omaralabed/Radxa-CM5-PCB/fabrication/footprint-coupon-a1/output/renders/Footprint-Coupon-bottom.png

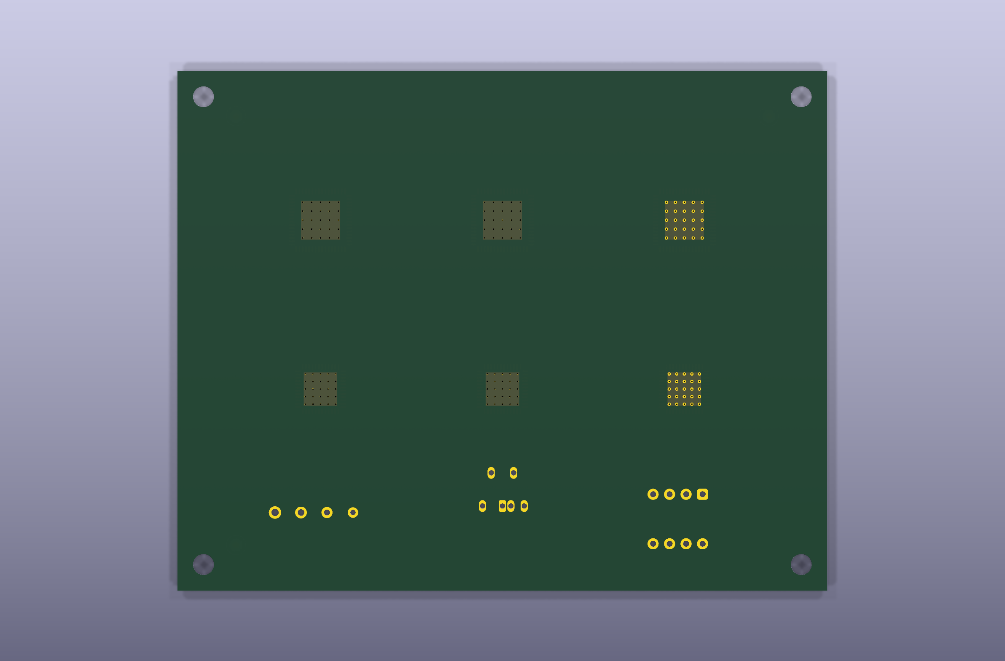
fabrication/footprint-coupon-a1/output/renders/Footprint-Coupon-bottom.png
