omaralabed/Radxa-CM5-PCB/references/radxa-cm-projects/cm5/README.md

<!-- AGENT_SPEC_START -->
Spec source: ../tools/out/cm5.md

### Agent Spec Summary
- Board: Radxa CM5 (cm5)
- SoC: RK3588S
- Category: cm
- Form factor: raspberrypi_cm4_compatible
- Interfaces total: 0
- Interface breakdown: none
- Capability tags: cm4_compatible, edge_ai
- Power inputs: unknown unknown via unknown
- Data path: hardware-db/boards/cm5
<!-- AGENT_SPEC_END -->

## Apply for Radxa CM5

Radxa is donating some free [Radxa CM5](hhttps://rock.sh/cm5) to open source hardware projects.

## How to apply

Send a new PR to this repository on GitHub, append your application table(sort Project Name). Radxa team will review/ask questions/discuss about the project detail. If the project is interesting or welcomed by the community, we will approve it. Radxa Team will contact the developer for the further sample shipping&development etc.

## CM5 projects list:

| Project Name | CM5 Model | Hardware(Carrier Board) | Software | Notes |
|---|---|---|---|---|
| Argo | Radxa CM5 Max (16GB RAM, 128GB eMMC) | Custom Raspberry Pi–focused Carrier PCB | Ubuntu/Android | For testing with custom Raspi-focused Carrier PCB |
| piBrick PocketRX5 | Radxa CM5 Max (16GB RAM, 128GB eMMC) | Handheld pocket computer | Ubuntu/Android | For designing new board supporting Radxa CM5 |
