omaralabed/Radxa-CM5-PCB/cad/kicad/FOOTPRINT_RELEASE.md

# Footprint Release Control

This project does not permit final production routing from schematic symbols
that lack a resolved, drawing-backed footprint. Engineering board outlines,
mechanical placement, component floorplanning, and routing outside a named
local coupon region may proceed from the controlled nominal geometry. Run:

```sh
python3 cad/kicad/audit_footprint_readiness.py --routing
```

The command must pass before final route freeze. The stricter `--release` gate
also requires a manufacturer and MPN for every board-mounted component.

## Locked connector evidence

| Function | Manufacturer / part | Footprint | Evidence | State |
|---|---|---|---|---|
| Wi-Fi Mini PCIe socket | Molex 0679101002 / 67910-1002 | `CM5Carrier:Molex_0679101002_Mini_PCIe` | Molex production drawing SD-67910-001 revision C2 | Land pattern locked; first-article and 3D fit open |
| Balanced output XLR, CH1-CH8 | Neutrik NC3MAV | `Connector_Audio:Jack_XLR_Neutrik_NC3MAV_Vertical` | Neutrik NC3MAV product drawing and KiCad source footprint | Pad/hole signature and Rev L face-center placement locked; overhanging outline is assembly data on `F.Fab` |
| Balanced input XLR, CH1-CH8 | Neutrik NC3FAV | `Connector_Audio:Jack_XLR_Neutrik_NC3FAV_Vertical` | Neutrik NC3FAV product drawing and KiCad source footprint | Pad/hole signature and Rev L face-center placement locked |
| Radxa CM5 board-to-board mates | 3x Hirose DF40C-100DS-0.4V(51) | Three `CM5Carrier:Radxa_CM5_*_DF40C_100DS_OFFICIAL` footprints | Pad, drill, module-mount, and relative-transform geometry extracted from Radxa IO V2.20 official PADS source; pin identity from V2.21 workbook; Hirose EDC3-311352-00 drawing | Source geometry locked. J24's child pad angle is restored to the native PADS decal angle after a documented KiCad importer double-rotation; coordinates and sizes are unchanged. Installed stack-height inspection remains open |
| Ethernet MagJacks | Wurth 74991114412 | `CM5Carrier:T_Wurth_WE-RJ45LAN_74991114412` | Wurth manufacturer footprint and STEP | Pad/hole signature and Rev L opening-center placement locked; immutable 0.2312 mm NPTH-to-copper minimum requires the documented PCBWay process rule |
| Cellular M.2 B-key socket | TE 2199230-3 | `CM5Carrier:TE_2199230-3_M2_Key_B_4.2mm` | TE customer drawing C-2199230 revision B4 | Locked; modem/heatsink envelope open |
| Dual nano-SIM holders | Wurth 693043020611 | `CM5Carrier:J_Wurth_WR-CRD_693043020611` | Wurth manufacturer drawing | Pad/hole signature and Rev L service-center placement locked |
| Program-audio TDM headers | Molex 87832-6423, two devices | `Connector_Molex_Milligrid:Molex_8783230xx_2x15_P2.0mm_Header_Vertical_Polarized_MountingPegs` | Molex 87832 production drawing; 30 circuits, pegs, polarization and 30 microinch gold | Locked; harness SI and vibration qualification open |
| CTIA headset jack | Kycon STX-353K7A-6N-KTTR | `CM5Carrier:Kycon_STX-353K7A-6N-KTTR_PRELIMINARY` | Kycon component drawing defines terminal centers but no recommended PCB land | Coupon A1 artwork ready; production blocked pending physical sample and plated-hole result |

## Program-audio package evidence

| Function | Manufacturer / part | Footprint | Evidence | State |
|---|---|---|---|---|
| Eight-channel ADC | AKM `AK5558VN` | `Package_DFN_QFN:QFN-64-1EP_9x9mm_P0.5mm_EP6x6mm_ThermalVias` | AKM package drawing and KiCad exposed-pad starting land | Coupon A1 artwork ready; routing blocked pending physical X-ray and assembly pass |
| Eight-channel DAC | AKM `AK4458VN` | `Package_DFN_QFN:QFN-48-1EP_7x7mm_P0.5mm_EP5.15x5.15mm_ThermalVias` | AKM package drawing and KiCad exposed-pad starting land | Coupon A1 artwork ready; routing blocked pending physical X-ray and assembly pass |
| Output fail-silent relays, K501-K508 | Panasonic Industry `TQ2-12V` | `CM5Carrier:Panasonic_TQ2-12V_PRELIMINARY` | Panasonic TQ relay package drawing | Coupon A1 artwork ready; routing blocked pending insertion, seating, and pin-map pass |
| Balanced input receivers | THAT Corporation `THAT1206S08-U` | `Package_SO:SOIC-8_3.9x4.9mm_P1.27mm` | THAT package drawing and standard SOIC land | Locked |
| Audio op amps | TI `OPA1652AIDR` | `Package_SO:SOIC-8_3.9x4.9mm_P1.27mm` | TI D package drawing and standard SOIC land | Locked |
| Balanced output drivers | THAT Corporation `THAT1646S08-U` | `Package_SO:SOIC-8_3.9x4.9mm_P1.27mm` | THAT package drawing and standard SOIC land | Locked |

## Molex 0679101002 datum contract

The project-owned Mini PCIe footprint is regenerated by `generate_interface_schematics.py`. Its origin is Molex datum E, the center of the 1.60 mm locator hole.

- 52 SMD contacts, each 0.60 x 2.00 mm.
- Contact pitch 0.80 mm.
- Even and odd rows staggered 0.40 mm.
- Contact-row centers at `Y = -4.10 mm` and `Y = +4.10 mm`.
- 1.60 mm datum-E locator at `(0, 0)`.
- 1.10 mm second locator at `(25.00, 0)`.
- Pin groups 1-16 span 5.60 mm; pin groups 17-52 span 13.60 mm.
- Mechanical solder tabs are included as unnumbered pads.

The current official drawing is:

`https://www.molex.com/content/dam/molex/molex-dot-com/products/automated/en-us/salesdrawingpdf/679/67910/679100002_sd.pdf`

As of 2026-08-16, Molex 0679101002 is listed active and stocked by major authorized distributors. Availability is procurement evidence only and must be refreshed before the production purchase order.

## Audio connector release contract

The TDM cable uses Molex `51110-3051` polarized 30-circuit housings and
`50394-8052` crimp terminals. The exact pin and wire-class assignment is in
`docs/audio_tdm_harness_a1.csv`. Final harness length, pair construction,
strain relief, and eye-margin qualification remain open mechanical/electrical
release gates.

The Kycon headset footprint is intentionally marked `PRELIMINARY`. Its six
pad centers are generated and checked by `validate_audio_control.py`, but the
production audit must remain `BLOCKED_MECHANICAL_COUPON` until a physical
sample and plated-hole coupon confirm terminal diameters, insertion fit, bezel,
and switch polarity.

## Footprint Coupon A1

The controlled coupon project is in `FOOTPRINT-COUPON`. Its generated release
archive and factory instructions are in
`../../fabrication/footprint-coupon-a1`. The coupon compares open, bottom-tented,
and selective IPC-4761 Type VII thermal vias for both AKM packages and includes
physical fit sites for the Panasonic relay and Kycon jack.

`FOOTPRINT-COUPON/review_coupon.sh` currently passes with zero KiCad DRC
violations. This closes CAD preparation only. It does not clear any routing or
production gate until the signed physical result sheet, X-ray evidence, via
microsection, and part-fit records pass the criteria in
`../../docs/qualification/footprint-coupon-a1.md`.

## Locked power-package evidence

| Function | Manufacturer / part | Footprint | Evidence | State |
|---|---|---|---|---|
| 4.006 V CM5 buck MOSFET, high side | onsemi `NVMFS6B25NLT1G` | `CM5Carrier:onsemi_DFN5_5x6_488AA_GSD` | onsemi case 488AA recommended soldering footprint | Drawing-derived G/S/D remap locked; first-article stencil and thermal review open |
| 4.006 V CM5 buck MOSFET, low side | onsemi `FDWS86068-F085` | `CM5Carrier:onsemi_DFNW8_5p2x6p3_507AU_GSD` | onsemi case 507AU recommended land pattern | Drawing-derived G/S/D remap locked; first-article stencil and thermal review open |
| 12 V buck-boost MOSFETs | TI `CSD18532Q5B`, `CSD17573Q5B` | `CM5Carrier:TI_DNK0008A_GSD` | TI DNK0008A / VSON-CLIP package land pattern | Repeated source/drain terminals remapped to the three-pin symbol and machine checked |
| Radio/network buck regulators | TI `LM61460RJR`, `LM61440RJR` | `CM5Carrier:TI_RJR0014A` | TI drawing 4223976/H, RJR0014A example board layout | All 14 pads, including four L-shaped lands, are drawing-derived and machine checked |
| Wi-Fi load switch | TI `TPS22990DMLR` | `CM5Carrier:TI_DML0010A` | TI drawing 4222524/A | Exposed VIN land and all ten terminals machine checked |
| 4.006 V CM5 buck inductor | TDK `SPM10065VC-3R3M-D` | `CM5Carrier:TDK_SPM10065VC` | TDK recommended land dimensions | Locked |
| 12 V buck-boost inductor | Wurth `74439370047` | `CM5Carrier:Wurth_74439370047` | Wurth manufacturer drawing | Locked |
| 12 V current shunts | Susumu `KRL6432E-M-R006-F-T1`, `KRL11050-C-R004-F-T1` | project KRL6432E/KRL11050 lands | Susumu KRL recommended land tables | Locked |

`CM5-CARRIER/validate_power_regulators.py` checks the critical pad sets and
dimensions above and checks every row in `docs/power_regulator_bom_a1.csv`.
The BOM is regenerated from the KiCad netlist by `export_schematic_bom.py`.

## Open gate

Power-Regulators-A1 has zero routing or production-part blockers. Across the
three physical board roots, the controlled audit currently reports 1203
unique components, ten local final-routing blockers, and 11 production blockers.
Engineering placement and routing outside those local coupon regions may
proceed; production route freeze remains held until the routing count is zero. See
`reports/component-footprint-audit.md` and
`reports/component-footprint-audit.csv`. Assigning a plausible package without
a locked part drawing is not accepted as closure.
