omaralabed/Radxa-CM5-PCB/outputs/schematic-release-a1/CM5-Carrier-Schematic-A1.pdf

1 | 2 | 3 | 4 | 5 | 6 | 7 | 8 | 9 | 10 | 11
1 | 2 | 3 | 4 | 5 | 6 | 7 | 8 | 9 | 10 | 11

AB

C

D

E

## FGH

AB

C

D

E

# FGH Date: 2026-08-14

# KiCad E.D.A. 10.0.5-rc1

Size: A2 | Rev: A1 Id: 1/1

# Title: Radxa CM5 ProComm Carrier - Interface Contract

# File: CM5-Carrier.kicad_sch

# Sheet: /

# ProComm

# Interface overview; detailed A1 capture is maintained in the named standalone sheets

# Fan 1 intake, fan 2 exhaust; independent PWM/tach channels

# Program audio crosses a buffered differential TDM link

# NOT A FABRICATION RELEASE

1 | 2
3 | 4 J401 CPU_FAN
1 | 2
3 | 4
5 | 6
7 | 8
9 | 10
11 | 12
13 | 14
15 | 16
17 | 18
19 | 20
21 | 22
23 | 24
25 | 26
27 | 28
29 | 30
| J201

## AUDIO_TDM_CONTROL

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
## J102 PWR_STATUS_FROM_SELECTOR

1 | 2
3 | 4 J101 RAW_POWER_FROM_PWR_SELECT
1 | 2
3 | 4

## J402 MODEM_FAN

1 | 2
3 | 4
J404

## THA0412AD-TZW3_EXHAUST

1
2
3
4
5
6

## J103 PWR_TELEMETRY_FROM_SELECTOR

1 | 2
3 | 4 J403

## THA0412AD-TZW3_INTAKE

1 | 2
3 | 4 J202

## AUDIO_12V_POWER

## AUD_ADC_RST_N

## AUD_DAC_MUTE_N

## INTAKE_FAN_TACH

GND | MODEM_FAN_12V MODEM_FAN_PWM
CPU_FAN_12V | GND | INTAKE_FAN_12V
| | INTAKE_FAN_PWM

## GND

CPU_FAN_PWM | MODEM_FAN_TACH

## GND

AUDIO_12V | AUDIO_12V

## EXHAUST_FAN_PWM

## GND

## CTRL_I2C_SDA GND

## CTRL_I2C_SCL PWR_MON_ALERT_N

## LOGIC_3V3 GND

## AUD_MCLK_N

## GND

## AUD_BCLK_N

## AUD_FSYNC_N

## GND

## CH_24V_N

## CH_BAT_N

## VALID_24V_N

## GND

## GND

RAW_OUT_LOAD | RAW_OUT_LOAD

## GND

## EXHAUST_FAN_TACH

## VALID_BAT_N

## BAT_LOW_N

## VALID_DTAP_N

## VALID_GOLD_N

## TDM_SPARE_1

## LOGIC_3V3

## AUDIO_PRESENT_N

## EXHAUST_FAN_12V

## AUD_MCLK_P

## GND

## AUD_BCLK_P

## AUD_FSYNC_P

## GND

## GND

## GND

## AUD_DAC_SDIN_N

## AUD_ADC_SDOUT_N

## GND

## GND

## TDM_SPARE_2

## GND

## AUD_DAC_SDIN_P

## AUD_ADC_SDOUT_P

## GND

AUD_I2C_SCL | AUD_I2C_SDA
| AUD_DAC_RST_N
| AUD_IRQ_N
| AUDIO_ENABLE

## CPU_FAN_TACH

THA0412AD-TZW3_EXHAUST

08 Thermal-IO: I2C translation, GPIO expansion, sensors and four fan channels

Carrier drives MCLK/BCLK/FSYNC/DAC data; AUDIO-8X8 drives ADC data back. Mates with AUDIO-8X8 J101 using Molex 87832-6423 headers; harness assembly remains vibration-qualified. B. BUFFERED DIFFERENTIAL TDM + AUDIO CONTROL

Mates with PWR-SELECT J401; add 3.3 V pull-ups on the carrier. Mates with PWR-SELECT J301; two contacts per polarity; validate 15 A derating. A. PWR-SELECT INTERFACE

Mates with PWR-SELECT J402; carrier supplies 3.3 V and owns I2C pull-ups.

J403 is physically keyed/labeled INTAKE; J404 is keyed/labeled EXHAUST. MODEM_FAN C. FOUR INDEPENDENT PWM / TACH FANS

CPU_FAN | THA0412AD-TZW3_INTAKE

09 Power-Regulators-A1: protected raw hold-up, all main rails, sequencing and test points 10 Audio-8x8: all XLR shields bonded to chassis with one controlled AGND bond 11 Review: every detailed sheet has zero ERC errors; warnings are classified DC/DC compensation and magnetics remain a separate power-design calculation milestone. High-speed routing starts only after stackup and connector Z datums are released. The two enclosure fans require an underside baffle to prevent direct intake/exhaust short flow.

# D. DETAILED CAPTURE SUITE - REV A1

01 CM5-Core-Allocated: exact 300-contact CM5 symbol, 76 locked functions 02 CM5-Core-Allocated: VCC_SYSIN, reset, recovery, power-on and debug UART 04 Network-PCIe: 4x Wurth MagJack and Molex 0679101002 Mini PCIe 4T4R Wi-Fi 03 Network-PCIe: PI7C9X2G608GP, 3x LAN7430 and native WAN1 front end 05 WWAN-SIM: TE 2199230-3 B-key, USB3/USB2, controls and dual-SIM mux 06 Display-Harness: HDMI, USB touch and dedicated 12 V / 2.5 A branch 07 Audio-Control: I2S0 TDM, I2S1 ES8316 headset and CTIA amplifier path

Separate filtered audio-power harness; no fan/radio loads.

1 | 2 | 3 | 4 | 5 | 6 | 7 | 8 | 9 | 10 | 11
1 | 2 | 3 | 4 | 5 | 6 | 7 | 8 | 9 | 10 | 11

AB

C

D

E

## FGH

AB

C

D

E

# FGH Date: 2026-08-13

Size: A2 | Rev: A1

# Title: Radxa CM5 ProComm Carrier - Exact CM5 Connector Allocation

# File: CM5-Core-Allocated.kicad_sch

# Three 100-contact Hirose DF40C mates; all physical pin numbers follow CM5 V2.21

Exactly 76 product allocations are connected; unused functions are intentionally no-connect

# All connector grounds join the carrier ground plane; allocated GPIO domain is 3.3 V

# DETAILED CAPTURE BASELINE - verify CM5 voltage limits before release

GND 1 | GND | 2 PHY1_MDI3+ 3 | PHY1_MDI1+ | 4 PHY1_MDI3- 5 | PHY1_MDI1- | 6 GND 7 | GND | 8 PHY1_MDI2- 9 | PHY1_MDI0- | 10 PHY1_MDI2+ 11 | PHY1_MDI0+ | 12 GND 13 | GND | 14 PHY1_LED2_Y 15 | NC | 16 PHY1_LED1_G 17 | NC | 18 PHY1_LED0_Y1 19 | HP_INT | 20 PWM15_M1 21 | GND | 22 GND 23 | PCIE20X1_2_WAKEN_M0 | 24
I2C4_SDA_M3_WIFI 25 | NC | 26 WIFI_REG_ON_E 27 | SPIO_MOSI_M1 | 28 GSENSOR_INT 29 | SPIO_CLK_M1 | 30
SPIO_CS0M1 31 | GND | 32 GND 33 | I2S0_SDO0 | 34
I2C8_SCL_M2_CAM 35 | I2C8_SDA_M2_CAM | 36
TP_INT_L 37 | MIPI_CAM2_RST_L | 38
TP_RST_L 39 | GPIO1_B1 | 40
LCD_RESET_L 41 | GND | 42 GND 43 | GPIO1_B2_CAM1 | 44 GPIO1_A6_CAM1 45 | I2S0_SCLK_TX | 46 MIPI_CAM2_PDN_L 47 | I2S0_LRCK_TX | 48
I2C4_SCL_M3_WIFI 49 | I2S0_MCLK | 50 UART2_RX_M0 51 | GND | 52 GND 53 | I2S0_SDI0 | 54 UART2_TX_M0 55 | GPIO0_C7 | 56
SDMMC_CLK 57 | GPIO0_D0 | 58 GND 59 | GND | 60
SDMMC_D3 61 | SDMMC_CMD | 62
SDMMC_D0 63 | NC | 64 GND 65 | GND | 66
SDMMC_D1 67 | NC | 68
SDMMC_D2 69 | NC | 70 GND 71 | NC | 72
VCCIO_FLASH 73 | GND | 74
SD_PWR_ON 75 | NC | 76
VCC_SYSIN 77 | GPIO_VREF | 78
VCC_SYSIN 79 | I2C7_SCL_M2 | 80
VCC_SYSIN 81 | I2C7_SDA_M2 | 82
VCC_SYSIN 83 | VCC_3V3_S3 | 84
VCC_SYSIN 85 | VCC_3V3_S3 | 86
VCC_SYSIN 87 | VCC_1V8_S0 | 88 PWM4_M0 89 | VCC_1V8_S0 | 90 HOST_WAKE_BT_H 91 | RESET_L | 92
SARADC_VIN0_BOOT 93 | NC | 94 WIFI_LED 95 | SARADC_VIN4 | 96 USB_HOST_PWREN_H 97 | GND | 98 PWRON_L 99 | SPIO_MISO_M1 100 J501 RADXA CM5 U13-A MATE | 1

2
3
4
5

J512

INTERNAL_USB_RECOVERY | 1 | 2
3 | 4
5 | 6
7 | 8 J513 CM5_POWER_ENTRY

GND

1 | GND

2

TYPEC0_SBU1

3 | GPIO3_C0

4

TYPEC0_SBU2

5 | GPIO3_B7

6 GND

7
| TYPEC0_SBU1_DC

8

TYPEC0_SSRX1P

9 | GPIO1_B6_CAM2_CLK

10

TYPEC0_SSRX1N

11 | GPIO1_B7

12 GND

13
| TYPEC0_SBU2_DC

14

TYPEC0_SSTX1P

15 | NC

16

TYPEC0_SSTX1N

17 | PWM11_M3

18 GND

19 | GPIO1_C1

20

TYPEC0_SSRX2P

21 | GND

22

TYPEC0_SSRX2N

23 | WIFI_PWR_EN

24 GND

25

SARADC_VIN1_KEY/RECOVERY 26

TYPEC0_SSTX2P

27
SARADC_VIN2_DC

28

TYPEC0_SSTX2N

29
SARADC_VIN3_HP_HOOK

30 GND

31 | GND

32 NC

33
| LCD_PWREN_H

34 NC

35 | HP_DET_L | 36 GND
37 | GPIO4_A4

38 PCIE20_2_REFCLKP

39 | GPIO4_A5

40 PCIE20_2_REFCLKN

41 | GND

42 GND

43 | GPIO1_D0

44 USB20_HOST1_DP

45 | GPIO1_D1

46 USB20_HOST1_DM

47 | GND

48 GND

49 | NC
50 USB30_2_SSTXP
51 | NC

52 USB30_2_SSTXN

53 | NC

54 GND

55 | GND

56 USB30_2_SSRXP

57 | NC

58 USB30_2_SSRXN

59 | NC

60 GND

61 | GND

62 USB20_HOST0_DP

63 | NC

64 USB20_HOST0_DM

65 | NC

66 GND

67 | GND

68

I2C6_SDA_M3

69 | NC

70

I2C6_SCL_M3

71 | GND

72 GND

73

SDMMC_DET_L | 74 GPIO1_C6_S
75 | GND

76 GPIO1_D5_S

77 | NC

78 GPIO1_C4_S

79 | NC
80 RTC_INT_L 81 | NC

82 GPIO1_D2

83 | NC
84 BT_HOST_WAKE 85 | NC

86 GPIO4_A7

87 | NC

88 GPIO4_A6

89 | NC

90 NC

91
| VCC_3V3_S3

92 GPIO0_C2

93 | GPIO0_D3

94

TYPEC5V_PWREN_H

95 | CC_INT0_L | 96
TYPEC0_OTG_VBUSDET 97 | BT_REG_ON_H

98 GND

99 | GND

## 100 J503 RADXA CM5 J1 MATE

TYPEC0_USB20_OTG_ID 101 | PCIE20X1_2_CLKREQN_M0 102
TYPEC0_OTG_DM 103 | NC 104
TYPEC0_OTG_DP 105 | 5V_HDMI 106 GND 107 | GND 108 PCIE20X1_2_PERSTN_M0 109 | PCIE20_0_REFCLKP 110 NC 111 | PCIE20_0_REFCLKN 112 GND 113 | GND 114 MIPI_DPHY0_RX_D0N 115 | PCIE20_0_RXP 116 MIPI_DPHY0_RX_D0P 117 | PCIE20_0_RXN 118 GND 119 | GND 120 MIPI_DPHY0_RX_D1N 121 | PCIE20_0_TXP 122 MIPI_DPHY0_RX_D1P 123 | PCIE20_0_TXN 124 GND 125 | GND 126 MIPI_DPHY0_RX_CLKN 127 | MIPI_CSI0_RX_D0N 128 MIPI_DPHY0_RX_CLKP 129 | MIPI_CSI0_RX_D0P 130 GND 131 | GND 132 MIPI_DPHY0_RX_D2N 133 | MIPI_CSI0_RX_D1N 134 MIPI_DPHY0_RX_D2P 135 | MIPI_CSI0_RX_D1P 136 GND 137 | GND 138 MIPI_DPHY0_RX_D3N 139 | MIPI_CSI0_RX_CLK0N 140 MIPI_DPHY0_RX_D3P 141 | MIPI_CSI0_RX_CLK0P 142 NC 143 | GND 144 HDMI0_TX_SBDP 145 | NC 146 HDMI0_TX_SBDN 147 | NC 148 NC 149 | GND 150 HDMI_TX0_CEC_PORT 151 | NC 152 HDMI_TX0_HPD 153 | NC 154 GND 155 | GND 156 MIPI_DPHY0_TX_D0N 157 | NC 158 MIPI_DPHY0_TX_D0P 159 | NC 160 GND 161 | GND 162 MIPI_DPHY0_TX_D1N 163 | NC 164 MIPI_DPHY0_TX_D1P 165 | NC 166 GND 167 | GND 168 MIPI_DPHY0_TX_CLKN 169 | HDMI0_TX2P 170 MIPI_DPHY0_TX_CLKP 171 | HDMI0_TX2N 172 GND 173 | GND 174 MIPI_DPHY1_TX_D0N 175 | HDMI0_TX1P 176 MIPI_DPHY1_TX_D0P 177 | HDMI0_TX1N 178 GND 179 | GND 180 MIPI_DPHY1_TX_D1N 181 | HDMI0_TX0P 182 MIPI_DPHY1_TX_D1P 183 | HDMI0_TX0N 184 GND 185 | GND 186 MIPI_DPHY1_TX_CLKN 187 | HDMI0_TX3P 188 MIPI_DPHY1_TX_CLKP 189 | HDMI0_TX3N 190 GND 191 | GND 192 MIPI_DPHY1_TX_D2N 193 | MIPI_DPHY1_TX_D3N 194 MIPI_DPHY1_TX_D2P 195 | MIPI_DPHY1_TX_D3P 196 GND 197 | GND 198 HDMI_TX0_SDA_5V 199 | HDMI_TX0_SCL_5V 200 J502 RADXA CM5 U13-B MATE 1

2
3
4
5
6
J510 CM5_POWER_SERVICE | 1

2
3
4

## J511 DEBUG_UART_3V3

GND

IO_5V0

GND

# GND WAN1_LED2 WAN1_LED1 WAN1_LED0 HS_SDOUT_TO_CODEC

GND | PCIE_UP_TX_N_CM5 | WWAN_USB3_TX_P

GND

GND

TOUCH_USB_DM

GND

GND

GND

GND

GND

GND

GND HS_SDIN_FROM_CODEC HS_JACK_DET_N

TOUCH_USB_DP

GND DBG_UART_RX

GND

GND

GND

GND

GND

GND CM5_RECOVERY_KEY HS_I2C_SCL WAN1_MDI2_N

AUD_BCLK

AUD_FSYNC

AUD_MCLK

GND

GND

GND

GND

LOGIC_3V3

GND HS_MCLK

HS_I2C_SDA GND | GND

## REC_USB_VBUS_DET

HDMI_DDC_SCL HDMI_CLK_N

HDMI_CLK_P HDMI_D0_N

HDMI_D0_P HDMI_D1_N

WAN1_MDI1_N WAN1_MDI0_N WAN1_MDI0_P

GND

AUD_IRQ_N

GND PCIE_UP_WAKE_N

HS_BCLK HS_LRCK

GND

REC_USB_ID

REC_USB_DM

REC_USB_DP

GND PCIE_UP_PERST_N

HDMI_HEAC_P HDMI_HEAC_N

HDMI_CEC HDMI_HPD | HDMI_D1_P

GND

GND

GND

GND

GND

GND

GND

## GND

## REC_USB_ID

## REC_USB_DP

## REC_USB_DM

GND

GND | PCIE_UP_CLKREQ_N

## SYS_4V0

## SYS_4V0

GND REC_USB_VBUS_DET GND

GND

WAN1_MDI1_P

DBG_UART_RX | GND | GND

## LOGIC_3V3 GND

DBG_UART_TX | GND

GND

GND

GND

GND

GND HDMI_DDC_SDA

GND

AUD_DAC_SDIN

AUD_ADC_SDOUT SYS_I2C7_SCL SYS_I2C7_SDA CM5_RESET_N LOGIC_3V3 CM5_RESET_N

## CM5_BOOT CM5_PWRON_N

## CM5_RECOVERY_KEY

WAN1_MDI3_N

GND DBG_UART_TX

GND

GND

## GND

## SYS_4V0

## SYS_4V0

GND

GND SYS_4V0

SYS_4V0

SYS_4V0

SYS_4V0 | WWAN_USB3_RX_N WWAN_USB3_RX_P

GND SYS_4V0

SYS_4V0 CM5_BOOT | WWAN_USB3_TX_N
GND CM5_PWRON_N | WWAN_USB2_DM

WWAN_USB2_DP HDMI_D2_N

HDMI_D2_P

## GND

GND

GND

GND

GND

GND PCIE_UP_RX_N_CM5 PCIE_UP_RX_P_CM5

GND

GND

GND

GND

GND

WAN1_MDI3_P

GND

GND

GND

GND | PCIE_UP_TX_P_CM5

GND

GND

GND

GND WAN1_MDI2_P | PCIE_UP_REFCLK_N

PCIE_UP_REFCLK_P

GND

GND

Internal keyed recovery harness; service fixture owns the protected USB-C receptacle and CC network.

J1: 100 physical contacts 3.3 V UART only; keyed factory/debug cable. | Kelvin-sense SYS_4V0 at J501; 4.0 V follows the Radxa CM5 carrier design note.

# U13-A: 100 physical contacts 2. INTERNAL POWER / STARTUP / RECOVERY SERVICE

## Internal keyed service header; never exposed on the top panel. 3. OWNERSHIP AUDIT

76 / 76 allocated contacts connected; 0 duplicate physical-pin claims. WAN1 uses native MDI. PCIe Gen2 x1 feeds the packet switch. WWAN owns USB30_2 + USB20_HOST0; touch owns USB20_HOST1. HDMI_TX0, I2S0 TDM, I2S1 headset, I2C7, I2C3 and UART2 are reserved exactly once. Pins 145/147 remain HDMI HEAC reserved. U13-B pin 106 receives the dedicated IO_5V0 rail. Unused alternate-function contacts carry explicit no-connect markers on this A1 baseline.

# 1. EXACT RADXA CM5 MATING CONNECTORS

U13-B: 100 physical contacts

1 | 2 | 3 | 4 | 5 | 6 | 7 | 8 | 9 | 10 | 11 | 12 | 13 | 14 | 15 | 16
1 | 2 | 3 | 4 | 5 | 6 | 7 | 8 | 9 | 10 | 11 | 12 | 13 | 14 | 15 | 16

AB

C

D

E

## FGH

## IJK

AB

C

D

E

## FGH

# IJK Date: 2026-08-14

Size: A1 | Rev: A1

# Title: Radxa CM5 ProComm Carrier - PCIe / Ethernet / Wi-Fi

# File: Network-PCIe.kicad_sch

# PI7C9X2G608GP in 606 mode: x1 upstream plus five x1 downstream ports

# Native WAN1 plus three LAN7430 endpoints use exact Wurth 74991114412 MagJacks

# Exact package balls/pins from Diodes DS40210 Rev 8 and Microchip DS00002631G

# Port 5 is disabled and unrouted; generic cable headers are prohibited on PCIe Gen2 lanes

D1+
1 D1-
2 | GND

3 D2+
4 D2-

5NC

6NC
7 NC

9NC
10 | U634
TPD4E05U06DQA | D1+

1 D1-

2 | GND

3 D2+
4 D2-

5NC

6NC
7 NC

9NC
10 | U636
TPD4E05U06DQA | 330R R656 | 330R R657 L6131 3.3uH / 2.37A min | 200R R61311%

AVDDH_1

1

TXRXP_A 2

TXRXM_A 3

AVDDL_1 | 4

TXRXP_B

5
TXRXM_B

6

TXRXP_C

7
TXRXM_C

8

AVDDL_2

9
TXRXP_D

10

TXRXM_D

11
AVDDH_2

12

VDD12CORE 13
VP

14 GD_1

15 | PCIE_RX_P

16 PCIE_RX_M

17 | GD_2

18 PCIE_TX_P

19
| VPTX

20 PCIE_TX_M

21 | GD_3

22

VPH

23 | RESREF | 24 PCIE_CLK_P
25 | PCIE_CLK_M

26

VDD25_REG_OUT 27
| VDD_REG_IN

28 RESET_N

29

TEST 30

VDD12CORE 31

VDD12_SW_OUT 32

VDD_SW_IN

33
VDD12_SW_FB

34

VAUX_DET/GPIO3/LED3/TCK

35

EECLK/GPIO2/LED2/TMS/ADV_PM_DISABLE 36

EEDIO/GPIO1/LED1/TDO

37

EECS/GPIO0/LED0/TDI 38

VDDVARIO

39

VDD12CORE 40

VDD_OTP

41 | CLKREQ#

42 WAKE#

43 | PERST#

44

AVDD12

45
XO

46

XI 47

ISET 48

VSS_EP

49 U613

# LAN7430 C6125

# 15pF C0G

D1+
1 D1-
2 | GND

3 D2+
4 D2-

5NC

6NC
7 NC

9NC
10 | U635
TPD4E05U06DQA 330R R654 | 330R R655 GND
1 | D1+
2 | D1-
3 | D2+
4 | D2-
5 | D3+
6 | D3-
7 | D4+
8 | D4-
9
| SHIELD1

S1

# SHIELD2

S2

# LED1_Y-/G+

11

# LED1_Y+/G-

12

# LED2_Y-/G+

13

# LED2_Y+/G-

14

J612

74991114412

C6122

# 100nF C6121

# 10uF 25V X5R

C6124

## 15pF C0G ⁶.04k R61221%

XI 1 GND
2 XO

3

4 Y612

# 25MHz / 10pF / -40..85C

C6123

# 1uF 35V X5R / ESR <1R

AVDDH_1

1

TXRXP_A 2

TXRXM_A 3

AVDDL_1 | 4

TXRXP_B

5
TXRXM_B

6

TXRXP_C

7
TXRXM_C

8

AVDDL_2

9
TXRXP_D

10

TXRXM_D

11
AVDDH_2

12

VDD12CORE 13
VP

14 GD_1

15 | PCIE_RX_P

16 PCIE_RX_M

17 | GD_2

18 PCIE_TX_P

19
| VPTX

20 PCIE_TX_M

21 | GD_3

22

VPH

23 | RESREF | 24 PCIE_CLK_P
25 | PCIE_CLK_M

26

VDD25_REG_OUT 27
| VDD_REG_IN

28 RESET_N

29

TEST 30

VDD12CORE 31

VDD12_SW_OUT 32

VDD_SW_IN

33
VDD12_SW_FB

34

VAUX_DET/GPIO3/LED3/TCK

35

EECLK/GPIO2/LED2/TMS/ADV_PM_DISABLE 36

EEDIO/GPIO1/LED1/TDO

37

EECS/GPIO0/LED0/TDI 38

VDDVARIO

39

VDD12CORE 40

VDD_OTP

41 | CLKREQ#

42 WAKE#

43 | PERST#

44

AVDD12

45
XO

46

XI 47

ISET 48

VSS_EP

49 U612
LAN7430 | C6131
10uF 25V X5R | 6.04k R61321%

C6132

100nF

XI 1 GND
2 XO

3

4 Y613

# 25MHz / 10pF / -40..85C

C6133

# 1uF 35V X5R / ESR <1R

# PWR_FLAG

C6135

# 15pF C0G

D1+
1 D1-
2 | GND

3 D2+
4 D2-

5NC

6NC
7 NC

9NC
10 | U637

# TPD4E05U06DQA GND

1 | D1+
2 | D1-
3 | D2+
4 | D2-
5 | D3+
6 | D3-
7 | D4+
8 | D4-
9
| SHIELD1

S1

# SHIELD2

S2

# LED1_Y-/G+

11

# LED1_Y+/G-

12

# LED2_Y-/G+

13

# LED2_Y+/G-

14

J613

74991114412

# PWR_FLAG

C6134

# 15pF C0G

# PWR_FLAG

D1+
1 D1-
2 | GND

3 D2+
4 D2-

5NC

6NC
7 NC

9NC
10 | U633

# TPD4E05U06DQA C6114

# 15pF C0G

PWR_FLAG ³³⁰R R652 | 330R R653 GND 1 | D1+ 2 | D1- 3 | D2+ 4 | D2- 5 | D3+ 6 | D3- 7 | D4+ 8 | D4- 9

# SHIELD1 S1 SHIELD2 S2

# LED1_Y-/G+

11

# LED1_Y+/G-

12

# LED2_Y-/G+

13

# LED2_Y+/G-

14

J611

74991114412

C6112

100nF | C6113
1uF 35V X5R / ESR <1R 200R R61111% | 6.04k R61121%

C6111

# 10uF 25V X5R

D1+
1 D1-
2 | GND | 3 | D2+ 4 D2-
| | | 5NC

6NC
7 NC

9NC
10 | U632
TPD4E05U06DQA | 10k R620 PWR_FLAG
GND 1 | D1+ 2 | D1- 3 | D2+ 4 | D2- 5 | D3+ 6 | D3- 7 | D4+ 8 | D4- 9

# SHIELD1 S1 SHIELD2 S2

LED1_Y-/G+ | 11
LED1_Y+/G- | 12
LED2_Y-/G+ | 13
LED2_Y+/G- | 14

J610

74991114412 330R R651

CLKREQ_L[5] A1 | CLKREQ_L[4] | A2 PERP[7] A3 | PETP[7] | A4 PERP[6] A5 | PETP[6] | A6 REFCLKN[1] A7 | PETP[5] | A9 PERP[5] A10 | PETP[4] A11 PERP[4] A12 | CLKREQ_L[6] | B2 PERN[7] B3 | PETN[7] | B4 PERN[6] B5 | PETN[6] | B6 REFCLKP[1] B7 | PETN[5] | B9 PERN[5] B10 | PETN[4] B11 PERN[4] B12 | PERST_L C12 CLKREQ_L[3] C13 | CLKREQ_L[2] D12 REFCLKOP[1] D13 | REFCLKON[1] D14 REFCLKOP[2] E13 | REFCLKON[2] E14 CLKREQ_L[1] F11 | REFCLKOP[3] F13 REFCLKON[3] F14 | REFCLKIP G13 REFCLKIN G14 | REFCLKOP[4] H13 REFCLKON[4] H14 | REFCLKOP[5] J13 REFCLKON[5] J14 | REFCLKOP[6] K13 REFCLKON[6] K14 | REFCLKOP[7] L13 REFCLKON[7] L14 | DWNRST_L[1] | M2 DWNRST_L[4] M3 | DWNRST_L[5] | M4 DWNRST_L[2] N2 | PERN[0] | N3 PETN[0] N4 | PERN[1] | N5 PETN[1] N6 | REFCLKP[0] | N8 PETN[2] N9 | PERN[2] N10 PETN[3] N11 | PERN[3] N12 DWNRST_L[3] P2 | PERP[0] | P3 PETP[0] P4 | PERP[1] | P5 PETP[1] P6 | REFCLKN[0] | P8 PETP[2] P9 | PERP[2] P10 PETP[3] P11 | PERP[3] P12 U601A PI7C9X2G608GP

# PWR_FLAG

D1+
1 D1-
2 | GND | 3 | D2+ 4 D2-
| | | 5NC

6NC
7 NC

9NC
10 | U630
TPD4E05U06DQA | L6121 3.3uH / 2.37A min

AVDDH_1 1

TXRXP_A 2

TXRXM_A 3
AVDDL_1

4

TXRXP_B 5
TXRXM_B

6

TXRXP_C 7
TXRXM_C

8

AVDDL_2 9
TXRXP_D

10

TXRXM_D 11 | AVDDH_2

12

VDD12CORE 13 | VP
14 GD_1 15 | PCIE_RX_P
16 PCIE_RX_M 17 | GD_2
18 PCIE_TX_P 19 | VPTX
20 PCIE_TX_M 21 | GD_3

22

VPH 23 | RESREF | 24 PCIE_CLK_P 25 | PCIE_CLK_M

26

VDD25_REG_OUT 27 | VDD_REG_IN
28 RESET_N 29 | TEST | 30
VDD12CORE 31 | VDD12_SW_OUT | 32
VDD_SW_IN 33 | VDD12_SW_FB

34

VAUX_DET/GPIO3/LED3/TCK 35 | EECLK/GPIO2/LED2/TMS/ADV_PM_DISABLE | 36
EEDIO/GPIO1/LED1/TDO 37 | EECS/GPIO0/LED0/TDI | 38
VDDVARIO 39 | VDD12CORE | 40
VDD_OTP 41 | CLKREQ#
42 WAKE# 43 | PERST#

44

AVDD12 45 | XO

46

XI 47 | ISET | 48

VSS_EP 49 U611

# LAN7430 L6111 3.3uH / 2.37A min D1+

1 D1-

2 | GND | 3 | D2+ 4 D2-
| | | 5NC

6NC
7 NC

9NC
10 | U631
TPD4E05U06DQA | 200R R61211% 2.2k R605 475R R604 1% ¹.43k R603 1% ¹.43k R602 1% ⁴.7k R601
AGND C5 | AGND | C6
AVDDH C8 | AGND | C9
AGND C10 | AGND C11
VDDR D4 | VDDC | D5
VDDC D6 | AVDD | D7
AVDD D8 | VDDC | D9
VDDC D10 | VDDR D11
VDDC E4 | DGND | E5 DGND E6 | DGND | E7 DGND E8 | DGND | E9 DGND E10 | VDDC E11 DGND F5 | DGND | F6 DGND F7 | DGND | F8 DGND F9 | DGND F10
AVDDH G3 | VDDC | G4 DGND G5 | DGND | G6 DGND G7 | DGND | G8 DGND G9 | DGND G10
VDDC G11 | CVDDR G12
AGND H3 | VDDC | H4 DGND H5 | DGND | H6 DGND H7 | DGND | H8 DGND H9 | DGND H10
VDDC H11 | CVDDR H12 DGND J5 | DGND | J6 DGND J7 | DGND | J8 DGND J9 | DGND J10
VDDC K4 | DGND | K5 DGND K6 | DGND | K7 DGND K8 | DGND | K9 DGND K10 | VDDC K11
VDDR L4 | VDDC | L5
VDDC L6 | AVDD | L7
AVDD L8 | VDDC | L9
VDDC L10 | VDDR L11
AGND M5 | AGND | M6
AVDDH M7 | AGND | M9
AGND M10 | AGND M11 U601C

# PI7C9X2G608GP

C602

# 100nF C603

# 100nF C601

# 100nF C604

# 100nF ⁰RR607 2.2k R606

REXT[1] A8 | SHCL_I2C A13
LNKSTS[4] A14 | LNKSTS[2] | B1 REXT_GND[1] B8 | SHDA_I2C B13
LNKSTS[3]/LNKSTS_DIS B14 | NC | C1
LNKSTS[5] C2 | NC | C3 NC C4 | NC | C7
SHPCINT_L C14 | GPIO[1] | D1 GPIO[0] D2 | NC | D3 GPIO[4] E1 | GPIO[3] | E2 GPIO[2] E3 | IREF E12 UPS_PORTSEL[1]/DBO[4] F1 | GPIO[5] | F2 UPS_PORTSEL[0]/DBO[3] F3 | NC | F4
SDA_I2C F12 | NC | G1 UPS_PORTSEL[3] G2 | NC | H1 UPS_PORTSEL[2] H2 | GPIO[7] | J1 RXPOLINV_DIS J2 | DBO[1] | J3 GPIO[6] J4 | SCL_I2C J11
SWG_LVL J12 | NC | K1 NC K2 | DBO[2] | K3
EEDO K12 | SMBUS_EN_L | L1 CLKBUF_PD L2 | NC | L3
EECK L12 | NC | M1 NC M8 | EECS_L M12
LNKSTS[1]/DBG_DIS M13 | EEDI M14 PL_512B/DBO[0] N1 | REXT_GND[0] | N7
VC1_EN N13 | NC N14 NC P1 | REXT[0] | P7 PWR_SAV_DIS P13 | TEST/LNKSTS[0] P14 U601B
PI7C9X2G608GP | 330R R650
WAKE 1 | +³V3AUX

# 2 COEX1

# 3 GND

# 4 COEX2

5 +¹V5

# 6 CLKREQ

7 | UIM_PWR

# 8 UIM_DATA 10 REFCLK-

11 | UIM_CLK

# 12 REFCLK+

13 | UIM_RESET 14 UIM_VPP

# 16 UIM_C8

# 17 UIM_C4

# 19 W_DISABLE 20 PERST 22 PERn0

# 23 +³V3AUX 24

# PERp0

25 | +¹V5 28

# SMB_CLK

# 30 PETn0

31

# SMB_DATA 32 PETp0

# 33 USB_D-

# 36 USB_D+

38 | +³V3AUX 39 | +³V3AUX 41

# LED_WWAN

42

# LED_WLAN

# 44 Reserved 45

# LED_WPAN

46 Reserved 47 +¹V5 48 Reserved 49 Reserved 51 +³V3AUX 52 | MP MP
J620 | AW7915-NP1_WIFI6_4T4R
XI 1 | GND
2 XO

3

4 Y611

# 25MHz / 10pF / -40..85C

C6115

# 15pF C0G

WAN2_1V2

# LAN1_1V2 NET_3V3 PCIE_UP_WAKE_N

LAN1_1V2

GND

LAN1_ISET LAN1_1V2 GND

LAN1_1V2 GND

GND

LAN1_MDI_A_P

LAN1_MDI_A_N

# LAN1_MDI_B_PLAN1_LED_A1

CHASSIS_GND

# CHASSIS_GNDNET_3V3

LAN1_LED_A2 NET_3V3

LAN1_LED0

LAN1_LED_A2

LAN1_LED1 | GND

LAN1_MDI_B_P

LAN1_MDI_B_N

GND

LAN2_MDI_A_N

LAN1_LED3

LAN1_MDI_B_N

LAN1_MDI_C_P

LAN1_MDI_C_N

LAN1_MDI_D_P

LAN1_MDI_D_N

GND WAN2_MDI_A_P WAN2_MDI_A_N WAN2_MDI_C_P WAN2_MDI_C_N | WAN2_LED_A2

CHASSIS_GND

CHASSIS_GND | NET_3V3
LAN2_MDI_A_P WAN2_LED0 WAN2_MDI_B_P WAN2_MDI_B_N | WAN2_LED_A1 WAN2_LED_A2 WAN2_LED1

LAN1_MDI_A_P

LAN1_MDI_A_N

WAN2_1V2

LAN2_MDI_B_N

LAN1_ISET LAN1_XO

GND WIFI_DISABLE1_N WIFI_PCIE_PERST_N WIFI_PCIE_TX_N WIFI_PCIE_TX_P WIFI_PCIE_RX_N WIFI_PCIE_RX_P

LAN2_MDI_B_P

WAN2_2V5

GND

WIFI_3V3 WIFI_3V3 WIFI_3V3 WIFI_3V3 WIFI_3V3

LAN2_LED_A2 NET_3V3

LAN2_LED_A1 NET_3V3

GND

LAN2_MDI_C_P

LAN2_MDI_B_N

LAN2_MDI_C_N

CHASSIS_GND

CHASSIS_GND

LAN2_MDI_D_N

LAN2_MDI_D_P

WAN2_MDI_A_N

LAN2_1V2 | GND
LAN1_1V2 | LAN2_SW_NODE | LAN2_1V2

WAN2_MDI_B_P

LAN2_RESREF | LAN2_ISET

PCIE_UP_RX_N_CM5 WIFI_PCIE_REFCLK_N WIFI_PCIE_PERST_N

LAN1_PCIE_PERST_N

SW_REXT1 GND

PCIE_MODE_606_HIGH

LAN2_PCIE_PERST_N

PCIE_UP_RX_P_CM5 | GND | GND

SW_REFCLK0_IN_N

GND

LAN2_1V2

SYS_I2C7_SDA

PCIE_UP_WAKE_N

NET_3V3

LAN2_LED1

LAN2_LED3

CHASSIS_GND

# CHASSIS_GNDNET_3V3 WAN1_LED_A1

LAN1_LED0

LAN2_RESET_LOCAL_N

LAN2_2V5

LAN2_PCIE_REFCLK_P

LAN2_2V5

LAN2_PCIE_TX_N

LAN2_PCIE_TX_P

LAN2_PCIE_RX_N

GND

LAN2_1V2

LAN2_MDI_D_N

LAN2_1V2

LAN1_LED2

LAN2_MDI_C_P

LAN2_MDI_B_P

LAN2_MDI_A_N

LAN2_2V5

PCIE_UP_CLKREQ_N

LAN1_1V2

SYS_I2C7_SCL

LOGIC_3V3

LAN1_SW_NODE

PCIE_1V0 NET_3V3 GND

GND

GND

PCIE_1V0 GND

GND

GND

PCIE_1V0 GND

GND

GND NET_3V3 PCIE_1V0 | SW_REFCLK1_IN_N

SW_REFCLK1_IN_P

SW_REFCLK2_RAW_N

LAN1_RESET_LOCAL_N

GND

SW_REFCLK1_RAW_P

SW_REFCLK0_IN_P

WAN2_MDI_C_P

LAN2_XI LAN1_2V5

GND

GND

GND

PCIE_1V0 PCIE_1V0

LAN1_PCIE_REFCLK_P

SW_REFCLK0_IN_N

SW_REFCLK1_RAW_N

SW_REFCLK2_RAW_P

LAN1_2V5

PCIE_1V0 GND

GND

GND

PCIE_1V0

PCIE_1V0 PCIE_1V0 PCIE_1V0 GND

GND

NET_3V3

GND

GND

GND

# GND NET_3V3 PCIE_1V0 GND

GND

GND

GND

GND

GND

GND

GND NET_3V3 GND NET_3V3 PCIE_1V0 | GND

GND

GND NET_3V3 GND

GND

GND

GND

GND

LAN1_PCIE_TX_N

GND

GND

GND NET_3V3 | GND

PCIE_1V0 PCIE_1V0 PCIE_1V0 PCIE_1V0 PCIE_1V0 PCIE_1V0 PCIE_1V0 GND NET_3V3 GND

NET_3V3

NET_3V3 GND

GND

GND

# LAN2_1V2 GND

LAN2_ISET LAN2_XO

SW_IREF | GND

LAN2_PCIE_PERST_N

LAN2_PCIE_CLKREQ_N

LAN2_1V2

SW_REXT1

LAN1_XI

PCIE_MODE_606_HIGH

NET_3V3

NET_3V3

SW_REXT0

NET_3V3

LAN2_LED0

LAN2_LED2

LAN2_1V2

LAN2_SW_NODE GND

SYS_I2C7_SCL

NET_3V3

LAN2_PCIE_REFCLK_N

LAN2_RESREF GND

GND

SW_REXT0

LAN2_1V2 GND

LAN2_PCIE_RX_P

GND

# LOGIC_3V3 GND

SYS_I2C7_SDA

LAN1_1V2

SW_IREF

GND

LAN2_1V2 WAN1_MDI3_P WAN1_MDI3_N

GND

LAN2_2V5

LAN2_MDI_D_P

LAN1_RESREF GND WAN2_ISET

WAN2_2V5

GND

GND

LAN1_1V2

# WAN2_PCIE_RX_P WAN2_PCIE_REFCLK_N WAN2_SW_NODE WAN2_1V2

LAN1_SW_NODE

WAN2_LED2 WAN2_LED0 WAN2_1V2 WAN2_PCIE_CLKREQ_N WAN2_PCIE_PERST_N WAN2_XO WAN2_ISET

WAN2_XI | WAN2_XO

GND

LAN2_MDI_C_N WAN1_MDI3_P WAN1_MDI3_N WAN1_MDI1_P WAN1_MDI1_N

LAN2_MDI_B_N WIFI_PCIE_RX_N

LAN2_PCIE_RX_N

LAN1_PCIE_RX_N WAN2_PCIE_RX_N

PCIE_UP_PERST_N

LAN1_PCIE_CLKREQ_N

SW_REFCLK1_RAW_N

SW_REFCLK2_RAW_N WAN2_PCIE_REFCLK_P

PCIE_UP_REFCLK_P

LAN1_PCIE_REFCLK_P

LAN2_PCIE_REFCLK_P

LAN1_LED1 WAN2_PCIE_PERST_N

GND WAN1_MDI0_P WAN1_MDI0_N WAN1_MDI2_P WAN1_MDI2_N WAN1_MDI0_P WAN1_MDI0_N

LAN2_1V2

LAN2_MDI_A_P WAN2_1V2

GND

WIFI_PCIE_CLKREQ_N WIFI_PCIE_RX_P

LAN2_PCIE_RX_P

LAN1_PCIE_RX_P WAN2_PCIE_RX_P

LAN1_XO

WIFI_PCIE_TX_P

LAN2_PCIE_TX_P

SW_REFCLK1_IN_N

LAN1_PCIE_TX_P

GND

WAN2_MDI_D_N WAN2_PCIE_TX_P WIFI_PCIE_TX_N

LAN2_PCIE_TX_N

SW_REFCLK1_IN_P

LAN1_PCIE_TX_N

GND

WAN2_PCIE_TX_N

LAN2_PCIE_CLKREQ_N

SW_REFCLK1_RAW_P

SW_REFCLK2_RAW_P WAN2_PCIE_CLKREQ_N WAN2_PCIE_REFCLK_N

PCIE_UP_REFCLK_N

LAN1_PCIE_REFCLK_N

LAN2_PCIE_REFCLK_N | WAN1_LED_A2 NET_3V3

WAN1_MDI1_P WAN1_MDI1_N

LAN1_MDI_D_N

WAN1_LED1 WAN1_LED_A1 WAN1_LED0 WAN1_LED_A2

WIFI_3V3

WAN1_MDI2_P WAN1_MDI2_N | WAN2_PCIE_TX_P WAN2_PCIE_TX_N

LAN1_MDI_D_P

WAN2_MDI_A_P WAN2_PCIE_REFCLK_P WAN2_2V5 WAN2_RESET_LOCAL_N WAN2_1V2 NET_3V3 WAN2_LED3 WAN2_LED1 NET_3V3 NET_3V3 PCIE_UP_WAKE_N WAN2_1V2 WAN2_XI GND

WAN2_MDI_A_P WAN2_MDI_A_N | WAN2_MDI_B_P WAN2_MDI_B_N

WAN2_MDI_B_N WAN2_MDI_C_N

GND

WIFI_3V3

WAN2_RESREF WAN2_1V2 WAN2_SW_NODE

WIFI_DISABLE1_N

LOGIC_3V3

SYS_I2C7_SDA

GND

SYS_I2C7_SCL

WAN2_1V2 GND | WAN2_2V5

WIFI_PCIE_REFCLK_P

WAN2_MDI_C_N | LAN1_MDI_C_N

WIFI_PCIE_REFCLK_N WIFI_PCIE_CLKREQ_N

NET_3V3 WAN2_LED_A1

PCIE_UP_WAKE_N

WAN2_MDI_D_P

# WAN2_MDI_D_P WAN2_XO

GND

GND

WAN2_MDI_D_P WAN2_MDI_D_N

GND

LAN1_2V5

LAN1_PCIE_PERST_N

WAN2_XI GND

WAN2_MDI_C_P | GND

PCIE_1V0

LAN1_PCIE_CLKREQ_N

WAN2_MDI_D_N

GND

NET_3V3

PCIE_UP_TX_N_CM5

SW_REFCLK0_IN_P

PCIE_UP_TX_P_CM5

LAN1_PCIE_REFCLK_N WAN2_1V2 | WAN2_1V2

LAN1_MDI_C_P

LAN1_LED_A1 | GND

LAN1_XI

GND WAN2_PCIE_RX_N WAN2_2V5

LAN1_XI | LAN1_XO

GND

GND

WAN2_1V2 | GND NET_3V3
| LAN1_RESREF GND

LAN1_PCIE_TX_P

LAN1_PCIE_RX_N

GND

LAN1_1V2

LAN1_MDI_D_N

LAN1_1V2

# LAN2_XI GND

LAN2_MDI_C_P

LAN2_MDI_C_N

GND

LAN1_PCIE_RX_P

LAN2_LED1

LAN2_LED_A1

LAN2_LED0

LAN2_LED_A2

GND

LAN1_1V2

LAN2_MDI_D_N

GND

GND

LAN2_MDI_D_P

LAN1_2V5

GND

LAN2_XO

GND

LAN2_XO

GND

CHASSIS_GND

GND

GND

LAN2_MDI_A_P

LAN2_MDI_A_N

LAN2_MDI_B_P

GND

LAN2_XI LAN2_2V5 GND

LAN2_1V2

NET_3V3 WAN2_RESREF GND

LAN1_MDI_A_P

LAN1_1V2

LAN1_MDI_B_N

LAN1_MDI_C_N

LAN1_MDI_D_P

LAN1_2V5

LAN1_MDI_A_N

LAN1_MDI_B_P

LAN1_MDI_C_P WIFI_PCIE_REFCLK_P WAN1: 74991114412 voltage-mode 1 GbE; shields direct to chassis, PHY-side residual ESD

GPIO[1:0] = 01 selects 606 mode. GPIO1 uses its internal pulldown; GPIO0 is pulled high. Hold PERST# low until 3.3 V, 1.0 V, and 100 MHz REFCLK are stable for at least 100 ms. U601B: 606-mode strap, I2C and calibration; other straps use documented internal defaults

U601C: every 1.0 V / 3.3 V / ground ball shown; place decoupling per ball group

1. PI7C9X2G608GP PCIe GEN2 SWITCH - 606 MODE | NATIVE CM5 WAN1 FRONT END | 2. THREE LAN7430 PCIe GIGABIT ENDPOINTS

AW7915-NP1: true Wi-Fi 6 4T4R Mini PCIe AP, 3.3 V / 4 A rail, four RF pigtails

# 3. WI-FI AP MINI PCIE 4T4R

J620 uses the controlled SD-67910-001 C2 land pattern; 3D/first-article fit remains a release gate.

WAN2: 74991114412 voltage-mode 1 GbE; shields direct to chassis, PHY-side residual ESD | LAN1: 74991114412 voltage-mode 1 GbE; shields direct to chassis, PHY-side residual ESD

U601A: exact PCIe lanes, reset and distributed reference clocks

PWR_FLAG symbols declare off-sheet regulator outputs for ERC; they are not physical parts.

LAN2: 74991114412 voltage-mode 1 GbE; shields direct to chassis, PHY-side residual ESD

Switch port 5 is disabled and unrouted to avoid PCIe Gen2 stubs and an unsafe generic test header.

1 | 2 | 3 | 4 | 5 | 6 | 7 | 8 | 9 | 10 | 11 | 12 | 13 | 14 | 15 | 16
1 | 2 | 3 | 4 | 5 | 6 | 7 | 8 | 9 | 10 | 11 | 12 | 13 | 14 | 15 | 16

AB

C

D

E

## FGH

## IJK

AB

C

D

E

## FGH

# IJK Date: 2026-08-14

Size: A1 | Rev: A1

# Title: Radxa CM5 ProComm Carrier - WWAN and Dual SIM

# File: WWAN-SIM.kicad_sch

# M.2 B-key modem socket supports USB 3.0 and USB 2.0 fallback

# Dedicated 3.8 V / 5 A minimum rail; verify selected modem peak-current waveform

# FSA2567 defaults to physical SIM 1; open-drain low selects physical SIM 2

# RF coax leaves the module directly for four right-side bulkhead antennas ¹⁰⁰k R701

PWR_FLAG | PWR_FLAG | PWR_FLAG

# TP7206 MODEM_SIM_MUX_SEL_OD

# TP7202 MODEM_W_DISABLE1_N

# TP7205 MODEM_STATUS_LED_N

# TP7201 MODEM_FULL_CARD_POWER_OFF_N

# TP7208 GND

1VSIM

1

| SEL | 2
2RST 3 | RST | 4
1RST 5 | GND
| | 6

2CLK

7 | CLK

8

1CLK

9 | NC

10

2DAT 11 | DAT | 12

1DAT 13
VCC

14

2VSIM

15
VSIM

16

EP

17 U704

# FSA2567MPX

# TP7203 MODEM_RESET_N

# TP7207 MODEM_3V8

# TP7204 MODEM_WAKE_N

# CONFIG_3 1 ³.3V 2 GND

3

FULL_CARD_POWER_OFF 6 USB_D+ 7 | W_DISABLE1 8 USB_D- 9 | GPIO_9/DAS/DSS/LED1 10 GPIO_5 20 CONFIG_0 21 GPIO_6 22 GPIO_11 23 GPIO_7 24 DPR 25 GPIO_10 26 GPIO_8 28 PERn1/USB3.0-Rx-/SSIC-RxN 29 UIM-RESET 30 PERp1/USB3.0-Rx+/SSIC-RxP 31 UIM-CLK 32 UIM-DATA 34 PETn1/USB3.0-Tx-/SSIC-TxN 35 UIM-PWR 36 PETp1/USB3.0-Tx+/SSIC-TxP 37 DEVSLP 38 | GPIO_0 40 PERn0/SATA-B+ 41 | GPIO_1 42 PERp0/SATA-B- 43 | GPIO_2 44 GPIO_3 46 PETn0/SATA-A- 47 | GPIO_4 48 PETp0/SATA-A+ 49 PERST 50 CLKREQ 52 REFCLKn 53 PEWAKE 54 REFCLKp 55

# ANTCTL0 59 COEX3 60 ANTCTL1 61 COEX2 62 ANTCTL2 63 COEX1 64

# ANTCTL3 65

SIM_DETECT 66 RESET 67 | SUSCLK 68 CONFIG_1 69 CONFIG_2 75
J701 | WWAN_M2_B_KEY_USB3_USB2

VCC

C1 | RESET | C2 CLOCK
C3 | GND

C5

VPP_NC

C6
I/O

C7

SHIELD

S1
SHIELD

S2

SHIELD

S3
SHIELD

S4

SHIELD

S5
SHIELD

S6 J703

693043020611

VCC

C1 | RESET | C2 CLOCK
C3 | GND

C5

VPP_NC

C6
I/O

C7

SHIELD

S1
SHIELD

S2

SHIELD

S3
SHIELD

S4

SHIELD

S5
SHIELD

S6 J702

693043020611

1

# 2J714CELL_4_GNSS_RF PWR_FLAG

1

# 2J712CELL_2_RF

# DATA1_OUT 1 CLK_OUT 2 DATA2_OUT 3

# VCC 5 DATA2_IN

# 6 CLK_IN

# 7 DATA1_IN

8 | GND U706 | 9

# TPD3F303DPV DATA1_OUT 1 CLK_OUT 2 DATA2_OUT 3

# VCC 5 DATA2_IN

# 6 CLK_IN

# 7 DATA1_IN

8 | GND U705 | 9

# TPD3F303DPV

1

# 2J713CELL_3_RF PWR_FLAG

1

# 2J711CELL_1_RF

C703

# 10uF 25V X5R

D1+
1 D1-
2 | GND

3 D2+
4 D2-

5NC

6NC
7 NC

9NC

10 | U702 TPD4E05U06DQA

C704

# 100nF PWR_FLAG

D1+
1 D1-
2 | GND

3 D2+
4 D2-

5NC

6NC
7 NC

9NC

10 | U703 TPD4E05U06DQA

CELL_3_RF

GND MODEM_UIM_PWR MODEM_UIM_PWR MODEM_SIM_MUX_SEL_OD

MODEM_UIM_CLK MODEM_UIM_RESET MODEM_UIM_CLK MODEM_UIM_DATA MODEM_UIM_PWR | MODEM_UIM_DATA
LOGIC_3V3 | GND | CHASSIS_GND

MODEM_UIM_PWR

GND

MODEM_SIM_MUX_SEL_OD

SIM2_CLK_RAW

MODEM_W_DISABLE1_N

GND | MODEM_STATUS_LED_N

SIM2_DATA_RAW

SIM1_VCC

MODEM_3V8

SIM2_VCC MODEM_FULL_CARD_POWER_OFF_N MODEM_RESET_N

# GND MODEM_WAKE_N

SIM1_RESET_RAW

SIM2_RESET_RAW

MODEM_RESET_N

MODEM_3V8 | WWAN_USB3_RX_P

SIM1_CLK_RAW

SIM1_CLK MODEM_W_DISABLE1_N MODEM_WAKE_N

GND

MODEM_3V8 | WWAN_USB2_DP WWAN_USB2_DM
GND WWAN_USB3_RX_P WWAN_USB3_RX_N | WWAN_USB3_RX_N

GND

MODEM_3V8

WWAN_USB3_TX_P

SIM1_VCC WWAN_USB3_TX_N

WWAN_USB3_TX_P WWAN_USB3_TX_N

WWAN_USB2_DM

GND

WWAN_USB2_DP

GND MODEM_3V8 | MODEM_3V8

CHASSIS_GND CELL_1_RF

GND

SIM2_VCC

SIM2_RESET SIM2_CLK

SIM2_DATA

SIM2_VCC

CHASSIS_GND

SIM1_VCC

GND

MODEM_FULL_CARD_POWER_OFF_N

CHASSIS_GND

CHASSIS_GND

SIM1_CLK

SIM1_RESET SIM1_VCC

GND

CHASSIS_GND

CHASSIS_GND

SIM1_RESET_RAW

SIM1_CLK_RAW

SIM1_DATA_RAW

CELL_2_RF MODEM_STATUS_LED_N

CHASSIS_GND

SIM2_CLK

CHASSIS_GND MODEM_UIM_RESET

SIM2_VCC

CHASSIS_GND | CELL_4_GNSS_RF | CHASSIS_GND

MODEM_SIM_MUX_SEL_OD

CHASSIS_GND

SIM1_RESET GND

SIM1_DATA CHASSIS_GND

SIM1_DATA_RAW

SIM1_DATA | SIM2_RESET_RAW
| SIM2_CLK_RAW

SIM2_DATA_RAW

SIM2_RESET SIM2_DATA CHASSIS_GND

CHASSIS_GND

CHASSIS_GND

# CHASSIS_GND 3. FSA2567 DUAL-SIM MUX

Socket power pins retain the stock symbol's 3.3 V names but are intentionally fed from MODEM_3V8. Qualification window: 3.135-4.4 V module input, >=5 A transient capability, keyed B socket, 42 mm standoff. 6. MODEM CONTROL CONTRACT

1. UNIVERSAL M.2 B-KEY WWAN SOCKET | 2. USB ESD AND MODEM BULK CAPACITANCE

Power-Regulators C1189-C1192 provide 1320 uF low-ESR bulk beside the socket; C703/C704 are local HF bypass.

Place USB ESD at the modem socket; route USB 3 pairs as short, continuous 90 ohm differential channels. | 5. RF BULKHEAD HARNESS CONTRACT

CELL_1

Four off-board ECT 818033349 USS RF IV-to-SMA bulkhead pigtails; final cable length remains a routed sample gate. | CELL_2

Physical SIM 1 uses FSA2567 channel 2 and physical SIM 2 uses channel 1 to implement that default.

CELL_3

R701 keeps SEL high: SIM 1 is selected by default. GPIO control must be open drain; low selects SIM 2. The control domain tracks MODEM_UIM_PWR, preventing a fixed 3.3 V overdrive when the SIM rail is 1.8 V.

# 4. TWO FIELD-ACCESSIBLE NANO-SIM HOLDERS

CELL_4_GNSS

TP7201-TP7208 are copper factory probes. USB 2/3 has no branch or generic test header.

SIM1: TPD3F303 filters RESET/CLK/DATA and clamps VCC beside the holder; shell bonds to CHASSIS_GND. | SIM2: TPD3F303 filters RESET/CLK/DATA and clamps VCC beside the holder; shell bonds to CHASSIS_GND.

Control outputs originate at the system GPIO expander. FULL_CARD_POWER_OFF and RESET require final modem-specific timing validation.

1 | 2 | 3 | 4 | 5 | 6 | 7 | 8 | 9 | 10 | 11 | 12 | 13 | 14 | 15 | 16
1 | 2 | 3 | 4 | 5 | 6 | 7 | 8 | 9 | 10 | 11 | 12 | 13 | 14 | 15 | 16

AB

C

D

E

## FGH

## IJK

AB

C

D

E

## FGH

# IJK Date: 2026-08-14

Size: A1 | Rev: A1

# Title: Radxa CM5 ProComm Carrier - Lid Display Harness

# File: Display-Harness.kicad_sch

# 15.6-inch lid monitor: HDMI video, USB 2 touch, 12 V / 2.5 A

# Carrier connectors face downward at the hinge-edge harness notch

# USB-A is the CM5 host end; cable terminates in USB-B SuperSpeed at the monitor

# No display eFuse; separate fused DISPLAY_12V and DISPLAY_IO_12V branches feed this sheet

1 | 2
3 | 4 J803

## LID_DISPLAY_12V C802

# 100nF ².2k R802 2.2k R801 PWR_FLAG

D1+
1 D1-
2 | GND

3 D2+
4 D2-

5NC

6NC
7 NC

9NC
10 | U801

# TPD4E05U06DQA D1+

1 D1-

2 | GND

3 D2+
4 D2-

5NC

6NC
7 NC

9NC

10 | U802 TPD4E05U06DQA

C801

## 10uF 25V X5R

C808

## 22uF 10V X7R

C806

# 10uF 25V X7R ²⁶.1k R805 0.1%

PWR_FLAG | PWR_FLAG | PWR_FLAG | 7.5k R807S-CONF
PWR_FLAG | L805 2.2uH / 3.7A C805

470nF

PWR_FLAG | PWR_FLAG

EN/SYNC

1
SW

2

VO

3 | PGND

4 PG

5
| VIN

6 PSNS

7 | NR/SS

8

FB

9

S-CONF 10 U805

## TPS62913RPU

C810

## 22uF 10V X7R

C809

## 22uF 10V X7R

C807

## 10uF 25V X7R ⁴.99k R806 0.1% F802 1.10A hold / 16V D1+

1 D1-

2 | GND | 3 | D2+ 4 D2-
| | | 5NC

6NC
7 NC

9NC
10 | U804
TPD4E05U06DQA | F801 | 0.10A hold / 15V

D1+
1 D1-
2 | GND

3 D2+
4 D2-

5NC

6NC
7 NC

9NC

10 | U803 TPD4E05U06DQA

# VBUS 1 D- 2 D+ 3 GND

4

## SSRX- 5 SSRX+ 6 DRAIN

7

## SSTX- 8

SSTX+ 9 SHIELD SHJ802 | TOUCH_USB_HOST
D2+ 1 | D2S

# 2 D2- 3 D1+ 4 D1S

# 5 D1- 6 D0+ 7 D0S

# 8 D0- 9 CK+ 10 CKS 11 CK- 12 CEC 13 UTILITY 14

## SCL 15

SDA 16 | GND 17 +⁵V 18 HPD 19 | SH
J801 | SH | HDMI_TO_LID_DISPLAY

DISPLAY_12V

GND | GND | CHASSIS_GND | HDMI_DDC_SCL

HDMI_D2_P HDMI_D2_N

HDMI_D1_P HDMI_D1_N

HDMI_D0_P | HDMI_5V_OUT

IO_5V0

HDMI_CLK_P HDMI_CLK_N

HDMI_HEAC_P HDMI_DDC_SCL HDMI_DDC_SDA | HDMI_5V_OUT

GND

HDMI_DDC_SDA HDMI_5V_OUT GND HDMI_D0_N

# HDMI_CEC HDMI_HPD

GND

GND GND

TOUCH_USB_5V

TOUCH_USB_DM | DISPLAY_12V

HDMI_DDC_SCL

TOUCH_USB_5V

HDMI_D1_N

HDMI_D1_P
GND | HDMI_CLK_N
GND | HDMI_DDC_SDA

HDMI_D2_N

HDMI_CEC

GND

HDMI_D2_P

GND | DISPLAY_12V

HDMI_D0_P HDMI_D0_N

HDMI_CLK_P

TOUCH_USB_DM

HDMI_HPD

GND

GND

HDMI_5V_OUT

GND

IO5V0_FB

GND

DISPLAY_IO_12V

TOUCH_USB_5V

GND

# IO_5V0 GND

IO_5V0

IO_5V0 | TOUCH_USB_5V

IO5V0_SW

GND

IO5V0_NRSS

IO5V0_SCONF

TOUCH_USB_DP CHASSIS_GND

HDMI_5V_OUT

IO5V0_NRSS | IO5V0_SCONF GND

TOUCH_USB_5V

IO_5V0

IO5V0_SW

CHASSIS_GND

GND

DISPLAY_IO_12V

IO_5V0

IO_5V0_PG

GND

IO5V0_FB

TOUCH_USB_DP

DISPLAY_IO_12V

IO_5V0

IO5V0_FB

DISPLAY_IO_12V GND

IO_5V0

GND | GND

GND

IO_5V0

DISPLAY_IO_12V

Acceptance: full lid travel plus 300 mm panel lift / 45 degree tilt; no connector tension or hinge-line bend. Carrier connectors face down. Store released loops clear of fans, PSU airflow, board keepouts and sharp edges.

Confirm CM5 DDC 5 V tolerance and final pull-up values against the Radxa carrier reference before layout release.

No local display eFuse. Use the upstream AUX_12V branch fuse and H03C keyed 18 AWG harness.

# 5. 12 V / 2.5 A DISPLAY POWER

H03A HDMI, H03B USB touch, H03C 12 V: 1000 +/- 25 mm each, with separate retained hinge and service loops. 6. HINGE-EDGE HARNESS BUILD

# 3. DEDICATED IO_5V0 / 2 A BUCK

DISPLAY_12V design load: 2.5 A continuous / 30 W branch, covering the locked 25 W monitor. The monitor-side SuperSpeed Type-B receptacle is not duplicated as a device connector on this host carrier. Only USB 2 is allocated from the CM5. A standard USB 3 A-to-B cable still carries USB 2 touch data.

# 2. HDMI ESD / LOW-CAPACITANCE SHUNTS

# 4. USB TOUCH HOST PORT

Shell bonds to chassis at the connector. TMDS shield returns use the local digital ground plane. HDMI_HEAC_N remains unused in Rev A; the selected monitor uses video/DDC/CEC/HPD only.

IO_5V0 feeds CM5 U13-B pin 106, HDMI source 5 V and USB-touch VBUS; no monitor-power eFuse.

# 1. HDMI TYPE-A SOURCE CONNECTOR

Place all HDMI ESD arrays immediately behind J801 with no stubs on TMDS pairs.

1 | 2 | 3 | 4 | 5 | 6 | 7 | 8 | 9 | 10 | 11 | 12 | 13 | 14 | 15 | 16 | 17 | 18 | 19 | 20 | 21 | 22 | 23
1 | 2 | 3 | 4 | 5 | 6 | 7 | 8 | 9 | 10 | 11 | 12 | 13 | 14 | 15 | 16 | 17 | 18 | 19 | 20 | 21 | 22 | 23

AB

C

D

E

## FGH

## IJK

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
## FGH

## IJK

LM

N

O

# P Date: 2026-08-16

Size: A0 | Rev: A1

# Title: Radxa CM5 ProComm Carrier - TDM and Headset Audio

# File: Audio-Control.kicad_sch

# I2S0/TDM program audio is buffered over LVDS to the separate AUDIO-8X8 board

# I2S1 uses explicit 3.3 V to 1.8 V translation before the ES8316 codec

# TPA6132A2 provides 0 dB dedicated stereo headphone amplification

# Kycon STX-353K7A is CTIA-mapped; its preliminary land pattern requires a coupon

C902

1uF

## INL-

1

## INL+

2

## INR+

3

## INR-

4 | OUTR

5 G0

6 G1

7 | HPVSS

## 8 CPN

9 PGND 10 | CPP

## 11 HPVDD 12

EN

13 | VDD 14 SGND 15 | OUTL 16 EP U913 | 17 | C924
2.2uF | C925 2.2uF

VCCA 1

| SCLA | 2
SDAA 3 | GND | 4

EN 5

| SDAB | 6

SCLB 7

## VCCB 8 U903 PCA9517ADP

C920

1uF | C923

## 2.2uF C921

1uF | C922 1uF
D1D2D3D4 EN 1 DIN1 2 DIN2 3 | VCC

# 4 GND

## 5 DIN3 6 DIN4 7

EN 8 | DOUT4- 9 DOUT4+ 10 DOUT3+ 11 DOUT3- 12 DOUT2- 13 DOUT2+ 14 DOUT1+ 15 DOUT1- 16 U901 | SN65LVDS047PW

D1+
1 D1-
2 | GND

3 D2+
4 D2-

5NC

6NC
7 NC

9NC

10 | U914 TPD4E05U06DQA

SLEEVE_MIC

1 | R2_GND

2 R1_HP_R

3

TIP_HP_L 4

SWITCH_A 5
SWITCH_B
6 J910 | C930
100nF ².2k R903 | 2.2k R904 | 2.2k R910 | 330k R911

C926

## 100nF 0R R900star bond

C928

## 100nF C927

100nF

CCLK

1 | MCLK

2 DVDD

3 | PVDD

4 DGND

5
| SCLK

6 DSDIN

7 | DLRCK

8

ASDOUT 9 | GPIO1

10 GPIO2

11 | GPIO3

12 CPVSSP

13 | CPVDD

14 CPTOP

15 | CPBOT | 16 CPGND
17 | CPGNDREF | 18 ROUT 19
LOUT | 20 DACVREF 21
| AVDD

22

AGND

23

ADCVREF 24

VMID

25 | MICBIAS

26 RIN2

27
| LIN2

28 RIN1

29
LIN1
30 CE 31 | CDATA | 32

E-PAD

33 U912 C916

## 10uF C915

10uF

R
B

1

A 2 | NC

3 NC

# 4 GND

5 NC

6 R

7

## VCC 8 U902 SN65LVDT2D 2.2k R901

C914

10uF

1 | 2
3 | 4
5 | 6
7 | 8
9 | 10
11 | 12
13 | 14
15 | 16
17 | 18
19 | 20
21 | 22
23 | 24
25 | 26
27 | 28
29 | 30
| J901

## AUDIO_8X8_TDM_CONTROL

C919

4.7uF ².2k R902 | 100k R912 | 100k R913 10k R914

C906

100nF | C907
100nF | C929
100nF | C918

## 10uF C917

10uF

## IN 1 GND

2

EN 3 | OUT 5 U911 | LP5907MFX-1.8 PWR_FLAG

C911

# 1uF VCCA 1

## 1DIR 2 2DIR 3

1A1 4
1A2 5
2A1 6
2A2 7 | GND

8

## 2B2 10 2B1 11 1B2 12 1B1 13

2OE 14 1OE 15 | VCCB 16 U905
PWR_FLAG | PWR_FLAG

C912

## 1uF PWR_FLAG

C910

# 1uF PWR_FLAG

## IN 1 GND

2

EN 3 | OUT 5 U910 | LP5907MFX-3.3 | C913
1uF ².2k R905 | 2.2k R906 C904

## 100nF C903

100nF | VCCA 1 | GND

2

A 3 | B
4 DIR 5 | VCCB

## 6 U906 GND

# 1 VREF1

2

## SCL1 3 SDA1 4

## SDA2 5

## SCL2 6 VREF2

7

EN 8 U904 | 2.2k R908 | C905
100nF | C908

## 100nF ².2k R907 C901

100nF

AUD_MCLK 1

AUD_BCLK 2

AUD_FSYNC 3

AUD_DAC_SDIN 4

AUD_ADC_SDOUT 5

SYS_I2C7_SCL 6

SYS_I2C7_SDA 7

AUD_IRQ_N | 8 HS_MCLK 9 | HS_BCLK | 10 HS_LRCK 11 | HS_SDOUT_TO_CODEC | 12 HS_SDIN_FROM_CODEC 13 | HS_I2C_SCL | 14 HS_I2C_SDA 15 | HS_JACK_DET_N | 16 U900 CM5_AUDIO_OFFSHEET_PORT
HS_CODEC_I2C_SDA | HPAMP_CPN

LOGIC_3V3 GND

LOGIC_3V3

HPAMP_CPP

AUD_ADC_SDOUT_P

GND

AUD_ADC_SDOUT LOGIC_3V3

HPAMP_CPN

HPAMP_HPVSS

AUD_BCLK

SYS_I2C7_SCL AUD_IRQ_N

AUDIO_ENABLE

AUD_DAC_SDIN

GND

AUD_MCLK

AUD_FSYNC

# AUD_ADC_SDOUT SYS_I2C7_SDA HS_SDIN_FROM_CODEC

HEADSET_HP_R

AUD_DAC_SDIN

HS_BCLK HS_SDOUT_TO_CODEC HS_I2C_SCL HS_I2C_SDA | HS_JACK_DET_N

HS_MCLK HS_LRCK

AUD_ADC_SDOUT_N

HS_I2C_SCL HEADSET_1V8 HS_CODEC_I2C_SDA

LOGIC_3V3

LOGIC_3V3

HEADSET_1V8

LOGIC_3V3

LOGIC_3V3 HEADSET_AGND

HS_I2C_SDA

HEADSET_AGND

HS_I2C_SDA HS_I2C_SCL

LOGIC_3V3

LOGIC_3V3 HEADSET_1V8 HS_CODEC_I2C_SDA | HEADSET_AGND HS_CODEC_I2C_SCL

HEADSET_AGND

# HS_LRCK HS_SDOUT_TO_CODEC HEADSET_AGND HEADSET_AGND

LOGIC_3V3

HEADSET_AGND HEADSET_AGND | HEADSET_AGND
HEADSET_AGND | HEADSET_AGND

HEADSET_1V8

HEADSET_1V8 | HS_CODEC_SDIN HEADSET_1V8 HS_CODEC_I2C_SCL | HEADSET_AGND

GND HEADSET_AGND HEADSET_1V8
HEADSET_1V8

LOGIC_3V3

HEADSET_HP_L

SYS_4V0 | HEADSET_3V3 HEADSET_AGND HEADSET_POWER_EN

HS_SDIN_FROM_CODEC

HEADSET_3V3 HS_CODEC_MCLK HS_CODEC_BCLK

SYS_4V0 HEADSET_AGND

SYS_4V0 | LOGIC_3V3

HS_CODEC_LRCK

HPAMP_HPVSS

HS_CODEC_SDOUT

HEADSET_3V3 HEADSET_AGND

HEADSET_AGND

LOGIC_3V3

HEADSET_3V3 HEADSET_AGND

GND | HEADSET_AGND

HEADSET_1V8

HEADSET_3V3 | HEADSET_AGND HEADSET_POWER_EN

HEADSET_3V3 HS_BCLK

HEADSET_AGND

HS_MCLK

ES8316_DACVREF HEADSET_AGND

ES8316_ADCVREF

LOGIC_3V3 | HS_CODEC_BCLK HS_CODEC_LRCK

ES8316_ADCVREF ES8316_MICBIAS

AUD_I2C_SCL

ES8316_CE HEADSET_3V3 HEADSET_AGND

LOGIC_3V3

LOGIC_3V3 HEADSET_AGND

HEADSET_POWER_EN

HEADSET_AGND | HEADSET_AGND HEADSET_AMP_EN

HEADSET_1V8

HS_CODEC_MCLK HEADSET_1V8 | HEADSET_AMP_EN HS_CODEC_HP_L HPAMP_IN_L | HS_CODEC_HP_R HPAMP_IN_R

SYS_I2C7_SDA

HPAMP_HPVSS HEADSET_AGND

AUDIO_ENABLE

# HEADSET_1V8 HEADSET_AGND

ES8316_VMID | HEADSET_3V3

LOGIC_3V3

AUD_I2C_SCL

SYS_I2C7_SCL GND

LOGIC_3V3

GND

GND

AUD_BCLK_N

AUD_FSYNC_N

AUD_I2C_SDA

AUD_I2C_SDA

LOGIC_3V3

LOGIC_3V3

AUD_MCLK_P

GND

AUD_BCLK_P

AUD_FSYNC_P

GND

GND

GND

AUD_DAC_SDIN_N

AUD_ADC_SDOUT_N

GND

GND

TDM_SPARE_2

SYS_I2C7_SCL | AUD_DAC_SDIN_P

AUD_ADC_SDOUT_P

GND

AUD_I2C_SCL | AUD_I2C_SDA

AUD_DAC_RST_N

AUD_IRQ_N

AUDIO_ENABLE

AUD_ADC_RST_N

AUD_DAC_MUTE_N

AUDIO_PRESENT_N

LOGIC_3V3

TDM_SPARE_1 GND

ES8316_CPVSS

LOGIC_3V3

HEADSET_1V8 HEADSET_AGND

ES8316_CPTOP

AUD_DAC_SDIN_N

HEADSET_AGND

GND

HEADSET_AGND

HEADSET_AGND

ES8316_VMID HS_MIC_INPUT ES8316_CE HEADSET_AGND

AUD_DAC_SDIN_P

HEADSET_1V8

ES8316_CPBOT HEADSET_AGND | HEADSET_3V3 HPAMP_IN_L HEADSET_AGND

HEADSET_AGND

AUD_FSYNC_N

ES8316_CPBOT HEADSET_1V8 HEADSET_AGND | HEADSET_1V8

AUD_MCLK_N

HS_CODEC_HP_L HEADSET_3V3 | HEADSET_AGND HPAMP_IN_R

AUD_MCLK_P

HEADSET_AGND

HEADSET_AGND

HEADSET_AGND

HEADSET_1V8

AUD_BCLK_P

HS_CODEC_I2C_SCL HEADSET_1V8 HEADSET_AGND HS_CODEC_SDOUT HS_CODEC_SDIN

ES8316_CPVSS

ES8316_CPTOP HEADSET_AGND HS_CODEC_HP_R
ES8316_DACVREF | HEADSET_AGND
AUD_MCLK | HS_MIC_JACK HEADSET_HP_R HEADSET_AGND

AUD_BCLK

HS_JACK_DET_N

HEADSET_HP_L HEADSET_HP_R

AUD_BCLK_N

LOGIC_3V3

AUD_FSYNC_P

ES8316_MICBIAS HS_MIC_JACK | HS_MIC_JACK HS_MIC_INPUT

HEADSET_AGND

AUD_FSYNC | HEADSET_AGND HEADSET_HP_L HS_JACK_DET_N

LOGIC_3V3

SYS_I2C7_SDA

HEADSET_3V3

HS_MIC_JACK HS_JACK_DET_N

HEADSET_AGND

HPAMP_CPP

AUD_MCLK_N

# 5. TPA6132A2 HEADPHONE AMPLIFIER

CE is pulled to 1.8 V; all ES8316 digital pins are translated. Decoupling follows the Radxa reference topology.

# 6. CTIA HEADSET JACK, MIC BIAS, DETECT, AND ESD

# 4. ES8316 I2S1 HEADSET CODEC

G0=1 and G1=0 select 0 dB gain. EN remains software-controlled for pop-free mute.

Firmware must debounce HS_JACK_DET_N and perform pop-free mute before any route change. Sequence: enable rails, configure ES8316, enable TPA6132A2, then ramp software volume.

HEADSET_POWER_EN and HEADSET_AMP_EN default low so the codec and amplifier remain muted during boot. 7. HEADSET CONTROL POLICY

R900 is the only headset analog-ground bond. Do not create a second PCB or chassis bond.

J910 is routable for prototype capture, but its drawing-derived footprint is blocked from production until sample/coupon sign-off.

# 3. DEDICATED LOW-NOISE HEADSET RAILS

CM5 audio GPIO is 3.3 V. ES8316 digital pins remain entirely in the translated 1.8 V domain.

# 2. I2S1 HEADSET LEVEL TRANSLATION

# 1. I2S0/TDM PROGRAM-AUDIO LVDS LINK

CTIA contact map: tip=L, ring1=R, ring2=GND, sleeve=MIC. Verify isolated switch polarity on a Kycon sample. J901 mates with AUDIO-8X8 J101. Route five 100 ohm differential pairs with the assigned interleaved returns. SN65LVDT2D includes the ADC-data receiver termination; do not add a duplicate far-end resistor.

1 | 2 | 3 | 4 | 5 | 6 | 7 | 8 | 9 | 10 | 11 | 12 | 13 | 14 | 15 | 16 | 17 | 18 | 19 | 20 | 21 | 22 | 23
1 | 2 | 3 | 4 | 5 | 6 | 7 | 8 | 9 | 10 | 11 | 12 | 13 | 14 | 15 | 16 | 17 | 18 | 19 | 20 | 21 | 22 | 23

AB

C

D

E

## FGH

## IJK

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
## FGH

## IJK

LM

N

O

# P Date: 2026-08-14

Size: A0 | Rev: A1

# Title: Radxa CM5 ProComm Carrier - Power Regulators and Sequencing

# File: Power-Regulators-A1.kicad_sch

# RAW_OUT_LOAD accepts 10.5 V to 30 V after source selection and load telemetry

# The 27.2 mF / 50 V no-blink bank resides on floor-mounted PWR-SELECT

# DISPLAY_12V is a fused 12 V / 2.5 A harness branch with no dedicated eFuse

Component values are Rev A1 starting values; bench loop, thermal, and transfer validation remain mandatory

C1118

# 100nF 25V X7R

C1152

# 4.7uF 50V 100k R11510.1%

C1154

# 47uF X7R

C1155

47uF X7R | 0R R1153 RBOOT L1150 4.7uH / 15.2A Isat 43.2k R11520.1%

BIAS

1
VCC

2

AGND

3
FB

4 PGOOD

5 | RT | 6

EN/SYNC

7
VIN1

8 PGND1

9
SW

10 PGND2

11
VIN2
12 RBOOT 13 | CBOOT | 14 U1140

# LM61440RJR

C1150

100nF

BIAS

1
VCC

2

AGND

3
FB

4 PGOOD

5 | RT | 6

EN/SYNC

7
VIN1

8 PGND1

9
SW

10 PGND2

11
VIN2
12 RBOOT 13 | CBOOT | 14 U1150
LM61440RJR | 7.5k R11702S-CONF

C11710

## 470nF 4.99k R117110.1%

EN/SYNC

1
SW

2

VO

3 | PGND

4 PG

5
| VIN

6 PSNS

7 | NR/SS

8

FB

9

S-CONF 10 U1171

# TPS62913RPU

C11715

# 10uF 25V X7R

C11714

10uF 25V X7R | 6.19k R117100.1%

C11703

## 22uF 10V X7R L1140 4.7uH / 15.2A Isat

C11702

# 22uF 10V X7R

+VIN

1 | -VIN
2 +VOUT 3 | COMMON

4 -VOUT 5 U1180

# TRI 20-1223 ON AUDIO-8X8 C11713

# 22uF 10V X7R

C11712

# 22uF 10V X7R

C1112

# 150pF C0G

C11711

22uF 10V X7R ⁴.99k R11120.1% | 7.5k R11712S-CONF 7.5k R1113 | L11710 2.2uH / 1.5A rail C1156

# 1uF 10V X7R

C1161

4.7uF 50V | C1162
4.7uF 50V 3A | F1180 time-lag 69.8k R11151% ⁴⁰.2k R1110 | 10k R11161% | 3A | F1181 time-lag | 0R R1163 RBOOT C1166

# 1uF 10V X7R

C1165

47uF X7R | 0.25A | F1183 fast 2A | F1182 time-lag | 3A | F1184 time-lag | 2A | F1185 time-lag

C1160

100nF

C1109

# 1uF 50V X7R

C1163

# 47uF X7R

C1164

# 47uF X7RL1160 4.7uH / 15.2A Isat

BIAS

1
VCC

2

AGND

3
FB

4 PGOOD

5 | RT | 6

EN/SYNC

7
VIN1

8 PGND1

9
SW

10 PGND2

11
VIN2
12 RBOOT 13 | CBOOT | 14 U1160
LM61440RJR | 43.2k R11620.1%
1 | 2
3 | 4
J1100 RAW_POWER_FROM_PWR_SELECT | 100k R11610.1% 33.2k R1160/ 400kHz

C11701

# 22uF 10V X7R

C11700

# 470nF L11700 2.2uH / 2.0A rail

EN/SYNC

1
SW

2

VO

3 | PGND

4 PG

5
| VIN

6 PSNS

7 | NR/SS

8

FB

9

S-CONF 10 U1170

# TPS62913RPU

C1146

1uF 10V X7R ⁰R R1143 RBOOT | 33.2k R1150/ 400kHz C1151

# 4.7uF 50V

1

# 2 3 Q1110 NVMFS6B25NL 1

2 3 Q1111

# FDWS86068-F085 4.99k R117010.1%

C1189

# 330uF 6.3V polymer

C1113

# 47uF 6.3V X7R

C1190

330uF 6.3V polymer | C1192 330uF 6.3V polymer

C1114

# 47uF 6.3V X7R

C1191

# 330uF 6.3V polymer

# TP1193 MODEM_3V8

TP1192

# AUX_12V

CT 1 | NC

2

VIN

3
VBIAS

4 ON

5 | GND

6 PG

7
| VOUT1

8

VOUT2

9
VOUT3

10 U1141

# TPS22990DMLR L1110 3.3uH / 29.2A Isat

C11705

## 10uF 25V X7R 1.24k R117000.1%

# PWR_FLAG ⁴⁹⁹R R1114

C1122

33nF

# PWR_FLAG

C1149

10nF

PWR_FLAG | PWR_FLAG

TP1191

# SYS_4V0

C1119

# 4.7uF 10V X7R

C1111

6.8nF

# TP1190 RAW_OUT_LOAD

C1193

# 470uF 6.3V polymer C11704

# 10uF 25V X7R ³⁵.7k R11320.1%

C1133

# 47uF X7R

C1134

# 47uF X7R

C1138

## 4.7nF 255R R11381% / 6A ILIM

IN1 1

IN2 | 2
IN3 3 | GND1 | 4 GND2 5
EN/UVLO | 6

ITIMER 7

ILIM | 8
IMON 9 | RETRY_DLY | 10 NRETRY 11 | LDSTRT | 12 PG 13 | GND3 | 14
dVdt 15 | IN4 | 16 OUT1 17 | OUT2 | 18 OUT3 19 | OUT4 | 20 OUT5 21 | OUT6 | 22 OUT7 23 | OUT8 | 24 U1131

# TPS259827LNRGER ¹⁰⁰k R11310.1%

C1132

# 4.7uF 50V ³³.2k R1130/ 400kHz C1131

# 4.7uF 50V

C1210

10nF

BIAS 1

VCC 2

AGND 3

FB | 4 PGOOD 5 | RT | 6

EN/SYNC 7

VIN1 | 8 PGND1 9
SW | 10 PGND2 11 | VIN2 | 12 RBOOT 13 | CBOOT | 14 U1130
LM61460RJR | 100k R11410.1% 33.2k R1140/ 400kHz

C1130

100nF | 0R R1133 RBOOT L1130 4.7uH / 15.2A Isat

C1142

4.7uF 50V | C1153 47uF X7R

C1141

4.7uF 50V | C1140

## 100nF 43.2k R11420.1%

C1135

# 47uF X7R

C1136

# 1uF 10V X7R

C1143

# 47uF X7R

C1144

# 47uF X7R

C1145

# 47uF X7R

C1110

47nF | C1196

# 4.7uF 50V X7R

C1195

# 4.7uF 50V X7R

C1117

# 47uF 6.3V X7R

C1116

47uF 6.3V X7R | 27.4k R1121 C1197

# 4.7uF 50V X7R

C1194

# 4.7uF 50V X7R

C1115

# 47uF 6.3V X7R

C1126

# 330uF 16V polymer C1125

# 330uF 16V polymer C1124

330uF 16V polymer | 10k R11281% 73.2k R11271% | 93.1k R1122 20.0k R11110.1%

C1120

220pF | C1127
330uF 16V polymer D1120 BAT54WS | D1121 BAT54WS²⁸⁰k R11230.1%

EN/UVLO

1 | RT | 2

SS/TRK

3 | COMP

4

FB

5
AGND

6

SYNCOUT 7
SYNCIN

8 NC

9 | PGOOD

10

ILIM

11 | PGND

12

LO

13
VCC

14

EP

15 | NC
16 BST 17 | HO

18

SW

19
VIN

20 U1110

# LM5146RGYR

C1121

100nF

1

# 2 3 Q1120 CSD18532Q5B

C1205

# 4.7uF 50V X7R

C1203

# 4.7uF 50V X7R

C1204

# 4.7uF 50V X7R

C1201

# 2.2nF C1200

# 4.7uF 10V

1

# 2 3 Q1122 CSD17573Q5B

C1202

# 4.7uF 50V X7R

C1129

# 100nF 25V C1128

# 100nF 25V

EN/UVLO

1
VIN

2

VISNS

3 | MODE | 4 DITH
5 | RT/SYNC

6

SLOPE 7
| SS

8 COMP

9
AGND

10

FB

11
VOSNS

12

ISNS-

13
ISNS+

14 CSG

15 | CS

16 PGOOD

17
| SW2

18 HDRV2

19 | BOOT2

20

LDRV2

21 | PGND

22

VCC

23 | BIAS

24

LDRV1

25 | BOOT1

26 HDRV1

27
| SW1

28

EP

29 U1120

# LM5176PWP

1

# 2 3 Q1121 CSD18532Q5B

C1123

560pF | 4mR R11266W

1

## 2 3 Q1123 CSD17573Q5B 6mR R11202W L1120 4.7uH / 20.9A Isat 20k R11240.1% 10k R1125

GND

NET3V3_FB

AUX_COMP_C

AUX_SW1

AUX_SW2

AUX_FB

GND

AUX_COMP_C

AUX_12V_PRE

AUX_COMP

# AUX_CS GND

AUX_SW2

AUX_FB

AUX_12V

AUX_COMP

AUX_CS

AUX_EN_UVLO | RAW_OUT_LOAD
RAW_OUT_LOAD | AUX_MODE
AUX_DITH | AUX_RT AUX_SS GND

AUX_12V_PRE

AUX_SW2

AUX_BOOT2

AUX_BOOT1

AUX_SLOPE

AUX_COMP

AUX_12V

AUX_12V_PG

SYS_EN_UVLO

AUX_HDRV2

AUX_LDRV2

AUX_VCC

AUX_LDRV1

AUX_HDRV1 GND

AUX_FB | AUX_12V GND | AUX_CS

AUX_SW1

AUX_VCC

GND

LOGIC_3V3 GND

AUX_BOOT2

AUX_CS

AUX_LDRV1

AUX_SW2

AUX_BOOT1

AUX_SW1

AUX_BOOT2

AUX_LDRV2

AUX_DITH

GND

AUX_SW2

RAW_OUT_LOAD

GND | GND

AUX_HDRV2 RAW_OUT_LOAD

AUX_SW1

RAW_OUT_LOAD | RAW_OUT_LOAD

GND

RAW_OUT_LOAD

GND

AUX_HDRV1

GND | AUX_FB
AUX_SS | AUX_12V

AUX_12V_PRE SYS_4V0_PG

GND

AUX_VCC

GND

AUX_12V

GND

AUX_BOOT1 | AUX_VCC

SYS_COMP

GND

GND

AUX_12V

AUX_SW1

AUX_MODE | AUX_SLOPE

SYS_RT

SYS_FB

AUX_EN_UVLO | GND

RAW_OUT_LOAD

SYS_4V0

RAW_OUT_LOAD

GND

AUX_12V GND

AUX_12V

RAW_OUT_LOAD

AUX_EN_UVLO

GND

SYS_VCC

AUX_12V

GND

GND

RAW_OUT_LOAD

GND | GND

SYS_HO

GND

SYS_4V0

GND

GND | GND

AUX_RT RAW_OUT_LOAD

GND

GND

SYS_SW

GND

SYS_BST

SYS_4V0 | SYS_4V0

SYS_LO

GND

SYS_ILIM

RAW_OUT_LOAD | RAW_OUT_LOAD

SYS_SYNCOUT_TP

# WIFI3V3PRE_RBOOT WIFI3V3PRE_CBOOT WIFI3V3PRE_VCC

GND | GND WIFI_3V3_PRE

SYS_RT

WIFI_3V3_PRE | WIFI_3V3_PRE GND | GND

GND

RAW_OUT_LOAD

GND MODEM_3V8_PRE GND | MODEM3V8PRE_VCC

SYS_EN_UVLO

GND

WIFI3V3PRE_FB

GND | WIFI3V3PRE_CBOOT WIFI3V3PRE_SW

SYS_SS

MODEM_3V8_PRE | RAW_OUT_LOAD

GND

GND

MODEM3V8PRE_RT | MODEM3V8PRE_FB | MODEM3V8PRE_CBOOT | MODEM3V8PRE_RBOOT MODEM3V8PRE_SW | MODEM3V8PRE_CBOOT

MODEM3V8PRE_SW

MODEM3V8PRE_FB

RAW_OUT_LOAD

GND WIFI3V3PRE_RT

MODEM3V8PRE_VCC | WIFI_3V3_PRE WIFI3V3PRE_FB

MODEM_3V8_PRE

# MODEM_3V8 MODEM_3V8 MODEM_DVDT GND

GND

GND

GND

RAW_OUT_LOAD

GND

RAW_RAIL_EN MODEM3V8PRE_RBOOT

RAW_OUT_LOAD

GND

# GND MODEM_DVDT MODEM_3V8 MODEM_3V8

MODEM3V8PRE_FB

# MODEM_3V8_PRE MODEM_3V8_PRE MODEM_ITIMER MODEM_IMON MODEM_3V8_PG

GND

MODEM3V8PRE_CBOOT

MODEM_ITIMER

GND | GND MODEM_ILIM

RAW_OUT_LOAD

# NET_3V3 NET3V3_FB NET_3V3

GND

WIFI_3V3_PRE GND | WIFI3V3PRE_FB MODEM3V8PRE_SW
GND | MODEM_3V8_PRE GND

RAW_OUT_LOAD

MODEM_3V8_PRE

MODEM3V8PRE_RT

SYS_4V0

GND

WIFI_3V3 GND

SYS_COMP_C

SYS_4V0

SYS_ILIM | SYS_VCC

NET_3V3_PG

RAW_OUT_LOAD | SYS_4V0

RAW_OUT_LOAD

GND

GND WIFI_DVDT

WIFI_3V3_PRE WIFI_POWER_EN WIFI_3V3_PG WIFI_3V3

NET_3V3

NET_3V3

GND

GND

SYS_SW

GND | GND
SYS_4V0 GND | PCIE1V0_FB PCIE_1V0

SYS_SW

SYS_BST

LOGIC_3V3 GND WIFI_3V3 WIFI_3V3 WIFI_DVDT

GND

GND

MODEM_3V8

SYS_4V0

AUX_12V

SYS_SW

SYS_SW

MODEM_3V8 GND | GND

NET_3V3

MODEM_3V8

SYS_4V0

MODEM_3V8_PRE GND MODEM_POWER_EN MODEM_ILIM

GND

GND

GND MODEM_3V8_PRE MODEM_3V8 MODEM_3V8 MODEM_3V8 MODEM_3V8 | MODEM_3V8 GND | GND MODEM_3V8

GND

SYS_4V0

PCIE1V0_FB

GND

PCIE1V0_NRSS PCIE1V0_SCONF

GND

SYS_LO

RAW_OUT_LOAD

GND | GND

RAW_OUT_LOAD

SYS_SW

SYS_HO

PCIE1V0_FB

PCIE1V0_SW

SYS_4V0 GND

GND

PCIE1V0_SW

PCIE_1V0 PCIE1V0_NRSS | PCIE_1V0

NET3V3_RT

GND

NET3V3_RBOOT

GND | GND

GND

PCIE1V0_EN

PCIE_1V0 PCIE_1V0_PG

GND

GND | LOGIC3V3_FB
LOGIC3V3_RT | LOGIC_3V3

GND

RAW_OUT_LOAD | RAW_RAIL_EN

LOGIC3V3_RBOOT LOGIC_3V3_PG

RAW_RAIL_EN

GND

GND

LOGIC3V3_VCC

LOGIC3V3_FB

LOGIC3V3_RT RAW_OUT_LOAD

LOGIC3V3_SW NET3V3_RBOOT

RAW_OUT_LOAD | LOGIC_3V3
LOGIC3V3_CBOOT | LOGIC3V3_SW

LOGIC_3V3 GND

LOGIC_3V3 GND

RAW_OUT_LOAD RAW_OUT_LOAD

LOGIC3V3_SW

LOGIC3V3_FB

GND NET3V3_CBOOT | LOGIC3V3_CBOOT

DISPLAY_IO_12V

AUX_12V

FAN_AUX_12V

AUX_12V

MODEM_3V8_PRE_PG

GND MODEM_3V8_PRE

AUX_12V NIGHT_LIGHT_12V

AUX_12V

AUDIO_12V

NET3V3_CBOOT | GND | GND NET3V3_VCC | LOGIC_3V3

# LOGIC3V3_RBOOT LOGIC3V3_CBOOT LOGIC3V3_VCC

AUX_12V DISPLAY_12V

AUX_12V

FAN_CPU_12V

RAW_OUT_LOAD

GND

RAW_OUT_LOAD

GND

SYS_FB

RAW_OUT_LOAD

SYS_SS

LOGIC1V8_NRSS

LOGIC1V8_SCONF | LOGIC1V8_SW

LOGIC_1V8

SYS_EN_UVLO

WIFI3V3PRE_SW

LOGIC1V8_SCONF GND

NET_3V3

GND

GND

GND | GND

LOGIC_1V8

SYS_FB

SYS_FB

NET3V3_SW

RAW_OUT_LOAD

LOGIC_1V8 GND

LOGIC_1V8

RAW_OUT_LOAD

SYS_COMP

AUDIO_12V

AUDIO_P15V

AUDIO_N15V

GND

AGND

AGND

SYS_COMP_C

GND

SYS_COMP

PCIE_1V0 | PCIE_1V0

WIFI_3V3_PRE

LOGIC1V8_FB

LOGIC1V8_EN

LOGIC_1V8

LOGIC_1V8_PG

LOGIC1V8_FB LOGIC_1V8

WIFI3V3PRE_SW

GND

WIFI3V3PRE_CBOOT

GND

SYS_4V0

WIFI3V3PRE_RT

SYS_4V0 GND | LOGIC1V8_FB

LOGIC1V8_SW

GND

WIFI3V3PRE_VCC

GND

WIFI3V3PRE_RBOOT

GND

LOGIC1V8_NRSS

GND

SYS_4V0

PCIE1V0_SCONF GND

GND | NET3V3_CBOOT NET3V3_RT RAW_OUT_LOAD NET3V3_SW NET3V3_VCC NET3V3_FB
RAW_RAIL_EN | NET3V3_SW

WIFI_3V3_PRE_PG

AUX_12V | U1180 is a typed off-board handoff only. AUDIO-8X8 locally creates +/-15 V, the quiet 5.5 V pre-rail, separate LT3045 ADC/DAC 5 V rails and AKM 3.3 V.

FAN_CPU_12V and FAN_AUX_12V are separate 3 A branches; every fan also has local resettable protection.

# 6. AUX_12V BRANCHES AND AUDIO HANDOFF

4.006 V nominal follows Radxa RK806 guidance. 300 kHz; target loop crossover about 20 kHz.

1. PROTECTED RAW INPUT FROM PWR-SELECT | 2. SYS_4V0 / 12 A SYNCHRONOUS BUCK

Mates with PWR-SELECT J301; 15 A path; do not mate live.

# 4. DEDICATED RADIO, NETWORK, AND LOGIC BUCKS

C1109 is local high-frequency input decoupling; the clamped bulk bank is not carried by this suspended PCB. PWR-SELECT C306-C309 provide 27.2 mF plus 660 uF local storage upstream of its load shunt.

# 5. LOW-NOISE POINT-OF-LOAD RAILS

TPS22990 provides controlled Wi-Fi startup and PG; it is not a current limiter. | NIGHT_LIGHT_12V: independent 0.25 A fused panel branch; no CM5 or software dependency.

TPS62913 uses 2.2 MHz, 470 nF NR/SS and 2.2 uH. Headset LDOs live on Audio-Control; all AKM rails live on AUDIO-8X8. All PGOOD outputs are open drain; control-sheet 10k pull-ups to LOGIC_3V3 and adjacent rail test pads are required. AUDIO_ENABLE controls the AUDIO-8X8 converters; DAC mute stays asserted through rail and clock qualification. Wi-Fi and modem final rails remain off until Thermal-IO asserts WIFI_POWER_EN / MODEM_POWER_EN after checks. SYS_4V0_PG enables LOGIC_1V8 and PCIE_1V0; hold PCIe reset until NET_3V3_PG and PCIE_1V0_PG are both valid. RAW valid -> SYS_4V0, AUX_12V, LOGIC_3V3 and radio pre-regulators start from local UVLO. 7. SEQUENCING, POWER-GOOD, AND TEST ACCESS

TPS259827L active current limiter; 255 ohm ILIM; 1320 uF local modem bulk; validate weak-signal TX bursts.

Revised 12 V / 8 A starting design. Recalculate losses and compensation, then verify by Bode plot and full thermal load before routing.

DISPLAY_12V: 12 V / 2.5 A harness, simple fuse only. No dedicated monitor eFuse by requirement.

# 3. AUX_12V / 8 A FOUR-SWITCH BUCK-BOOST

1 | 2 | 3 | 4 | 5 | 6 | 7 | 8 | 9 | 10 | 11 | 12 | 13 | 14 | 15 | 16 | 17 | 18 | 19 | 20 | 21 | 22 | 23
1 | 2 | 3 | 4 | 5 | 6 | 7 | 8 | 9 | 10 | 11 | 12 | 13 | 14 | 15 | 16 | 17 | 18 | 19 | 20 | 21 | 22 | 23

AB

C

D

E

## FGH

## IJK

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
## FGH

## IJK

LM

N

O

# P Date: 2026-08-14

Size: A0 | Rev: A1

# Title: Radxa CM5 ProComm Carrier - Thermal and GPIO Control

# File: Thermal-IO.kicad_sch

# EMC2305 controls CPU, modem, intake, and exhaust fans independently

# PWM pull-ups provide full-speed hardware fallback if the controller or firmware fails

# TMP117 sensors monitor CM5, modem, and board/power zones at 0x48/0x49/0x4A

TCA9535 0x20 captures source, fan, temperature, and power-monitor alerts ².2k R1003 | 10k R1033 | F1024 | 1.1A | 10k R1034hold / 33V | 1k R1070 ring limit

# INT 1

A1

2

A2

3 | P00

4 P01
5 P02
6 P03
7 P04
8 P05
9 P06
10 P07
11 GND 12 | P10

13 P11
14 P12
15 P13
16 P14
17 P15
18 P16
19 P17
20
A0

21

# SCL 22

# SDA 23 VCC 24 U1001

# TCA9535PWR_0x20

1 | 2
3 | 4
5 | 6
7 | 8 J1070 NIGHT_LIGHT_PANEL_HARNESS
1 | 2
3 | 4 J1024
THA0412AD-TZW3 EXHAUST 1kR1062 | 1kR1063 100k R1082 | 100k R1083

1

2 3 Q1065

2N7002K-7

1

2 3 Q1064

## 2N7002K-7 ¹⁰⁰k R1081 1kR1061

1

2 3 Q1062

2N7002K-7

1

2 3 Q1061

2N7002K-7

1

2 3 Q1063

2N7002K-7 | 100k R1018 100k R1014 | 100k R1015 5.1k R1050 | 100k R1016 | 100k R1017 | 100k R1012
SCL 1 | GND

2

# ALERT 3

ADD0 4 | V+

5
SDA 6 | U1050
TMP117_CM5 | 100k R1011 100k R1013 100k R1010 | 0.25A | F1060 fast
PWR_FLAG | PWR_FLAG | PWR_FLAG | 100k R1085 1kR1064 | 1kR1065

C1050

100nF | 100k R1084
1 | 2
3 | 4
5 | 6
7 | 8 J1060

# STATUS_LAMP_PANEL_HARNESS

1 | 2
3 | 4 J1023
THA0412AD-TZW3 INTAKE F1023 | 1.1A hold / 33V
SCL 1 | GND

2

# ALERT 3

# ADD0

4 | V+
| 5
SDA 6 | U1051
TMP117_MODEM | F1022 | 1.1A hold / 33V | 1 | 2
| | | 3 | 4 J1022

# AFB0412SHB-SP04 MODEM FAN

# INT 1

A1

2

A2

3 | P00

4 P01
5 P02
6 P03
7 P04
8 P05
9 P06
10 P07
11 GND 12 | P10

13 P11
14 P12
15 P13
16 P14
17 P15
18 P16
19 P17
20
A0

21

# SCL 22

# SDA 23 VCC 24 U1002

# TCA9535PWR_0x2110k R1042

C1051

100nF PWR_FLAG | 10k R1032 | 10k R1044
PWR_FLAG | 10k R1043 2.2k R1001

C1052

100nF | 1kR1060 100k R1080

1

2 3 Q1060

2N7002K-7

SCL 1 | GND

2

# ALERT 3

# ADD0

4 | V+
| 5
SDA 6 | U1052
TMP117_BOARD_POWER ².2k R1002 | 4.7k R10205%

C1020

100nF 4.7k R1021 | 10k R1031 GND

# 1 VREF1

2

# SCL1 3 SDA1 4

# SDA2 5

# SCL2 6 VREF2

7

EN 8 U1000 | PCA9306DP | F1021 | 3.0A hold / 15V | 10k R1041
1 | 2
3 | 4 J1021

# FFB0412EN-00Y2E CPU FAN

# SMDATA 1

SMCLK 2 | VDD

3

ADDR_SEL 4 | PWM1 5

# TACH1 6 PWM2 7

# TACH2 8 PWM3 9

# TACH3 10 CLK 11

ALERT 12 | PWM4 13

# TACH4 14 PWM5 15

TACH5 16 GND 17U1020 | EMC2305-1-AP-TR | 2.2k R1004 | 4.7k R1005

MODEM_FAN_PWM

STATUS_AUDIO_SINK

CTRL_I2C_SCL | CTRL_I2C_SDA
LOGIC_3V3 | LOGIC_3V3 PWR_MON_ALERT_N

GND

EXHAUST_FAN_TACH

U1001_INT_N

GND

GND

CTRL_I2C_SCL CTRL_I2C_SDA | GND

CPU_FAN_TACH MODEM_FAN_PWM

MODEM_FAN_TACH

INTAKE_FAN_PWM

LOGIC_3V3

INTAKE_FAN_TACH

EXHAUST_FAN_PWM

EXHAUST_FAN_TACH | EXHAUST_FAN_PWM

LOGIC_3V3

CTRL_I2C_SDA CTRL_I2C_SCL

LOGIC_3V3

EMC2305_ADDR

FAN_ALERT_N

LOGIC_3V3

CPU_FAN_PWM

GND | CPU_FAN_12V CPU_FAN_TACH

SYS_I2C7_SDA

CPU_FAN_TACH

LOGIC_3V3 CPU_FAN_PWM

LOGIC_3V3

SYS_I2C7_SCL

CPU_FAN_12V

LOGIC_1V8

FAN_CPU_12V

CTRL_I2C_SCL

GND

CTRL_I2C_SDA

LOGIC_3V3

FAN_ALERT_N

LOGIC_3V3

GND

EXHAUST_FAN_12V

CPU_FAN_PWM

GND

LOGIC_3V3

EMC2305_ADDR

LOGIC_3V3

FAN_AUX_12V

CTRL_I2C_SCL | GND

GND

LOGIC_3V3 CTRL_I2C_SDA

CH_24V_N

CH_BAT_N

CS_GREEN_RING_K NIGHT_LIGHT_SINK

CTRL_I2C_SDA CTRL_I2C_SCL

TEMP_ALERT_N

LOGIC_3V3

NIGHT_LIGHT_SINK

VALID_24V_N

STATUS_BACKUP_GATE | GND STATUS_BACKUP_SINK

EXHAUST_FAN_PWM

GND

STATUS_PWR_GATE | GND STATUS_PWR_SINK

EXHAUST_FAN_12V

SYS_I2C7_SDA

LOGIC_1V8

# LED_PWR_GATE STATUS_PWR_GATE STATUS_PWR_GATE

NIGHT_LIGHT_12V

SYS_I2C7_SCL

GND

CTRL_I2C_SDA

NIGHT_LIGHT_12V

LOGIC_3V3 GND

LOGIC_1V8

MODEM_FAN_TACH

CS_GREEN_RING_K

LOGIC_3V3

INTAKE_FAN_TACH

LOGIC_3V3 | LOGIC_3V3

NIGHT_LIGHT_SINK NIGHT_LIGHT_12V

FAN_AUX_12V | LOGIC_3V3 MODEM_FAN_12V

FAN_AUX_12V

GND

CTRL_I2C_SDA

LOGIC_3V3

AUDIO_ENABLE

AUD_ADC_RST_N

LOGIC_3V3

AUD_DAC_RST_N

AUD_DAC_MUTE_N

HEADSET_POWER_EN

HEADSET_AMP_EN MODEM_FULL_CARD_POWER_OFF_N

LOGIC_3V3

MODEM_STATUS_LED_N WIFI_DISABLE1_N WAN2_RESET_LOCAL_N | WAN2_RESET_LOCAL_N

MODEM_W_DISABLE1_N MODEM_RESET_N MODEM_SIM_MUX_SEL_OD

LAN1_RESET_LOCAL_N

LAN2_RESET_LOCAL_N

GND | MODEM_WAKE_N

MODEM_FAN_PWM

GND | MODEM_FAN_12V MODEM_FAN_TACH

CTRL_I2C_SDA CTRL_I2C_SCL

LOGIC_3V3

GND

GND

# LOGIC_3V3 CTRL_I2C_SCL

GND

INTAKE_FAN_PWM

LOGIC_3V3

FAN_AUX_12V

INTAKE_FAN_12V

LOGIC_3V3

INTAKE_FAN_TACH

TEMP_ALERT_N | STATUS_AUDIO_SINK

STATUS_LED_12V STATUS_BACKUP_SINK

STATUS_CELL_SINK

GND | GND

STATUS_CELL_GATE

LED_CELL_GATE STATUS_CELL_GATE GND | GND

STATUS_TEMP_GATE

LED_TEMP_GATE STATUS_TEMP_GATE

LOGIC_3V3

LOGIC_3V3 GND

FAN_CPU_12V

STATUS_LED_12V

# LED_AUDIO_GATE STATUS_AUDIO_GATE STATUS_AUDIO_GATE

AUX_12V

LOGIC_3V3

STATUS_LED_12V STATUS_PWR_SINK

STATUS_WIFI_SINK

STATUS_TEMP_SINK

MODEM_W_DISABLE1_N

NIGHT_LIGHT_SINK

AUDIO_ENABLE GND

GND

LOGIC_1V8

GND | INTAKE_FAN_12V
| INTAKE_FAN_PWM

GND

EXHAUST_FAN_TACH

VALID_BAT_N

LOGIC_3V3

AUD_DAC_MUTE_N

GND | MODEM_FULL_CARD_POWER_OFF_N

BAT_LOW_N

LOGIC_3V3

MODEM_RESET_N

LOGIC_3V3

LAN1_RESET_LOCAL_N

TEMP_ALERT_N

TEMP_ALERT_N

LED_WIFI_GATE

GND

LOGIC_3V3

AUD_IRQ_N

LAN2_RESET_LOCAL_N

WIFI_DISABLE1_N

LOGIC_3V3

AUDIO_PRESENT_N

STATUS_CELL_GATE

STATUS_WIFI_GATE GND

STATUS_WIFI_SINK

STATUS_WIFI_GATE

STATUS_CELL_SINK

STATUS_TEMP_GATE | GND

LED_AUDIO_GATE

LED_TEMP_GATE

STATUS_WIFI_GATE | GND

FAN_ALERT_N

TEMP_ALERT_N

LED_CELL_GATE

# LED_BACKUP_GATE GND

# STATUS_BACKUP_GATE STATUS_BACKUP_GATE

LED_WIFI_GATE

LED_BACKUP_GATE PWR_MON_ALERT_N

LED_PWR_GATE

STATUS_TEMP_SINK

STATUS_AUDIO_GATE | GND

U1002_INT_N

AUDIO / DX06WG012B

TCA9535 outputs power up as inputs. External straps below define safe reset, mute, radio, and amplifier states.

The three open-drain TMP117 alerts share TEMP_ALERT_N; firmware reads 0x48/0x49/0x4A to identify the source.

W_DISABLE and WIFI_DISABLE are held active during boot; software releases them only after power and thermal checks pass.

TMP117 CM5 / 0x48

U1002: 7-bit address 0x21; INT is test-point only and firmware polls status.

AFB0412SHB-SP04 MODEM FAN

U1001: 7-bit address 0x20; INT is test-point only and firmware polls status. 3. EMC2305 FOUR-FAN CONTROL WITH FAILSAFE | 6. INDEPENDENT WARM-WHITE PANEL LIGHTS

THA0412AD-TZW3 INTAKE

TMP117 BOARD POWER / 0x4A

# 5. SIX 12 V TOP-PANEL STATUS-LAMP DRIVERS

PWR / DX06WG012B

J1060 feeds six external Bulgin DX06 12 V wire-lead indicators. Two supply contacts plus six protected low-side returns. | BACKUP / DX06WY012B

The control branch is isolated by its own PCA9306. Recheck total bus capacitance with the separate AUDIO-8X8 branch populated.

All four PWM nets pull high when U1020 is absent or unpowered, commanding the selected 4-wire fans to full speed. Fan 1 is panel intake and fan 2 is panel exhaust. CPU and modem fans circulate locally beneath their dedicated mesh/keepout areas. FFB0412EN-00Y2E CPU FAN

Enclosure channels: 26.00 kHz base / divide 26 = 1.000 kHz PWM; direct duty with tach monitoring, 100% start and 30% minimum running duty. | THA0412AD-TZW3 EXHAUST 4. THREE HIGH-ACCURACY TEMPERATURE SENSORS

ADDR_SEL 4.7k to 3.3 V selects 7-bit SMBus address 0x2E; internal clock is used.

WIFI / DX06WB012B | CELL / DX06WW012B | TEMP / DX06WR012B
1. 1.8 V TO 3.3 V SYSTEM I2C CONTROL BUS | 2. TWO 16-BIT GPIO EXPANDERS

J1070 is the keyed eight-circuit boundary to external CS7L2FR and two LS102W panel lights. Unused blue/red switch-ring leads are insulated in the harness. Pins 1-4 serve switch GND, 12 V, green ring, and latching sink. Pins 5-8 are the two lamp +/- pairs; the PCB joins both lamps to the switched sink. Hardware-only control: lights remain usable if the CM5 is booting, crashed, or powered down while AUX_12V is available.

TMP117 MODEM / 0x49
