omaralabed/Radxa-CM5-PCB/outputs/schematic-release-a1/Power-Selector-Schematic-A1.pdf

1 | 2 | 3 | 4 | 5 | 6 | 7 | 8 | 9 | 10 | 11
1 | 2 | 3 | 4 | 5 | 6 | 7 | 8 | 9 | 10 | 11

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
## FGH Date: 2026-08-16

## KiCad E.D.A. 10.0.5-rc1

Size: A2 | Rev: A1 Id: 1/1

# Title: Radxa CM5 ProComm 24 V / Battery Seamless Power Selector

## File: PowerSelector.kicad_sch

## Sheet: /

## ProComm

## Fixed priority: internal PSU 24 V, then D-Tap, then Gold Mount dock

## RAW_OUT_LOAD feeds the protected CM5-CARRIER regulator input

## 27.2 mF / 50 V hold-up bank is retained on this floor-mounted board

## Battery inputs use LTC4418 plus back-to-back P-MOS reverse-polarity blocking

10uF 50V

S

1

S

2

S

3 G

4 | D

5 47nF 50V

S

1

S

2

S

3 G

4 | D

5 10uF 50V X7R

PWR_FLAG | PWR_FLAG | PWR_FLAG

A1

1

A0

2

Alert 3

SDA 4

SCL 5 VS

# 6 GND

7

Vbus 8

Vin-

9

Vin+

10

10uF 50V X7R

1 | 2
3 | 4 PWR_FLAG | PWR_FLAG | PWR_FLAG
1 | 2
3 | 4

47nF 50V

S

1

S

2

S

3 G

4 | D
| 5

S

1

S

2

S

3 G

4 | D
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
470nF 50V

TMR 1 UV1 2 OV1 3 UV2 4 OV2 5

VALID1 6

VALID2 7 | GND

8 CAS 9 INTVCC 10 G2 11

VS2 12 G1 13

VS1 14

VOUT 15

V2 16

V1 17

EN 18

SHDN 19 HYS 20 | EP 21 470nF 50V
CTR 1 | GND

2 CTS 3 RESET 4

SENSE 5

VDD 6

100nF

1
2
3
4
5
6
100nF 16V | 1nF C0G | 100uF 63V

SOURCE1 1 GATE1 2

V1 3 UVF1 4 UVR1 5 OV1 6

TMR1 7 DISABLE1 8 CH1 9

VALID1 10

FAULT1 11 | CASIN 12 INTVCC 13 | CASOUT 14 QUAL 15 GND 16 | RETRY 17

SHDN 18

FAULT2 19

VALID2 20 CH2 21 DISABLE2 22

TMR2 23 OV2 24 UVR2 25 UVF2 26

V2 27 | GATE2 28

SOURCE2 29

SENSE2 30 OUT2 31 CPOREF 32 | CPO 33 | EXTVCC 34 | OUT1 35

# SENSE1 36 EP 37

220uF 50V | 220uF 50V | 220uF 50V | 1uF 50V X7R | 100nF 50V | 47nF 50V

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
# 5 47nF 50V

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
# 5 6800uF 50V

PWR_FLAG | PWR_FLAG

1uF 50V X7R

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
510uF 50V 1uF 50V X7R 1

2

1 | 2
3 | 4
6800uF 50V | 1uF 16V 1

2

34

1

2

34

6800uF 50V

A1

1

A0

2

Alert 3

SDA 4

SCL 5 VS

# 6 GND

7

Vbus 8

Vin-

9

Vin+

10

6800uF 50V | 1
| 2

34

1uF 16V | 1nF C0G | 100nF

A1

1

A0

2

Alert 3

SDA 4

SCL 5 VS

# 6 GND

7

Vbus 8

Vin-

9

Vin+

10 | PWR_FLAG
1 | 2
3 | 4
GND | INTVCC

MON_3V3 GND MONBAT_VBUS

VALID_DTAP_N

FAULT_DISABLE_BAT

INTVCC

RAW_OUT_LOAD

FAULT_DISABLE_24

INTVCC

MONBAT_VBUS

INTVCC
PRE_INTVCC

VALID_GOLD_N

SRC_GOLD

GND | MONBAT_INN

RAW_OUT RAW_OUT GATE_BAT BAT_SENSE SRC_BAT GND

SHDN_MAIN

GND

SRC_24 GATE_24

V24_SENSE

BAT_LOW_N

G2_CTRL | BAT_SELECTED

SRC_GOLD

BAT_SELECTED

MON24_INN MON24_INP

RAW_OUT | MON24_INN | MONBAT_INP | RAW_OUT RAW_OUT_LOAD
| | GND
BAT_SENSE RAW_OUT | MONLOAD_INP

GATE_GOLD GATE_GOLD

GATE_GOLD

MON_3V3 | PWR_MON_SCL PWR_MON_SDA PWR_MON_ALERT_N
GND | RAW_OUT_LOAD MON24_INP MON24_INN MON24_VBUS | GND
V24_SENSE | MON24_INP | MON_3V3 G2_CTRL

MONLOAD_INN

V24_FUSED | MON24_VBUSMON24_VBUS GND | MON_3V3 MONLOAD_VBUS MONBAT_VBUS

BAT_SELECTED

MONBAT_INP MONBAT_INN MON_3V3 PWR_MON_SDA PWR_MON_SCL PWR_MON_ALERT_N

GND

GND

BAT_FUSED MONBAT_INP MONBAT_INN

# GND MONLOAD_VBUS

TMR_BAT FAULT_DISABLE_BAT CH_BAT_N

VALID_BAT_N
FAULT_DISABLE_BAT
V24_RTOP_MID | MONLOAD_INN
V24_RTOP_MID | MONLOAD_INP
MON_3V3 V24_FUSED | UVF_24 | UVF_24 | UVR_24 | PWR_MON_ALERT_N

PWR_MON_SDA GND

RAW_OUT_LOAD | RAW_OUT_LOAD

PWR_MON_SCL

RAW_OUT | RAW_OUT GND

GATE_GOLD

MON_3V3 | MONLOAD_INP

GOLD_FUSED

GATE_DTAP

SRC_DTAP

GND

BAT_SENSE

PWR_MON_ALERT_N

GND | GOLD_FUSED

GATE_GOLD

GND | PWR_MON_SCL

GND

INTVCC

GND

RAW_OUT CPO

RAW_OUT

GOLD_FUSED

MON_3V3

SRC_GOLD

BAT_SELECTED

GOLD_FUSED

V24_SENSE

RAW_OUT

GND | GND

SHDN_PRE

GND

GATE_DTAP

GND

GND MON_3V3 PWR_MON_SDA DTAP_FUSED

BAT_FUSED

V24_FUSED

BAT_SELECTED

GND

RAW_OUT GND

RAW_OUT GND

GND

GOLD_IN | GOLD_IN

SHDN_MAIN

V24_IN | V24_IN

DTAP_FUSED

GND

DTAP_FUSED

SHDN_MAIN

GND

V24_FUSED

BAT_FUSED

V24_FUSED

GOLD_FUSED

MONLOAD_INN MONLOAD_VBUS

GOLD_IN

V24_FUSED | V24_FUSED

GND

GND

GATE_BAT

MON_3V3 GND

GND

BAT_FUSED

BAT_MON | MON_3V3 GND

DTAP_FUSED

DTAP_IN
GND
BAT_FUSED | QUAL

GND

DTAP_IN | DTAP_IN

GATE_24

SRC_24 | RAW_OUT | GND

GND

BAT_SELECTED

SRC_DTAP

BAT_SELECTED

GATE_DTAP

GND BAT_FUSED

GND

CH_24V_N RAW_OUT CPO

GND

CH_BAT_N

G1_CTRL GATE_DTAP

G1_CTRL | GATE_DTAP

VALID_24V_N

OV_BAT

BAT_SELECTED

SRC_DTAP

GND

BAT_FUSED

SRC_BAT | OV_BAT | OV_BAT

GATE_24

SRC_24

UVR_BAT

UVR_BAT RAW_OUT GND

RAW_OUT GND

BAT_RTOP_MID | UVF_BAT | UVF_BAT | UVR_BAT

V24_FUSED

GATE_24

BAT_RTOP_MID

GATE_BAT SRC_BAT

VALID_BAT_N

UVF_BAT

DTAP_FUSED

BAT_LOW_N

BAT_SENSE GATE_BAT SRC_BAT | BAT_FUSED | PRE_INTVCC

GND

SHDN_PRE

V24_SENSE

FAULT_DISABLE_24

TMR_PRE BAT_SELECTED

G2_CTRL

SRC_24

VALID_24V_N

SRC_GOLD

CH_24V_N

RAW_OUT GND

RAW_OUT

G1_CTRL

FAULT_DISABLE_24

TMR_24

SRC_DTAP

OV_24 GND

RAW_OUT GND

VALID_GOLD_N

UVR_24

GOLD_FUSED

OV_24 | GND

GND

VALID_DTAP_N

UVF_24

V24_FUSED

OV_24

OV_DTAP UV_DTAP

DTAP_FUSED

RAW_OUT

UVR_24

OV_GOLD UV_GOLD | GND
PRE_INTVCC | TMR_PRE GND

GND

GND | OV_GOLD

GND

BAT_SELECTED

GND

OV_GOLD | OV_DTAP
GOLD_FUSED | OV_DTAP | GND

SHDN_PRE

DTAP_FUSED | DTAP_RTOP_MID | DTAP_RTOP_MID | UV_DTAP MON_3V3

GND

GND

# RAW_OUT_LOADMON_3V3 BAT_MON

RAW_OUT

UV_GOLD | UV_GOLD | UV_DTAP
GND INTVCC | GND QUAL GND
BAT_MON | BAT_MON | GND

GND

BAT_FUSED

TMR_BAT GND

TMR_24 BAT_FUSED

R111 1.50mR KELVIN Q201 | Q202

Q501 External interface: LEMO EGG.0B.302.CLL female panel inlet; pin 1 return, pin 2 positive.

C311 1nF C0G Q502 LTC4418 V1 gives valid D-Tap priority over V2 Gold Mount. Both paths are break-before-make. G. D-TAP / GOLD MOUNT NON-PARALLELING PRESELECTOR

Q101 | Q102 Common-source MOSFET pairs block reverse and cross current. B. BREAK-BEFORE-MAKE IDEAL-DIODE POWER PATHS
C105 D201 SMCJ18A C201 D101 SMCJ24A H01: RPS-400 CN3 +V to J101-1; CN2 -V to J101-2; 14 AWG. A. MAIN INPUT, COMMON BACKUP FUSE, TVS CLAMPS

C101

J202 FROM 2-PIN LEMO PANEL INLET 13.0-16.8 V

C210

SW201 OFF disables both selectors; no valid source can energize RAW_OUT. Charge batteries externally. Both selectors are break-before-make; C301-C309 provide continuous energy to the carrier input. Priority: internal PSU 24 V, then D-Tap, then Gold Mount. No source paralleling.

C110

R302 10.0k 0.1%

REVERSE MISWIRE SAFE: fuse + bidirectional TVS + ceramic C precede LTC4418/back-to-back P-MOS blockers.

R205 1.69R

SiR5607DP: -60 V P-MOS, 12 mOhm max at VGS=-4.5 V. Use large copper heat-spreading areas. D-Tap and Gold Mount are alternate backup inputs only. Never parallel and never charge through this board.

STARTING VALUE: ILIM = 25 mV / 1.50 mR = 16.7 A. Validate tolerance, SOA, and thermal margin before release. C205

## DESIGN INTENT

D511/D521: anode at controller G pin, cathode at MOSFET gate for fast turn-off

R105 2.40R

R511/R521 + C511/C521 limit higher-voltage-source inrush; verify SOA on prototype C532 = 1 nF: about 16 ms source validation

C310 100nF 10V R202 15.8k 0.1%

24 V operating window: UV fall 18.0 V, UV rise 20.0 V, OV rise 30.0 V

BAT_SELECTED FROM LTC4418 PRESELECTOR

F202 15A | D202 SMBJ18CA
J101 BOTTOM-PSU 24 V HARNESS | F101 15A

F203 15A

R203 4.22k 0.1%

Selected-backup outer window: UV fall 10.6 V, UV rise 11.6 V, OV rise 18.1 V D. RAW OUTPUT AND TRANSFER HOLD-UP

J301 RAW OUT TO LM5176

J203 FROM PANEL QRC-GOLD 8375-0094 HARNESS 10.0-16.8 V

R541 47k F201 15A

U603 0x44 R201 28.0k 0.1%

C202

C309

D203 SMBJ18CA

C308

C203

# C. LTC4421 PRIORITY CONTROLLER

U602 0x41 C302 | C303 | C307

R206 12.1k 0.1%

C121 Battery: OV=18.09 V, UV rising=11.58 V, UV falling=10.57 V | U201 LTC4418IUF#PBF

C304

R204 953k 0.1%

R211 1.50mR KELVIN

# C120 E. VALID-VOLTAGE WINDOWS (0.5 V COMPARATOR TAPS)

Physical order is VIN - R4 - UVF - R3 - UVR - R2 - OV - R1 - GND. R102 9.10k 0.1%

C306 | U301 TPS3842A015DRLRQ1

Gold actual: UV rise 11.69 V, UV fall 11.35 V, OV rise 17.74 V Q503

R504 56.2k 0.1%

J401 STATUS TO CARRIER

R506 909k 0.1%

C123/C223 = 100 nF gives about 8.3 ms current-limit timer.

R503 909k 0.1%

C122 = 1 nF gives about 16 ms input qualification.

# F. BATTERY WARNING AND CARRIER STATUS

R311 1.00mR LOAD KELVIN

C223

Open-drain outputs require 3.3 V pull-ups on the carrier. J401 pins 1-8: GND, /CH24, /CHBAT, /VALID24, /VALIDBAT, /BATLOW, /VDTAP, /VGOLD Hardware backup-low policy: assert about 13.02 V; 5% hysteresis releases near 13.67 V. R103 3.01k 0.1% 24 V: OV=29.95 V, UV rising=19.97 V, UV falling=17.99 V

R106 107k 0.1%

R301 176k 0.1%

C122 | C123

R104 953k 0.1%

C301 C301-C303 are low-ESR Panasonic hybrid capacitors. C306-C309: 4 x 6800 uF = 27.2 mF; total with C301-C303 is 27.86 mF nominal. At -20% capacitance the total provides about 25.4 ms ideal hold-up at 184.2 W from 24.0 V to 12.5 V. 30 x 35 mm cans require a tray-supported clamp; board outline and dock clearance remain A2 sample gates.

D-Tap actual: UV rise 12.62 V, UV fall 12.25 V, OV rise 18.00 V

J402 TELEMETRY: 1 3V3, 2 GND, 3 SDA, 4 SCL, 5 /ALERT, 6 GND

R501 55.6k 0.1% Q504

## I. PRIMARY / BACKUP / LOAD DIGITAL POWER TELEMETRY

Source shunts: 1.5mR -> 27.307 A at +/-40.96 mV. Load shunt: 1mR -> 40.96 A. R311 is after the hold-up bank, so U603 includes capacitor-supplied load current during transfer.

J204 KEYED 4-WIRE SWITCH HARNESS OFF opens both poles; 47k pull-downs disable LTC4421 and LTC4418 (fail-OFF). SW201: E-Switch RA812C1121 maintained DPST OFF-ON panel rocker. H. USER SYSTEM POWER SWITCH

U101 LTC4421IUHE#PBF

Switch carries only controller-enable current; no 10 A load current crosses the panel. | R542 47k

R507 10.0k 0.1%

INA228: 85 V, 20-bit shunt/bus monitor; common I2C with wired-OR active-low alert.

R505 31.6k 0.1%

SW201 pole B: J204-3 PRE_INTVCC to J204-4 SHDN_PRE.

R502 26.1k 0.1%

U601 0x40

RETRY is grounded: a sustained overcurrent latches off until the selector is | power-cycled. | SW201 pole A: J204-1 INTVCC to J204-2 SHDN_MAIN. R131 100k

R101 18.2k 0.1%

R231 100k C305
