omaralabed/Radxa-CM5-PCB/docs/radxa_cm5_v2210_pinout.xlsx

Sheet: U13-A
Radxa CM5 V2.21 U13-A Pinout
Pin Number | Raspberry Pi CM4 | Radxa CM5 | RK3588S SoC | Func1 | Func2 | Func3 | Func4 | Func5 | Func6 | Func7 | Func8 | Func9 | Func10 | Note
1 | GND | GND | -
2 | GND | GND | -
3 | Ethernrt_Pair3_P | PHY1_MDI3+ | -
4 | Ethernet_Pair1_P | PHY1_MDI1+ | -
5 | Ethernrt_Pair3_N | PHY1_MDI3- | -
6 | Ethernet_Pair1_N | PHY1_MDI1- | -
7 | GND | GND | -
8 | GND | GND | -
9 | Ethernrt_Pair2_N | PHY1_MDI2- | -
10 | Ethernet_Pair0_N | PHY1_MDI0- | -
11 | Ethernrt_Pair2_P | PHY1_MDI2+ | -
12 | Ethernet_Pair0_P | PHY1_MDI0+ | -
13 | GND | GND | -
14 | GND | GND | -
15 | Ethernrt_nLED3(3.3V) | PHY1_LED2_Y | -
16 | Ethernet_SYNC_IN(1.8v) | NC | -
17 | Ethernrt_nLED2(3.3V) | PHY1_LED1_G | -
18 | Ethernet_SYNC_OUT(1.8v) | NC | -
19 | Ethernrt_nLED1(3.3V) | PHY1_LED0_Y1 | -
20 | EEPROM_nWP | HP_INT | W38 | REFCLK_OUT | GPIO0_A0_d
21 | Pl_nLED_Activity | PWM15_M1 | AV23 | CIF_VSYNC | BT1120_D9 | I2S1_SDO2_M0 | PCIE20X1_2_BUTTON_RSTN | I2C7_SDA_M3 | UART8_CTSN_M0 | PWM15_IR_M1 | CAN1_TX_M1 | GPIO4_B3_u
22 | GND | GND | -
23 | GND | GND | -
24 | GPIO26 | PCIE20X1_2_WAKEN_M0 | AW31 | CIF_D12 | PCIE20X1_2_WAKEN_M0 | HDMI_TX0_SDA_M2 | I2C5_SDA_M0 | UART4_RX_M1 | PWM8_M2 | SPI3_CLK_M3 | GPIO3_D0_u
25 | GPIO21 | I2C4_SDA_M3_WIFI | D38 | VOP_POST_EMPTY | I2C4_SDA_M3 | UART6_RTSN_M1 | PWM0_M2 | SPI4_CLK_M2 | GPIO1_A2_d
26 | GPIO19 | NC | -
27 | GPIO20 | WIFI_REG_ON_E | L40 | PCIE20X1_1_WAKEN_M2 | I2C2_SCL_M4 | UART6_TX_M1 | SPI4_MOSI_M2 | GPIO1_A1_d
28 | GPIO13 | SPIO_MOSI_M1 | AW18 | CIF_D1 | BT1120_D1 | I2S1_SCLK_TX_M0 | PCIE20X1_1_WAKEN_M1 | UART9_CTSN_M1 | SPI0_MOSI_M1 | GPIO4_A1_d
29 | GPIO16 | GSENSOR_INT | G37 | SPI2_MISO_M0 | GPIO1_A4_d
30 | GPIO6 | SPIO_CLK_M1 | AV26 | CIF_D2 | BT1120_D2 | I2S1_LRCK_TX_M0 | PCIE20X1_1_PERSTN_M1 | SPI0_CLK_M1 | GPIO4_A2_d
31 | GPIO12 | SPIO_CS0M1 | AT15 | CIF_HREF | BT1120_D8 | I2S1_SDO1_M0 | PCIE20X1_1_BUTTON_RSTN | I2C7_SCL_M3 | UART8_RTSN_M0 | PWM14_M1 | SPI0_CS0_M1 | CAN1_RX_M1 | GPIO4_B2_u
32 | GND | GND | -
33 | GND | GND | -
34 | GPIO5 | I2S0_SDO0 | P41 | I2S0_SDO0 | I2C4_SCL_M4 | UART4_CTSN | GPIO1_C7_d
35 | ID_SC | I2C8_SCL_M2_CAM | L37 | MIPI_CAMERA3_CLK_M0 | I2C8_SCL_M2 | UART1_RTSN_M1 | PWM14_M2 | GPIO1_D6_u
36 | ID_SD | I2C8_SDA_M2_CAM | G38 | MIPI_CAMERA4_CLK_M0 | I2C8_SDA_M2 | UART1_CTSN_M1 | PWM15_IR_M3 | GPIO1_D7_u
37 | GPIO7 | TP_INT_L | D40 | UART7_TX_M2 | SPI0_CS1_M2 | GPIO1_B5_u
38 | GPIO11 | MIPI_CAM2_RST_L | M37 | PDM1_CLK1_M1 | SATA0_ACT_LED_M1 | UART4_TX_M2 | SPI0_CLK_M2 | GPIO1_B3_d
39 | GPIO8 | TP_RST_L | M39 | PDM1_CLK0_M1 | UART7_RX_M2 | SPI0_CS0_M2 | GPIO1_B4_u
40 | GPIO9 | GPIO1_B1 | G39 | PDM1_SDI2_M1 | SPI0_MISO_M2 | GPIO1_B1_d
41 | GPIO25 | LCD_RESET_L | H39 | PDM1_SDI1_M1 | SPI2_CS1_M0 | GPIO1_B0_u
42 | GND | GND | -
43 | GND | GND | -
44 | GPIO10 | GPIO1_B2_CAM1 | M38 | PDM1_SDI3_M1 | UART4_RX_M2 | SPI0_MOSI_M2 | GPIO1_B2_d
45 | GPIO24 | GPIO1_A6_CAM1 | D39 | SPI2_CLK_M0 | GPIO1_A6_d
46 | GPIO22 | I2S0_SCLK_TX | M42 | I2S0_SCLK_TX | I2C6_SCL_M1 | UART3_CTSN | PWM7_IR_M2 | SPI4_CS0_M0 | GPIO1_C3_d
47 | GPIO23 | MIPI_CAM2_PDN_L | H38 | PDM1_SDI0_M1 | PCIE20X1_1_PERSTN_M2 | PWM3_IR_M3 | SPI2_CS0_M0 | GPIO1_A7_u
48 | GPIO27 | I2S0_LRCK_TX | P39 | I2S0_LRCK_TX | I2C2_SCL_M3 | UART4_RTSN | GPIO1_C5_d
49 | GPIO18 | I2C4_SCL_M3_WIFI | L39 | I2C4_SCL_M3 | UART6_CTSN_M1 | PWM1_M2 | SPI4_CS0_M2 | GPIO1_A3_d
50 | GPIO17 | I2S0_MCLK | U36 | I2S0_MCLK | I2C6_SDA_M1 | UART3_RTSN | PWM3_IR_M2 | SPI4_CLK_M0 | GPIO1_C2_d
51 | GPIO15 | UART2_RX_M0 | AH40 | I2S1_SCLK_TX_M1 | JTAG_TMS_M2 | I2C1_SDA_M0 | UART2_RX_M0 | PCIE20X1_1_WAKEN_M0 | GPIO0_B6_d
52 | GND | GND | -
53 | GND | GND | -
54 | GPIO4 | I2S0_SDI0 | N42 | I2S0_SDI0 | GPIO1_D4_d
55 | GPIO14 | UART2_TX_M0 | AH39 | I2S1_MCLK_M1 | JTAG_TCK_M2 | I2C1_SCL_M0 | UART2_TX_M0 | PCIE20X1_1_CLKREQN_M0 | GPIO0_B5_d
56 | GPIO3 | GPIO0_C7 | AL40 | I2S1_SDI2_M1 | PDM0_SDI0_M1 | I2C6_SDA_M0 | UART1_RTSN_M2 | PWM6_M0 | SPI0_MISO_M0 | GPIO0_C7_d
57 | SD_CLK | SDMMC_CLK | AR1 | SDMMC_CLK | PDM1_CLK0_M0 | TEST_CLKOUT_M0 | MCU_JTAG_TMS_M0 | CAN0_RX_M1 | UART5_TX_M0 | GPIO4_D5_d
58 | GPIO2 | GPIO0_D0 | AG39 | I2S1_SDI3_M1 | PDM0_SDI1_M1 | I2C6_SCL_M0 | UART1_CTSN_M2 | PWM7_IR_M0 | SPI3_MISO_M2 | GPIO0_D0_d
59 | GND | GND | -
60 | GND | GND | -
61 | SD_DAT3 | SDMMC_D3 | AT1 | SDMMC_D3 | PDM1_SDI0_M0 | JTAG_TMS_M0 | I2C8_SDA_M0 | UART5_RTSN_M0 | PWM10_M1 | GPIO4_D3_u
62 | SD_CMD | SDMMC_CMD | AU1 | SDMMC_CMD | PDM1_CLK1_M0 | MCU_JTAG_TCK_M0 | CAN0_TX_M1 | UART5_RX_M0 | PWM7_IR_M1 | GPIO4_D4_u
63 | SD_DAT0 | SDMMC_D0 | AV2 | SDMMC_D0 | PDM1_SDI3_M0 | JTAG_TCK_M1 | I2C3_SCL_M4 | UART2_TX_M1 | PWM8_M1 | GPIO4_D0_u
64 | SD_DAT5 | NC | -
65 | GND | GND | -
66 | GND | GND | -
67 | SD_DAT1 | SDMMC_D1 | AR2 | SDMMC_D1 | PDM1_SDI2_M0 | JTAG_TMS_M1 | I2C3_SDA_M4 | UART2_RX_M1 | PWM9_M1 | GPIO4_D1_u
68 | SD_DAT4 | NC | -
69 | SD_DAT2 | SDMMC_D2 | AV1 | SDMMC_D2 | PDM1_SDI1_M0 | JTAG_TCK_M0 | I2C8_SCL_M0 | UART5_CTSN_M0 | GPIO4_D2_u
70 | SD_DAT7 | NC | -
71 | GND | GND | -
72 | SD_DAT6 | NC | -
73 | SD_VDD_Override | VCCIO_FLASH | -
74 | GND | GND | -
75 | SD_PWR_ON | SD_PWR_ON | AV30 | CIF_D10 | SPI3_MISO_M3 | GPIO3_C6_u
76 | Reserved | NC | -
77 | +5v_(input) | VCC_SYSIN | -
78 | GPIO_VREF(1.8v/3.3v_input) | GPIO_VREF | -
79 | +5v_(input) | VCC_SYSIN | - |  |  |  |  |  |  |  |  |  |  | default is 4V
80 | SCL0 | I2C7_SCL_M2 | AY30 | CIF_D14 | I2C7_SCL_M2 | UART9_RTSN_M2 | SPI0_MOSI_M3 | GPIO3_D2_d
81 | +5v_(input) | VCC_SYSIN | - |  |  |  |  |  |  |  |  |  |  | default is 4V
82 | SDA0 | I2C7_SDA_M2 | AY31 | CIF_D15 | I2C7_SDA_M2 | UART9_CTSN_M2 | PWM10_M2 | SPI0_CLK_M3 | GPIO3_D3_d
83 | +5v_(input) | VCC_SYSIN | - |  |  |  |  |  |  |  |  |  |  | default is 4V
84 | +3.3v_(output)600mA Max | VCC_3V3_S3 | -
85 | +5v_(input) | VCC_SYSIN | - |  |  |  |  |  |  |  |  |  |  | default is 4V
86 | +3.3v_(output) | VCC_3V3_S3 | -
87 | +5v_(input) | VCC_SYSIN | - |  |  |  |  |  |  |  |  |  |  | default is 4V
88 | +1.8v_(output)600mA Max | VCC_1V8_S0 | -
89 | WL_nDisable | PWM4_M0 | AG38 | I2S1_SDI0_M1 | GPU_AVS | UART0_TX_M0 | I2C4_SCL_M2 | PWM4_M0 | GPIO0_C5_u
90 | +1.8v_(output)600mA | VCC_1V8_S0 | -
91 | BT_nDisable | HOST_WAKE_BT_H | AH42 | I2S1_SDI1_M1 | NPU_AVS | UART0_RTSN | PWM5_M1 | SPI0_CLK_M0 | SATA_CP_POD | GPIO0_C6_u
92 | RUN_PG | RESET_L | V42 | NPOR
93 | nRPIBOOT | SARADC_VIN0_BOOT | AW15 | SARADC_IN0_BOOT
94 | Analogip1 | NC | -
95 | nPl_LED_PWR | WIFI_LED | AV34 | CIF_D9 | FSPI_CS1N_M2 | CAN2_TX_M0 | UART5_RX_M1 | SPI3_CS1_M3 | GPIO3_C5_u
96 | Analogip0 | SARADC_VIN4 | AY15 | SARADC_IN4
97 | Camera_GPIO | USB_HOST_PWREN_H | G40 | PCIE20X1_1_CLKREQN_M2 | DP0_HPDIN_M2 | I2C2_SDA_M4 | UART6_RX_M1 | SPI4_MISO_M2 | GPIO1_A0_d
98 | GND | GND | -
99 | Global_EN | PWRON_L | -
100 | nEXTRST | SPIO_MISO_M1 | AV19 | CIF_D0 | BT1120_D0 | I2S1_MCLK_M0 | PCIE20X1_1_CLKREQN_M1 | UART9_RTSN_M1 | SPI0_MISO_M1 | GPIO4_A0_d

Sheet: U13-B
Radxa CM5 V2.21 U13-B Pinout
Pin Number | Raspberry Pi CM4 | Radxa CM5 | RK3588S SoC | Func1 | Func2 | Func3 | Func4 | Func5 | Func6 | Func7 | Func8 | Func9 | Func10 | Note
101 | USB_OTG_ID | TYPEC0_USB20_OTG_ID | AW10 | TYPEC0_USB20_OTG_ID
102 | Pcie_CLK_nREQ | PCIE20X1_2_CLKREQN_M0 | AU30 | CIF_D11 | PCIE20X1_2_CLKREQN_M0 | HDMI_TX0_SCL_M2 | I2C5_SCL_M0 | SPI3_MOSI_M3 | GPIO3_C7_u
103 | USB2_N | TYPEC0_OTG_DM | AY10 | TYPEC0_USB20_OTG_DM
104 | Reserved | NC | -
105 | USB2_P | TYPEC0_OTG_DP | AY11 | TYPEC0_USB20_OTG_DP
106 | Reserved | 5V_HDMI | - |  |  |  |  |  |  |  |  |  |  | If VCC_SYSIN provides 5V input, this pin can be No Connect; if VCC_SYSIN provides less than 5V, this pin needs to provide 5v from the IO board to the Radxa CM5 .
107 | GND | GND | -
108 | GND | GND | -
109 | Pcie_nRST | PCIE20X1_2_PERSTN_M0 | AY27 | CIF_D13 | PCIE20X1_2_PERSTN_M0 | UART4_TX_M1 | PWM9_M2 | SPI0_MISO_M3 | GPIO3_D1_d
110 | Pcie_CLK_P | PCIE20_0_REFCLKP | L42 | PCIE20_0_REFCLKP
111 | VDAC_COMP | NC | -
112 | Pcie_CLK_N | PCIE20_0_REFCLKN | K41 | PCIE20_0_REFCLKN
113 | GND | GND | -
114 | GND | GND | -
115 | CAM1_DO_N | MIPI_DPHY0_RX_D0N | BB38 | MIPI_DPHY0_RX_D0N | MIPI_CPHY0_RX_TRIO0_A
116 | Pcie_RX_P | PCIE20_0_RXP | J42 | PCIE20_0_RXP | SATA30_0_RXP
117 | CAM1_DO_P | MIPI_DPHY0_RX_D0P | BA38 | MIPI_DPHY0_RX_D0P | MIPI_CPHY0_RX_TRIO0_B
118 | Pcie_RX_N | PCIE20_0_RXN | J41 | PCIE20_0_RXN | SATA30_0_RXN
119 | GND | GND | -
120 | GND | GND | -
121 | CAM1_D1_N | MIPI_DPHY0_RX_D1N | AY40 | MIPI_DPHY0_RX_D1N | MIPI_CPHY0_RX_TRIO0_C
122 | Pcie_TX_P | PCIE20_0_TXP | H41 | PCIE20_0_TXP | SATA30_0_TXP
123 | CAM1_D1_P | MIPI_DPHY0_RX_D1P | BA40 | MIPI_DPHY0_RX_D1P | MIPI_CPHY0_RX_TRIO1_A
124 | Pcie_TX_N | PCIE20_0_TXN | H42 | PCIE20_0_TXN | SATA30_0_TXN
125 | GND | GND | -
126 | GND | GND | -
127 | CAM1_C_N | MIPI_DPHY0_RX_CLKN | BA41 | MIPI_DPHY0_RX_CLKN | MIPI_CPHY0_RX_TRIO1_B
128 | CAM0_D0_N | MIPI_CSI0_RX_D0N | AL41 | MIPI_CSI0_D0N
129 | CAM1_C_P | MIPI_DPHY0_RX_CLKP | BB41 | MIPI_DPHY0_RX_CLKP | MIPI_CPHY0_RX_TRIO1_C
130 | CAM0_D0_P | MIPI_CSI0_RX_D0P | AL42 | MIPI_CSI0_D0P
131 | GND | GND | -
132 | GND | GND | -
133 | CAM1_D2_N | MIPI_DPHY0_RX_D2N | BA42 | MIPI_DPHY0_RX_D2N | MIPI_CPHY0_RX_TRIO2_A
134 | CAM0_D1_N | MIPI_CSI0_RX_D1N | AK42 | MIPI_CSI0_D1N
135 | CAM1_D2_P | MIPI_DPHY0_RX_D2P | AY42 | MIPI_DPHY0_RX_D2P | MIPI_CPHY0_RX_TRIO2_B
136 | CAM0_D1_P | MIPI_CSI0_RX_D1P | AK41 | MIPI_CSI0_D1P
137 | GND | GND | -
138 | GND | GND | -
139 | CAM1_D3_N | MIPI_DPHY0_RX_D3N | AW42 | MIPI_DPHY0_RX_D3N | MIPI_CPHY0_RX_TRIO2_C
140 | CAM0_C_N | MIPI_CSI0_RX_CLK0N | AN41 | MIPI_CSI0_CLK0N
141 | CAM1_D3_P | MIPI_DPHY0_RX_D3P | AW41 | MIPI_DPHY0_RX_D3P | NO_USE
142 | CAM0_C_P | MIPI_CSI0_RX_CLK0P | AN42 | MIPI_CSI0_CLK0P
143 | HDMI1_HOTPLUG | NC | -
144 | GND | GND | -
145 | HDMI1_SDA | HDMI0_TX_SBDP | BA1 | HDMI_TX0_SBDP | EDP_TX0_AUXP
146 | HDIM1_TX2_P | NC | -
147 | HDMI1_SCL | HDMI0_TX_SBDN | AY1 | HDMI_TX0_SBDN | EDP_TX0_AUXN
148 | HDIM1_TX2_N | NC | -
149 | HDMI1_CEC | NC | AW22 | BT1120_D12 | SATA0_ACT_LED_M0 | I2C5_SCL_M1 | PWM13_M1 | SPI3_MOSI_M1 | GPIO4_B6_d
150 | GND | GND | -
151 | HDMI0_CEC | HDMI_TX0_CEC_PORT | AY26 | BT1120_D15 | SPDIF1_TX_M2 | PCIE20X1_2_PERSTN_M1 | HDMI_TX0_CEC_M0 | I2C8_SDA_M3 | PWM6_M1 | SPI3_CS1_M1 | GPIO4_C1_d
152 | HDIM1_TX1_P | NC | -
153 | HDMI0_HOTPLUG | HDMI_TX0_HPD | M40 | HDMI_TX0_HPD_M0 | SPI2_MOSI_M0 | GPIO1_A5_d
154 | HDIM1_TX1_N | NC | -
155 | GND | GND | -
156 | GND | GND | -
157 | DSIO_DO_N | MIPI_DPHY0_TX_D0N | BA31 | MIPI_DPHY0_TX_D0N | MIPI_CPHY0_TX_TRIO0_A
158 | HDIM1_TX0_P | NC | -
159 | DSIO_DO_P | MIPI_DPHY0_TX_D0P | BB31 | MIPI_DPHY0_TX_D0P | MIPI_CPHY0_TX_TRIO0_B
160 | HDIM1_TX0_N | NC | -
161 | GND | GND | -
162 | GND | GND | -
163 | DSIO_D1_N | MIPI_DPHY0_TX_D1N | BB32 | MIPI_DPHY0_TX_D1N | MIPI_CPHY0_TX_TRIO0_C
164 | HDIM1_CLK_P | NC | -
165 | DSIO_D1_P | MIPI_DPHY0_TX_D1P | BA32 | MIPI_DPHY0_TX_D1P | MIPI_CPHY0_TX_TRIO1_A
166 | HDIM1_CLK_N | NC | -
167 | GND | GND | -
168 | GND | GND | -
169 | DSIO_C_N | MIPI_DPHY0_TX_CLKN | BA34 | MIPI_DPHY0_TX_CLKN | MIPI_CPHY0_TX_TRIO1_B
170 | HDIM0_TX2_P | HDMI0_TX2P | BB7 | HDMI_TX0_D2P | EDP_TX0_D2P
171 | DSIO_C_P | MIPI_DPHY0_TX_CLKP | BB34 | MIPI_DPHY0_TX_CLKP | MIPI_CPHY0_TX_TRIO1_C
172 | HDIM0_TX2_N | HDMI0_TX2N | BA7 | HDMI_TX0_D2N | EDP_TX0_D2N
173 | GND | GND | -
174 | GND | GND | -
175 | DSI1_D0_N | MIPI_DPHY1_TX_D0N | BA16 | MIPI_DPHY1_TX_D0N | MIPI_CPHY1_TX_TRIO0_A
176 | HDIM0_TX1_P | HDMI0_TX1P | BA5 | HDMI_TX0_D1P | EDP_TX0_D1P
177 | DSI1_D0_P | MIPI_DPHY1_TX_D0P | BB16 | MIPI_DPHY1_TX_D0P | MIPI_CPHY1_TX_TRIO0_B
178 | HDIM0_TX1_N | HDMI0_TX1N | BB5 | HDMI_TX0_D1N | EDP_TX0_D1N
179 | GND | GND | -
180 | GND | GND | -
181 | DSI1_D1_N | MIPI_DPHY1_TX_D1N | BB17 | MIPI_DPHY1_TX_D1N | MIPI_CPHY1_TX_TRIO0_C
182 | HDIM0_TX0_P | HDMI0_TX0P | BB4 | HDMI_TX0_D0P | EDP_TX0_D0P
183 | DSI1_D1_P | MIPI_DPHY1_TX_D1P | BA17 | MIPI_DPHY1_TX_D1P | MIPI_CPHY1_TX_TRIO1_A
184 | HDIM0_TX0_N | HDMI0_TX0N | BA4 | HDMI_TX0_D0N | EDP_TX0_D0N
185 | GND | GND | -
186 | GND | GND | -
187 | DSI1_C_N | MIPI_DPHY1_TX_CLKN | BA19 | MIPI_DPHY1_TX_CLKN | MIPI_CPHY1_TX_TRIO1_B
188 | HDIM0_CLK_P | HDMI0_TX3P | BA2 | HDMI_TX0_D3P | EDP_TX0_D3P
189 | DSI1_C_P | MIPI_DPHY1_TX_CLKP | BB19 | MIPI_DPHY1_TX_CLKP | MIPI_CPHY1_TX_TRIO1_C
190 | HDIM0_CLK_N | HDMI0_TX3N | BB2 | HDMI_TX0_D3N | EDP_TX0_D3N
191 | GND | GND | -
192 | GND | GND | -
193 | DSI1_D2_N | MIPI_DPHY1_TX_D2N | BB20 | MIPI_DPHY1_TX_D2N | MIPI_CPHY1_TX_TRIO2_A
194 | DSI1_D3_N | MIPI_DPHY1_TX_D3N | BA22 | MIPI_DPHY1_TX_D3N | MIPI_CPHY1_TX_TRIO2_C
195 | DSI1_D2_P | MIPI_DPHY1_TX_D2P | BA20 | MIPI_DPHY1_TX_D2P | MIPI_CPHY1_TX_TRIO2_B
196 | DSI1_D3_P | MIPI_DPHY1_TX_D3P | BB22 | MIPI_DPHY1_TX_D3P | NO_USE
197 | GND | GND | -
198 | GND | GND | -
199 | HDIM0_SDA | HDMI_TX0_SDA_5V | AW23 | BT1120_D14 | PCIE20X1_2_WAKEN_M1 | HDMI_TX0_SDA_M0 | I2C8_SCL_M3 | SPI3_CS0_M1 | GPIO4_C0_u
200 | HDIM0_SCL | HDMI_TX0_SCL_5V | AV22 | BT1120_D13 | PCIE20X1_2_CLKREQN_M1 | HDMI_TX0_SCL_M0 | I2C5_SDA_M1 | SPI3_CLK_M1 | GPIO4_B7_u

Sheet: J1
Radxa CM5 V2.21 J1 Pinout
Pin Number | Radxa CM5 | RK3588S SoC | Func1 | Func2 | Func3 | Func4 | Func5 | Func6 | Func7 | Func8 | Func9 | Func10 | Note
1 | GND | -
2 | GND | -
3 | TYPEC0_SBU1 | BA8 | TYPEC0_SBU1 | DP0_AUXP
4 | GPIO3_C0 | AR36 | GMAC1_PPSTRIG | I2C3_SDA_M1 | UART7_TX_M1 | SPI1_MISO_M1 | GPIO3_C0_d
5 | TYPEC0_SBU2 | BB8 | TYPEC0_SBU2 | DP0_AUXN
6 | GPIO3_B7 | AY34 | GMAC1_PTP_REF_CLK | I2C3_SCL_M1 | SPI1_MOSI_M1 | GPIO3_B7_d
7 | GND | -
8 | TYPEC0_SBU1_DC | AU34 | CIF_D8 | FSPI_CS0N_M2 | CAN2_RX_M0 | UART5_TX_M1 | SPI3_CS0_M3 | GPIO3_C4_u
9 | TYPEC0_SSRX1P | BB10 | TYPEC0_SSRX1P | DP0_TX0P
10 | GPIO1_B6_CAM2_CLK | L38 | MIPI_CAMERA1_CLK_M0 | SPDIF0_TX_M0 | I2C5_SCL_M3 | UART1_TX_M1 | GPIO1_B6_u
11 | TYPEC0_SSRX1N | BA10 | TYPEC0_SSRX1N | DP0_TX0N
12 | GPIO1_B7 | F37 | MIPI_CAMERA2_CLK_M0 | SPDIF1_TX_M0 | SATA2_ACT_LED_M1 | I2C5_SDA_M3 | UART1_RX_M1 | PWM13_M2 | GPIO1_B7_u
13 | GND | -
14 | TYPEC0_SBU2_DC | AV31 | HDMI_TX0_HPD_M1 | MCU_JTAG_TCK_M1 | UART9_RX_M2 | SPI0_CS0_M3 | GPIO3_D4_d
15 | TYPEC0_SSTX1P | BB11 | TYPEC0_SSTX1P | DP0_TX1P
16 | NC | -
17 | TYPEC0_SSTX1N | BA11 | TYPEC0_SSTX1N | DP0_TX1N
18 | PWM11_M3 | AW30 | MCU_JTAG_TMS_M1 | UART9_TX_M2 | PWM11_IR_M3 | SPI0_CS1_M3 | GPIO3_D5_d
19 | GND | -
20 | GPIO1_C1 | N41 | I2C3_SCL_M0 | UART3_TX_M0 | SPI4_MOSI_M0 | GPIO1_C1_z
21 | TYPEC0_SSRX2P | BB13 | TYPEC0_SSRX2P | DP0_TX2P
22 | GND | -
23 | TYPEC0_SSRX2N | BA13 | TYPEC0_SSRX2N | DP0_TX2N
24 | WIFI_PWR_EN | R39 | I2S0_SDI1 | PDM0_SDI3_M0 | I2C1_SDA_M4 | UART4_RX_M0 | PWM1_M1 | SPI1_CS0_M2 | GPIO1_D3_d
25 | GND | -
26 | SARADC_VIN1_KEY/RECOVERY | AY13 | SARADC_IN1
27 | TYPEC0_SSTX2P | BB14 | TYPEC0_SSTX2P | DP0_TX3P
28 | SARADC_VIN2_DC | AV11 | SARADC_IN2
29 | TYPEC0_SSTX2N | BA14 | TYPEC0_SSTX2N | DP0_TX3N
30 | SARADC_VIN3_HP_HOOK | AV13 | SARADC_IN3
31 | GND | -
32 | GND | -
33 | NC | -
34 | LCD_PWREN_H | AY19 | CIF_D3 | BT1120_D3 | I2S1_SCLK_RX_M0 | UART0_TX_M2 | GPIO4_A3_d
35 | NC | -
36 | HP_DET_L | R38 | I2C3_SDA_M0 | UART3_RX_M0 | SPI4_MISO_M0 | GPIO1_C0_z
37 | GND | -
38 | GPIO4_A4 | AW19 | CIF_D4 | BT1120_D4 | I2S1_LRCK_RX_M0 | I2C3_SCL_M2 | UART0_RX_M2 | SPI2_MISO_M1 | GPIO4_A4_d
39 | PCIE20_2_REFCLKP | F41 | PCIE20_2_REFCLKP
40 | GPIO4_A5 | AU15 | CIF_D5 | BT1120_D5 | I2S1_SDI0_M0 | I2C3_SDA_M2 | UART3_TX_M2 | SPI2_MOSI_M1 | GPIO4_A5_d
41 | PCIE20_2_REFCLKN | F42 | PCIE20_2_REFCLKN
42 | GND | -
43 | GND | -
44 | GPIO1_D0 | U37 | I2S0_SDO1 | I2C7_SCL_M0 | UART6_TX_M2 | SPI1_MISO_M2 | GPIO1_D0_d
45 | USB20_HOST1_DP | AV7 | USB20_HOST1_DP
46 | GPIO1_D1 | U38 | I2S0_SDO2 | I2S0_SDI3 | PDM0_SDI1_M0 | I2C7_SDA_M0 | UART6_RX_M2 | SPI1_MOSI_M2 | GPIO1_D1_d
47 | USB20_HOST1_DM | AW7 | USB20_HOST1_DM
48 | GND | -
49 | GND | -
50 | NC | -
51 | USB30_2_SSTXP | E41 | PCIE20_2_TXP | SATA30_2_TXP | USB30_SSTXP
52 | NC | -
53 | USB30_2_SSTXN | D41 | PCIE20_2_TXN | SATA30_2_TXN | USB30_SSTXN
54 | NC | -
55 | GND | -
56 | GND | -
57 | USB30_2_SSRXP | D42 | PCIE20_2_RXP | SATA30_2_RXP | USB30_SSRXP
58 | NC | -
59 | USB30_2_SSRXN | C42 | PCIE20_2_RXN | SATA30_2_RXN | USB30_SSRXN
60 | NC | -
61 | GND | -
62 | GND | -
63 | USB20_HOST0_DP | AW6 | USB20_HOST0_DP
64 | NC | -
65 | USB20_HOST0_DM | AV6 | USB20_HOST0_DM
66 | NC | -
67 | GND | -
68 | GND | -
69 | I2C6_SDA_M3 | AW27 | CIF_CLKIN | BT1120_CLKOUT | I2S1_SDI3_M0 | I2C6_SDA_M3 | UART8_TX_M0 | SPI2_CS1_M1 | GPIO4_B0_d
70 | NC | -
71 | I2C6_SCL_M3 | AU22 | MIPI_CAMERA0_CLK_M0 | SPDIF1_TX_M1 | I2S1_SDO0_M0 | SATA2_ACT_LED_M0 | I2C6_SCL_M3 | UART8_RX_M0 | SPI0_CS1_M1 | GPIO4_B1_u
72 | GND | -
73 | GND | -
74 | SDMMC_DET_L | AC38 | SDMMC_DET | GPIO0_A4_u |  |  |  |  |  |  |  |  | SDMMC_DET_L needs to be pulled down by default if booting from microSD is required
75 | GPIO1_C6_S | M41 | I2S0_LRCK_RX | PDM0_CLK0_M0 | I2C4_SDA_M4 | PWM15_IR_M2 | GPIO1_C6_d
76 | GND | -
77 | GPIO1_D5_S | P38 | PDM0_SDI0_M0 | SPI1_CS1_M2 | GPIO1_D5_d
78 | NC | -
79 | GPIO1_C4_S | U35 | I2S0_SCLK_RX | PDM0_CLK1_M0 | I2C2_SDA_M3 | PWM11_IR_M2 | SPI4_CS1_M0 | GPIO1_C4_d
80 | NC | -
81 | RTC_INT_L | AC37 | SPI2_CS1_M2 | I2C1_SCL_M1 | UART0_RX_M1 | GPIO0_B0_z
82 | NC | -
83 | GPIO1_D2 | P40 | I2S0_SDO3 | I2S0_SDI2 | PDM0_SDI2_M0 | I2C1_SCL_M4 | UART4_TX_M0 | PWM0_M1 | SPI1_CLK_M2 | GPIO1_D2_d
84 | NC | -
85 | BT_HOST_WAKE | AU23 | BT1120_D11 | UART9_RX_M1 | PWM12_M1 | SPI3_MISO_M1 | GPIO4_B5_d
86 | NC | -
87 | GPIO4_A7 | AW26 | CIF_D7 | BT1120_D7 | I2S1_SDI2_M0 | I2C5_SDA_M2 | SPI2_CS0_M1 | GPIO4_A7_d
88 | NC | -
89 | GPIO4_A6 | AV18 | CIF_D6 | BT1120_D6 | I2S1_SDI1_M0 | I2C5_SCL_M2 | UART3_RX_M2 | SPI2_CLK_M1 | GPIO4_A6_d
90 | NC | - |  |  |  |  |  |  |  |  |  |  | This GPIO port is already in use.
91 | NC | -
92 | VCC_3V3_S3 | -
93 | GPIO0_C2 | AG36 | PMIC_SLEEP4 | GPIO0_C2_d
94 | GPIO0_D3 | AG37 | LITCPU_AVS | SPI3_CLK_M2 | GPIO0_D3_u
95 | TYPEC5V_PWREN_H | AM39 | I2S1_SDO3_M1 | CPU_BIG1_AVS | I2C1_SDA_M2 | CAN2_TX_M1 | HDMI_TX0_SCL_M1 | SPI3_CS1_M2 | SATA_MP_SWITCH | GPIO0_D5_u
96 | CC_INT0_L | AL38 | I2S1_LRCK_RX_M1 | PDM0_CLK1_M1 | PWM2_M0 | UART0_RX_M0 | I2C4_SDA_M2 | DP0_HPDIN_M1 | GPIO0_C4_d
97 | TYPEC0_OTG_VBUSDET | AV10 | TYPEC0_USB20_VBUSDET
98 | BT_REG_ON_H | AL39 | I2S1_SDO2_M1 | PDM0_SDI2_M1 | PWM3_IR_M0 | I2C1_SCL_M2 | CAN2_RX_M1 | HDMI_TX0_SDA_M1 | SPI3_CS0_M2 | SATA_CPDET | GPIO0_D4_u
99 | GND | -
100 | GND | -
