omaralabed/Radxa-CM5-PCB/cad/im2300-top-panel-layout-rev-l.png

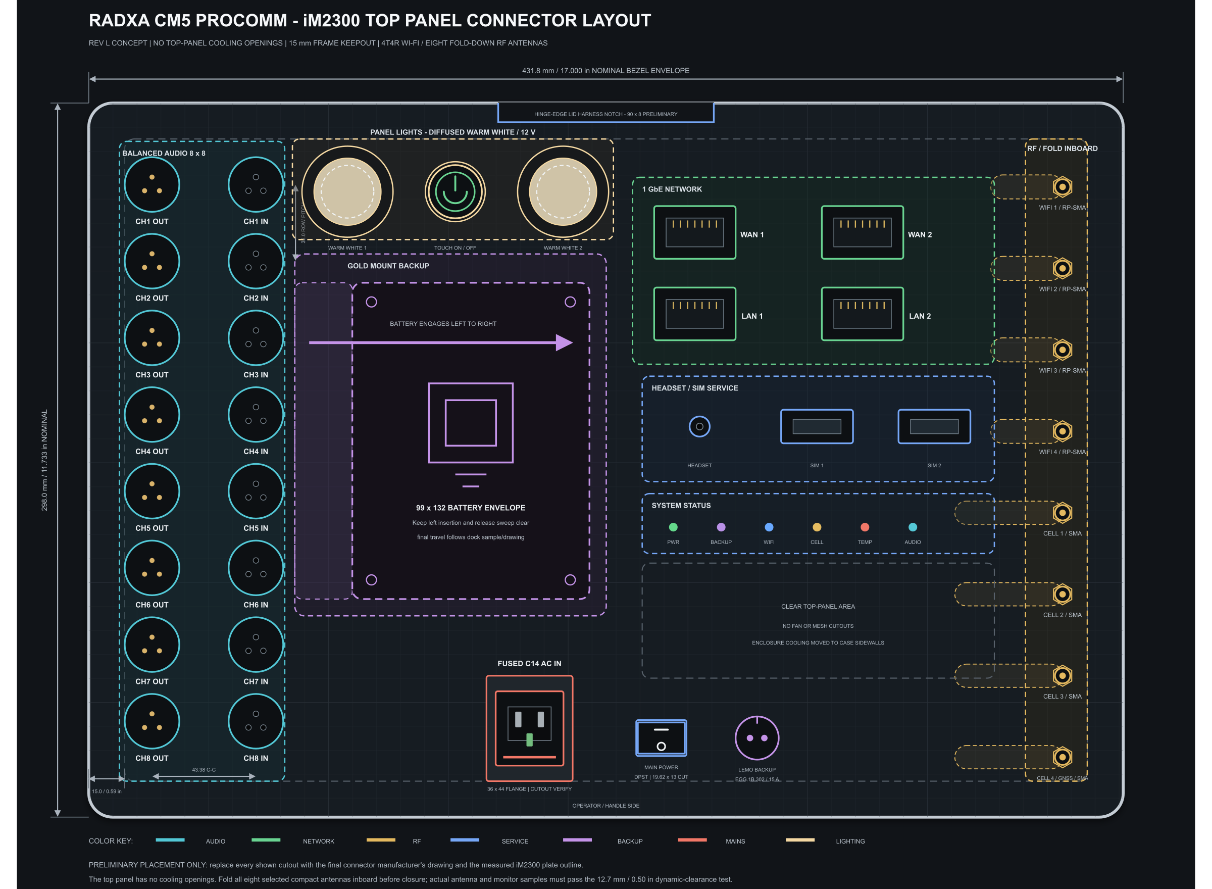
cad/im2300-top-panel-layout-rev-l.png
