omaralabed/Radxa-CM5-PCB/cad/kicad/AUDIO-8X8/REVIEW/rendered/Audio-8x8.png

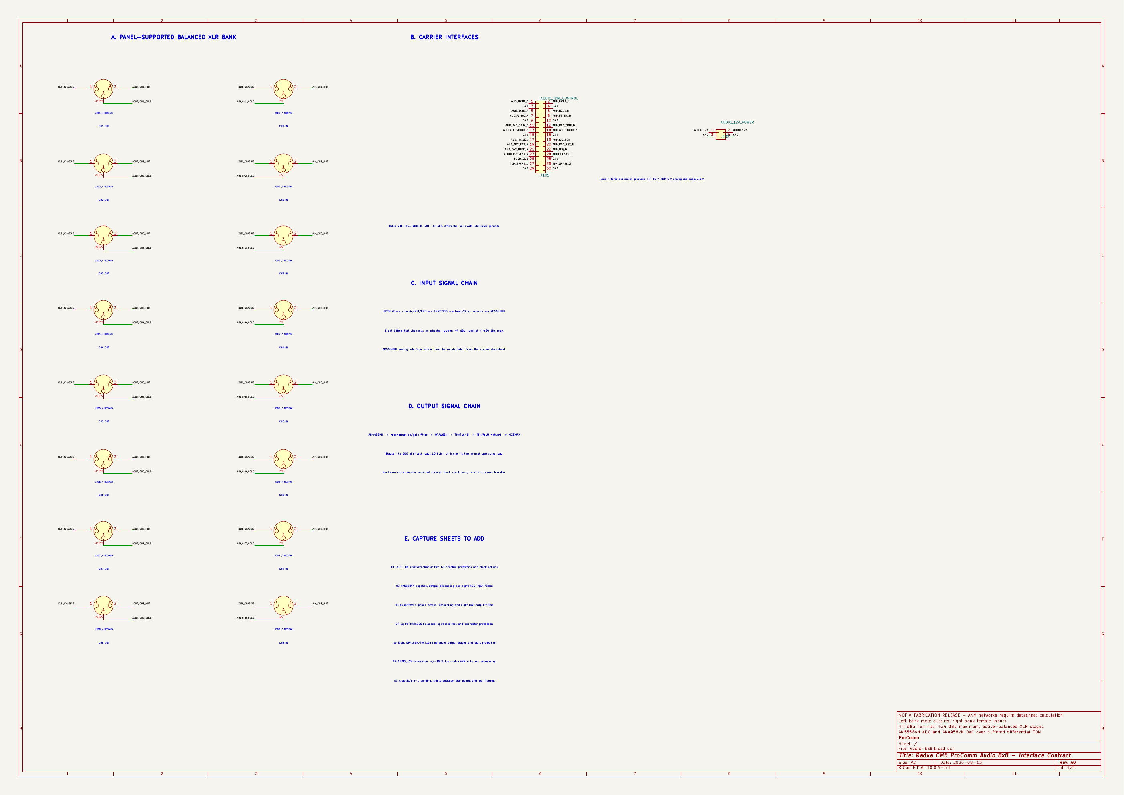
cad/kicad/AUDIO-8X8/REVIEW/rendered/Audio-8x8.png
