omaralabed/Radxa-CM5-PCB/cad/kicad/CM5-CARRIER/REVIEW/rendered/CM5-Carrier.png

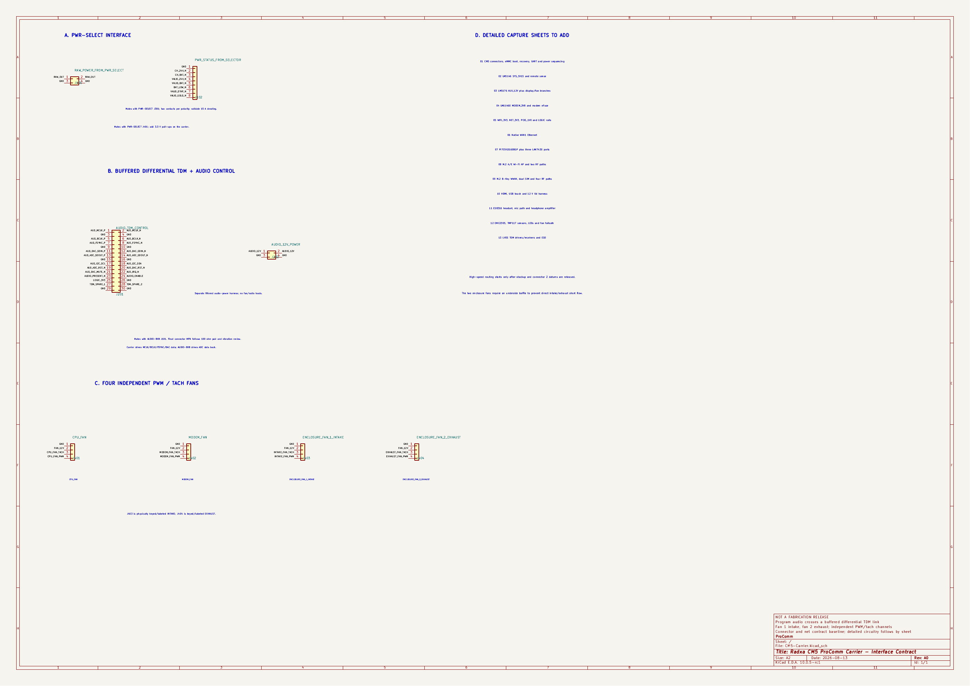
cad/kicad/CM5-CARRIER/REVIEW/rendered/CM5-Carrier.png
