omaralabed/Radxa-CM5-PCB/cad/kicad/CM5-CARRIER/REVIEW/rendered/Power-Regulators-A1.png

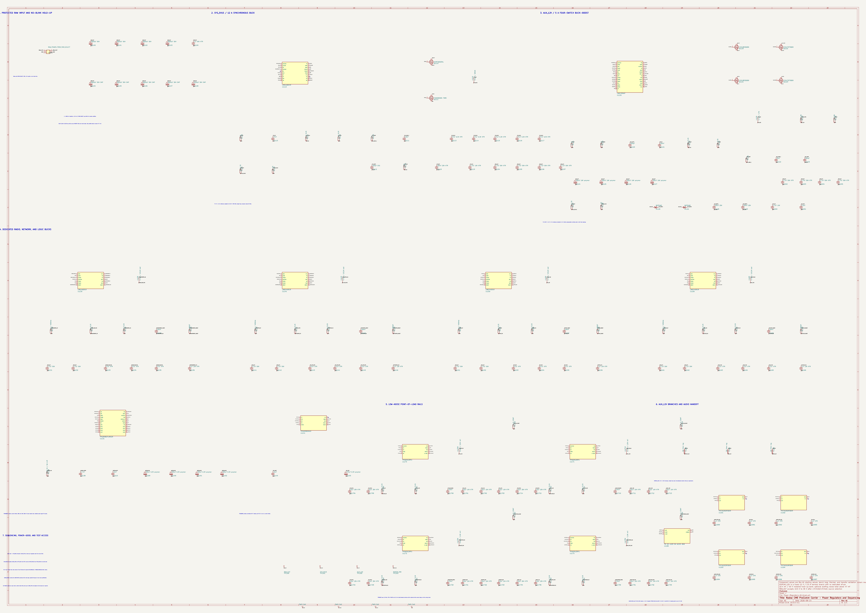
cad/kicad/CM5-CARRIER/REVIEW/rendered/Power-Regulators-A1.png
