omaralabed/Radxa-CM5-PCB/cad/kicad/PCB-REVIEW/3D/Audio-8x8-PCB-A1-bottom.png

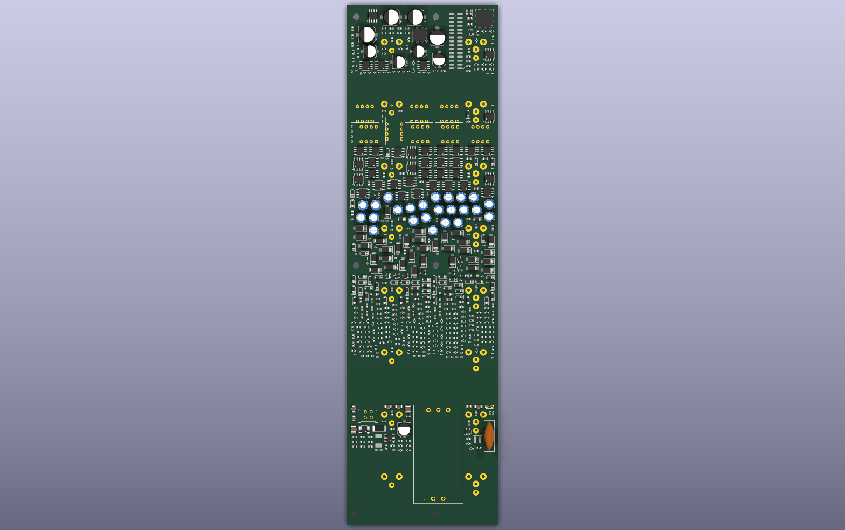
cad/kicad/PCB-REVIEW/3D/Audio-8x8-PCB-A1-bottom.png
