omaralabed/Radxa-CM5-PCB/cad/kicad/PCB-REVIEW/3D/PowerSelector-PCB-A1-bottom.png

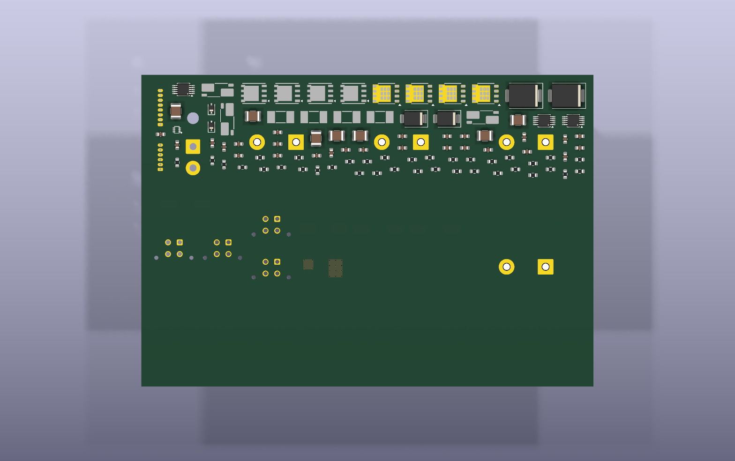
cad/kicad/PCB-REVIEW/3D/PowerSelector-PCB-A1-bottom.png
