omaralabed/Radxa-CM5-PCB/cad/kicad/PCB-REVIEW/3D/Sim-Service-PCB-A1-bottom.png

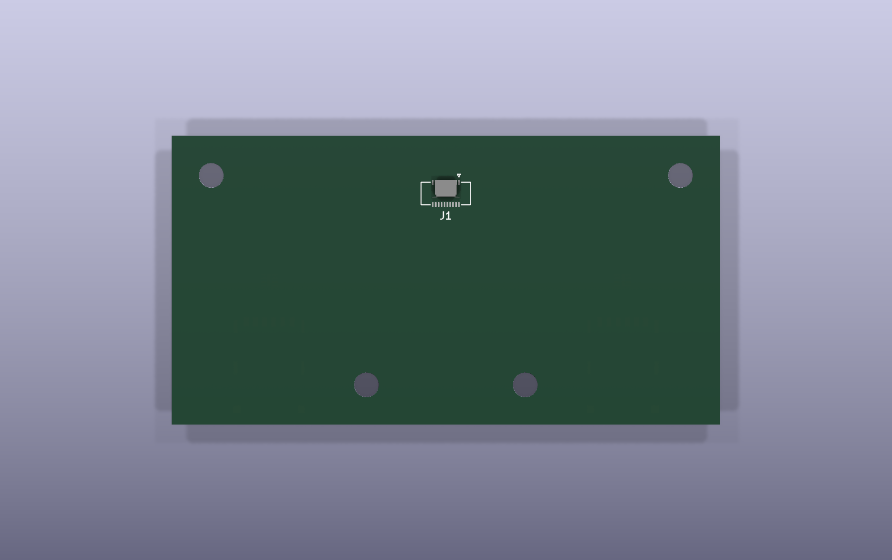
cad/kicad/PCB-REVIEW/3D/Sim-Service-PCB-A1-bottom.png
