omaralabed/Radxa-CM5-PCB/cad/kicad/PCB-REVIEW/3D/Sim-Service-PCB-A1-top.png

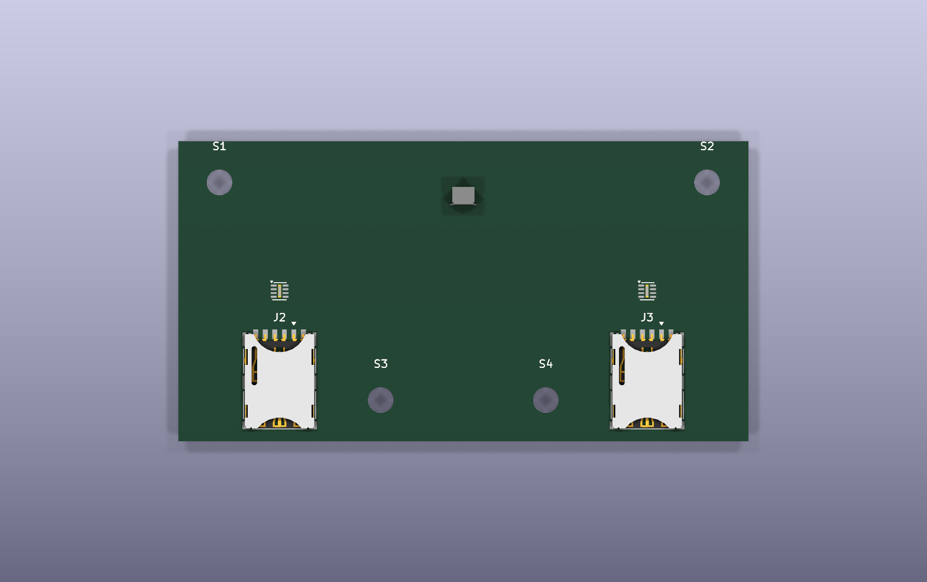
cad/kicad/PCB-REVIEW/3D/Sim-Service-PCB-A1-top.png
