omaralabed/Radxa-CM5-PCB/cad/kicad/PWR-SELECT/REVIEW/rendered/PowerSelector-A0.png

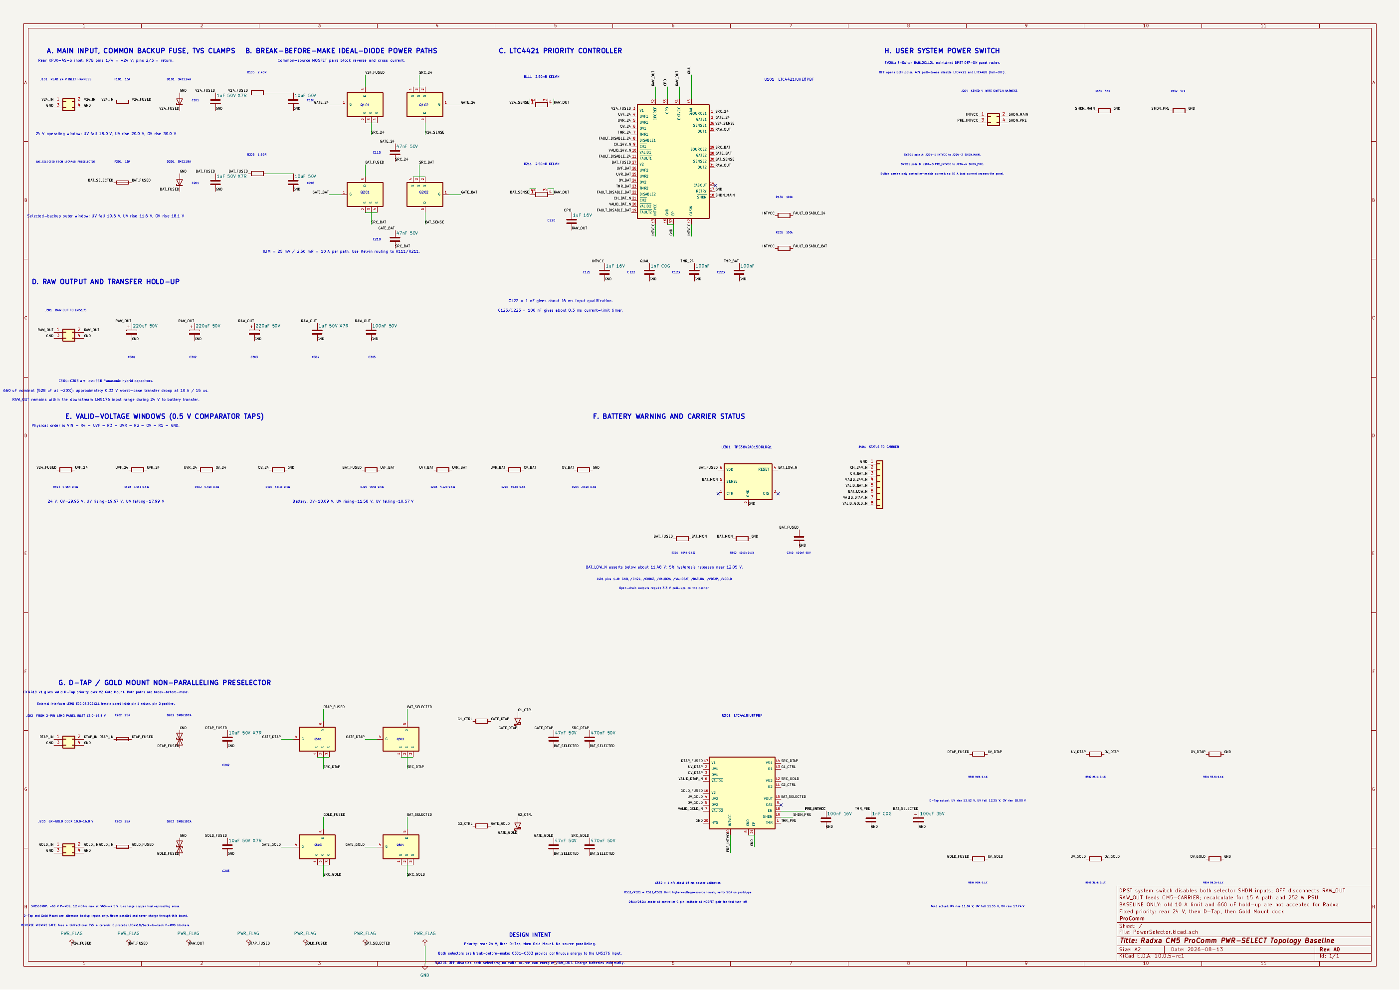
cad/kicad/PWR-SELECT/REVIEW/rendered/PowerSelector-A0.png
