omaralabed/Radxa-CM5-PCB/cad/mechanical/im2300-underside-pcb-floorplan-rev-l.png

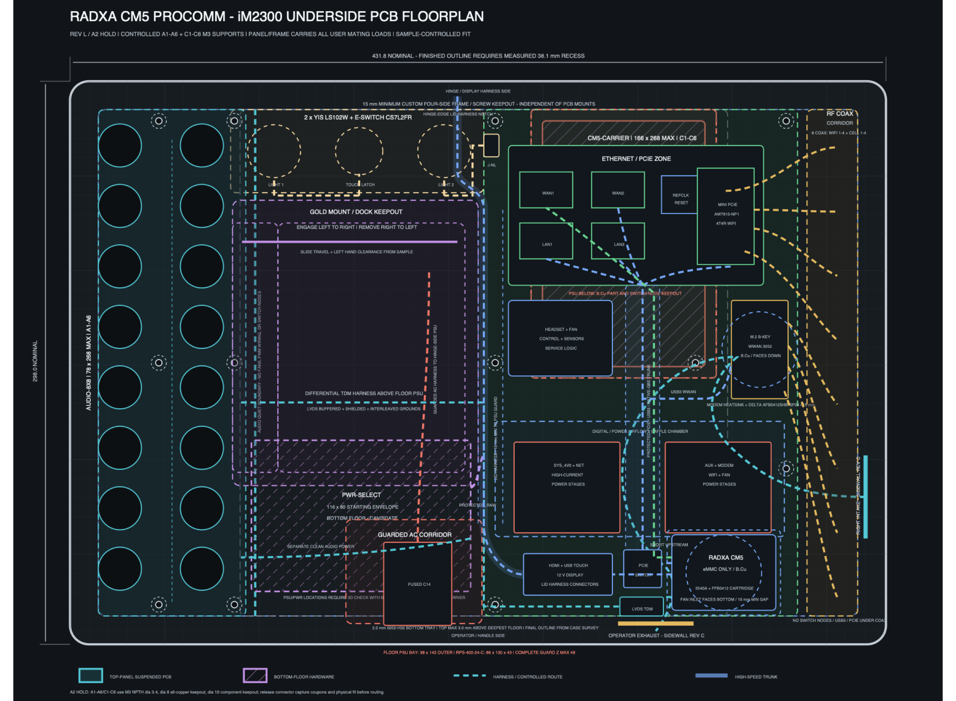
cad/mechanical/im2300-underside-pcb-floorplan-rev-l.png
