omaralabed/Radxa-CM5-PCB/cad/mechanical/pcb-and-connector-support-detail-rev-a.png

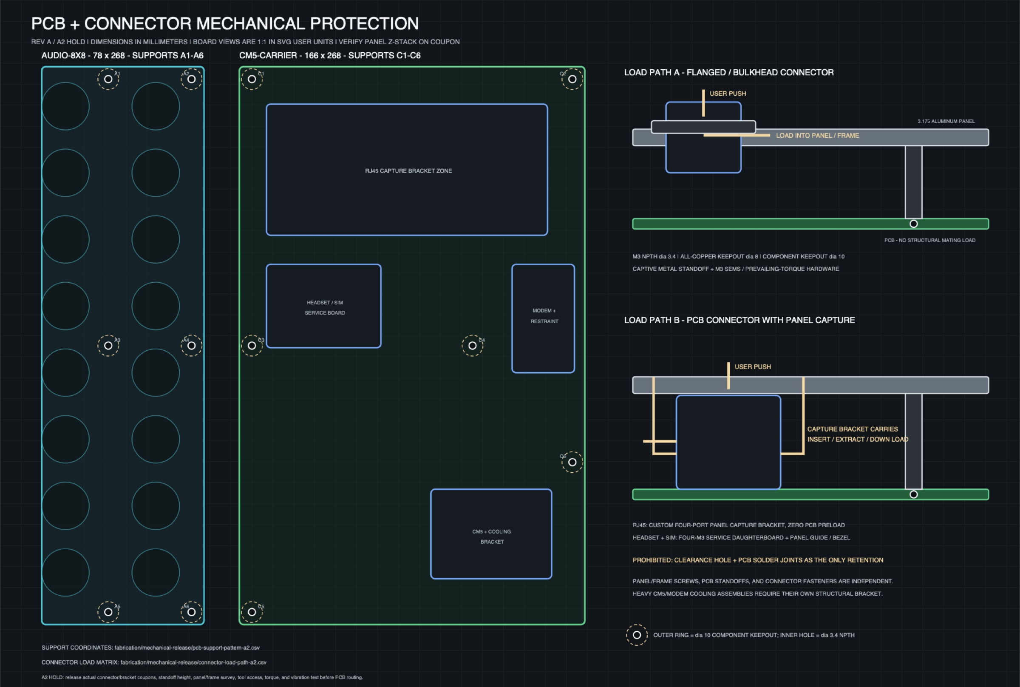
cad/mechanical/pcb-and-connector-support-detail-rev-a.png
