omaralabed/Radxa-CM5-PCB/cad/mechanical/sim-service-daughterboard-stack-rev-b.png

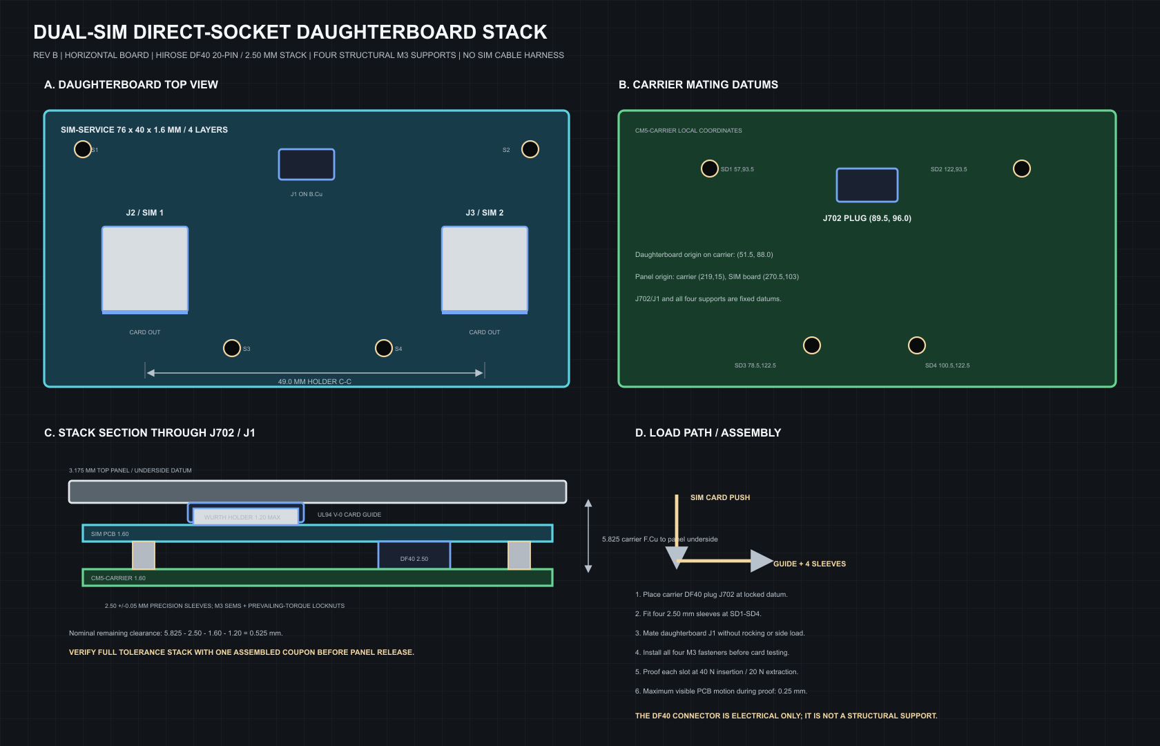
cad/mechanical/sim-service-daughterboard-stack-rev-b.png
