omaralabed/Radxa-CM5-PCB/outputs/cm5-pin-allocation-a0/previews/control-allocation.png

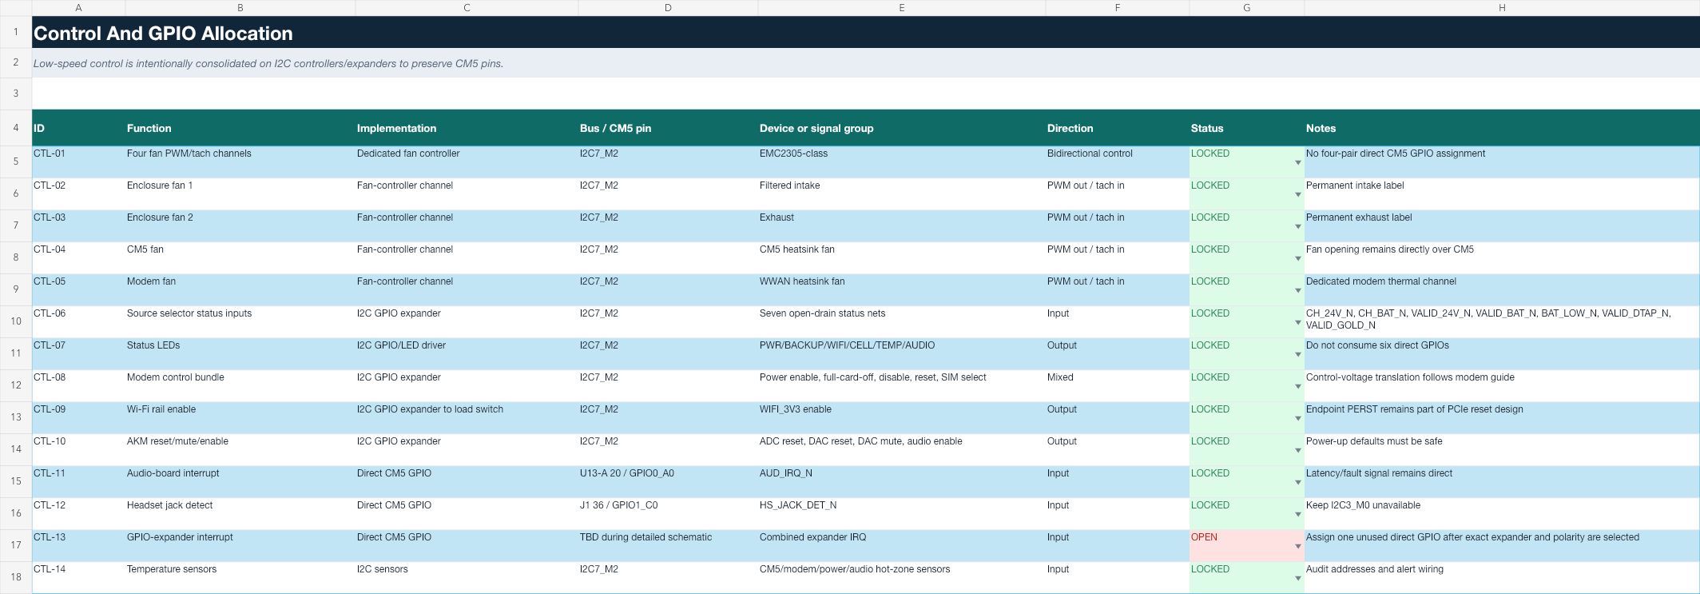
outputs/cm5-pin-allocation-a0/previews/control-allocation.png
