omaralabed/Radxa-CM5-PCB/outputs/cm5-pin-allocation-a0/previews/resource-map.png

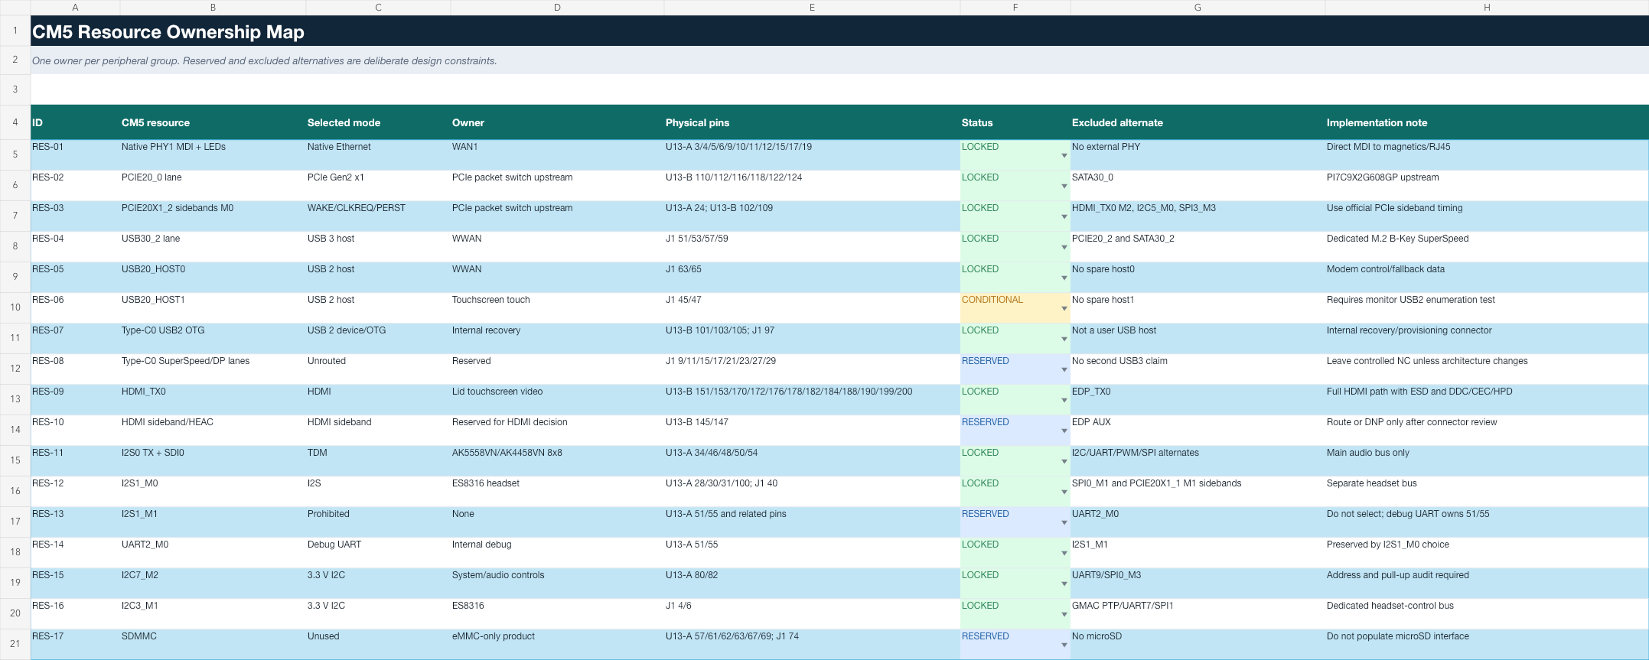
outputs/cm5-pin-allocation-a0/previews/resource-map.png
