omaralabed/Radxa-CM5-PCB/outputs/cm5-pin-allocation-a0/previews/summary.png

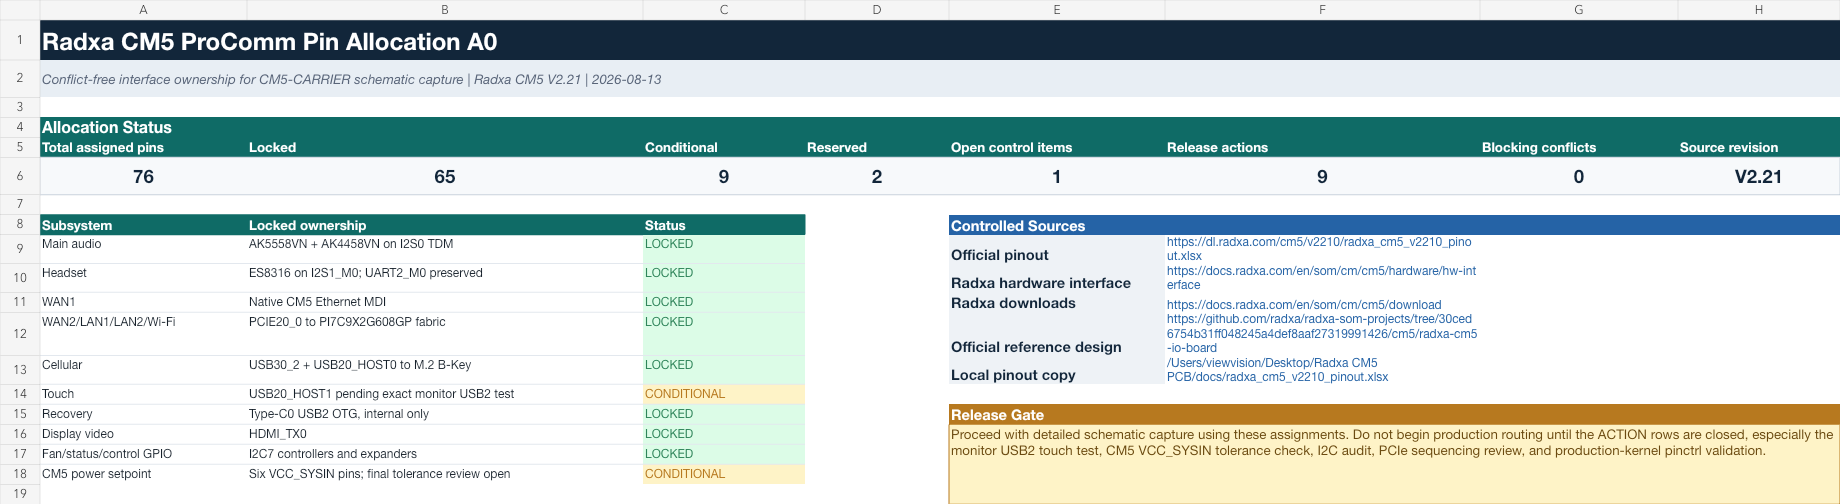
outputs/cm5-pin-allocation-a0/previews/summary.png
