omaralabed/Radxa-CM5-PCB/references/procomm-field-unit/procomm_field_unit-2.png

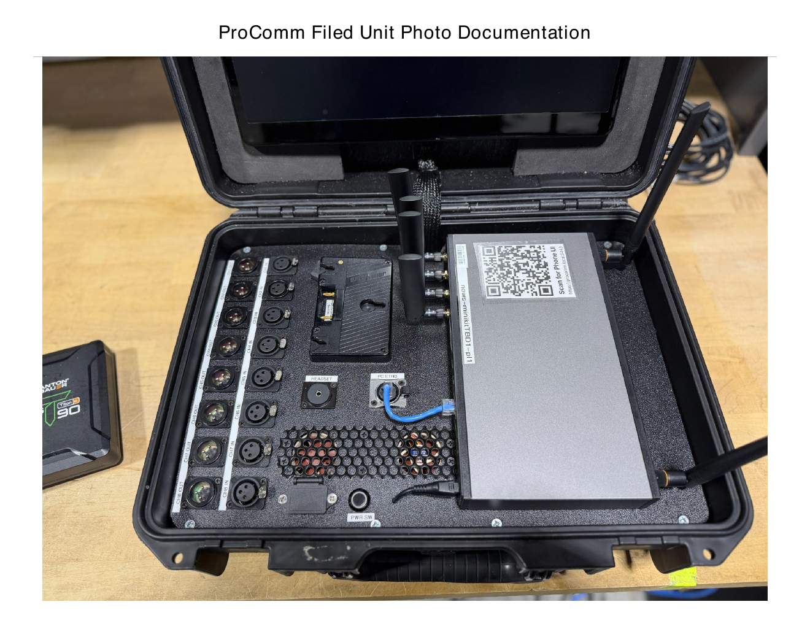
references/procomm-field-unit/procomm_field_unit-2.png
