omaralabed/Radxa-CM5-PCB/references/procomm-field-unit/procomm_field_unit-3.png

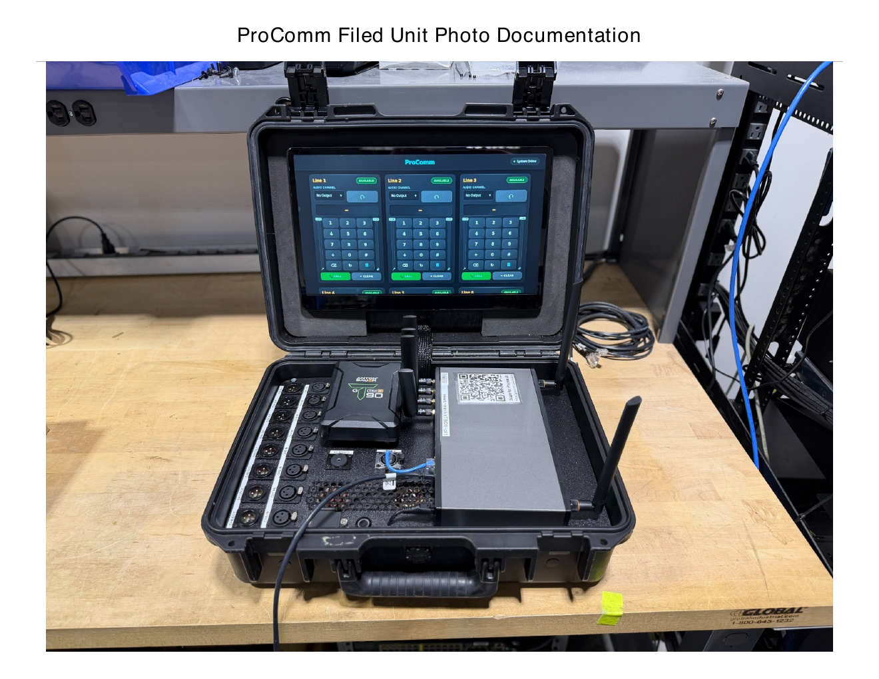
references/procomm-field-unit/procomm_field_unit-3.png
