omaralabed/Radxa-CM5-PCB/references/procomm-field-unit/procomm_field_unit-5.png

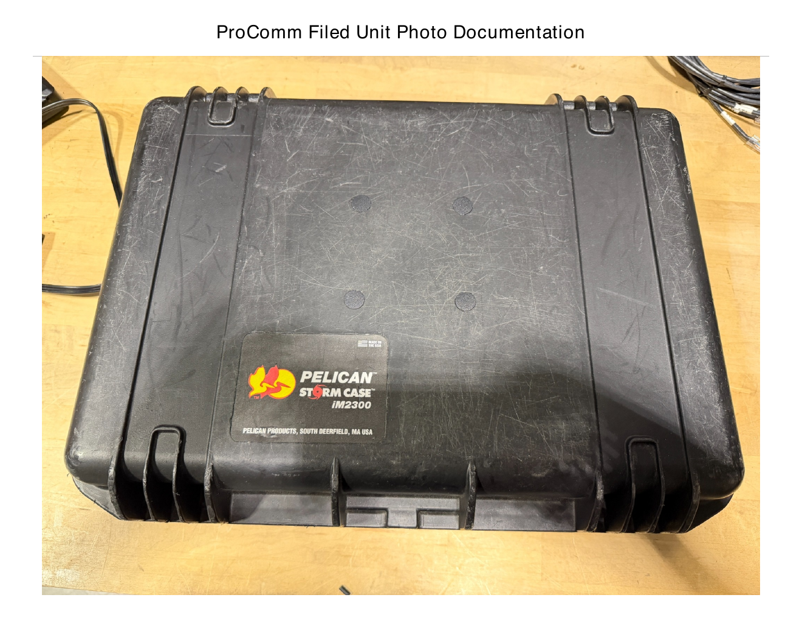
references/procomm-field-unit/procomm_field_unit-5.png
