omaralabed/Radxa-CM5-PCB/references/procomm-field-unit/procomm_field_unit-6.png

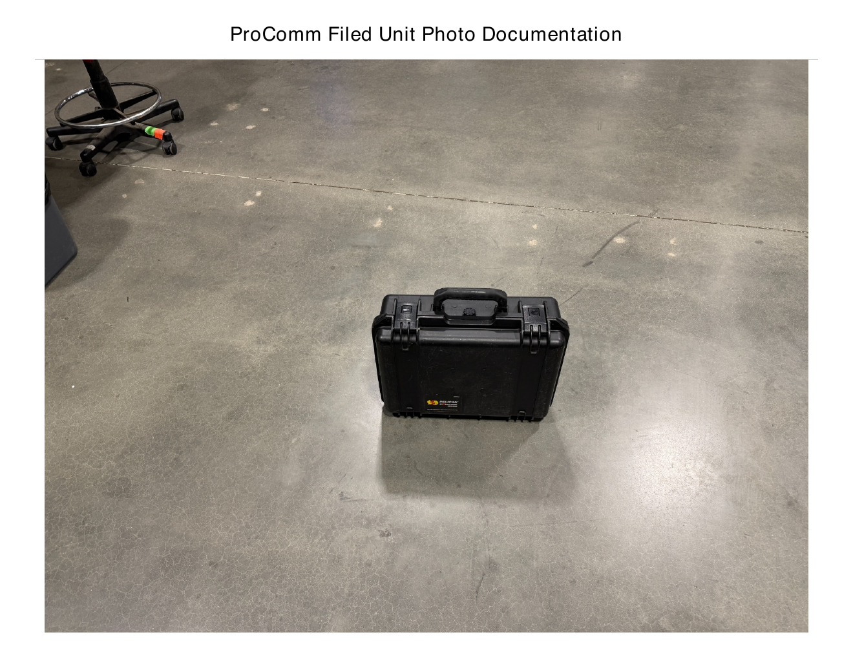
references/procomm-field-unit/procomm_field_unit-6.png
