omaralabed/Radxa-CM5-PCB/references/components/bel/V8BR-1AX1-GH/README.md

# Bel V8BR-1AX1-GH controlled reference

- Manufacturer part: Bel `V8BR-1AX1-GH`
- Function: vertical, through-hole, 1000BASE-T MagJack with G/Y LEDs
- Official drawing: <https://www.belfuse.com/media/drawings/products/magjack%20ICMs/dr-MAG-V8BR-1AX1-GH.pdf>
- Product page: <https://www.belfuse.com/products/ethernet/magjacks-icms/v8br-1ax1-gh>
- Cross-check source: LCSC `C5346729` EasyEDA record

`Bel_V8BR_1AX1_GH.kicad_mod` preserves the official drawing's 22 plated
holes and two 3.25 mm locating holes. The copied EasyEDA source is retained
for traceability. `Bel_V8BR_1AX1_GH.step` is a controlled outer-envelope model
generated from the official 18.19 x 20.65 x 17.02 mm dimensions. Its top
cavity communicates orientation; it is not a substitute for the supplier's
detailed internal model or the land pattern.
