omaralabed/Radxa-CM5-PCB/references/components/hirose/DF40C-100DS-0.4V/README.md

# Hirose DF40C-100DS-0.4V(51)

Controlled manufacturer evidence for all three Radxa CM5 mating connectors.

- Part: `DF40C-100DS-0.4V(51)`
- Hirose CL number: `CL0684-4033-4-51`
- Drawing: `DF40C-100DS-0.4V-51_2D_drawing.pdf`
- Drawing number: `EDC3-311352-00`
- Drawing revision/date shown: July 1, 2026
- SHA-256: `30b4c54ab38ddd18a65e1f3b631b8bcfb64efd1799c2a4a10936f010070521cd`
- Source: <https://www.hirose.com/en/product/p/CL0684-4033-4-51>

The Radxa IO V2.20 PADS board remains authoritative for the installed module
mating coordinates and its 1.14 x 0.20 mm production lands. The Hirose drawing
independently confirms the 100-position receptacle, 0.40 mm contact pitch, and
the land orientation. KiCad 10.0.5's PADS importer retains J24's 270-degree
component placement on each already-localized child pad; the project generator
removes only that double-applied angle and validates the result.
