omaralabed/Radxa-CM5-PCB/docs/radio_module_bom_a1.csv

Reference | Description | Manufacturer | MPN | Qty | Interface | Supply | Status | Source
WIFI-MOD-1 | Wi-Fi 6 4T4R full-size Mini PCIe AP module | AsiaRF | AW7915-NP1 | 1 | PCIe 2.1 Mini PCIe | 3.3 V +/-5% 3 A recommended | LOCKED-QUALIFICATION-REQUIRED | https://asiarf.com/product/wifi-6-11ax-4t4r-mini-pcie-module-mt7915-aw7915-np1/
