omaralabed/Radxa-CM5-PCB/fabrication/harnesses/H01-PSU-24V-BOM.csv

Reference | Assembly | Manufacturer | MPN | Qty | Description | Distributor | Distributor_PN | URL | Status | Notes
J101 | PWR-SELECT PCB | Molex | 76825-0002 | 1 | Mega-Fit 2-circuit dual-row right-angle through-hole header; tin; keyed and latched | Molex |  | https://www.molex.com/en-us/products/part-detail/768250002 | SELECTED | Pin 1 V24_IN; pin 2 GND; exact KiCad library footprint
P101 | H01 harness | Molex | 171692-0202 | 1 | Mega-Fit 2-circuit tangless TPA-capable receptacle housing | DigiKey | 900-1716920202-ND | https://www.digikey.com/en/products/detail/molex/1716920202/10481958 | SELECTED | Mates with J101
TPA101 | H01 harness | Molex | 105415-0002 | 1 | Mega-Fit 2-circuit terminal-position-assurance retainer | DigiKey | 900-1054150002-ND | https://www.digikey.com/en/products/detail/molex/1054150002/10482367 | SELECTED | Install after both contact latches pass tug check
C101A-C101B | H01 harness | Molex | 76823-0344 | 2 | Mega-Fit tangless female crimp contact; tin; single 14-16 AWG | DigiKey |  | https://www.molex.com/en-us/products/part-detail/0768230344 | SELECTED | One contact per polarity
RT101-RT102 | H01 harness | TE Connectivity | 320619 | 2 | PIDG insulated closed ring; 16-14 AWG; #6/M3.5 stud | DigiKey | A1070-ND | https://www.digikey.com/en/products/detail/te-connectivity-amp-connectors/320619/20591 | SELECTED | One each on PSU CN3 +V and CN2 -V
W101-W102 | H01 harness | Harness supplier | UL1015-14AWG | 2 | 14 AWG stranded copper hook-up wire; UL1015 or equivalent; 600 V; 105 C; red and black | Qualified supplier |  | MECH_SPEC | CONTROLLED_SPEC | 750 +/- 20 mm prototype finished length; release after 300 mm lift / 45 degree tilt test
SL101 | H01 harness | Harness supplier | PET-SLEEVE-6MM | 1 | Abrasion-resistant black PET sleeve sized for two 14 AWG conductors | Qualified supplier |  | MECH_SPEC | CONTROLLED_SPEC | Keep clear of PSU airflow and guarded AC zone
ID101-ID103 | H01 harness | Harness supplier | HEATSHRINK-ID | 3 | Permanent heat-shrink identification labels rated 105 C minimum | Qualified supplier |  | MECH_SPEC | CONTROLLED_SPEC | H01/J101 label plus CN2 and CN3 labels
