omaralabed/Radxa-CM5-PCB/references/radxa-cm-projects/cm5/radxa-cm5-io-board/radxa_cm5_io_board_v2200_BOM.xlsx

BOM层级 | 子项物料编码 | 物料名称 | 规格型号 | 子项类型 | 标准用量 | 位置号 | 原厂料号 | 品牌 | 原厂料号2 | 品牌2
0 | HHH01.00135 | 机板 | RC122 V2.2 CM5 IO RC122-V2.2 |  | 1
.1 | A1J11.00007 | DC座 | DIP 5PIN DS-044BS 内孔Φ6mm 铁芯Φ2.0mm 11.6*10.2*7.3mm ROHS | 标准件 | 1 | U37 | DS-044BS | 协佳
.1 | A1J01.00014 | 排座 | DIP 排针座 1*4PIN 180度 无定位柱 2.54mm脚距 针长一端8.3mm 另一端3.5mm 小4PIN 白色 M2545V-4P 兴飞 ROHS | 标准件 | 1 | U28 | M2545V-4P | 兴飞
.1 | A1J02.00013 | 排座 | DIP 排针座 1*3PIN 180度 2.54mm脚距 中间朔高2.5mm 针长一端6.1mm 另一端3mm 黑色 PH2.54 1*3P L=11.6/3.0 ROHS | 标准件 | 2 | U32,U90134 | PH2.54 1*3P L=11.6/3.0 | 国意英
.1 | A1J01.00012 | 排座 | DIP 排针座 2*20PIN 180度 2.54mm脚距 中间朔高2.5mm 针长一端6.1mm 另一端3mm 彩色 PH2.54 2*20P 彩印 L=11.6/3.0 ROHS | 标准件 | 1 | CON1 | PH2.54 2*20P 彩印 L=11.6/3.0 | 国意英
.1 | A1J03.00002 | RJ45座 | DIP母座 千兆网 带POE功能 18PIN 21.5*16*13.7MM LPJG0926HENL 镀镍 带指示灯 无弹片 左绿右黄 ROHS | 标准件 | 1 | J3 | LPJG0926HENL | LP
.1 | A1J01.00011 | 排座 | DIP 排针座 2*2PIN 180度 2.54mm脚距 中间朔高2.5mm 针长一端6.1mm 另一端3mm 黑色 PH2.54 2*02P L=11.6/3.0 S/T ROHS | 标准件 | 1 | J4 | PH2.54 2*02P L=11.6/3.0 S/T | 国意英
.1 | A1J02.00011 | 排座 | DIP 排针座 1*2PIN 180度 2.54mm脚距 中间朔高2.5mm 针长一端6.1mm 另一端3mm 黑色 PH2.54 1*2P L=11.6/3.0 ROHS | 标准件 | 1 | J10 | PH2.54 1*2P L=11.6/3.0 | 国意英
.1 | A1J02.00005 | USB2.0母座 | DIP 双层 卷边无定位柱 90度弯脚 黑色胶芯 17.5*14.4*H15.6mm 弯脚固定间距15.6mm 铜壳 ROHS | 标准件 | 1 | J8203 | XJ-DR-USB2.0AF90-02 | 协佳电子
.1 | TPT01.00194 | PCBA | RC122 V2.2 CM5 IO RC122-V2.2 | 标准件 | 1
..2 | A1P01.00282 | PCB板 | RC122 CM5 IO V2.2 90*160.1*H1.6mm FR-4 4层通孔板 沉金1U"+OSP 绿色油 白色丝印 ROHS | 标准件 | 1
..2 | A1R01.00001 | 贴片电阻 | SMD 0201 0R 1/20W ±1% ROHS | 标准件 | 19 | R715,R814,R95469,R95470,R95471,R95472,R95580,R2013,R2015,R2016,R2017,R9241,R90341,R91181,R91182,R95071,R95467,R95573,R95586 | 0201WMF0000TEE | UNI-ROYAL(厚声)
..2 | A1R01.00024 | 贴片电阻 | SMD 0201 22R 1/20W ±5% ROHS | 标准件 | 7 | R95143,R95147,R95148,R95149,R95150,R95152,R95583 | RC-01W220JT | FH
..2 | A1R01.00148 | 贴片电阻 | SMD 0201 4.7K 1/20W ±1% ROHS | 标准件 | 1 | R95556 | RC-01W4701FT | FH
..2 | A1R01.00158 | 贴片电阻 | SMD 0201 6.8K 1/20W ±1% ROHS | 标准件 | 1 | R91193 | RC-01W6801FT | FH
..2 | A1R01.00086 | 贴片电阻 | SMD 0201 8.2K 1/20W ±1% ROHS | 标准件 | 1 | R95116 | RC-01W8201FT | FH
..2 | A1R01.00012 | 贴片电阻 | SMD 0201 10K 1/20W ±5% ROHS | 标准件 | 8 | R90338,R95042,R95044,R95151,R95153,R95154,R95239,R95558 | RTT01103JTH | RALEC | RC-01W103JT | FH
..2 | A1R01.00011 | 贴片电阻 | SMD 0201 12K 1/20W ±5% ROHS | 标准件 | 1 | R95043 | RC-01W123JT | FH
..2 | A1R01.00061 | 贴片电阻 | SMD 0201 47K 1/20W ±1% ROHS | 标准件 | 1 | R95120 | RC0201FR-0747KL | YAGEO | RTT014702FTH | RALEC
..2 | A1R01.00149 | 贴片电阻 | SMD 0201 51K 1/20W ±1% ROHS | 标准件 | 1 | R95210 | RC-01W5102FT | FH
..2 | A1R01.00006 | 贴片电阻 | SMD 0201 100K 1/20W ±5% ROHS | 标准件 | 6 | R2004,R2007,R95041,R95113,R95119,R95137 | RC-01W104JT | FH | RTT01104JTH | RALEC
..2 | A1R01.00094 | 贴片电阻 | SMD 0201 120K 1/20W ±1% ROHS | 标准件 | 3 | R95555,R95578,R95579 | RTT011203FTH | RALEC
..2 | A1R01.00189 | 贴片电阻 | SMD 0201 232K 1/20W ±1% ROHS | 标准件 | 1 | R95281 | RTT012323FTH | RALEC
..2 | A1R01.00196 | 贴片电阻 | SMD 0201 330K 1/20W ±5% ROHS | 标准件 | 1 | R90337 | RC-01W334JT | FH | RTT01334JTH | RALEC
..2 | A1R01.00089 | 贴片电阻 | SMD 0201 510K 1/20W ±5% ROHS | 标准件 | 2 | R95114,R95122 | RC-01W514JT | FH
..2 | A1R01.00114 | 贴片电阻 | SMD 0201 2M 1/20W ±5% ROHS | 标准件 | 2 | R2005,R2006 | RTT01205JTH | RALEC
..2 | A1R01.00030 | 贴片电阻 | SMD 0402 0R 1/16W ±5% ROHS | 标准件 | 25 | R1,R5,R7,R120,R121,R153,R7120,R90334,R95155,R95377,R95468,R95530,R95541,R95557,R95570,R95571,R95589,R95599,R95602,R95609,R95612,R95613,R95282,R95616,R7125 | RC-02000JT | FH
..2 | A1R01.00049 | 贴片电阻 | SMD 0402 3.3R 1/16W ±5% ROHS | 标准件 | 2 | R147,R95115 | RHC-02U3R3JT | FH
..2 | A1R01.00063 | 贴片电阻 | SMD 0402 2.2R 1/16W ±5% ROHS | 标准件 | 4 | R91188,R91189,R95551,R95552 | RTT012R2JTH | RALEC
..2 | A1R01.00002 | 贴片电阻 | SMD 0402 22R 1/16W ±5% ROHS | 标准件 | 5 | R11,R95028,R95144,R95145,R95146 | RC-02W220JT | FH
..2 | A1R01.00033 | 贴片电阻 | SMD 0402 100R 1/16W ±5% ROHS | 标准件 | 7 | R167,R168,R95495,R95582,R95584,R95585,R95614 | RC-02K101JT | FH
..2 | A1R01.00066 | 贴片电阻 | SMD 0402 510R 1/16W ±5% ROHS | 标准件 | 2 | R3,R9 | RC-02K511JT | FH
..2 | A1R01.00067 | 贴片电阻 | SMD 0402 1K 1/16W ±5% ROHS | 标准件 | 2 | R91,R215 | RC-02K102JT | FH | 0402WGJ0102TCE | UNIOHM
..2 | A1R01.00409 | 贴片电阻 | SMD 0402 2.2K 1/16W ±1% ROHS | 标准件 | 5 | R95590,R95591,R95592,R95593,R7313 | 0402WGF2201TCE | UNI-ROYAL(厚声) | RC0402FR-072K2L | YAGEO(国巨)
..2 | A1R01.00238 | 贴片电阻 | SMD 0402 2.7K 1/16W ±1% ROHS | 标准件 | 1 | R102 | 0402WGF2701TCE | UNI-ROYAL
..2 | A1R01.00245 | 贴片电阻 | SMD 0402 3.9K 1/16W ±1% ROHS | 标准件 | 1 | R2322 | RC-02W3901FT | FH
..2 | A1R01.00051 | 贴片电阻 | SMD 0402 4.7K 1/16W ±5% ROHS | 标准件 | 3 | R2612,R2613,R95603 | 0402WGJ0472TCE | UNI-ROYAL
..2 | A1R01.00266 | 贴片电阻 | SMD 0402 8.2K 1/16W ±1% ROHS | 标准件 | 1 | R154 | RC-02W8201FT | FH
..2 | A1R01.00070 | 贴片电阻 | SMD 0402 5.1K 1/16W ±5% ROHS | 标准件 | 1 | R152 | RC-02W512JT | FH
..2 | A1R01.00034 | 贴片电阻 | SMD 0402 10K 1/16W ±5% ROHS | 标准件 | 8 | R94,R96,R149,R396,R2311,R7314,R7315,R95374 | RC-02W103JT | FH
..2 | A1R01.00046 | 贴片电阻 | SMD 0402 24K 1/16W ±5% ROHS | 标准件 | 1 | R160 | RC-02W243JT | FH
..2 | A1R01.00053 | 贴片电阻 | SMD 0402 47K 1/16W ±5% ROHS | 标准件 | 2 | R95375,R95615 | RTT02473JTH | RALEC
..2 | A1R01.00252 | 贴片电阻 | SMD 0402 51K 1/16W ±5% ROHS | 标准件 | 1 | R161 | RC-02K513JT | FH
..2 | A1R01.00031 | 贴片电阻 | SMD 0402 100K 1/16W ±1% ROHS | 标准件 | 8 | R105,R106,R156,R158,R2611,R4203,R151,R95606 | RTT021003FTH | RALEC | RC-02W1003FT | FH
..2 | A1R01.00289 | 贴片电阻 | SMD 0402 232K 1/16W ±1% ROHS | 标准件 | 1 | R157 | RC-02K2323FT | FH
..2 | A1R01.00058 | 贴片电阻 | SMD 0603 0R 1/10W ±5% ROHS | 标准件 | 3 | R220,R316,R95373 | RS-03000JT | FH | RTT03000JTP | RALEC
..2 | A1R01.00085 | 贴片电阻 | SMD 1206 0.1R 1/4W ±5% ROHS | 标准件 | 1 | R353 | RTT06R10JTP | RALEC
..2 | A1R01.00391 | 贴片电阻 | SMD 1206 1.1R 1/4W ±1% ROHS | 标准件 | 1 | R5004 | RS-06L1R10FT | FH
..2 | A1C01.00284 | 陶瓷电容 | SMD 0201 100PF 25V COG ±5% ROHS | 标准件 | 1 | C266 | 0201CG101J250NT | FH
..2 | A1C01.00096 | 陶瓷电容 | SMD 0201 10NF 25V X7R ±10% ROHS | 标准件 | 1 | C90084 | C0201X7R103K250NTA | EYANG
..2 | A1C01.00009 | 陶瓷电容 | SMD 0201 100NF 10V X5R ±20% ROHS | 标准件 | 4 | C549,C813,C90486,C90779 | CL03A104KP3NNNC | SAMSUNG | 0201X104K100NT | FH
..2 | A1C01.00018 | 陶瓷电容 | SMD 0201 100NF 16V X5R ±10% ROHS | 标准件 | 13 | C268,C269,C2010,C2011,C2013,C2014,C2019,C2020,C2280,C2281,C2284,C90392,C90393 | C0201X5R104K160NTA | EYANG | 0201X104K160NT | FH
..2 | A1C01.00082 | 陶瓷电容 | SMD 0201 220NF 16V X5R ±20% ROHS | 标准件 | 8 | C90420,C90421,C90422,C90423,C90424,C90425,C90426,C90427 | C0201X5R224M160NTJ | EYANG
..2 | A1C01.00020 | 陶瓷电容 | SMD 0201 1UF 16V X5R ±20% ROHS | 标准件 | 2 | C90429,C90430 | CL03A105MO3NRNH | SAMSUNG
..2 | A1C01.00174 | 陶瓷电容 | SMD 0201 1UF 10V X5R ±10% ROHS | 标准件 | 1 | C90482 | C0603X5R105KDTS | DARFON(达方)
..2 | A1C01.00170 | 陶瓷电容 | SMD 0402 12PF 50V COG ±5% ROHS | 标准件 | 1 | C90615 | GRM1555C1H120JA01D | muRata(村田)
..2 | A1C01.00030 | 陶瓷电容 | SMD 0402 22PF 50V NPO ±5% ROHS | 标准件 | 1 | C148 | 0402N220J500CT | Walsin(华新科) | CC0402JRNPO9BN220 | YAGEO(国巨)
..2 | A1C01.00211 | 陶瓷电容 | SMD 0402 56PF 50V NPO ±5% ROHS | 标准件 | 2 | C84,C85 | 0402N560J500CT | Walsin(华新科) | AC0402JRNPO9BN560 | YAGEO(国巨)
..2 | A1C01.00183 | 陶瓷电容 | SMD 0402 220PF 50V X7R ±10% ROHS | 标准件 | 2 | C2612,C2613 | UMK105B7221KVHF | TAIYO YUDEN
..2 | A1C01.00062 | 陶瓷电容 | SMD 0402 220NF 25V X5R ±10% ROHS | 标准件 | 1 | C90489 | CL05A224KA5NNNC | SAMSUNG
..2 | A1C01.00061 | 陶瓷电容 | SMD 0402 100NF 25V X5R ±20% ROHS | 标准件 | 3 | C133,C140,C152 | 0402X104M250NT | FH
..2 | A1C01.00031 | 陶瓷电容 | SMD 0402 4.7UF 16V X5R ±20% ROHS | 标准件 | 2 | C563,C574 | CL05A475MO5NUNC | SAMSUNG(三星)
..2 | A1C01.00161 | 陶瓷电容 | SMD 0402 10NF 25V X5R ±10% ROHS | 标准件 | 1 | C7322 | CC0402KRX5R8BB103 | YAGEO
..2 | A1C01.00001 | 陶瓷电容 | SMD 0402 100NF 16V X5R ±20% ROHS | 标准件 | 42 | C90483,C90488,C90790,C89,C3,C558,C90410,C90751,C90776,C90777,C5,C34,C87,C88,C126,C131,C135,C138,C139,C141,C145,C146,C150,C153,C560,C561,C570,C571,C573,C2606,C2609,C2611,C2614,C90617,C90618,C90772,C90782,C90783,C90784,C90787,C90788,C7320 | CL05A104MO5NNNC | SAMSUNG
..2 | A1C01.00048 | 陶瓷电容 | SMD 0402 220NF 16V X5R ±10% ROHS | 标准件 | 1 | C129 | 0402X224K160NT | FH
..2 | A1C01.00002 | 陶瓷电容 | SMD 0402 1UF 16V X5R ±20% ROHS | 标准件 | 6 | C1,C143,C144,C2608,C90773,C90789 | CL05A105MO5NNNC | SAMSUNG | CL05A105KO5NNNC | SAMSUNG
..2 | A1C01.00015 | 陶瓷电容 | SMD 0603 22UF 10V X5R ±20% ROHS | 标准件 | 4 | C83,C2282,C2283,C90774 | CL10A226MP8NUNE | SAMSUNG
..2 | A1C01.00239 | 陶瓷电容 | SMD 0603 4.7UF 16V X5R ±10% ROHS | 标准件 | 1 | C90408 | 0603X475K160CT | Walsin | GRM188R61C475KAAJD | muRata(村田)
..2 | A1C01.00261 | 陶瓷电容 | SMD 0603 1UF 50V X5R ±10% ROHS | 标准件 | 1 | C90409 | 0603X105K500NT | FH
..2 | A1C01.00228 | 陶瓷电容 | SMD 0603 22UF 16V X5R ±20% ROHS | 标准件 | 6 | C127,C130,C136,C137,C2607,C548 | GRM188R61C226ME01D | muRata
..2 | A1C01.00016 | 陶瓷电容 | SMD 0603 10UF 16V X5R ±20% ROHS | 标准件 | 15 | C4,C265,C267,C562,C564,C565,C568,C569,C572,C2335,C90431,C2330 ,C2332,C559,C90582 | CL10A106MO8NQNC | SAMSUNG
..2 | A1C01.00075 | 陶瓷电容 | SMD 0603 10UF 10V X5R ±20% ROHS | 标准件 | 4 | C812,C90750,C90775,C90778 | CL10A106MP8NNNC | SAMSUNG
..2 | A1C01.00005 | 陶瓷电容 | SMD 0805 10UF 25V X5R ±20% ROHS | 标准件 | 1 | C90781 | 0805X106M250NT | FH
..2 | A1C01.00248 | 陶瓷电容 | SMD 0805 22UF 10V X5R ±20% ROHS | 标准件 | 4 | C90478,C90479,C90485,C90490 | CL21A226MPQNNNE | SAMSUNG
..2 | A1C01.00053 | 陶瓷电容 | SMD 0805 22UF 16V X5R ±20% ROHS | 标准件 | 5 | C149,C154,C155,C156,C90780 | CL21A226MOQNNNE | SAMSUNG
..2 | A1C01.00249 | 陶瓷电容 | SMD 0805 22UF 25V X5R ±20% ROHS | 标准件 | 5 | C132,C134,C142,C151,C658 | CL21A226MAYNNNE | SAMSUNG
..2 | A1C01.00056 | 陶瓷电容 | SMD 1206 10UF 16V X5R ±10% ROHS | 标准件 | 1 | C147 | 1206X106K160NT | FH
..2 | A1C01.00065 | 陶瓷电容 | SMD 1206 10UF 25V X5R ±10% ROHS | 标准件 | 2 | C90480,C90484 | 1206X106K250NT | FH
..2 | A1D02.00001 | ESD管 | SMD 编带 DFN1006-2L ESD5311N-2/TR 双向TVS VRWM=5V 0.25pF 84W WILLSEMI(韦尔) ROHS | 标准件 | 16 | ED6,ED20,ED21,ED22,ESD2701,ESD2702,ESD2703,ESD2704,ESD2706,ESD27052,D90031,D90032,D90033,D90034,D90035,D90037 | ESD5311N-2/TR | WILLSEMI(韦尔)
..2 | A1D02.00002 | ESD管 | SMD 编带 0402 BTR04G02 B-tron ROHS | 标准件 | 6 | ED1,ED2,ED3,D3,D4,ED5 | BTR04G02 | B-tron
..2 | A1D02.00087 | ESD管 | SMD 编带 0402 MESD5V0UF12B 双向 5V 0.20pF 密勒半导体 ROHS | 标准件 | 9 | ED9,ED10,ED11,ED12,ED13,ED14,ED15,D48,D49 | MESD5V0UF12B | 密勒半导体
..2 | A1D02.00088 | ESD管 | SMD 编带 0402 MESD5V0SF11B 双向 5V 12pF 密勒半导体 ROHS | 标准件 | 8 | ED2109,ED2110,ED2111,ED4806,ED9203,ED9204,ED9205,ED7104 | MESD5V0SF11B | 密勒半导体
..2 | A1D02.00015 | ESD管 | SMD 编带 SON10 ESD73034D-10/TR 4Line 双向TVS VRWM=3.3V 0.2pF 33W WILLSEMI(韦尔) ROHS | 标准件 | 2 | U3806,U3807 | ESD73034D-10/TR | WILLSEMI(韦尔)
..2 | A1D02.00008 | ESD管 | SMD编带 DFN2510-10L ESD5344D ROHS | 标准件 | 2 | U5,U6 | ESD5344D | WILLSEMI(韦尔)
..2 | A1D02.00018 | ESD管 | SMD 编带 SON10 TPD4E05U06DQAR 4Line VRWM=5V 0.5pF 40W TI ROHS | 标准件 | 2 | U90040,U90127 | TPD4E05U06DQAR | TI
..2 | A1D01.00006 | MOS管 | SMD 编带 SOT23-3 WPM3407-3/TR P沟道 WILLSEMI(韦尔) ROHS | 标准件 | 1 | Q9514 | WPM3407-3/TR | WILLSEMI(韦尔)
..2 | A1D01.00010 | MOS管 | SMD编带 SOT23-3 AOS AO3416 N沟道 ROHS | 标准件 | 1 | Q15 | AO3416 | AOS
..2 | A1D02.00089 | 稳压二极管 | SMD 编带 SOD-123 BZT52C15 15V ROHS | 标准件 | 1 | D41 | BZT52C15 | CJ
..2 | A1D02.00007 | TVS管 | SMD编带 SOD-123 SMFJ18A ROHS | 标准件 | 1 | D47 | SMFJ18A | 晶导微
..2 | A1D02.00010 | 肖特基二极管 | SMD编带 SOD-123 B5819W ROHS | 标准件 | 2 | D5000,D37 | B5819W | 长电
..2 | A1D02.00005 | 肖特基二极管 | SMD 编带 SOD-323 B5819WS 晶导微 ROHS | 标准件 | 3 | D1,D2,D90038 | B5819WS | 晶导微
..2 | A1D02.00006 | 肖特基二极管 | SMD编带 DO-214AC SS54 ROHS | 标准件 | 2 | D45,D46 | SS54 | 晶导微
..2 | A1D03.00002 | 发光二极管 | SMD编带 0603 发绿光 单色 mcd=150 IF=20mA 无色散光 ROHS | 标准件 | 1 | LED4 | EY-TB0603GC-010F | 恩域光电
..2 | A1D01.00009 | 三极管 | SMD编带 SOT-23 S8050 NPN ROHS | 标准件 | 1 | Q9515 | S8050 | 长晶
..2 | A1L09.00034 | 贴片磁珠 | SMD 0402 FB120R 2A ±25% ROHS | 标准件 | 3 | FB2,FB6,FB7 | HCB1005KF-121T20 | TAI-TECH(台庆)
..2 | A1L09.00006 | 贴片磁珠 | SMD 1206 FB60R 5A ±25% ROHS | 标准件 | 2 | R148,R150 | HCB3216KF-600T50 | TAI-TECH(台庆)
..2 | A1L01.00132 | 贴片功率电感 | SMD 带屏蔽 5.4*5.2*2.8mm 1.5UH 10A ±20% RXWSHC0530-1R5M 仁芯微 ROHS | 标准件 | 2 | L12,L5002 | RXWSHC0530-1R5M | 仁芯微
..2 | A1L01.00071 | 贴片功率电感 | SMD 带屏蔽 5.4*5.2*1.8mm 4.7UH 4.5A ±20% RXWSHC0520-4R7M ROHS | 标准件 | 1 | L13 | RXWSHC0520-4R7M | 仁芯微
..2 | A1L01.00021 | 贴片功率电感 | SMD 带屏蔽 3*3*1.5mm 4.7UH 3A ±20% RXWHJ3015-4R7MT ROHS | 标准件 | 1 | L5000 | RXWHJ3015-4R7MT | 仁芯微
..2 | A1L01.00020 | 贴片功率电感 | SMD 带屏蔽 3*3*1.5mm 2.2UH 4.6A ±20% RXWHJ3015-2R2MT 仁芯微 ROHS | 标准件 | 1 | L5011 | RXWHJ3015-2R2MT | 仁芯微
..2 | A1L03.00006 | 共模电感 | SMD TDK MCZ1210DH900L2TA0G 90R 4PIN ±5% ROHS | 标准件 | 5 | FB261,L5012,L90020,L90026，L90027 | MCZ1210DH900L2TA0G | TDK
..2 | A1L03.00011 | 共模电感 | SMD 编带 BCMF062P120T 12R 4PIN 11.98GHZ ±5% 比创达 ROHS | 标准件 | 8 | L5003,L5004,L5005,L5006,L5007,L5008,L5009,L5010 | BCMF062P120T | 比创达
..2 | A1L09.00002 | 贴片磁珠 | SMD 0402 FB120R 1A PZ1005U121-1R0TF ±25% Sunlord(顺络) ROHS | 标准件 | 1 | L3 | PZ1005U121-1R0TF | Sunlord(顺络)
..2 | A1I01.00037 | IC | SMD DCDC MP8759GD-Z MPS QFN12 ROHS | 标准件 | 1 | U1 | MP8759GD-Z | MPS
..2 | A1I01.00206 | IC | SMD HUB FE1.1S_BQFN24B QFN24 Terminus ROHS | 标准件 | 1 | U17 | FE1.1S_BQFN24B | Terminus
..2 | A1I01.00033 | IC | SMD DCDC NB679GD-Z QFN12 MPS ROHS | 标准件 | 1 | U27 | NB679GD-Z | MPS
..2 | A1I01.00017 | IC | SMD USB限流 SY6280AAC SOT23-5 ROHS | 标准件 | 1 | U2603 | SY6280AAC | silergy(矽力杰)
..2 | A1I01.00054 | IC | SMD 限流 SGM2576BYN5G/TR SOT-23-5 圣邦威 ROHS | 标准件 | 3 | U90115,U90128,U2305 | SGM2576BYN5G/TR | 圣邦威
..2 | A1I01.00017 | IC | SMD USB限流 SY6280AAC SOT23-5 ROHS | 替代件 | 3 | U90115,U90128,U2305 | SY6280AAC | silergy(矽力杰)
..2 | A1I01.00217 | IC | SMD TYPEC协议 FUSB302BMPX MLP-14 ROHS | 标准件 | 1 | U2602 | FUSB302BMPX | onsemi(安森美)
..2 | A1I01.00032 | IC | SMD DCDC SY8089AAAC SOT23-5 ROHS | 标准件 | 1 | U90077 | SY8089AAAC | silergy(矽力杰)
..2 | A1I01.00493 | IC | SMD 驱动 MP3302DJ–LF–Z SOT23-5 MPS ROHS | 标准件 | 1 | U90082 | MP3302DJ–LF–Z | MPS
..2 | A1I01.00022 | IC | SMD 电平转换 UM3204H CSP-12 ROHS | 标准件 | 5 | U90089,U90132,U90133,U90135,U90136 | UM3204H | 上海英联
..2 | A1I01.00093 | IC | SMD DCDC SY8113BADC SOT23-6 silergy(矽力杰) ROHS | 标准件 | 1 | U29 | SY8113BADC | silergy(矽力杰)
..2 | A1I01.00055 | IC | SMD 音频 顺芯 ES8316 QFN32 ROHS | 标准件 | 1 | U90129 | ES8316 | 顺芯
..2 | A1I01.00264 | IC | SMD 时钟 HYM8563TS TSSOP8 武汉昊昱微 ROHS | 标准件 | 1 | U3 | HYM8563TS | 武汉昊昱微
..2 | A1I01.00437 | IC | SMD 时钟 TCS8563 MSOP8 汤诚 ROHS | 替代件 | 1 | U3 | TCS8563 | 汤诚
..2 | A1J01.00032 | 连接座 | SMD 母座 电池座 CR1220-3V 文章济美 ROHS | 标准件 | 1 | U90131 | CR1220-3V | 文章济美
..2 | A1Y01.00011 | 石英晶振 | SMD编带 无源 3225 12MHz 20PF ±10ppm ROHS | 标准件 | 1 | Y1 | 3S12.000E20UCG | 晶灏
..2 | A1Y01.00002 | 石英晶振 | SMD编带 无源 3215 32.768KHz 12.5PF ±20ppm ROHS | 标准件 | 1 | Y2 | SF32WK32768D31T002 | 泰晶
..2 | A1J02.00003 | TF卡座 | SMD TFW09-HRJ-68B 14.75*14.5*H1.85mm 不锈钢 ROHS | 标准件 | 1 | CN14A1 | TFW09-HRJ-68B | 文章济美
..2 | A1J01.00029 | 连接座 | SMD 母座 75PIN 180度 H5.5mm 0.5mm脚距 M.2 E KEY APCI0488-P001A 黑色 LOTES ROHS | 标准件 | 1 | U4301 | APCI0488-P001A | LOTES | APCI0317-P001A | LOTES
..2 | A1J06.00001 | FPC座 | SMD 下接触 卧式 39PIN 0.3mm脚距 后翻盖H1.0 镀金 FH35C-39S-0.3SHW(50) ROHS | 标准件 | 1 | U90104 | FH35C-39S-0.3SHW(50) | 广濑
..2 | A1J08.00010 | USB3.0母座 | SMD USB3.0母座 单层 直边无定位柱 蓝色胶芯 14.5*13*H6.8mm 90度弯脚 直脚固定间距12.6mm 鱼叉脚 脚长2.7mm ROHS | 标准件 | 1 | USB2502 | 5001-01010011A | 文章济美
..2 | A1J10.00001 | 耳机插座 | SMD XJ-DR-PJ342B-00 6PIN 外孔Φ6.0mm 内孔Φ3.6mm 前插后贴 14*6.4*H4.5MM 黑色 镀金铜头 协佳 ROHS | 标准件 | 1 | J15 | XJ-DR-PJ342B-00 | 协佳
..2 | A1J06.00002 | FPC座 | SMD 上下接触 卧式 31PIN 0.3mm脚距 后翻盖H1.0 FH35C-31S-0.3SHW(50) 镀金 ROHS | 标准件 | 1 | J5002 | FH35C-31S-0.3SHW(50) | 广濑
..2 | A1J04.00005 | HDMI座 | SMD A座 19PIN 180度 卧贴 12.1*15*6.05mm 镀镍 脚距14.5mm 916000-000004 ROHS | 标准件 | 1 | J1 | 916000-000004 | 闻川科技
..2 | A1J04.00007 | TYPEC座 | SMD母座 2*12PIN 双排 8.94*7.9*H3.2mm 带定位柱 不锈钢 ROHS | 标准件 | 1 | J8202 | TYPE-C USB JACK | 协佳
..2 | A1J01.00028 | 连接座 | SMD 母座 1*2PIN 90度 立贴 1.25mm脚距 5001—WF0125B—02R1-00 白色 文章济美 ROHS | 标准件 | 1 | U26 | 5001—WF0125B—02R1-00 | 文章济美
..2 | A1J01.00008 | FPC座 | SMD 下接触 立式 2*15PIN 180度 1.0mm脚距 胶厚3mm 白色卡扣 FPC1030-15S-TAG ROHS | 标准件 | 2 | J6,J7 | FPC1030-15S-TAG | 金胜博业
..2 | A2S02.00164 | 铜柱 | RS119 铜柱 M2*3.5*4.9 铜 镀锡 DDSMT231122104 东达 | 标准件 | 1 | J2 | DDSMT231122104 | 东达
..2 | A2S02.00012 | 铜柱 | 铜柱 SMD M2 通孔 一端∅3.5mm 高3.5mm 另一端∅2.5mm 高1.4mm 总高4.9mm 铜镀锡 ROHS XJH01-001 雄和远景 | 替代件 | 1 | J2 | XJH01-001 | 雄和远景
..2 | A1J01.00025 | 连接座 | SMD 母座 2*50PIN 180度 22.6x1.88x1.14mm 0.4mm脚距 DF40C-100DS-0.4V(51) 黑色 ROHS | 标准件 | 3 | U33A,U33B,J24 | DF40C-100DS-0.4V(51) | 广濑
