omaralabed/Radxa-CM5-PCB/fabrication/harnesses/H03-Lid-Display-Bundle.png

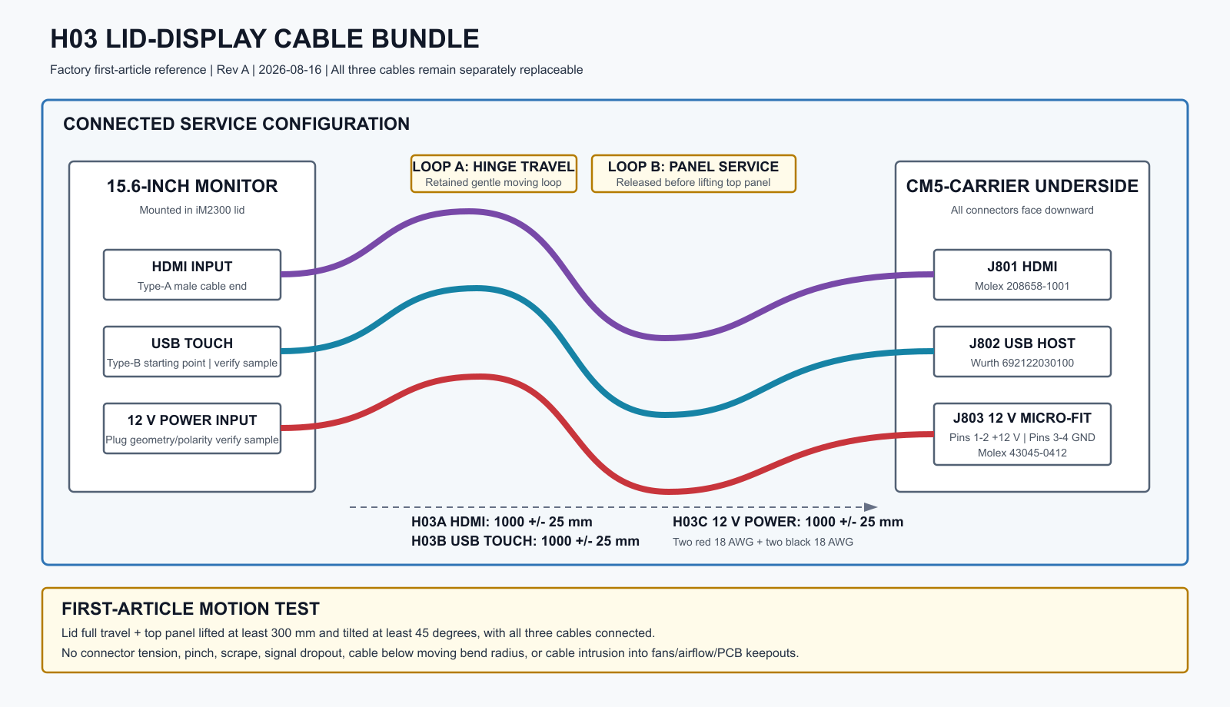
fabrication/harnesses/H03-Lid-Display-Bundle.png
