omaralabed/Radxa-CM5-PCB/fabrication/harnesses/PSU-Harness-Interfaces.png

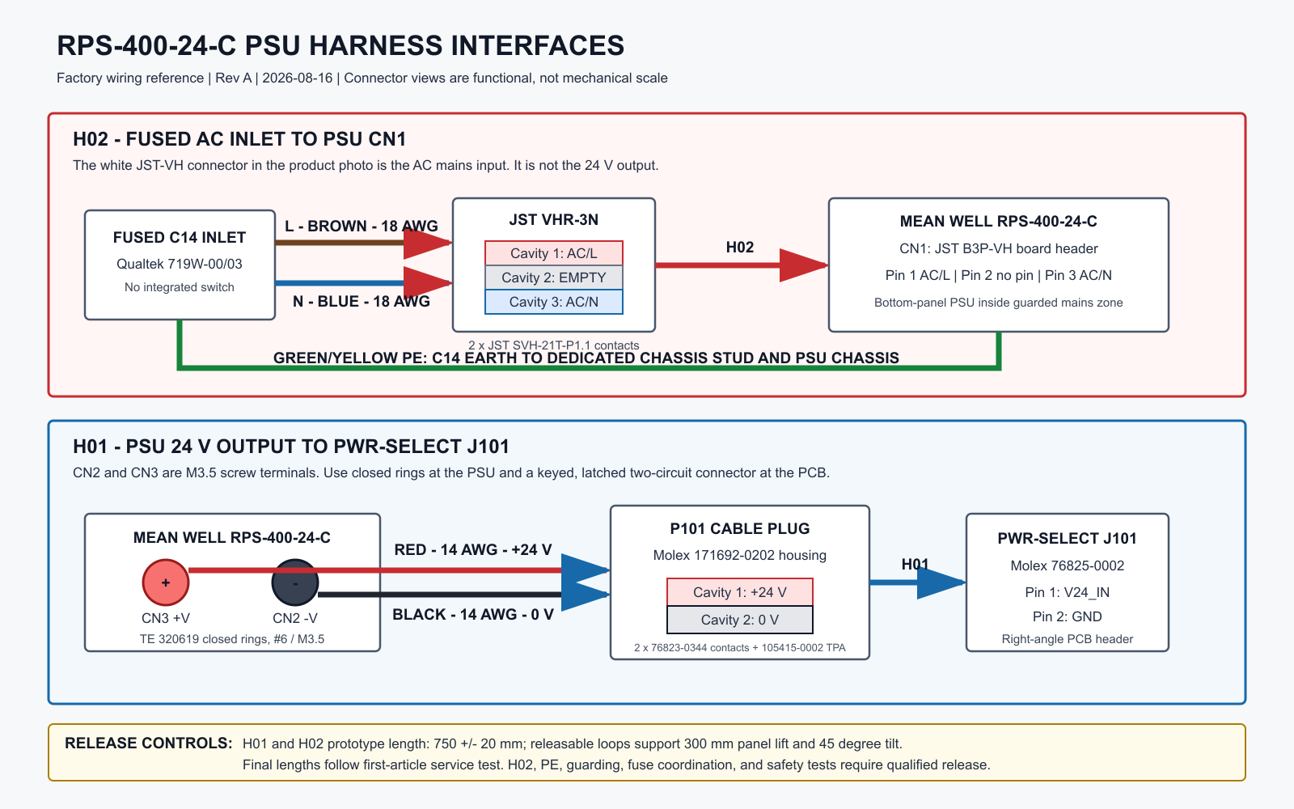
fabrication/harnesses/PSU-Harness-Interfaces.png
