omaralabed/Radxa-CM5-PCB/fabrication/mechanical-release/im2300-measurement-register.csv

id | group | measurement | datum_from | datum_to | units | design_target | tolerance_or_limit | measured_min | measured_max | tool | status | inspection_record
M001 | case | Opening width at hinge side | B | right case wall | mm | published reference 431.8 | record actual |  |  |  | OPEN
M002 | case | Opening width at center | B | right case wall | mm | published reference 431.8 | record actual |  |  |  | OPEN
M003 | case | Opening width at operator side | B | right case wall | mm | published reference 431.8 | record actual |  |  |  | OPEN
M004 | case | Opening depth at left side | C | operator case wall | mm | published bezel reference 298.0 | record actual |  |  |  | OPEN
M005 | case | Opening depth at center | C | operator case wall | mm | published bezel reference 298.0 | record actual |  |  |  | OPEN
M006 | case | Opening depth at right side | C | operator case wall | mm | published bezel reference 298.0 | record actual |  |  |  | OPEN
M007 | case | Inside corner radius upper left | case opening | corner | mm | TBD | record actual |  |  |  | OPEN
M008 | case | Inside corner radius upper right | case opening | corner | mm | TBD | record actual |  |  |  | OPEN
M009 | case | Inside corner radius lower left | case opening | corner | mm | TBD | record actual |  |  |  | OPEN
M010 | case | Inside corner radius lower right | case opening | corner | mm | TBD | record actual |  |  |  | OPEN
M011 | case | Opening diagonal upper-left to lower-right | case opening | case opening | mm | TBD | compare within 1.0 mm |  |  |  | OPEN
M012 | case | Opening diagonal upper-right to lower-left | case opening | case opening | mm | TBD | compare within 1.0 mm |  |  |  | OPEN
M013 | frame | Panel recess | D | A | mm | 38.1 | +/-0.5 |  |  |  | OPEN
M014 | frame | Frame support width left | case wall | E | mm | 15.0 minimum | >=15.0 |  |  |  | OPEN
M015 | frame | Frame support width right | case wall | E | mm | 15.0 minimum | >=15.0 |  |  |  | OPEN
M016 | frame | Frame support width hinge | case wall | E | mm | 15.0 minimum | >=15.0 |  |  |  | OPEN
M017 | frame | Frame support width operator | case wall | E | mm | 15.0 minimum | >=15.0 |  |  |  | OPEN
M018 | frame | Panel material thickness | top face | bottom face | mm | 3.2 | 3.0 to 3.3 |  |  |  | OPEN
M019 | frame | Frame screw edge distance | hole center | finished panel edge | mm | 8.0 minimum | >=8.0 |  |  |  | OPEN
M020 | frame | Frame nut and washer intrusion | frame inner edge | hardware envelope | mm | TBD | record maximum |  |  |  | OPEN
M021 | lid | Display total protrusion | lid cavity back surface | direct-mount gasket/display front glass | mm | TBD | record maximum from actual direct-mounted sample; exterior screw heads and hinge-edge connector heads do not add to the internal Z stack |  |  |  | OPEN
M022 | lid | Closed-lid gap at XLR bank | display front | XLR face | mm | 12.7 minimum dynamic | >=12.7 after tolerance |  |  |  | OPEN
M023 | lid | Battery-installed closure interference | display front | battery plus QRC-GOLD | mm | informational | do not latch if interference; battery is removed for transport |  |  |  | OPEN
M024 | lid | Closed-lid gap at folded RF bank | display front | highest point of all eight folded antennas | mm | 12.7 minimum dynamic | >=12.7 with released antennas installed and folded inboard |  |  |  | OPEN
M025 | lid | Hinge harness bend radius | harness centerline | bend center | mm | 10 x cable diameter minimum | record actual |  |  |  | OPEN
M026 | lid | Hinge harness slack at full opening | harness anchors | harness loop | mm | TBD | no tension or pinch |  |  |  | OPEN
M027 | bottom | Available depth below panel underside | panel underside | deepest interior floor | mm | published nominal 65.425 with 3.175 mm panel | record actual minimum |  |  |  | OPEN
M028 | bottom | PSU guard vertical clearance to carrier or panel underside | PSU guard | nearest overlying carrier component or panel | mm | 10.0 minimum | >=10.0 plus wiring |  |  |  | OPEN
M029 | bottom | CM5 dedicated fan inlet clearance | fan inlet | nearest floor or bottom hardware | mm | 10.0 minimum | >=10.0 through tolerance and vibration |  |  |  | OPEN
M030 | bottom | Modem dedicated fan inlet clearance | fan inlet | nearest floor or bottom hardware | mm | 10.0 minimum | >=10.0 through tolerance and vibration |  |  |  | OPEN
M031 | battery | Left-side insertion and hand corridor | XLR hardware | battery dock edge | mm | 30.0 target | >=20.0 minimum |  |  |  | OPEN
M032 | battery | Installed right-side service clearance | battery envelope | nearest RJ45 or cable | mm | 27.0 target | >=20.0 minimum |  |  |  | OPEN
M033 | battery | Left-to-right engagement slide travel | battery start position | fully latched position | mm | TBD | complete engagement with no collision |  |  |  | OPEN
M034 | thermal | Right-wall intake center from hinge side | C | fan axis | mm | 210 preliminary | +/-0.5 after physical release |  |  |  | OPEN
M035 | thermal | Right-wall intake center below parting line | D | fan axis | mm | 71.5 preliminary | +/-0.5 after physical release |  |  |  | OPEN
M036 | thermal | Operator-wall exhaust center from left side | B | fan axis | mm | 310 preliminary | +/-0.5 after physical release |  |  |  | OPEN
M037 | thermal | Operator-wall exhaust center below parting line | D | fan axis | mm | 71.5 preliminary | +/-0.5 after physical release |  |  |  | OPEN
M038 | thermal | Fan and PWM wiring separation to audio quiet boundary | audio boundary | nearest fan or PWM harness | mm | 100 target | >=100 where practical; engineering review if less |  |  |  | OPEN
M039 | pcb | AUDIO-8X8 maximum outline | PCB edge | PCB edge | mm | 78 x 268 | must not exceed |  |  |  | OPEN
M040 | pcb | CM5-CARRIER maximum outline | PCB edge | PCB edge | mm | 166 x 268 | must not exceed |  |  |  | OPEN
M041 | pcb | Minimum PCB to frame hardware clearance | PCB/copper/frame keepout | frame hardware | mm | 3.0 minimum | >=3.0 |  |  |  | OPEN
M042 | vibration | PCB standoff unsupported span | standoff | standoff | mm | 128.0 maximum between support rows | <=128.0 and engineering review |  |  |  | OPEN
M043 | vibration | Heavy component restraint clearance | component restraint | panel/bottom | mm | TBD | no preload on PCB |  |  |  | OPEN
M044 | panel | Hinge harness notch width | notch edge | notch edge | mm | 90.0 preliminary | release from cable bundle |  |  |  | OPEN
M045 | panel | Hinge harness notch depth | hinge panel edge | notch edge | mm | 8.0 preliminary | release from cable bundle |  |  |  | OPEN
M046 | thermal | Minimum sidewall fan reinforcement clearance | reinforcement or guard | case ribs handle hinges latches or frame | mm | 5.0 minimum | >=5.0 static plus service access |  |  |  | OPEN
M047 | emc | PSU guard separation to audio quiet boundary | audio quiet boundary | nearest grounded PSU guard edge | mm | 125.0 minimum | >=125.0 after tolerance stack |  |  |  | OPEN
M048 | harness | Lid-display cable envelope clearance to PSU guard | HDMI USB-touch and 12 V cable envelope | nearest grounded PSU guard edge | mm | 15.0 minimum | >=15.0 through full lid and panel service motion |  |  |  | OPEN
M049 | bottom | Local floor height variation under equipment tray | deepest interior floor | highest rib or support point | mm | TBD | record profile and maximum |  |  |  | OPEN
M050 | bottom | Bottom equipment tray material thickness | tray top | tray bottom | mm | 2.0 | 1.8 to 2.2 |  |  |  | OPEN
M051 | bottom | Bottom equipment tray top elevation | deepest interior floor | tray top | mm | 3.0 maximum | <=3.0 including restrained isolator |  |  |  | OPEN
M052 | bottom | Panel top-face height above deepest floor | deepest interior floor | A | mm | published nominal 68.6 | record actual minimum |  |  |  | OPEN
M053 | bottom | Clear height from tray top to panel underside | tray top | panel underside | mm | published nominal 62.4 if tray top is 3.0 | record actual minimum |  |  |  | OPEN
M054 | power | Installed PSU case height | tray top | RPS-400-24-C case top | mm | 43.0 | +/-1.0 manufacturer body tolerance plus mounting stack |  |  |  | OPEN
M055 | power | Installed PSU guard envelope height | deepest interior floor | tallest guard terminal cover or conductor bend | mm | 48.0 maximum | <=48.0 everywhere under carrier |  |  |  | OPEN
M056 | pcb | Carrier top-side gap to panel underside | carrier F.Cu highest non-panel component | panel underside | mm | 4.0 minimum | >=4.0 after tolerance; panel connector geometry controls |  |  |  | OPEN
M057 | pcb | Carrier bottom copper-plane height | deepest interior floor | carrier B.Cu surface | mm | TBD | record minimum at all supports |  |  |  | OPEN
M058 | power | PSU guard clearance to carrier B.Cu | PSU guard envelope | carrier B.Cu keepout plane | mm | 10.0 minimum | >=10.0 after tolerance and vibration |  |  |  | OPEN
M059 | display | Monitor documented body width | left body edge | right body edge | mm | 396.24 nominal | controlled Amazon ASIN listing value; installed fit uses M062-M065 | 396.24 | 396.24 | Amazon product information | COMPLETE | ASIN B0GK5X95D9 accessed 2026-08-16
M060 | display | Monitor documented body height | top body edge | bottom body edge | mm | 203.20 nominal | controlled Amazon ASIN listing value; installed fit uses M062-M065 | 203.20 | 203.20 | Amazon product information | COMPLETE | ASIN B0GK5X95D9 accessed 2026-08-16
M061 | display | Monitor documented body depth | rear body surface | front glass | mm | 20.32 nominal | controlled Amazon ASIN listing value; mount buildup uses M062; monitor connectors remain inside the rear-bracket Z envelope | 20.32 | 20.32 | Amazon product information | COMPLETE | ASIN B0GK5X95D9 accessed 2026-08-16
M062 | display | Monitor total lid protrusion | lid cavity back surface | front glass or bezel | mm | TBD | include compressed direct-mount gasket; exterior screw heads and hinge-edge connector heads are excluded from internal Z only after direct-mount and cable-motion verification |  |  |  | OPEN
M063 | display | Monitor left-right position in lid | lid cavity left wall | monitor body edges | mm | TBD | record both margins and centering error |  |  |  | OPEN
M064 | display | Monitor hinge-operator position in lid | lid cavity hinge wall | monitor body edges | mm | TBD | record both margins and harness keepout |  |  |  | OPEN
M065 | lid | Minimum closed-lid permanent-hardware clearance | display front | tallest permanent panel hardware | mm | 12.7 minimum | >=12.7 through gasket compression lid flex and tolerance |  |  |  | OPEN
M066 | battery | QRC-GOLD plate protrusion | A | tallest dock or latch point | mm | published body approximately 12.7 | measure full latch and backplate stack |  |  |  | OPEN
M067 | battery | Battery plus QRC-GOLD total protrusion | A | tallest installed battery point | mm | preliminary approximately 70.7 | record actual; transport state is battery removed |  |  |  | OPEN
M068 | rf | Folded RF antenna protrusion | A | tallest hinge housing or folded antenna surface | mm | 32.0 preliminary maximum | measure every installed antenna and record the worst case |  |  |  | OPEN
M069 | rf | Folded RF transport closure sweep | display lid and neighboring panel hardware | all eight installed and folded RF antennas | mm | 12.7 minimum | fold each antenna inboard and verify the full closing and latched sweep without contact |  |  |  | OPEN
M070 | thermal | Clean-filter through-case airflow | right intake | operator exhaust | CFM | 15.0 minimum | >=15.0 at released PWM and nominal line voltage |  |  |  | OPEN
M071 | thermal | Loaded-filter through-case airflow | right intake | operator exhaust | CFM | 12.0 minimum | >=12.0 at maintenance loading limit |  |  |  | OPEN
M072 | thermal | PSU inlet-air temperature at qualification | PSU inlet sensor | ambient chamber | C | 50.0 maximum | <=50.0 at 45 C ambient and 151.7 W continuous load |  |  |  | OPEN
M073 | vibration | Panel deflection under battery insertion and field load | A | QRC-GOLD fastener region | mm | TBD | no permanent set contact or frame lift |  |  |  | OPEN
M074 | vibration | AUDIO-8X8 maximum unsupported span | PCB support | adjacent PCB support | mm | 128.0 maximum | <=128.0 using controlled A1-A6 pattern and engineering review |  |  |  | OPEN
M075 | vibration | CM5-CARRIER maximum unsupported span | PCB support | adjacent PCB support | mm | 128.0 maximum | <=128.0 using controlled C1-C6 pattern and engineering review |  |  |  | OPEN
M076 | thermal | CM5 fan inlet gap under tolerance and vibration | fan inlet | nearest floor tray or harness | mm | 10.0 minimum | >=10.0 in worst case |  |  |  | OPEN
M077 | thermal | Modem fan inlet gap under tolerance and vibration | fan inlet | nearest floor tray or harness | mm | 10.0 minimum | >=10.0 in worst case |  |  |  | OPEN
M078 | safety | PSU chassis and panel protective-earth continuity | AC inlet PE | PSU case panel frame and tray | milliohm | TBD | record test method and pass limit from safety plan |  |  |  | OPEN
M079 | harness | Display harness full-motion clearance | H03 bundle | case frame PSU fans and sharp edges | mm | 3.0 minimum static plus bend requirement | no tension pinch rub fan entry or hot-surface contact |  |  |  | OPEN
M080 | material | Panel finish and grounding coupon | finished panel | PE bond and connector samples | inspection | 5052-H32 3.175 mm matte black | fit adhesion corrosion and masked-bond approval |  |  |  | OPEN
