omaralabed/Radxa-CM5-PCB/fabrication/mechanical-release/im2300-measurement-worksheet-a2.png

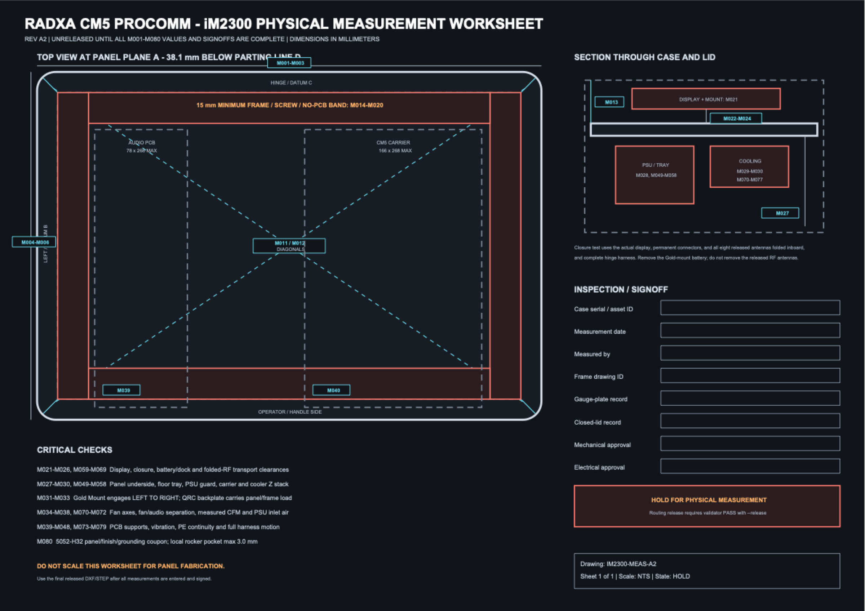
fabrication/mechanical-release/im2300-measurement-worksheet-a2.png
