omaralabed/Radxa-CM5-PCB/fabrication/footprint-coupon-a1/output/drawings/Footprint-Coupon-assembly-top.pdf

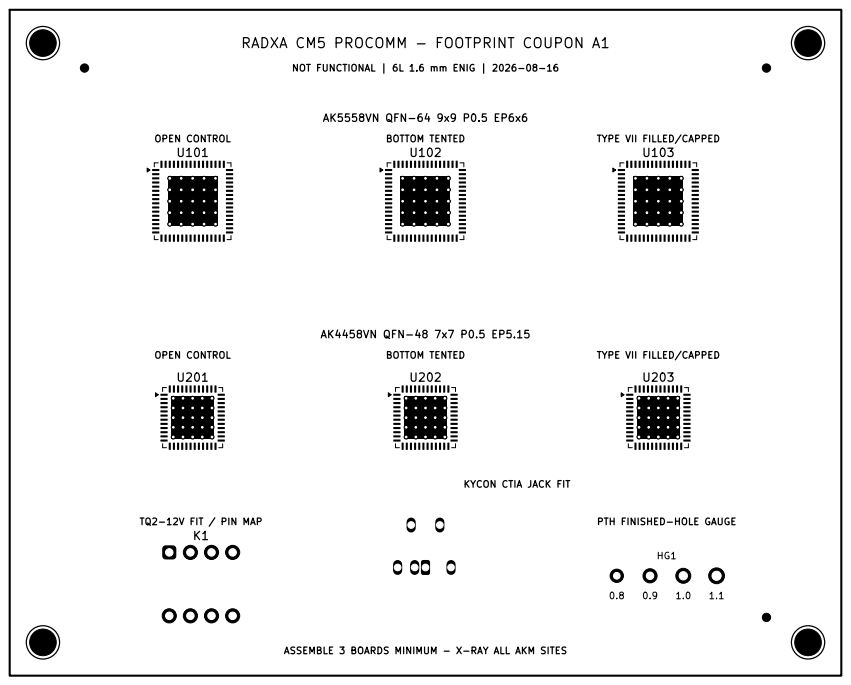
[picture p59: page 1]

RADXA CM5 PROCOMM - FOOTPRINT COUPON A1

NOT FUNCTIONAL | 6L 1.6 mm ENIG | 2026-08-16

KYCON CTIA JACK FIT

PTH FINISHED-HOLE GAUGE

ASSEMBLE 3 BOARDS MINIMUM - X-RAY ALL AKM SITES
