omaralabed/Radxa-CM5-PCB/fabrication/footprint-coupon-a1/output/drawings/Footprint-Coupon-fabrication.pdf

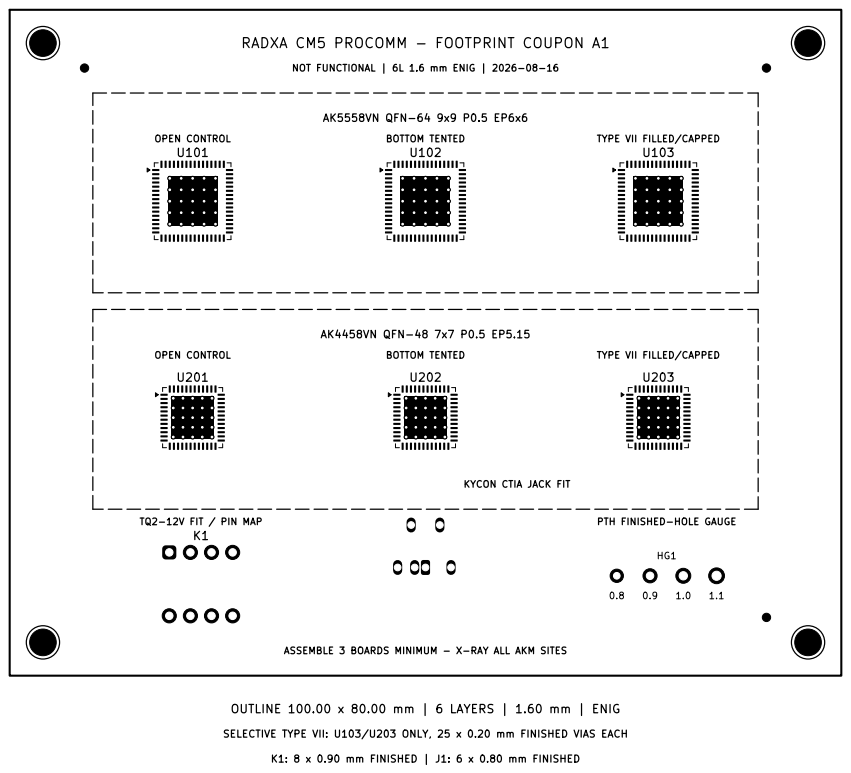
[picture p60: page 1]

RADXA CM5 PROCOMM - FOOTPRINT COUPON A1

NOT FUNCTIONAL | 6L 1.6 mm ENIG | 2026-08-16

KYCON CTIA JACK FIT

PTH FINISHED-HOLE GAUGE

ASSEMBLE 3 BOARDS MINIMUM - X-RAY ALL AKM SITES

OUTLINE 100.00 x 80.00 mm | 6 LAYERS | 1.60 mm | ENIG

SELECTIVE TYPE VII: U103/U203 ONLY, 25 x 0.20 mm FINISHED VIAS EACH

K1: 8 x 0.90 mm FINISHED | J1: 6 x 0.80 mm FINISHED
