omaralabed/Radxa-CM5-PCB/cad/kicad/CM5-CARRIER/REVIEW/CM5-Carrier-A1.pdf

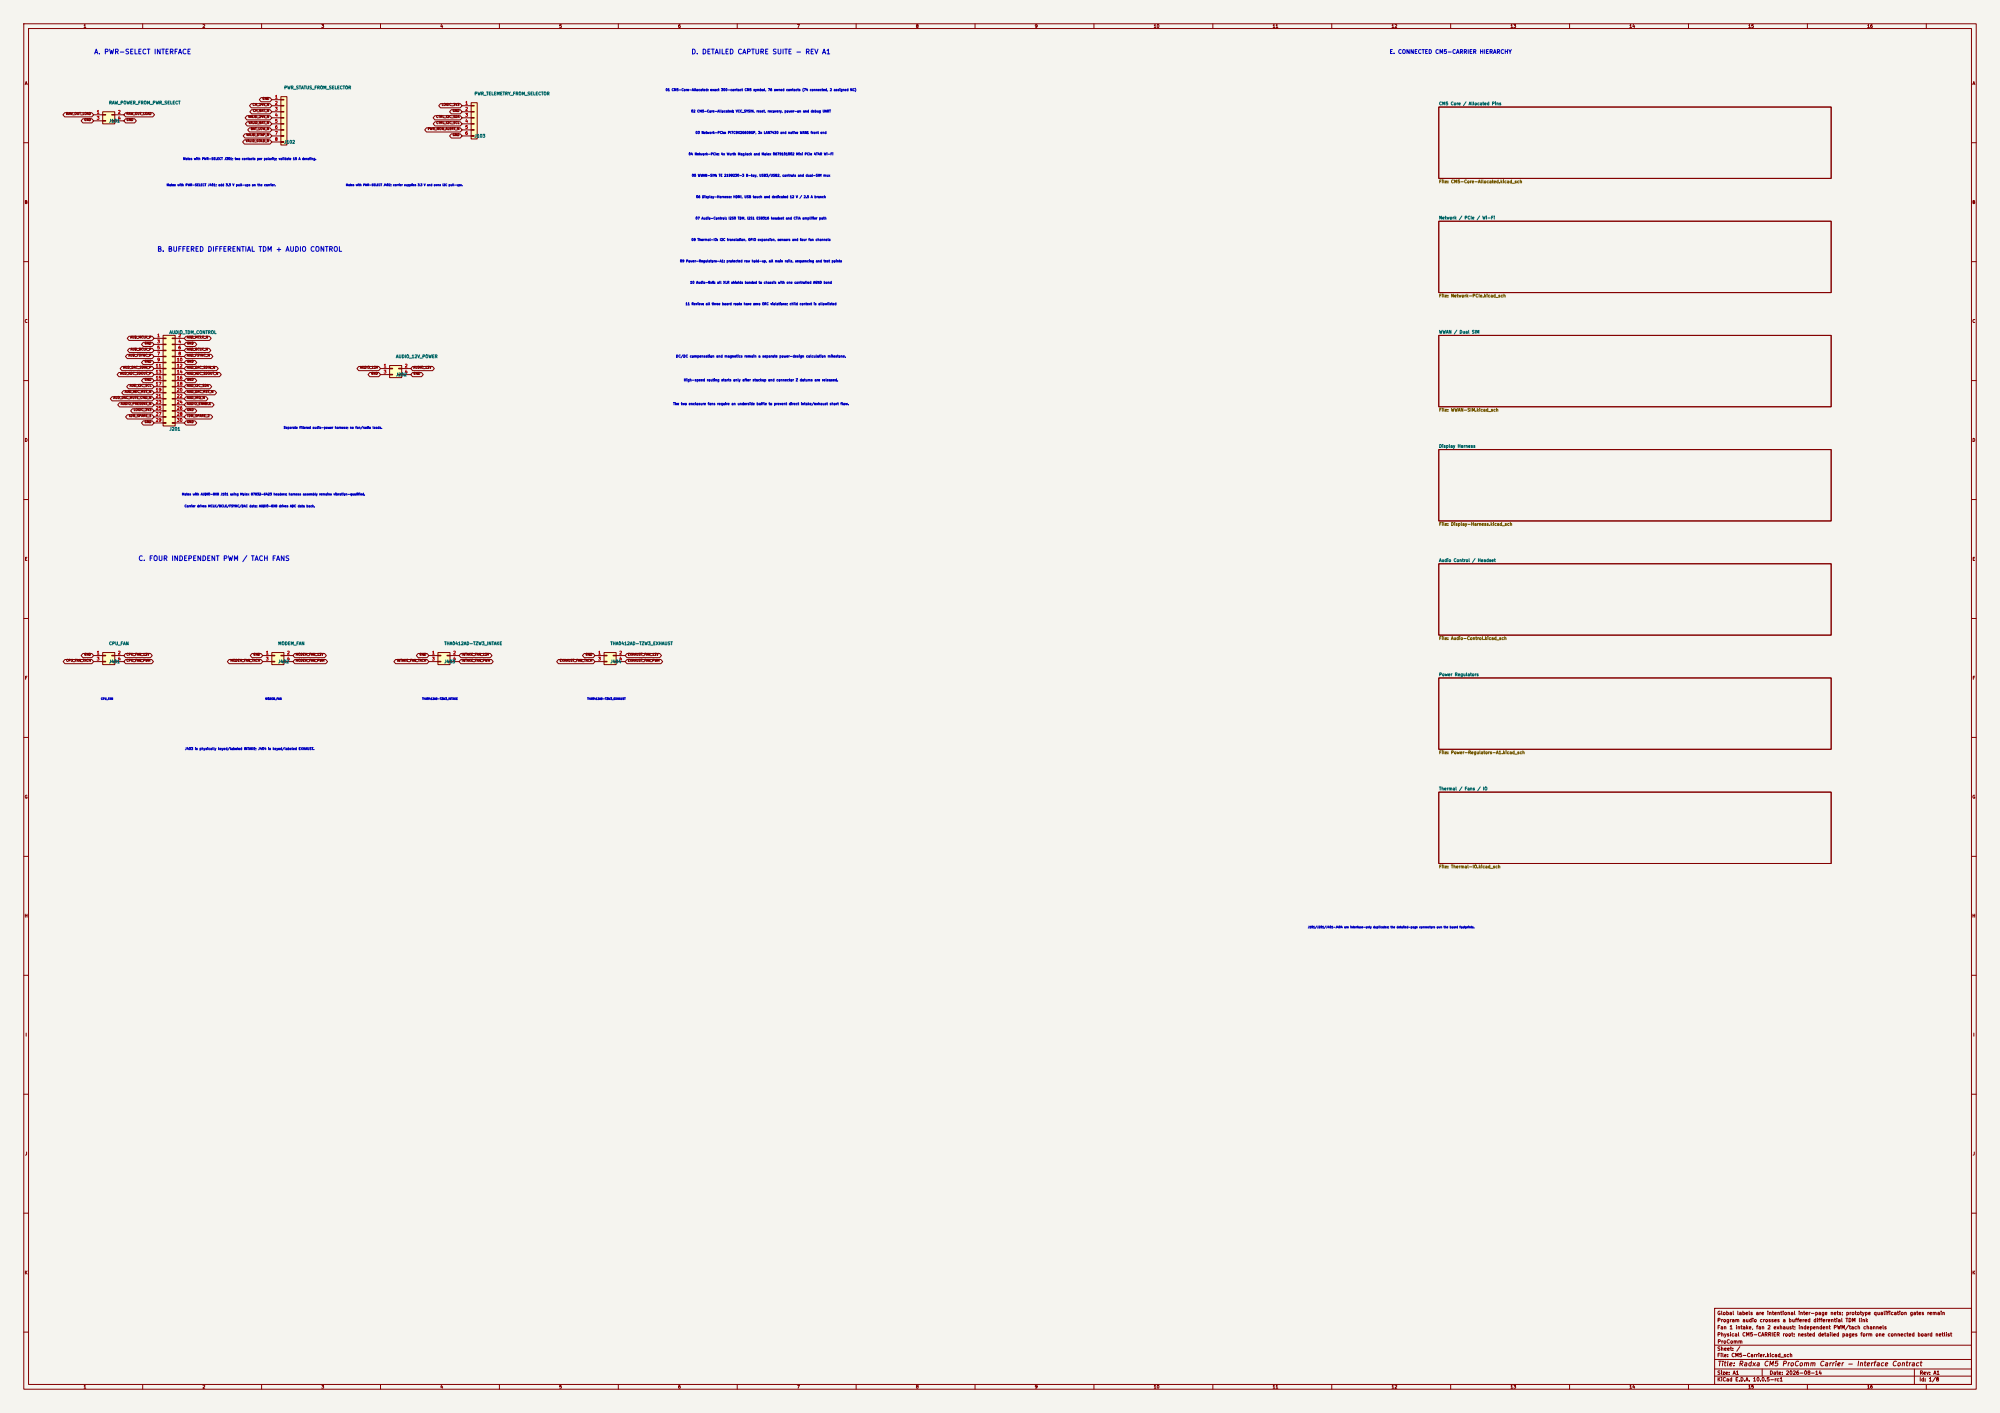
[picture p61: page 1]

Mates with PWR-SELECT J401; add 3.3 V pull-ups on the carrier. Mates with PWR-SELECT J301; two contacts per polarity; validate 15 A derating. A. PWR-SELECT INTERFACE

D. DETAILED CAPTURE SUITE - REV A1

01 CM5-Core-Allocated: exact 300-contact CM5 symbol, 76 owned contacts (74 connected, 2 assigned NC) 02 CM5-Core-Allocated: VCC_SYSIN, reset, recovery, power-on and debug UART 03 Network-PCIe: PI7C9X2G608GP, 3x LAN7430 and native WAN1 front end

CM5 Core / Allocated Pins File: CM5-Core-Allocated.kicad_sch

04 Network-PCIe: 4x Wurth MagJack and Molex 0679101002 Mini PCIe 4T4R Wi-Fi 05 WWAN-SIM: TE 2199230-3 B-key, USB3/USB2, controls and dual-SIM mux 06 Display-Harness: HDMI, USB touch and dedicated 12 V / 2.5 A branch 07 Audio-Control: I2S0 TDM, I2S1 ES8316 headset and CTIA amplifier path 08 Thermal-IO: I2C translation, GPIO expansion, sensors and four fan channels 09 Power-Regulators-A1: protected raw hold-up, all main rails, sequencing and test points 10 Audio-8x8: all XLR shields bonded to chassis with one controlled AGND bond 11 Review: all three board roots have zero ERC violations; child context is allowlisted DC/DC compensation and magnetics remain a separate power-design calculation milestone. High-speed routing starts only after stackup and connector Z datums are released. The two enclosure fans require an underside baffle to prevent direct intake/exhaust short flow.

Mates with PWR-SELECT J402; carrier supplies 3.3 V and owns I2C pull-ups.

Network / PCIe / Wi-Fi File: Network-PCIe.kicad_sch WWAN / Dual SIM

Separate filtered audio-power harness; no fan/radio loads. Carrier drives MCLK/BCLK/FSYNC/DAC data; AUDIO-8X8 drives ADC data back. Mates with AUDIO-8X8 J101 using Molex 87832-6423 headers; harness assembly remains vibration-qualified. B. BUFFERED DIFFERENTIAL TDM + AUDIO CONTROL

File: WWAN-SIM.kicad_sch Display Harness File: Display-Harness.kicad_sch
Audio Control / Headset File: Audio-Control.kicad_sch Power Regulators File: Power-Regulators-A1.kicad_sch

J403 is physically keyed/labeled INTAKE; J404 is keyed/labeled EXHAUST. MODEM_FAN C. FOUR INDEPENDENT PWM / TACH FANS

J101/J201/J401-J404 are interface-only duplicates; the detailed-page connectors own the board footprints.

Global labels are intentional inter-page nets; prototype qualification gates remain
Program audio crosses a buffered differential TDM link
Fan 1 intake, fan 2 exhaust; independent PWM/tach channels
Physical CM5-CARRIER root; nested detailed pages form one connected board netlist
ProComm
Sheet: /
File: CM5-Carrier.kicad_sch
Title: Radxa CM5 ProComm Carrier - Interface Contract

Size: A1 | Rev: A1
KiCad E.D.A. 10.0.5-rc1 | Id: 1/8

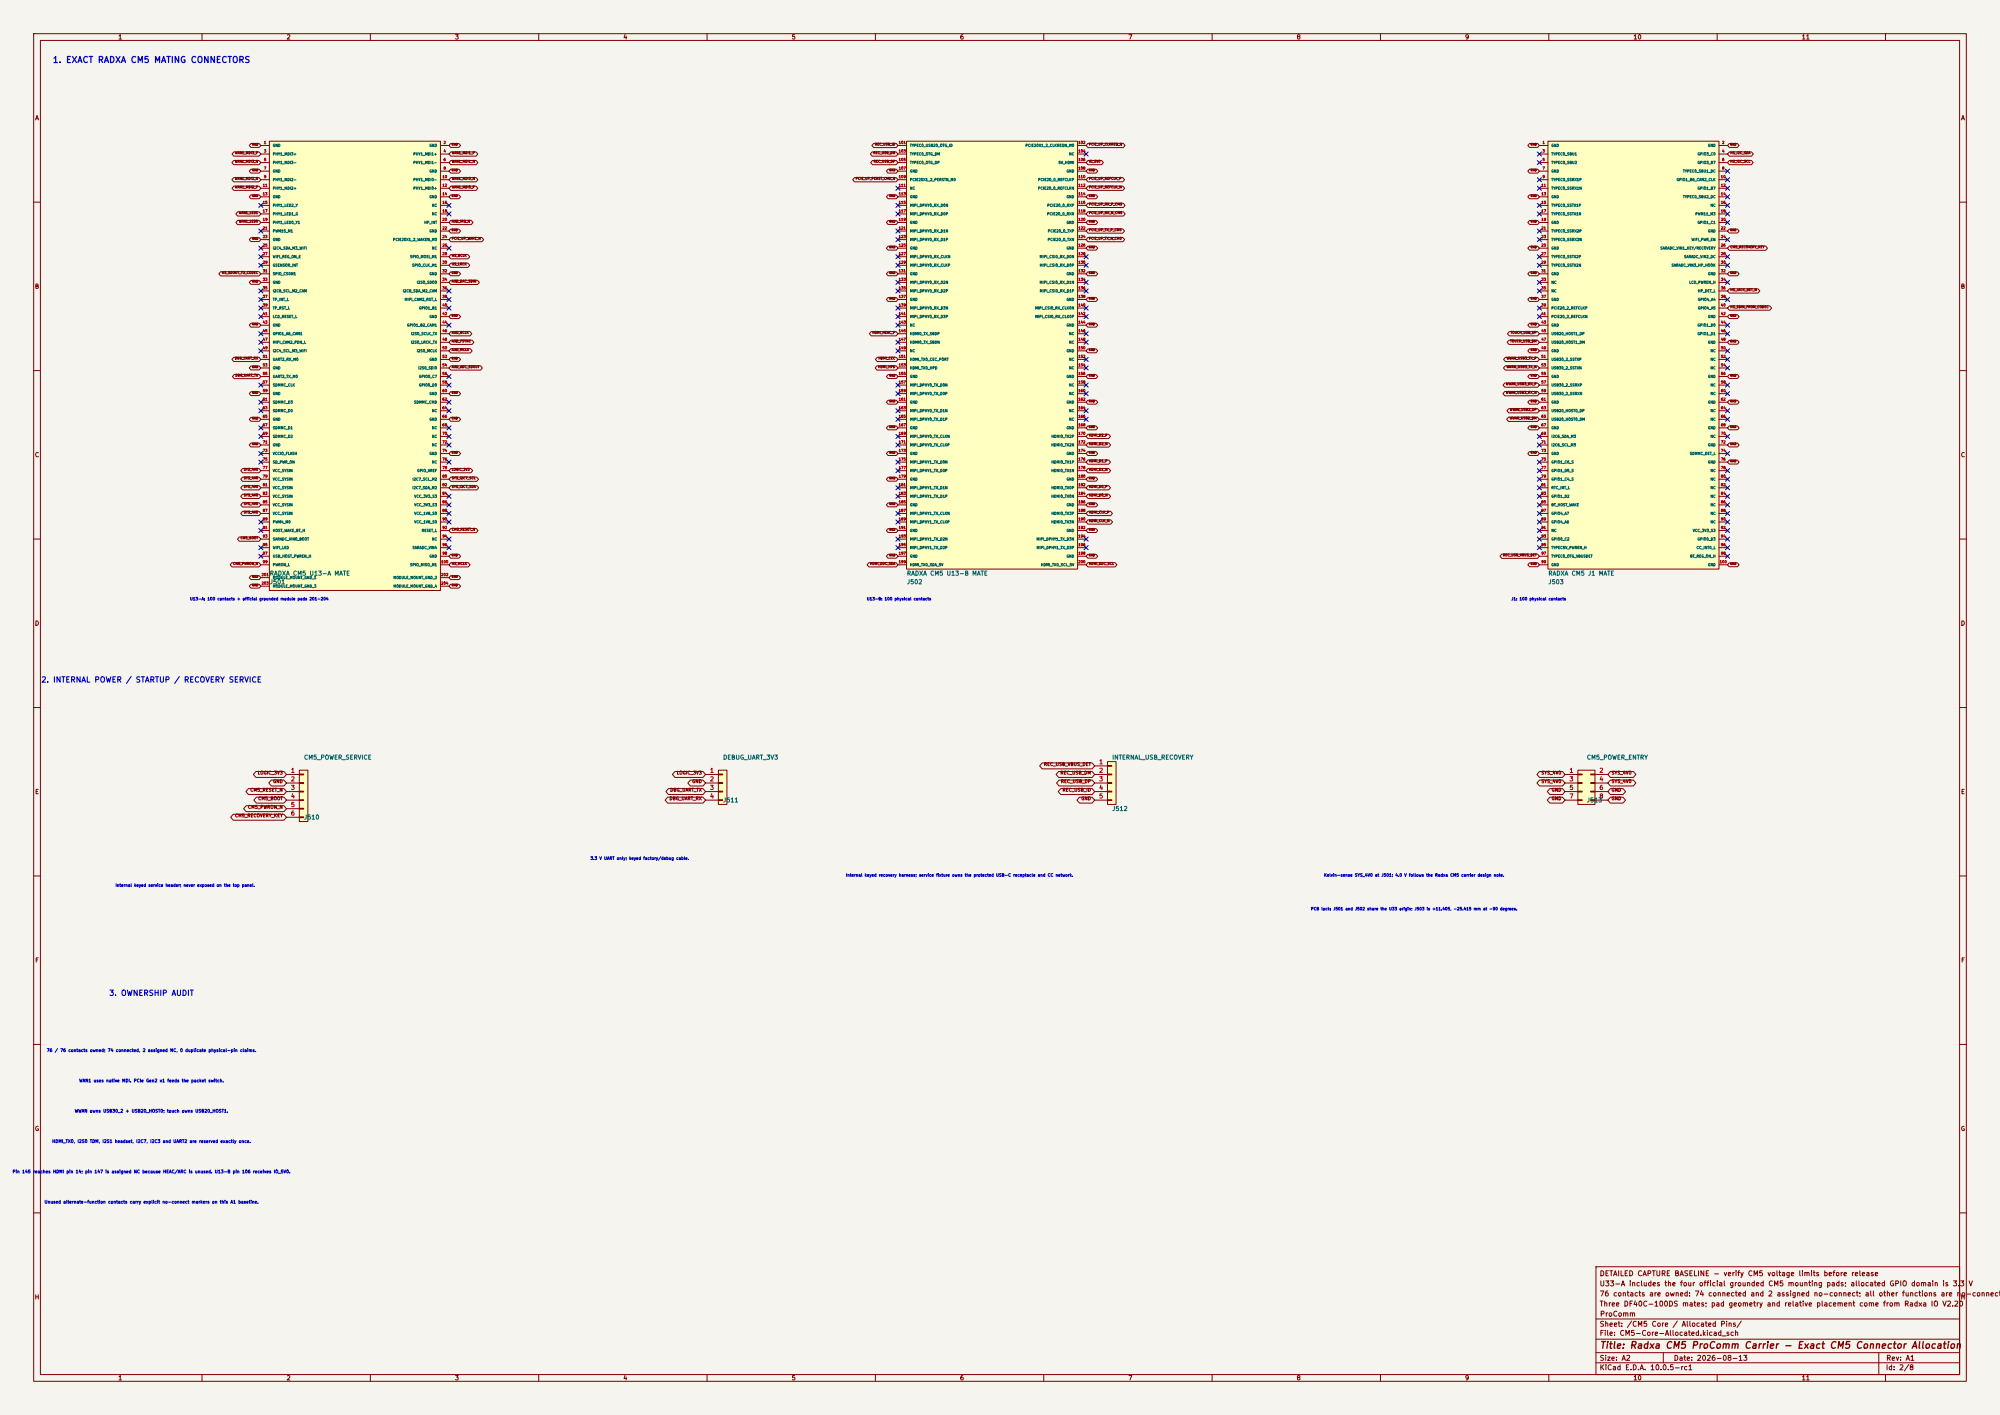
[picture p62: page 2]

1. EXACT RADXA CM5 MATING CONNECTORS

J1: 100 physical contacts 2. INTERNAL POWER / STARTUP / RECOVERY SERVICE

U13-A: 100 contacts + official grounded module pads 201-204

3.3 V UART only; keyed factory/debug cable.

Internal keyed service header; never exposed on the top panel. 3. OWNERSHIP AUDIT

76 / 76 contacts owned; 74 connected, 2 assigned NC, 0 duplicate physical-pin claims. WAN1 uses native MDI. PCIe Gen2 x1 feeds the packet switch. WWAN owns USB30_2 + USB20_HOST0; touch owns USB20_HOST1. HDMI_TX0, I2S0 TDM, I2S1 headset, I2C7, I2C3 and UART2 are reserved exactly once. Pin 145 reaches HDMI pin 14; pin 147 is assigned NC because HEAC/ARC is unused. U13-B pin 106 receives IO_5V0. Unused alternate-function contacts carry explicit no-connect markers on this A1 baseline.

DETAILED CAPTURE BASELINE - verify CM5 voltage limits before release
U33-A includes the four official grounded CM5 mounting pads; allocated GPIO domain is 3.3 V
76 contacts are owned: 74 connected and 2 assigned no-connect; all other functions are no-connect
Three DF40C-100DS mates; pad geometry and relative placement come from Radxa IO V2.20

Sheet: /CM5 Core / Allocated Pins/
File: CM5-Core-Allocated.kicad_sch
Title: Radxa CM5 ProComm Carrier - Exact CM5 Connector Allocation

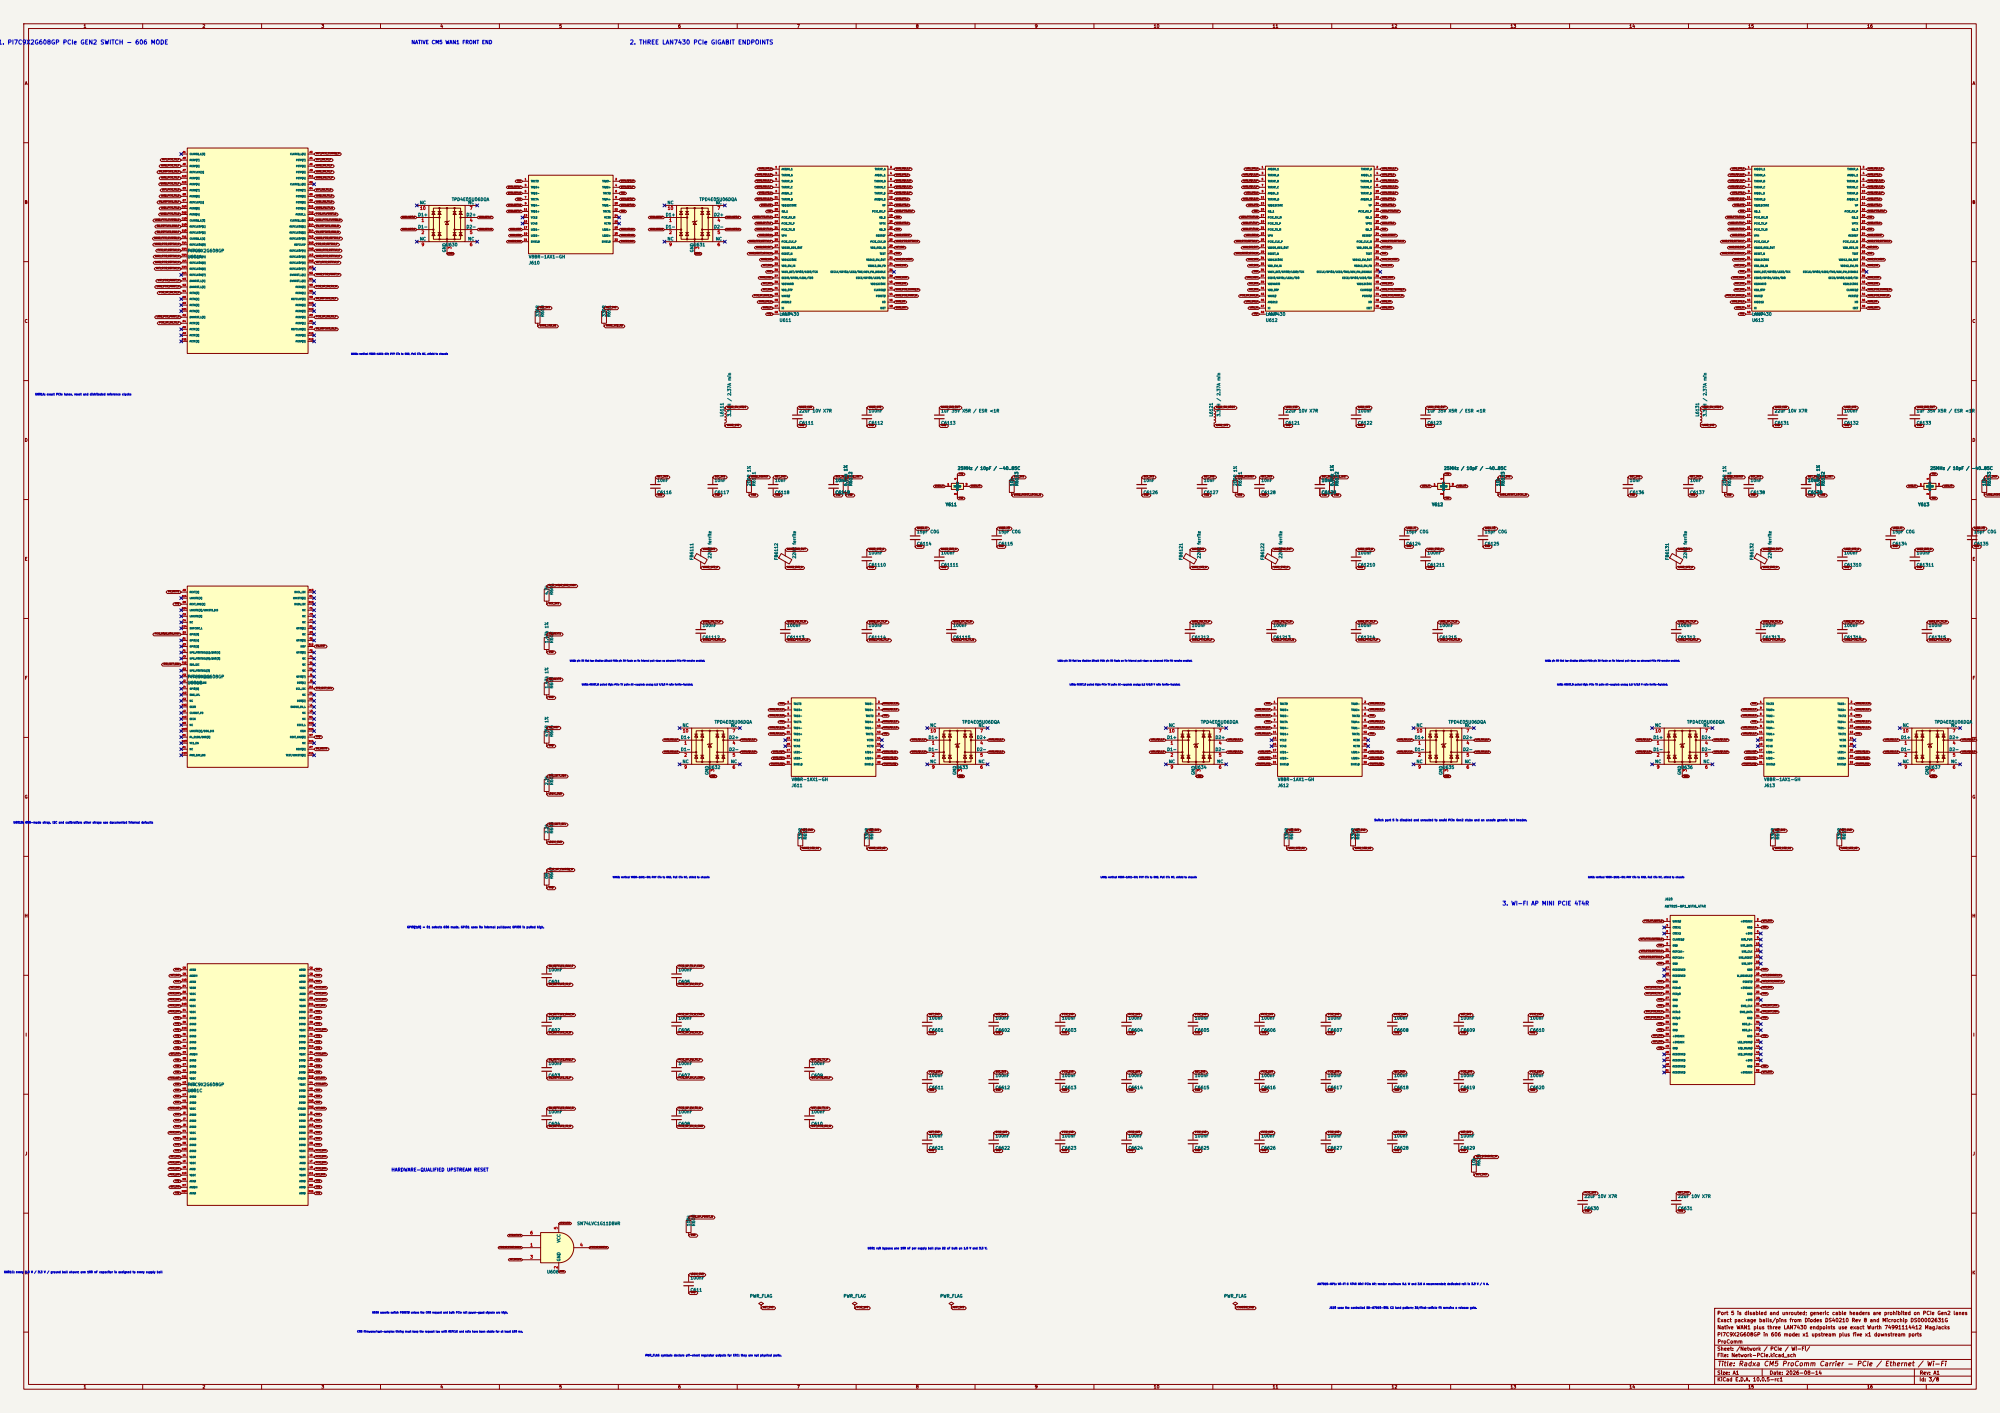
[picture p63: page 3]

2. THREE LAN7430 PCIe GIGABIT ENDPOINTS

WAN2: pin 35 tied low disables D3cold PME; pin 36 floats on its internal pull-down so advanced PCIe PM remains enabled.

LAN1: pin 35 tied low disables D3cold PME; pin 36 floats on its internal pull-down so advanced PCIe PM remains enabled.

LAN2: pin 35 tied low disables D3cold PME; pin 36 floats on its internal pull-down so advanced PCIe PM remains enabled.

WAN2: RESET_N pulled high; PCIe TX pairs AC-coupled; analog 1.2 V/2.5 V rails ferrite-isolated.

LAN1: RESET_N pulled high; PCIe TX pairs AC-coupled; analog 1.2 V/2.5 V rails ferrite-isolated.

LAN2: RESET_N pulled high; PCIe TX pairs AC-coupled; analog 1.2 V/2.5 V rails ferrite-isolated.

U601B: 606-mode strap, I2C and calibration; other straps use documented internal defaults

LAN2: vertical V8BR-1AX1-GH; PHY CTs to GND, PoE CTs NC, shield to chassis Switch port 5 is disabled and unrouted to avoid PCIe Gen2 stubs and an unsafe generic test header.

LAN1: vertical V8BR-1AX1-GH; PHY CTs to GND, PoE CTs NC, shield to chassis

3. WI-FI AP MINI PCIE 4T4R

HARDWARE-QUALIFIED UPSTREAM RESET

AW7915-NP1: Wi-Fi 6 4T4R Mini PCIe AP; vendor maximum 9.1 W and 3.5 A recommended; dedicated rail is 3.3 V / 4 A. J620 uses the controlled SD-67910-001 C2 land pattern; 3D/first-article fit remains a release gate.

Port 5 is disabled and unrouted; generic cable headers are prohibited on PCIe Gen2 lanes
Exact package balls/pins from Diodes DS40210 Rev 8 and Microchip DS00002631G
Native WAN1 plus three LAN7430 endpoints use exact Wurth 74991114412 MagJacks
PI7C9X2G608GP in 606 mode: x1 upstream plus five x1 downstream ports

Sheet: /Network / PCIe / Wi-Fi/
File: Network-PCIe.kicad_sch
Title: Radxa CM5 ProComm Carrier - PCIe / Ethernet / Wi-Fi

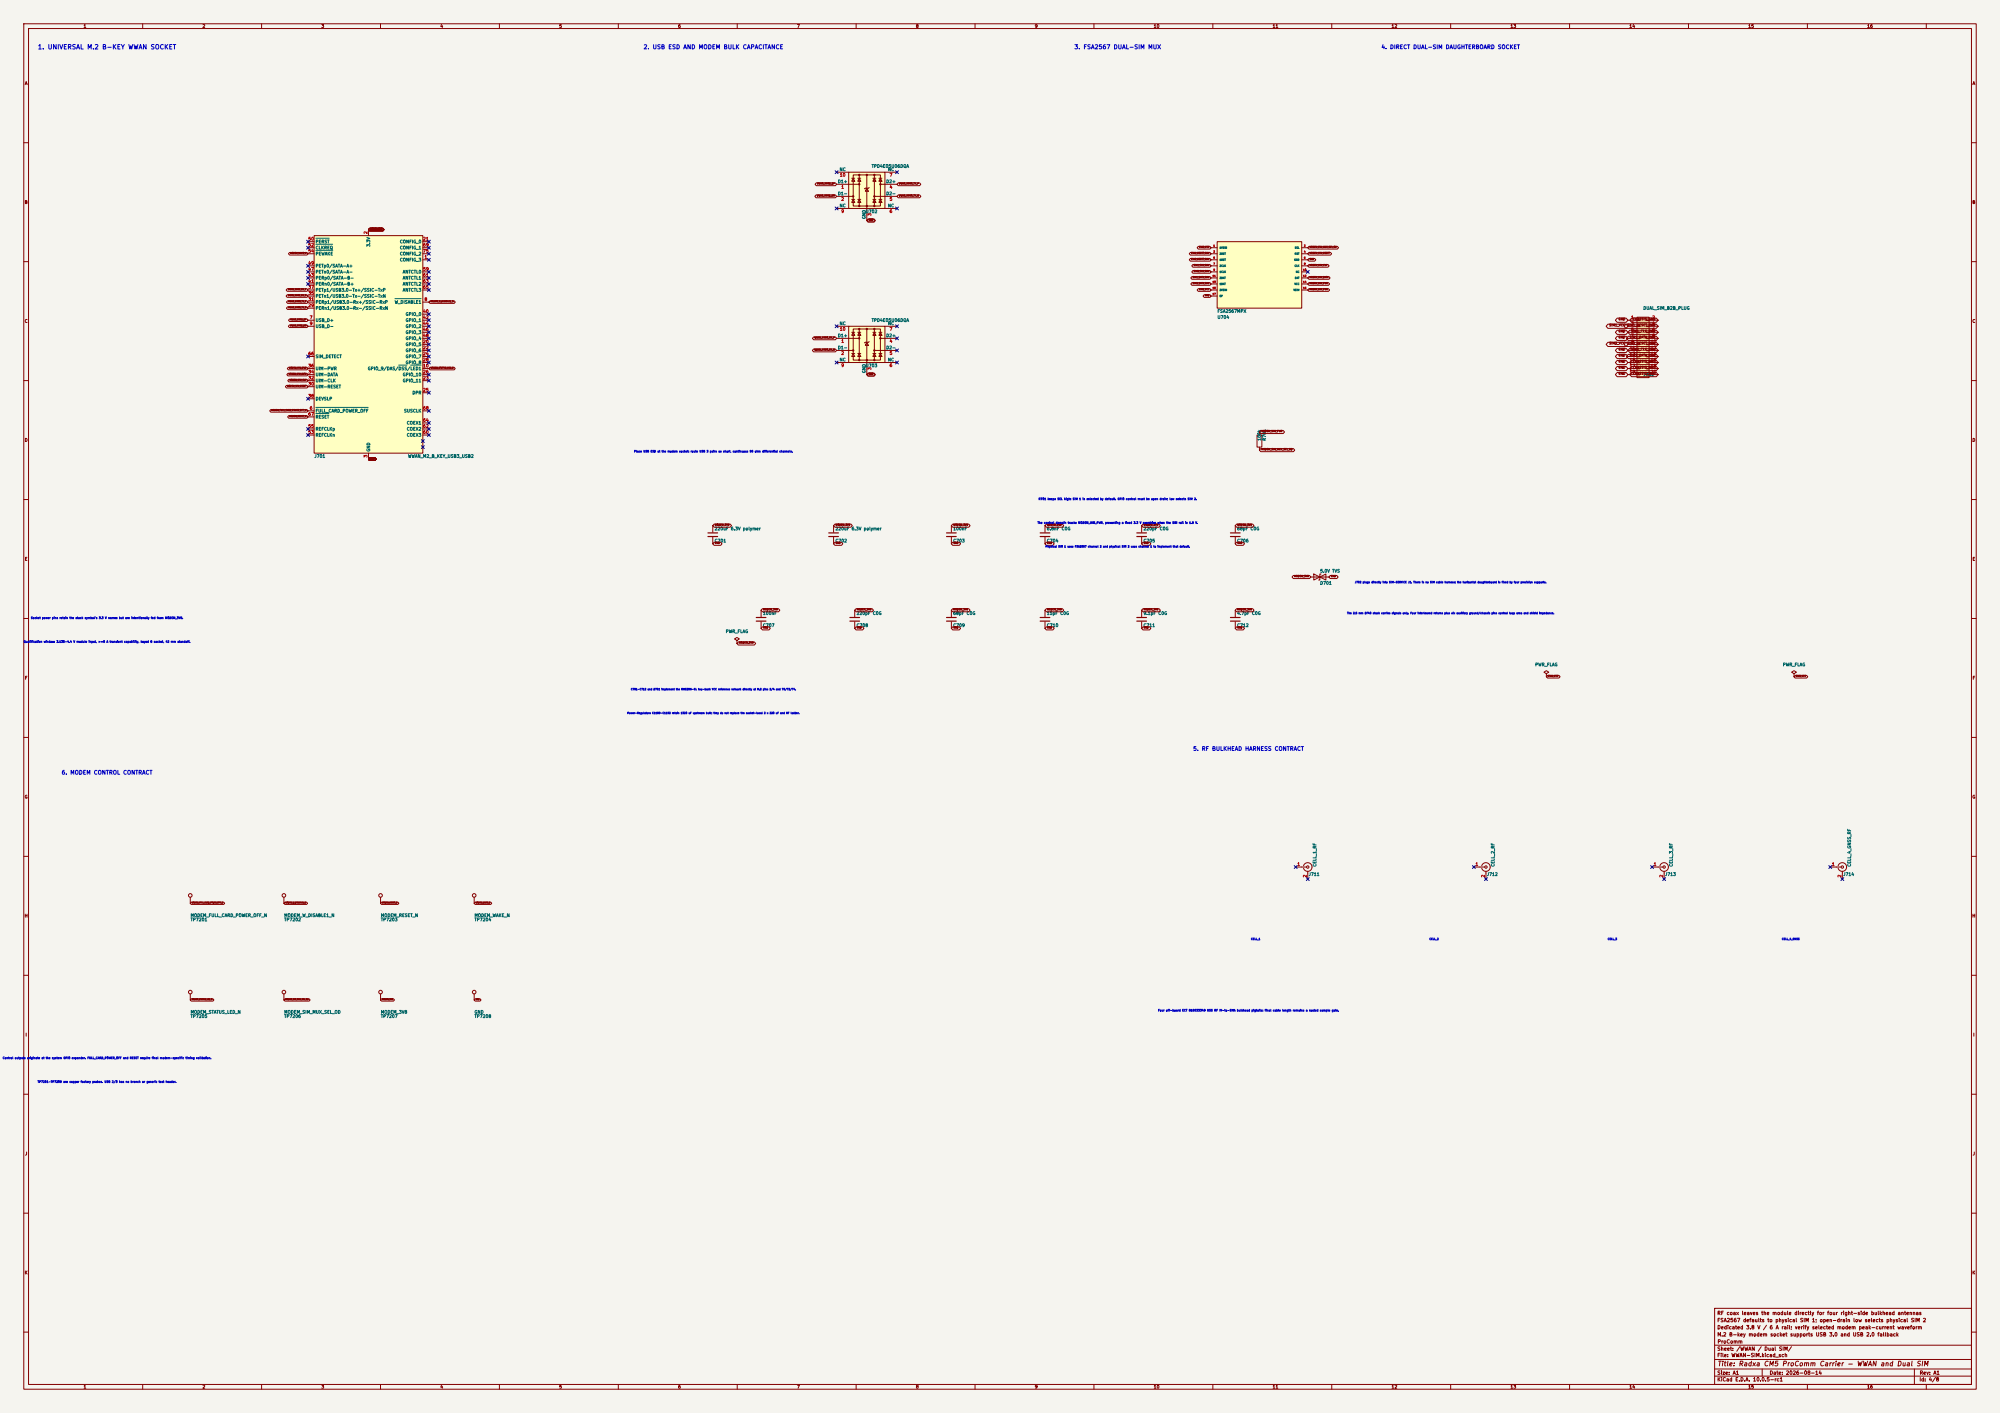
[picture p64: page 4]

4. DIRECT DUAL-SIM DAUGHTERBOARD SOCKET

R701 keeps SEL high: SIM 1 is selected by default. GPIO control must be open drain; low selects SIM 2.

Socket power pins retain the stock symbol's 3.3 V names but are intentionally fed from MODEM_3V8.

Power-Regulators C1189-C1192 retain 1320 uF upstream bulk; they do not replace the socket-local 2 x 220 uF and HF ladder. C701-C712 and D701 implement the RM520N-GL two-bank VCC reference network directly at M.2 pins 2/4 and 70/72/74. Qualification window: 3.135-4.4 V module input, >=5 A transient capability, keyed B socket, 42 mm standoff.

Four off-board ECT 818033349 USS RF IV-to-SMA bulkhead pigtails; final cable length remains a routed sample gate.

TP7201-TP7208 are copper factory probes. USB 2/3 has no branch or generic test header. Control outputs originate at the system GPIO expander. FULL_CARD_POWER_OFF and RESET require final modem-specific timing validation.

RF coax leaves the module directly for four right-side bulkhead antennas
FSA2567 defaults to physical SIM 1; open-drain low selects physical SIM 2
Dedicated 3.8 V / 6 A rail; verify selected modem peak-current waveform
M.2 B-key modem socket supports USB 3.0 and USB 2.0 fallback

Sheet: /WWAN / Dual SIM/
File: WWAN-SIM.kicad_sch
Title: Radxa CM5 ProComm Carrier - WWAN and Dual SIM

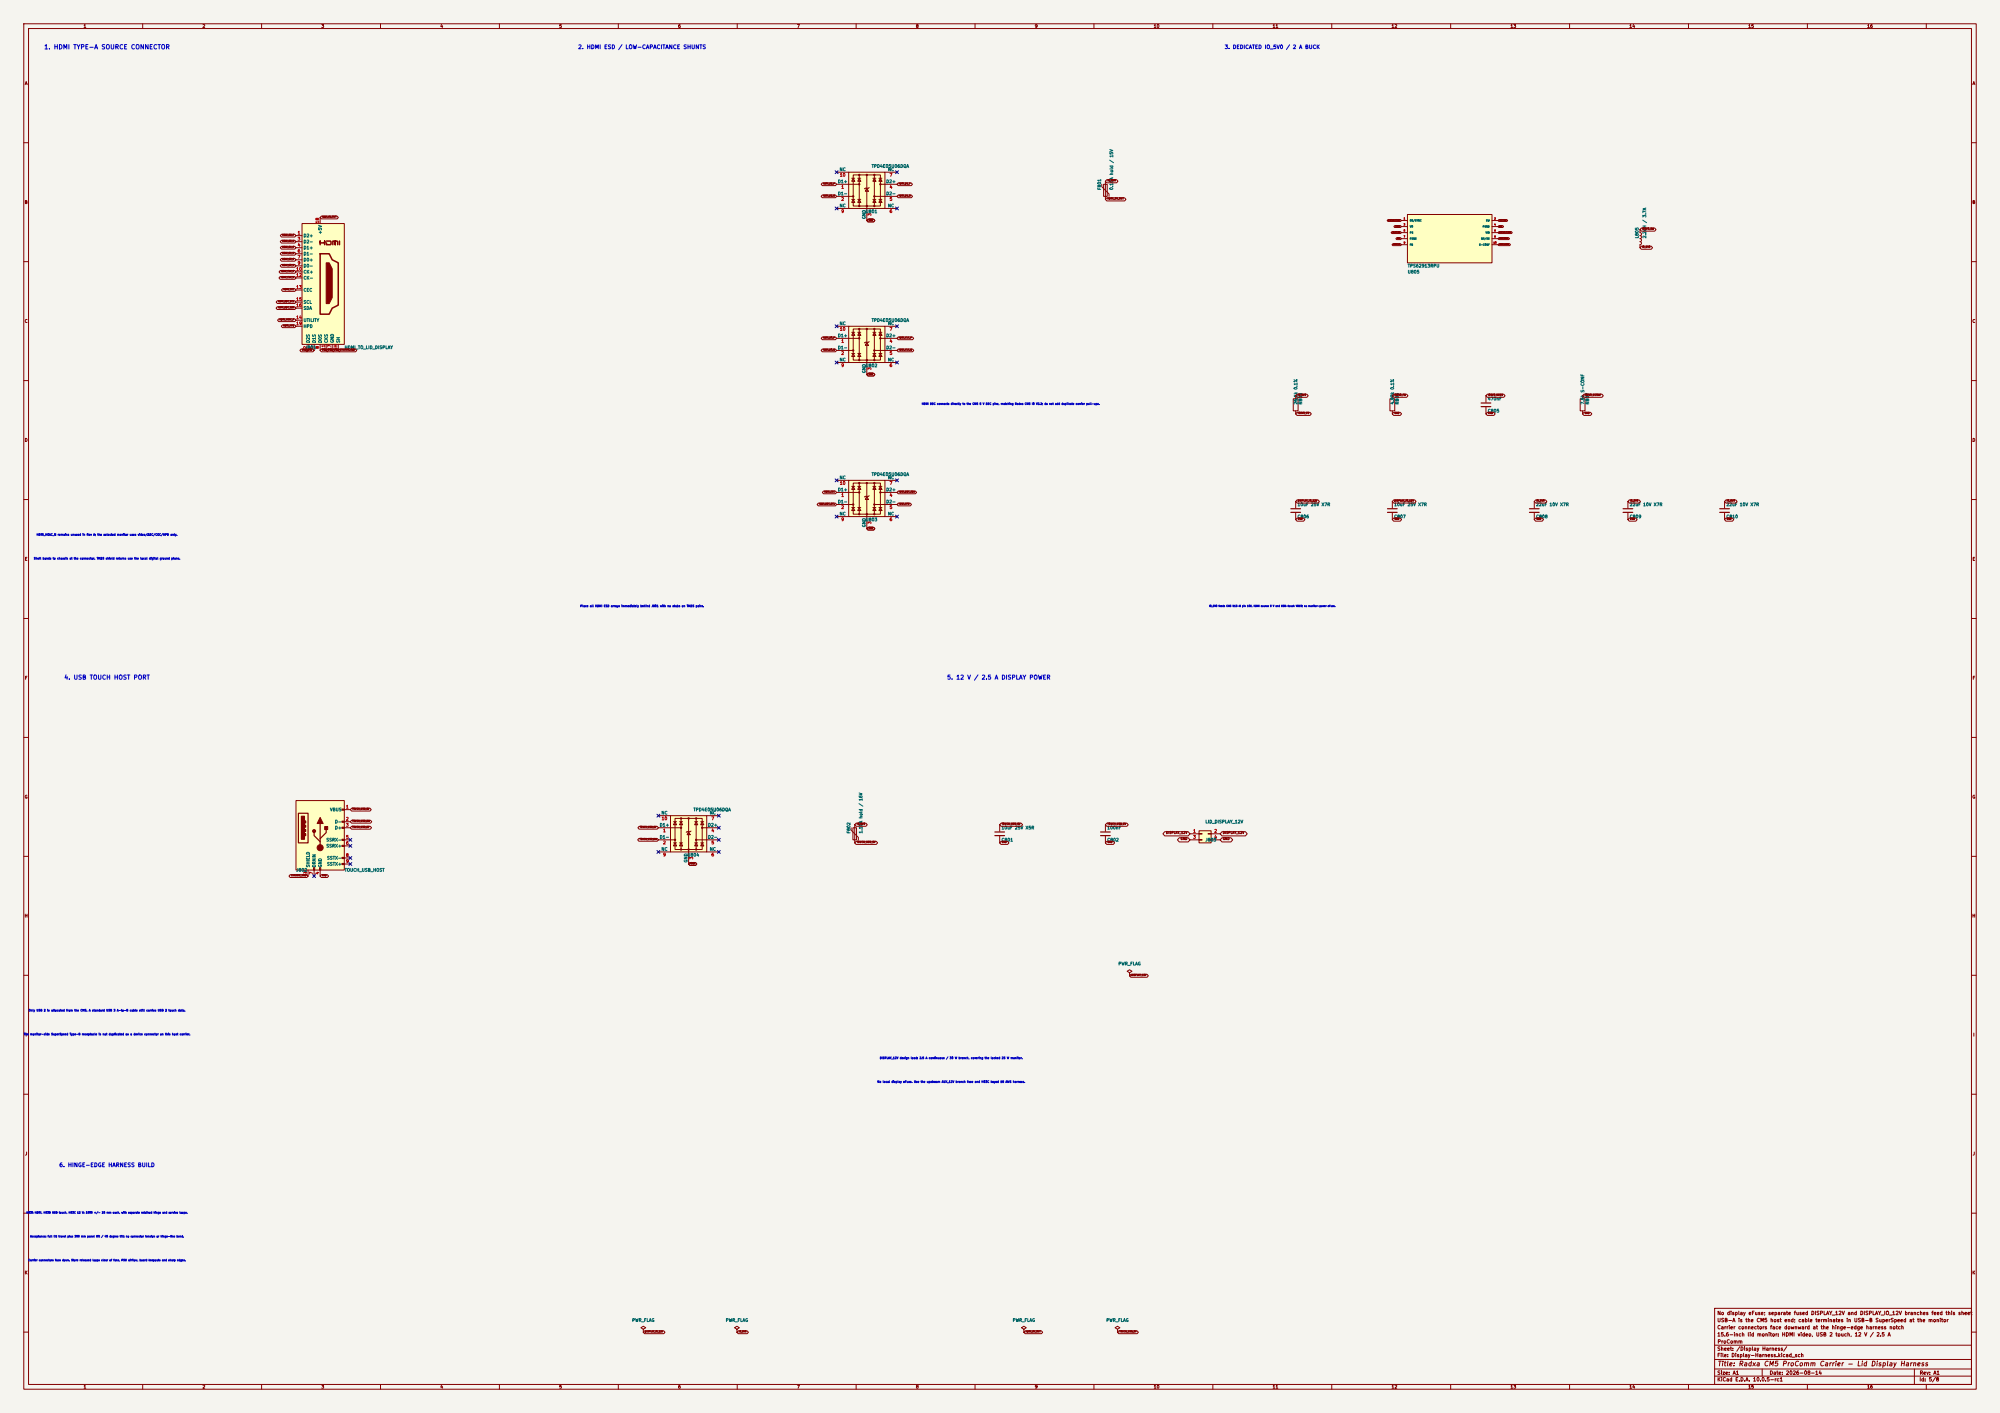
[picture p65: page 5]

2. HDMI ESD / LOW-CAPACITANCE SHUNTS

8 D0- 9 CK+ 10 CKS 11 CK- 12 CEC 13 UTILITY 14

IO_5V0 feeds CM5 U13-B pin 106, HDMI source 5 V and USB-touch VBUS; no monitor-power eFuse.

No local display eFuse. Use the upstream AUX_12V branch fuse and H03C keyed 18 AWG harness.

H03A HDMI, H03B USB touch, H03C 12 V: 1000 +/- 25 mm each, with separate retained hinge and service loops. Acceptance: full lid travel plus 300 mm panel lift / 45 degree tilt; no connector tension or hinge-line bend. Carrier connectors face down. Store released loops clear of fans, PSU airflow, board keepouts and sharp edges.

No display eFuse; separate fused DISPLAY_12V and DISPLAY_IO_12V branches feed this sheet
USB-A is the CM5 host end; cable terminates in USB-B SuperSpeed at the monitor
Carrier connectors face downward at the hinge-edge harness notch
15.6-inch lid monitor: HDMI video, USB 2 touch, 12 V / 2.5 A

Sheet: /Display Harness/
File: Display-Harness.kicad_sch
Title: Radxa CM5 ProComm Carrier - Lid Display Harness

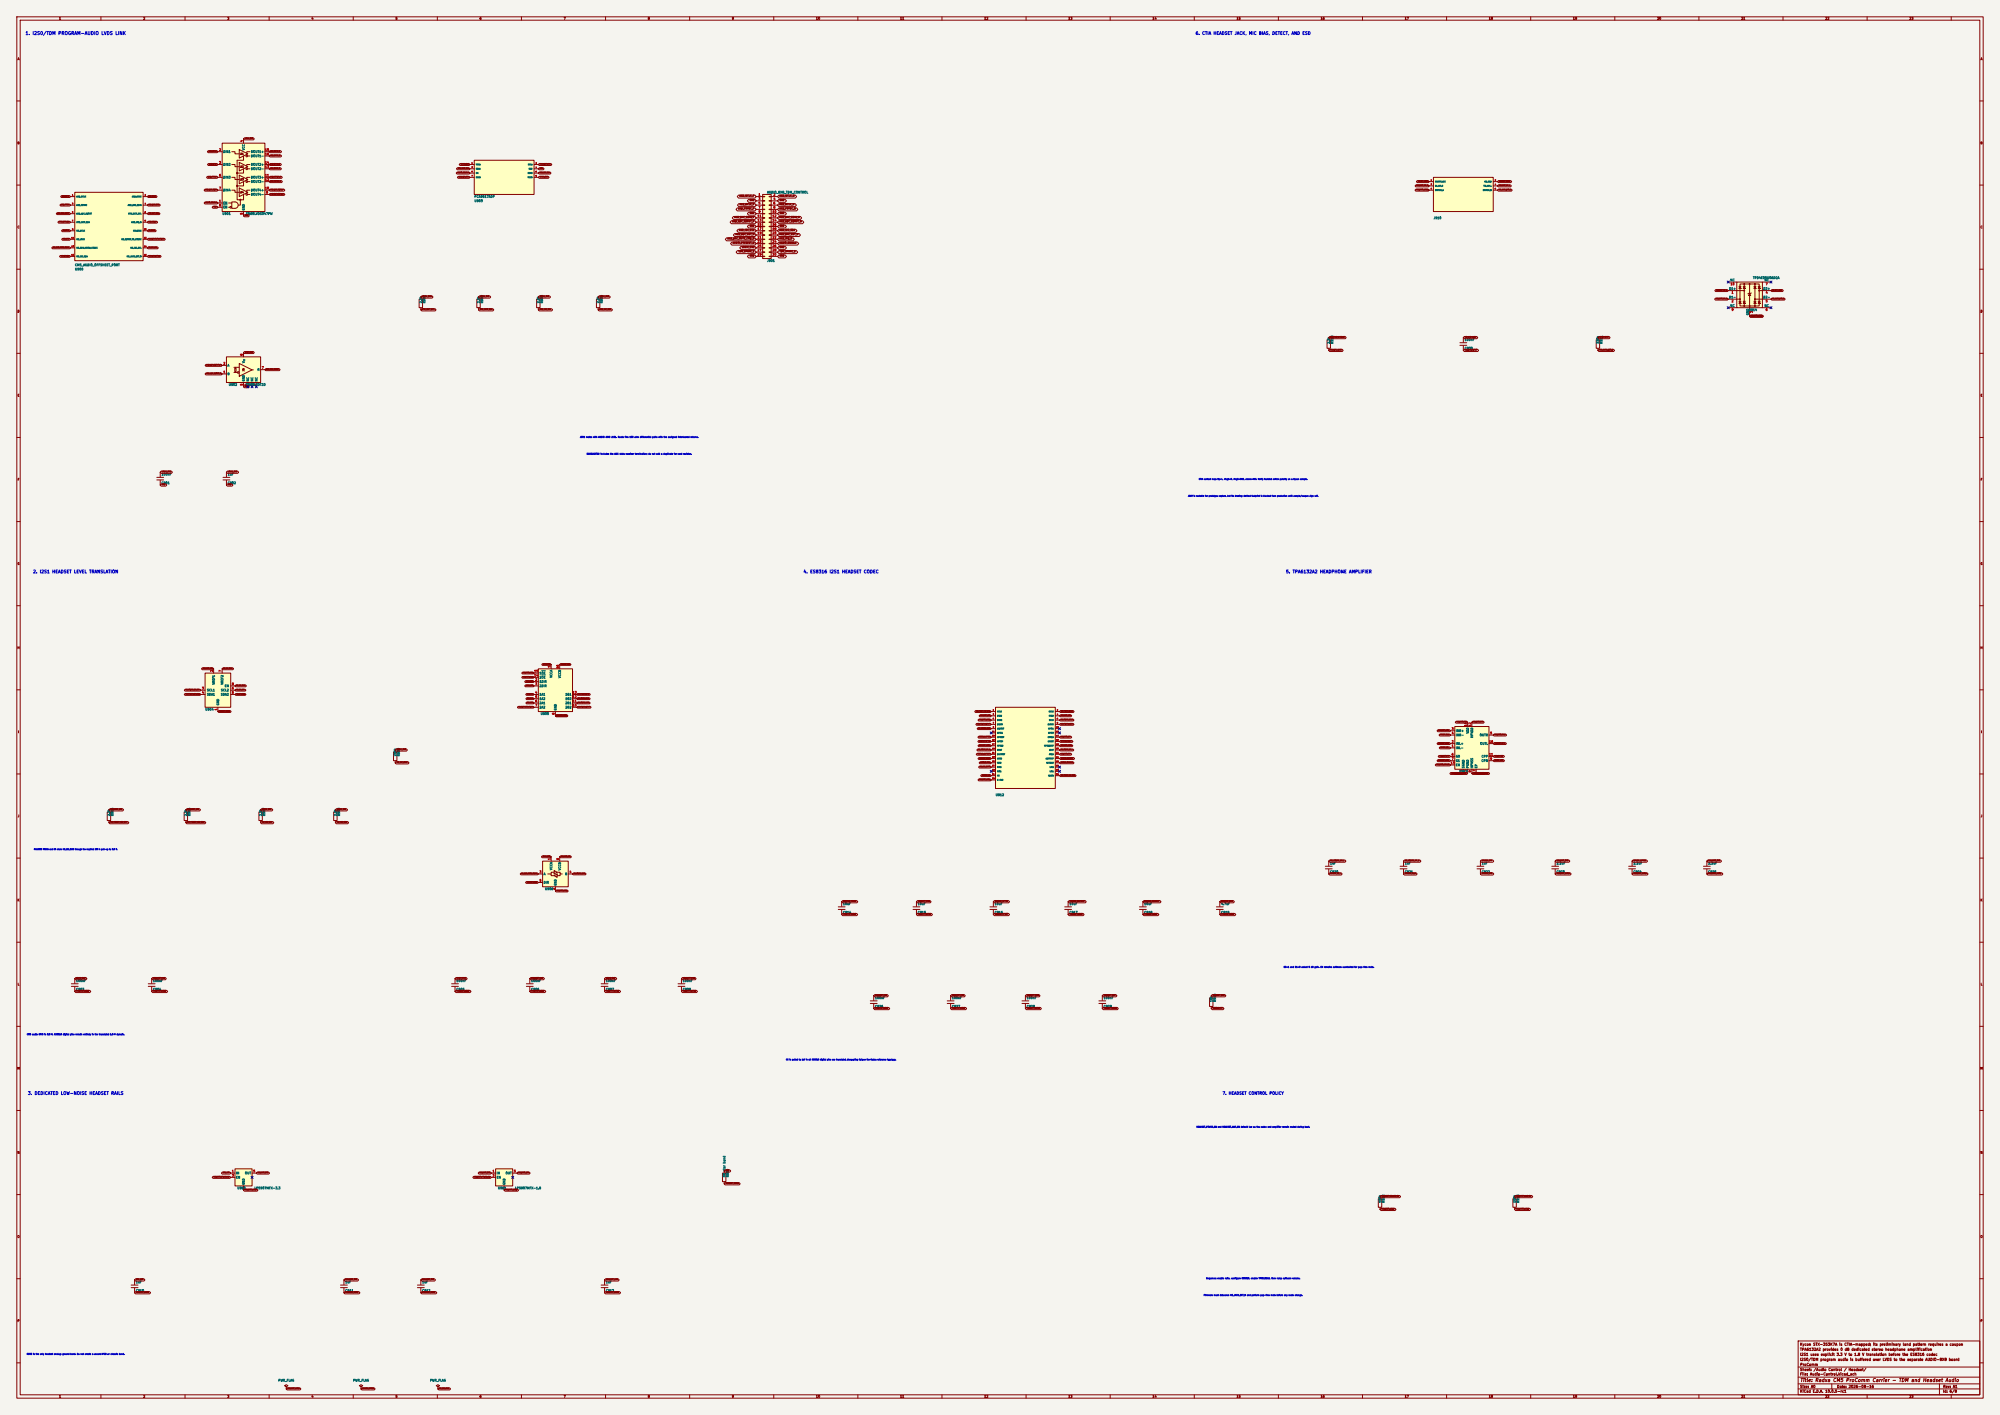
[picture p66: page 6]

1. I2S0/TDM PROGRAM-AUDIO LVDS LINK

6. CTIA HEADSET JACK, MIC BIAS, DETECT, AND ESD

Kycon STX-353K7A is CTIA-mapped; its preliminary land pattern requires a coupon 2.2k R907

CM5 audio GPIO is 3.3 V. ES8316 digital pins remain entirely in the translated 1.8 V domain.

CE is pulled to 1.8 V; all ES8316 digital pins are translated. Decoupling follows the Radxa reference topology.

3. DEDICATED LOW-NOISE HEADSET RAILS

HEADSET_POWER_EN and HEADSET_AMP_EN default low so the codec and amplifier remain muted during boot.

Sequence: enable rails, configure ES8316, enable TPA6132A2, then ramp software volume. Firmware must debounce HS_JACK_DET_N and perform pop-free mute before any route change.

TPA6132A2 provides 0 dB dedicated stereo headphone amplification
I2S1 uses explicit 3.3 V to 1.8 V translation before the ES8316 codec
I2S0/TDM program audio is buffered over LVDS to the separate AUDIO-8X8 board

R900 is the only headset analog-ground bond. Do not create a second PCB or chassis bond.

Sheet: /Audio Control / Headset/
File: Audio-Control.kicad_sch
Title: Radxa CM5 ProComm Carrier - TDM and Headset Audio

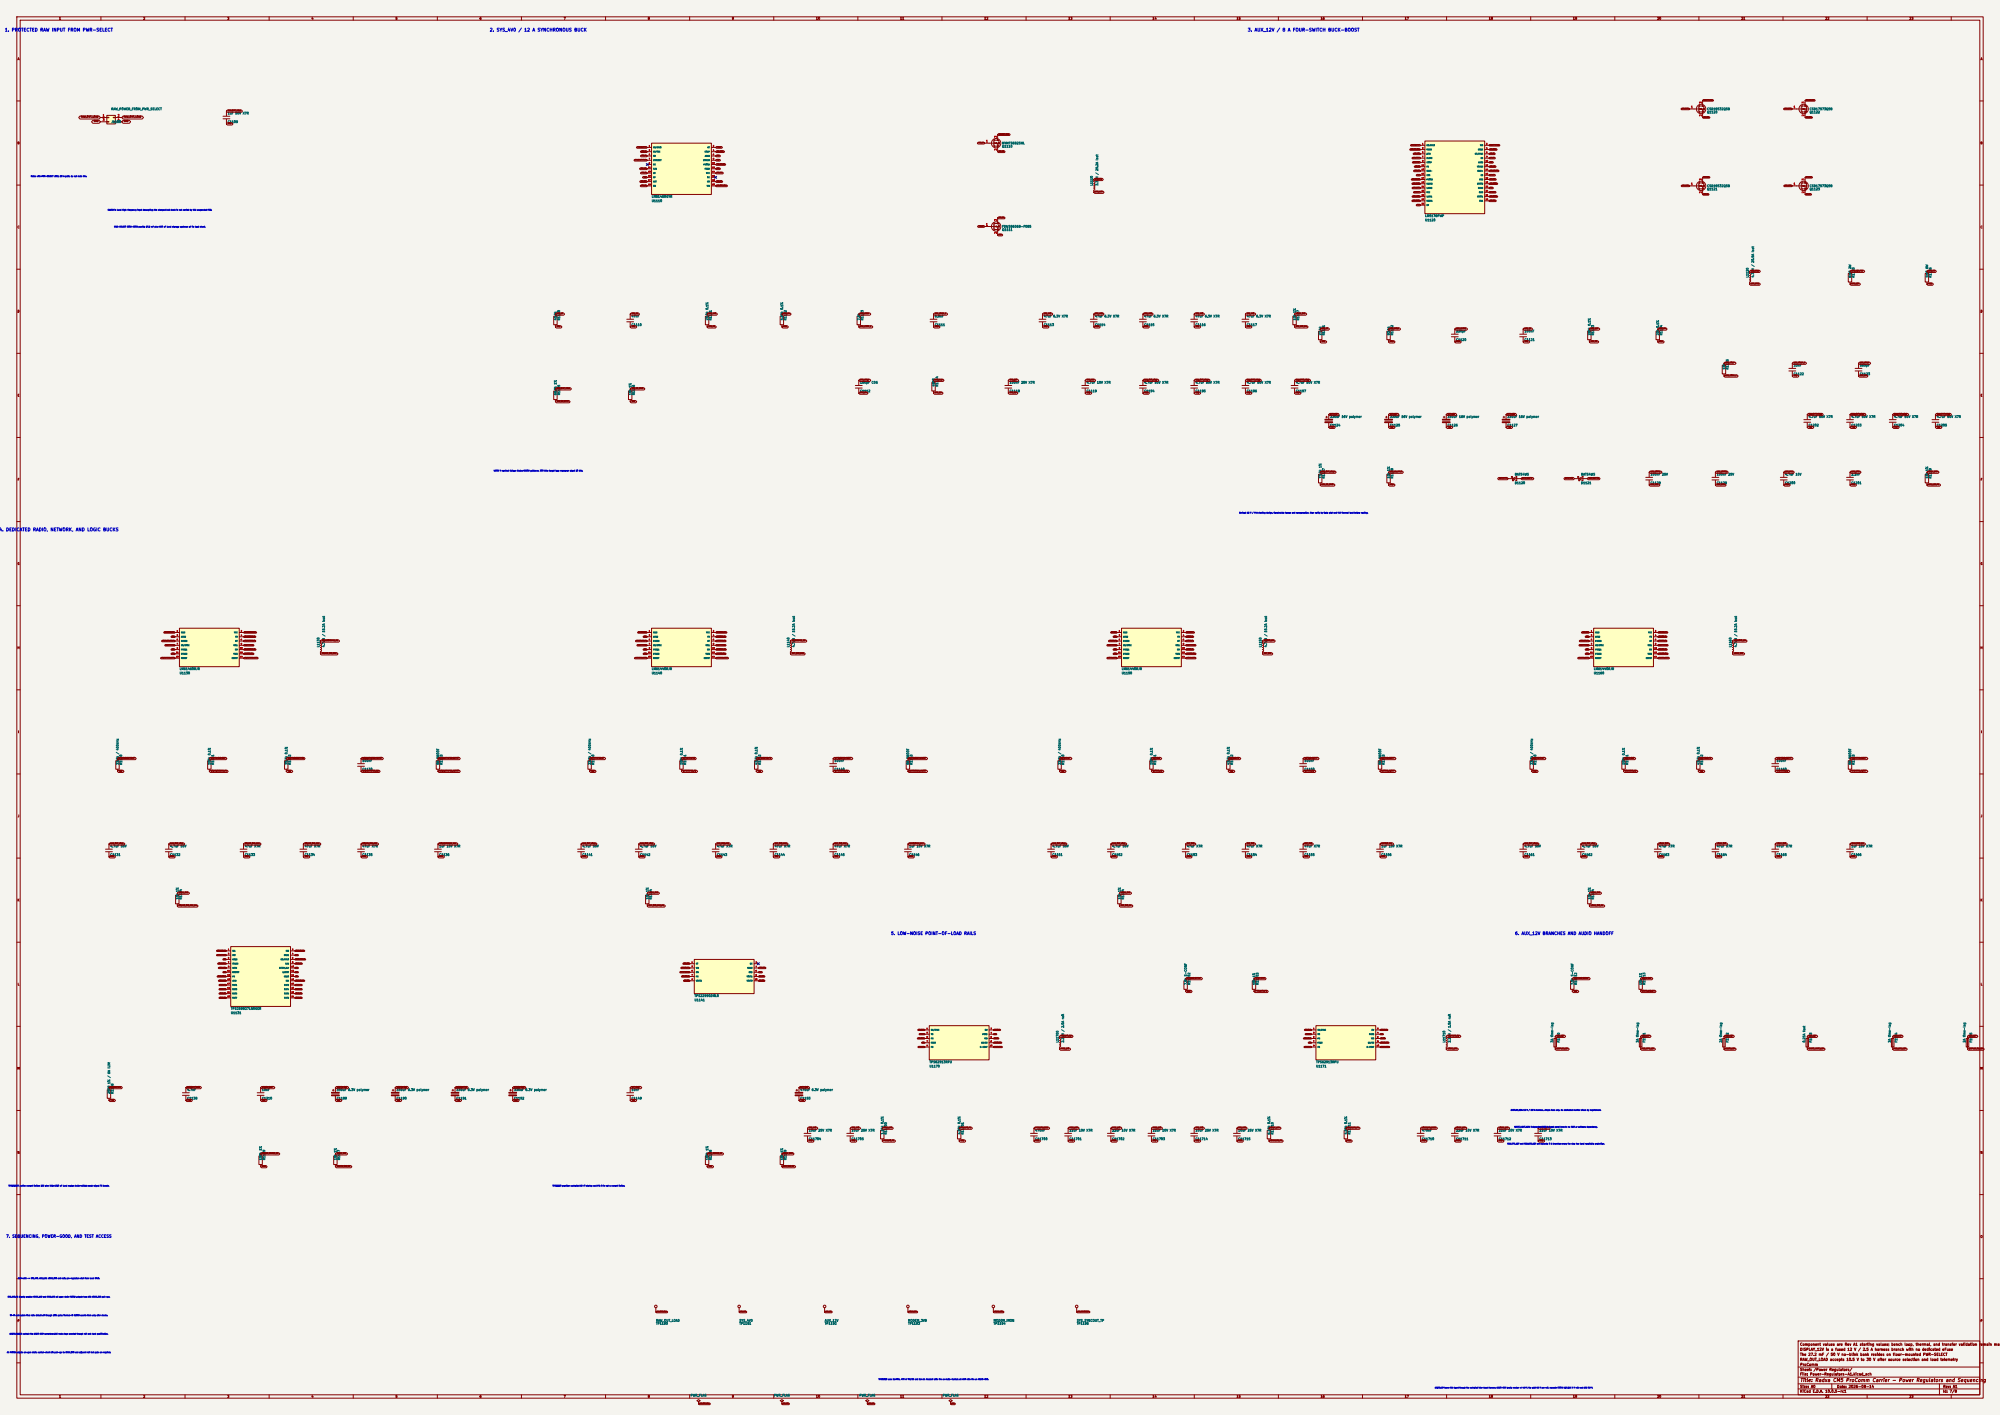
[picture p67: page 7]

Mates with PWR-SELECT J301; 15 A path; do not mate live. 1. PROTECTED RAW INPUT FROM PWR-SELECT

3. AUX_12V / 8 A FOUR-SWITCH BUCK-BOOST

AUX_LDRV2
Component values are Rev A1 starting values; bench loop, thermal, and transfer validation remain mandatory 6mR R11202W

C1109 is local high-frequency input decoupling; the clamped bulk bank is not carried by this suspended PCB. PWR-SELECT C306-C309 provide 27.2 mF plus 660 uF local storage upstream of its load shunt.

4.006 V nominal follows Radxa RK806 guidance. 300 kHz; target loop crossover about 20 kHz. 4. DEDICATED RADIO, NETWORK, AND LOGIC BUCKS

Revised 12 V / 8 A starting design. Recalculate losses and compensation, then verify by Bode plot and full thermal load before routing.

5. LOW-NOISE POINT-OF-LOAD RAILS

6. AUX_12V BRANCHES AND AUDIO HANDOFF

DISPLAY_12V: 12 V / 2.5 A harness, simple fuse only. No dedicated monitor eFuse by requirement. NIGHT_LIGHT_12V: independent 0.25 A fused panel branch; no CM5 or software dependency.

TPS259827L active current limiter; 255 ohm ILIM; 1320 uF local modem bulk; validate weak-signal TX bursts.

Wi-Fi and modem final rails default off through 100k pulls; Thermal-IO U1003 asserts them only after checks. SYS_4V0_PG directly enables LOGIC_1V8 and PCIE_1V0; all open-drain PGOOD outputs have 10k LOGIC_3V3 pull-ups. RAW valid -> SYS_4V0, AUX_12V, LOGIC_3V3 and radio pre-regulators start from local UVLO. 7. SEQUENCING, POWER-GOOD, AND TEST ACCESS

All PGOOD outputs are open drain; control-sheet 10k pull-ups to LOGIC_3V3 and adjacent rail test pads are required. AUDIO_ENABLE controls the AUDIO-8X8 converters; DAC mute stays asserted through rail and clock qualification.

DISPLAY_12V is a fused 12 V / 2.5 A harness branch with no dedicated eFuse
The 27.2 mF / 50 V no-blink bank resides on floor-mounted PWR-SELECT
RAW_OUT_LOAD accepts 10.5 V to 30 V after source selection and load telemetry

Sheet: /Power Regulators/
File: Power-Regulators-A1.kicad_sch
Title: Radxa CM5 ProComm Carrier - Power Regulators and Sequencing

TPS62913 uses 2.2 MHz, 470 nF NR/SS and 2.2 uH. Headset LDOs live on Audio-Control; all AKM rails live on AUDIO-8X8.

AUDIO_12V leaves this board through the controlled inter-board harness. AUDIO-8X8 locally creates +/-15 V, the quiet 5.5 V pre-rail, separate LT3045 ADC/DAC 5 V rails and AKM 3.3 V.

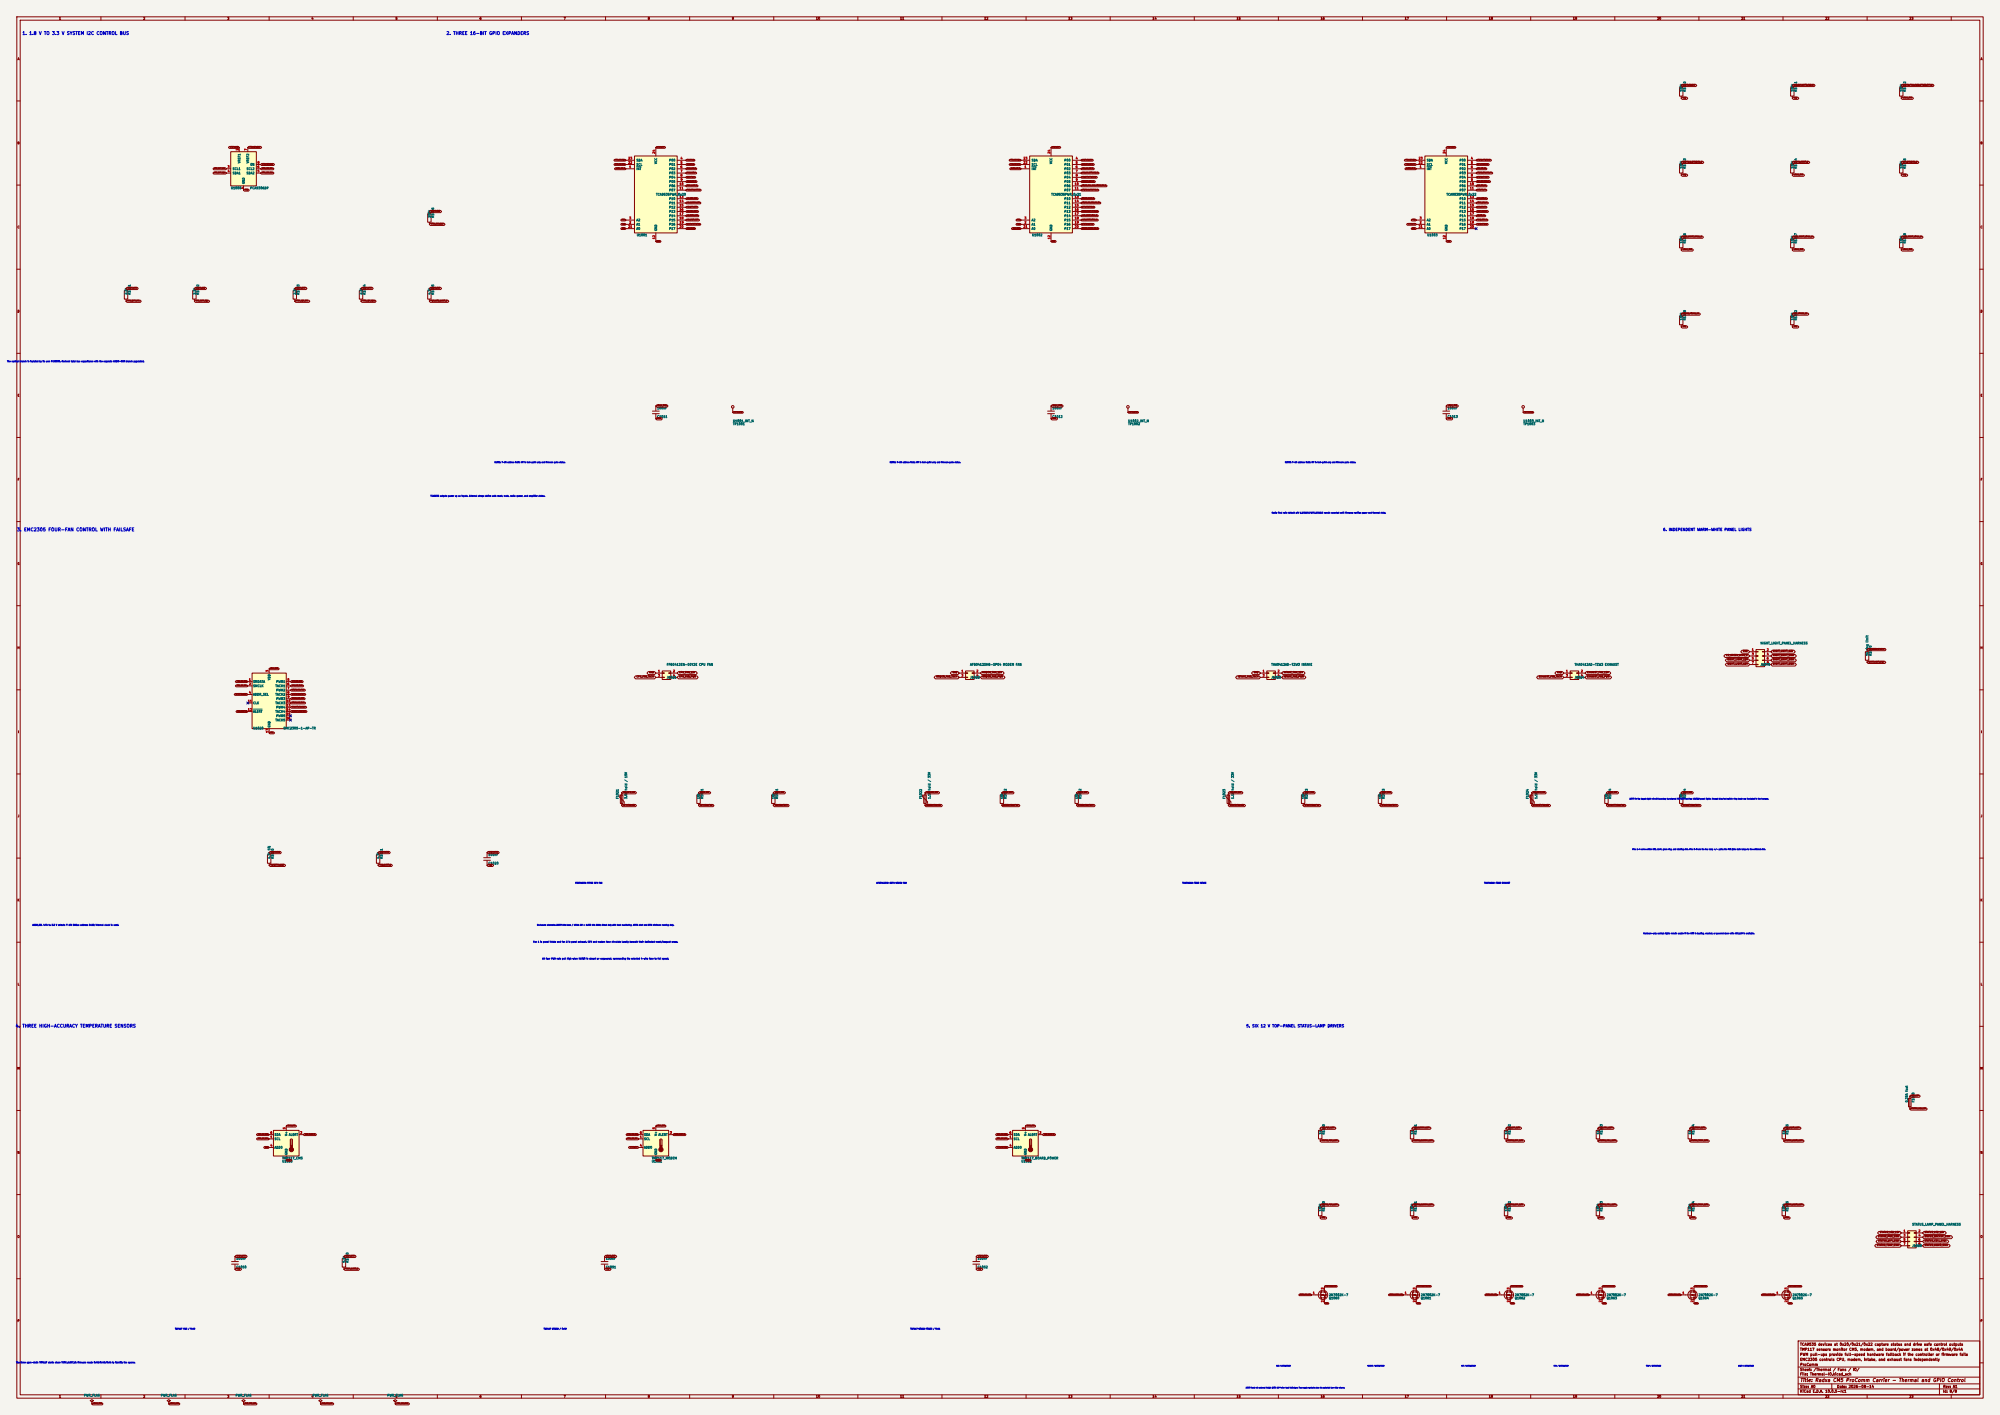
[picture p68: page 8]

1. 1.8 V TO 3.3 V SYSTEM I2C CONTROL BUS

2. THREE 16-BIT GPIO EXPANDERS

The control branch is isolated by its own PCA9306. Recheck total bus capacitance with the separate AUDIO-8X8 branch populated.

U1003: 7-bit address 0x22; INT is test-point only and firmware polls status. Radio final rails default off; W_DISABLE/WIFI_DISABLE remain asserted until firmware verifies power and thermal state.

J1070 is the keyed eight-circuit boundary to external CS7L2FR and two LS102W panel lights. Unused blue/red switch-ring leads are insulated in the harness. Pins 1-4 serve switch GND, 12 V, green ring, and latching sink. Pins 5-8 are the two lamp +/- pairs; the PCB joins both lamps to the switched sink.

Enclosure channels: 26.00 kHz base / divide 26 = 1.000 kHz PWM; direct duty with tach monitoring, 100% start and 30% minimum running duty.

Hardware-only control: lights remain usable if the CM5 is booting, crashed, or powered down while AUX_12V is available.

4. THREE HIGH-ACCURACY TEMPERATURE SENSORS

5. SIX 12 V TOP-PANEL STATUS-LAMP DRIVERS

TCA9535 devices at 0x20/0x21/0x22 capture status and drive safe control outputs
TMP117 sensors monitor CM5, modem, and board/power zones at 0x48/0x49/0x4A
PWM pull-ups provide full-speed hardware fallback if the controller or firmware fails
EMC2305 controls CPU, modem, intake, and exhaust fans independently

The three open-drain TMP117 alerts share TEMP_ALERT_N; firmware reads 0x48/0x49/0x4A to identify the source.

Sheet: /Thermal / Fans / IO/
File: Thermal-IO.kicad_sch
Title: Radxa CM5 ProComm Carrier - Thermal and GPIO Control
