omaralabed/Radxa-CM5-PCB/cad/kicad/SIM-SERVICE/REVIEW/Sim-Service-A1.pdf

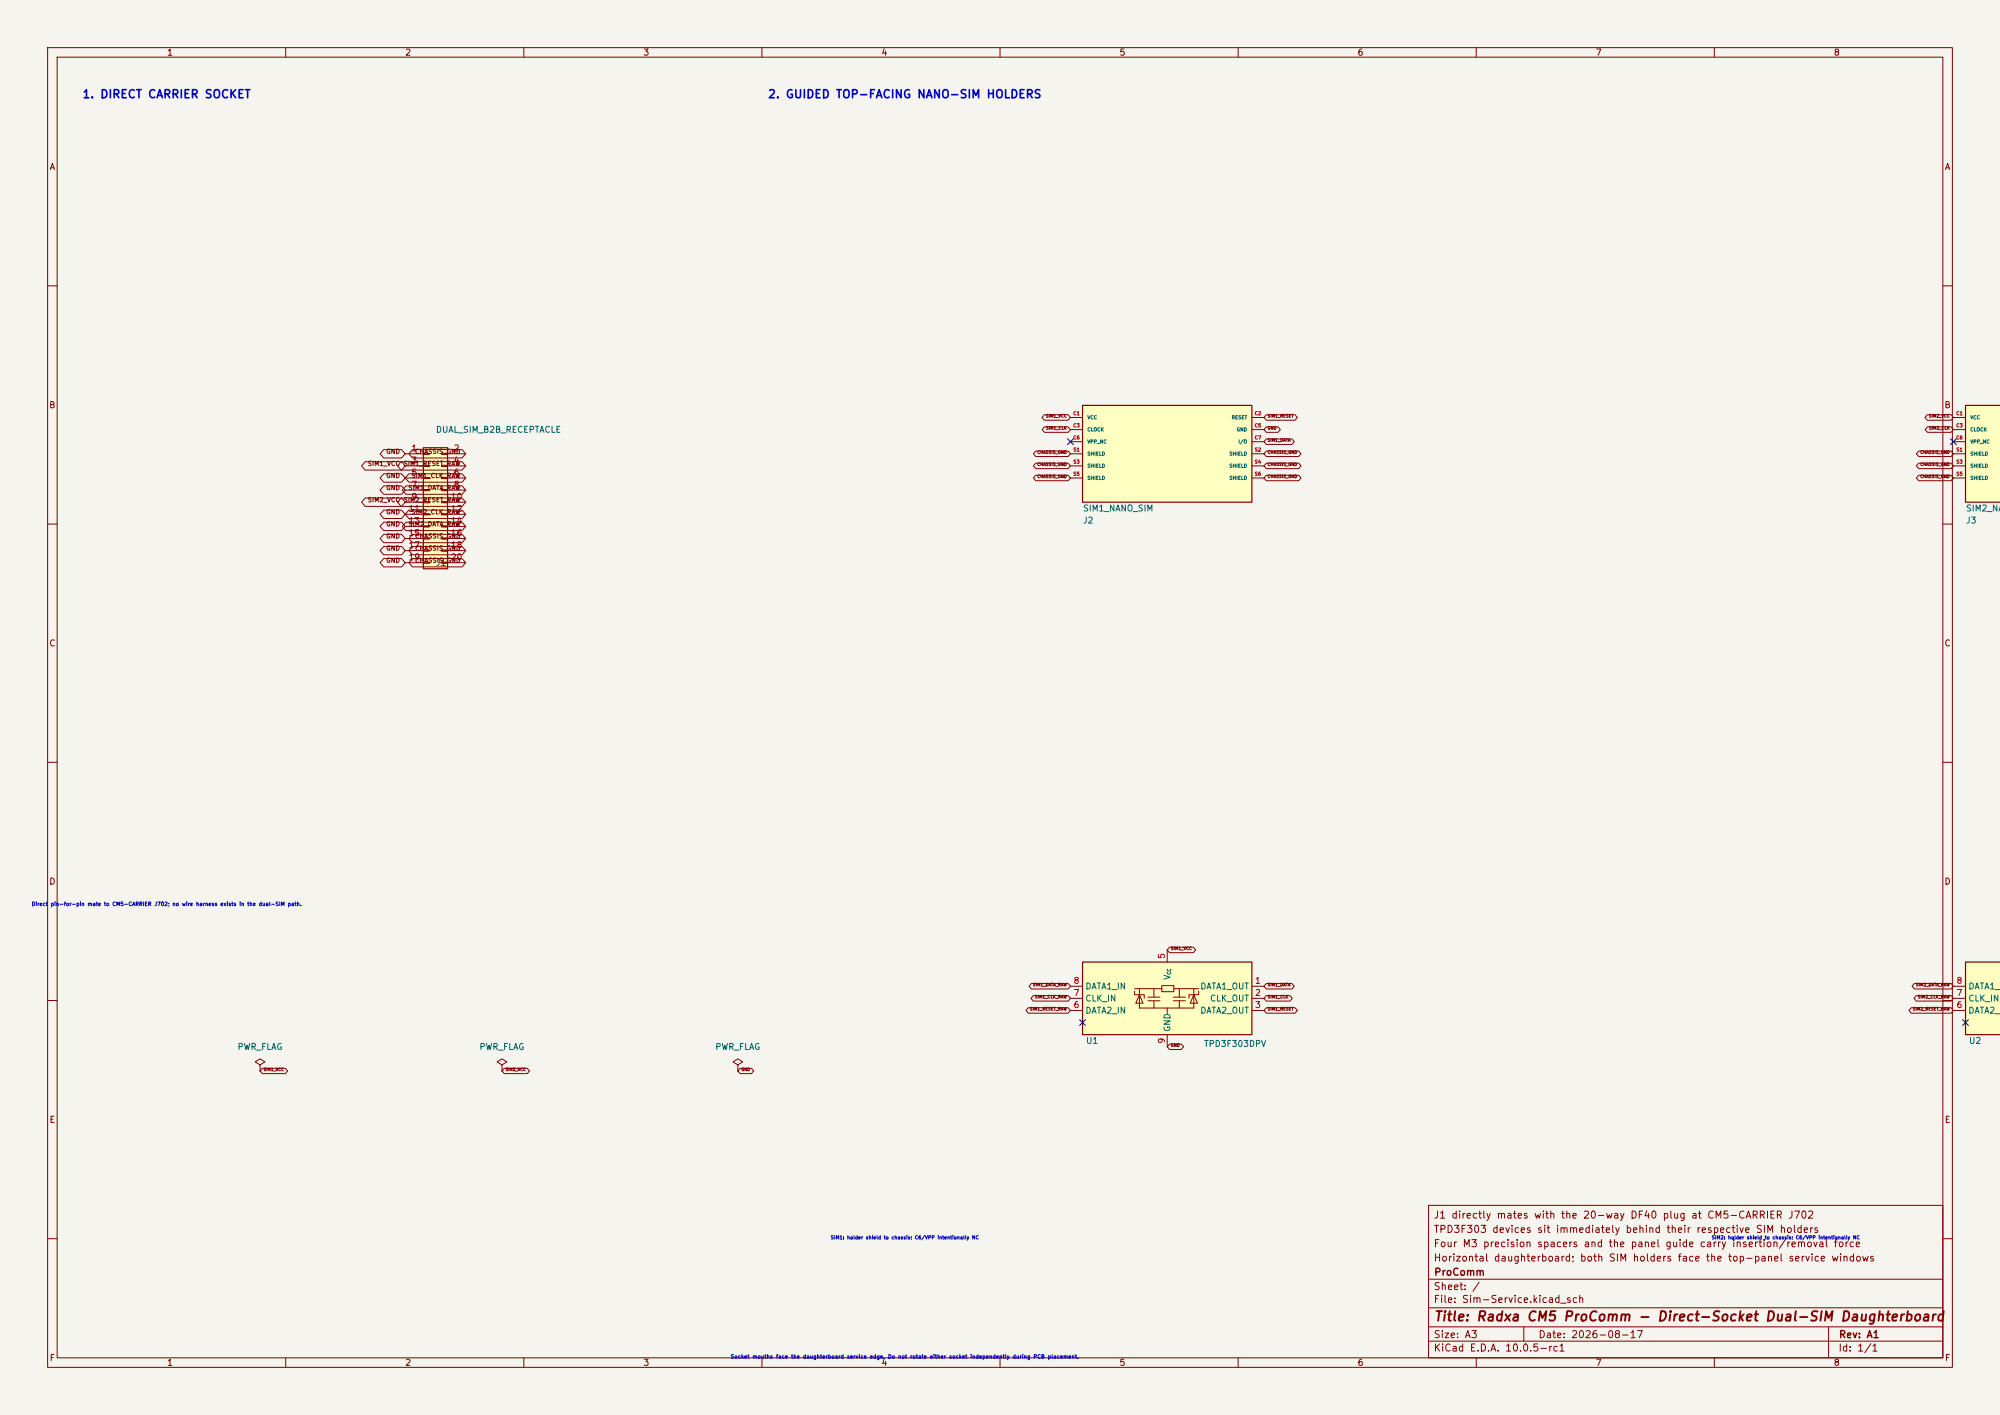
[picture p69: page 1]

2. GUIDED TOP-FACING NANO-SIM HOLDERS

Direct pin-for-pin mate to CM5-CARRIER J702; no wire harness exists in the dual-SIM path.

J1 directly mates with the 20-way DF40 plug at CM5-CARRIER J702
TPD3F303 devices sit immediately behind their respective SIM holders
Four M3 precision spacers and the panel guide carry insertion/removal force
Horizontal daughterboard; both SIM holders face the top-panel service windows
ProComm
Sheet: /
File: Sim-Service.kicad_sch
Title: Radxa CM5 ProComm - Direct-Socket Dual-SIM Daughterboard

Socket mouths face the daughterboard service edge. Do not rotate either socket independently during PCB placement. SIM1: holder shield to chassis; C6/VPP intentionally NC

SIM2: holder shield to chassis; C6/VPP intentionally NC

Size: A3 | Rev: A1 | F Date: 2026-08-17
KiCad E.D.A. 10.0.5-rc1 | Id: 1/1
