omaralabed/Radxa-CM5-PCB/cad/kicad/AUDIO-8X8/REVIEW/Audio-8x8-A1.pdf

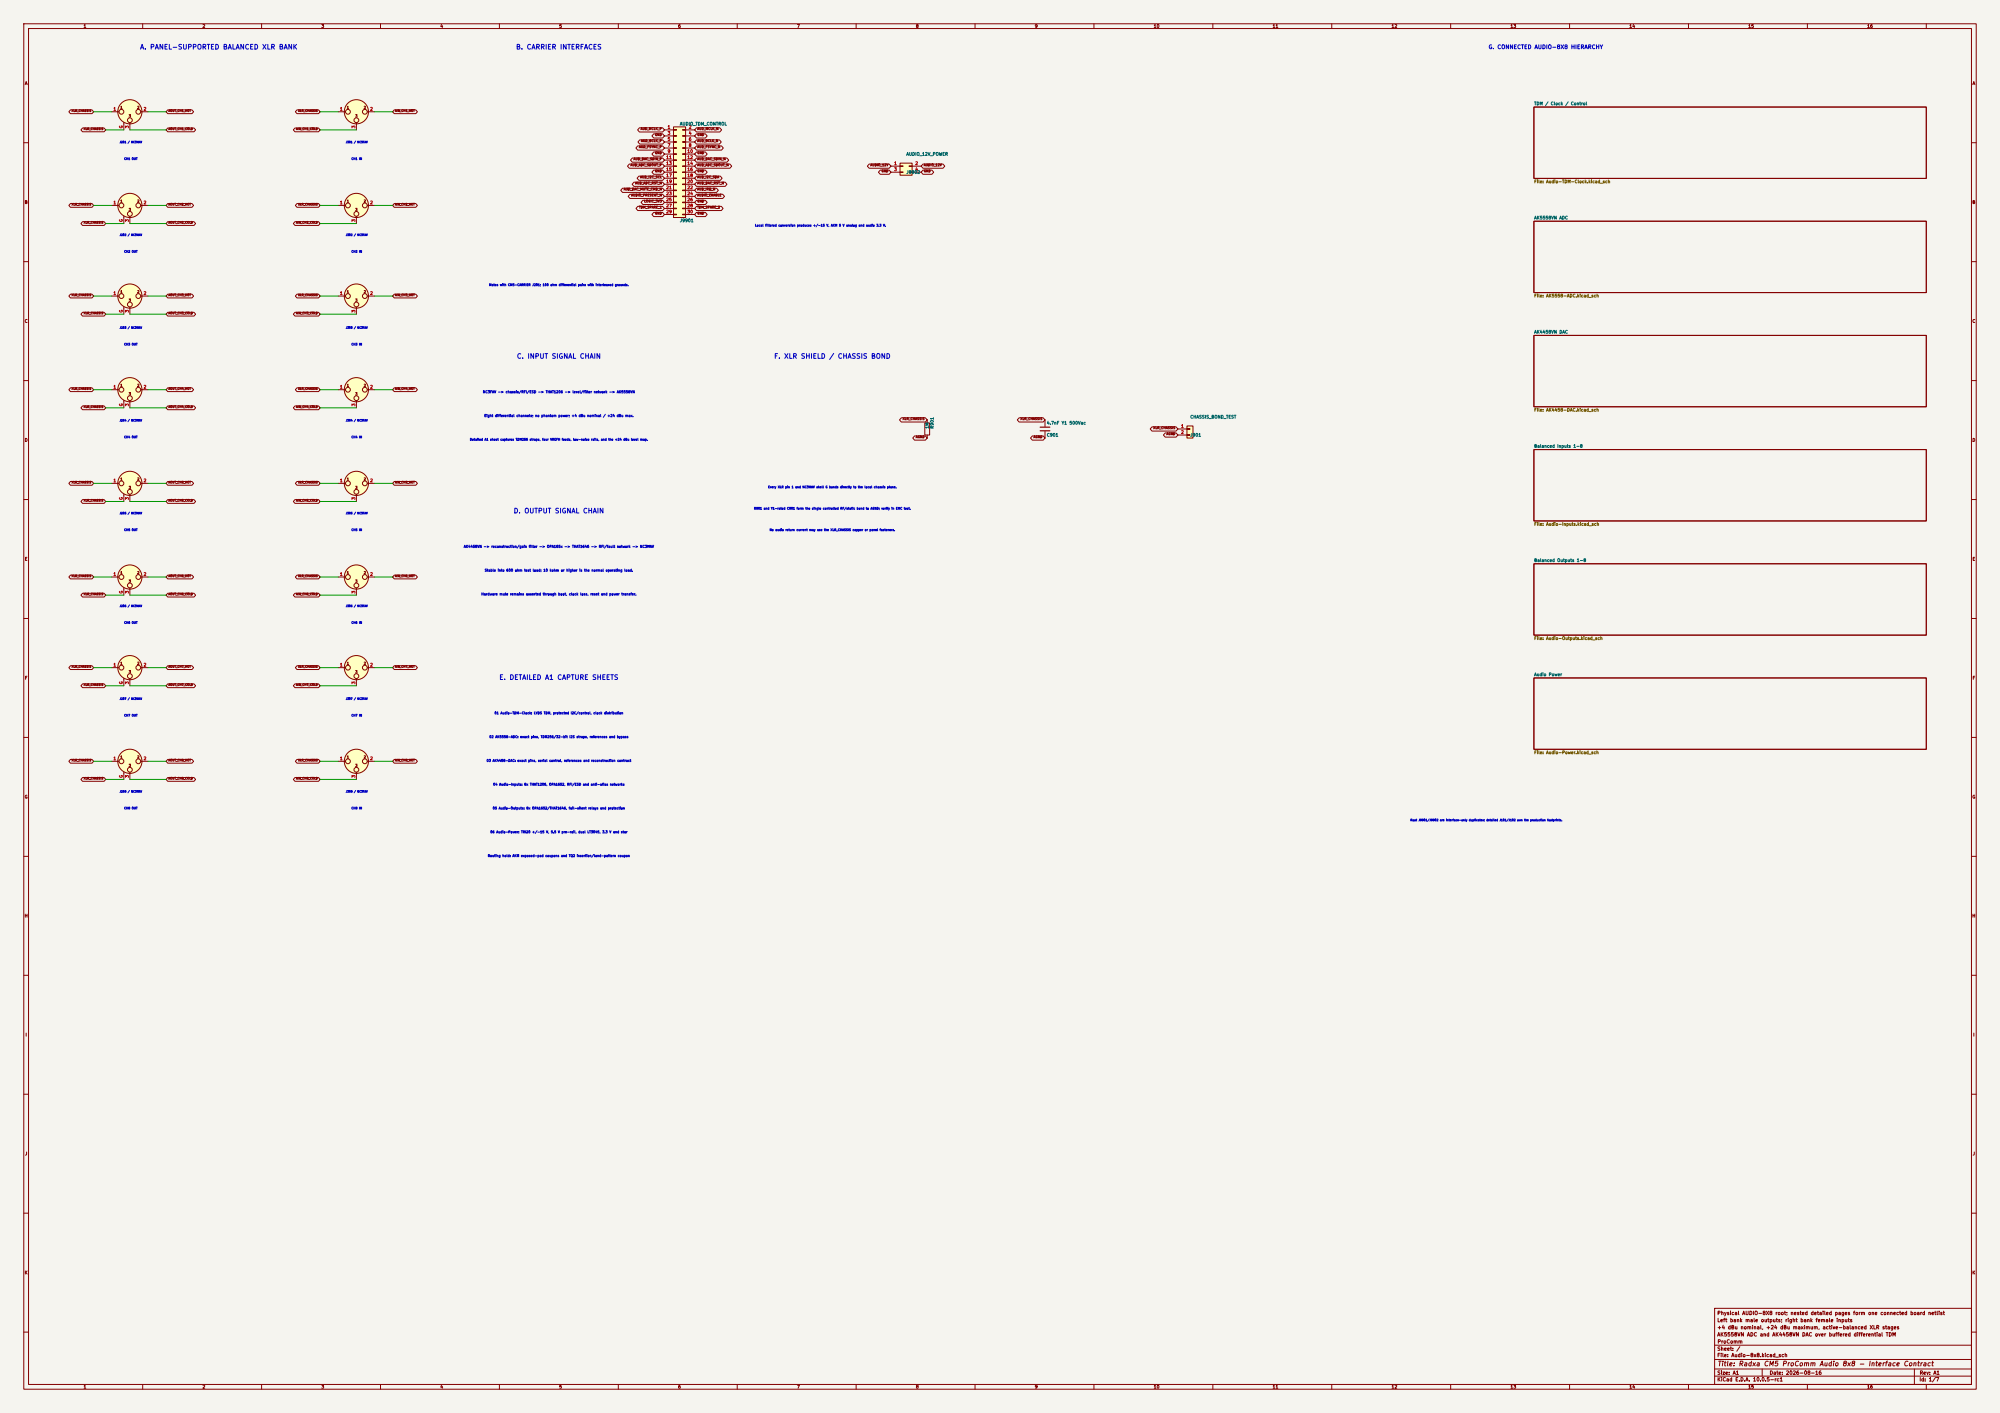
[picture p70: page 1]

A. PANEL-SUPPORTED BALANCED XLR BANK

TDM / Clock / Control File: Audio-TDM-Clock.kicad_sch

Local filtered conversion produces +/-15 V, AKM 5 V analog and audio 3.3 V.

AK4458VN DAC
File: Audio-Outputs.kicad_sch Balanced Inputs 1-8

Every XLR pin 1 and NC3MAV shell G bonds directly to the local chassis plane. R901 and Y1-rated C901 form the single controlled RF/static bond to AGND; verify in EMC test. No audio return current may use the XLR_CHASSIS copper or panel fasteners. F. XLR SHIELD / CHASSIS BOND

Stable into 600 ohm test load; 10 kohm or higher is the normal operating load. AK4458VN -> reconstruction/gain filter -> OPA165x -> THAT1646 -> RFI/fault network -> NC3MAV D. OUTPUT SIGNAL CHAIN

File: Audio-Inputs.kicad_sch
Audio Power File: Audio-Power.kicad_sch Balanced Outputs 1-8

03 AK4458-DAC: exact pins, serial control, references and reconstruction contract 02 AK5558-ADC: exact pins, TDM256/32-bit I2S straps, references and bypass 01 Audio-TDM-Clock: LVDS TDM, protected I2C/control, clock distribution E. DETAILED A1 CAPTURE SHEETS

Routing hold: AKM exposed-pad coupons and TQ2 insertion/land-pattern coupon 06 Audio-Power: TRI20 +/-15 V, 5.5 V pre-rail, dual LT3045, 3.3 V and star 05 Audio-Outputs: 8x OPA1652/THAT1646, fail-silent relays and protection 04 Audio-Inputs: 8x THAT1206, OPA1652, RFI/ESD and anti-alias networks

Physical AUDIO-8X8 root; nested detailed pages form one connected board netlist
Left bank male outputs; right bank female inputs
+4 dBu nominal, +24 dBu maximum, active-balanced XLR stages
AK5558VN ADC and AK4458VN DAC over buffered differential TDM
ProComm
Sheet: /
File: Audio-8x8.kicad_sch
Title: Radxa CM5 ProComm Audio 8x8 - Interface Contract

Size: A1 | Rev: A1
KiCad E.D.A. 10.0.5-rc1 | Id: 1/7


FSYNC: integrated 110 ohm termination

5. HARDWARE FAIL-SILENT GATE

100 ohm differential; interleaved returns; no branch stubs
87832-6423 pin assignment is locked and matches CM5-CARRIER J901
One LVDS driver returns the ADC TDM data stream to the CM5 carrier
Four terminated LVDS receivers carry MCLK, BCLK, FSYNC, and DAC TDM data

Sheet: /TDM / Clock / Control/
File: Audio-TDM-Clock.kicad_sch
Title: ProComm AUDIO-8X8 - TDM, Clock, and Control Interface

U106 permits DAC unmute and relay closure only when the carrier command, ADC_5V_PG, and DAC_5V_PG are all high. Any power-good loss forces AUDIO_SAFE_UNMUTE_N low in hardware; R117 keeps mute/relays asserted if AKM_3V3_D is absent.


Straps establish the safe hardware default; firmware still writes and verifies the serial-control registers after reset. LOCAL BYPASS

Each VREFH uses 20 ohm plus 100 nF and 100 uF to its VREFL/AGND
AVDD=5.0 V, TVDD=3.3 V, internal 1.8 V LDO enabled
TDM256, 32-bit I2S, slave mode: TDM1:0=10, DIF1:0=11, MSN=0

Sheet: /AK5558VN ADC/
File: AK5558-ADC.kicad_sch
Title: ProComm AUDIO-8X8 - AK5558VN Eight-Channel ADC


CAD1:0=01 selects DAC address 0x11; ADC remains at 0x10. TDM256 and 32-bit I2S are written only while mute is asserted. The unused SDTI2/3/4 and DSD pins are tied low in PCM TDM mode to prevent floating inputs.

3. REFERENCES AND LOCAL BYPASS

DAC mute remains asserted until rails, clocks, reset, and register readback pass
AVDD=5.0 V, TVDD=3.3 V, internal 1.8 V LDO enabled
TDM256, 32-bit I2S, slave mode is programmed and read back over I2C

Sheet: /AK4458VN DAC/
File: AK4458-DAC.kicad_sch
Title: ProComm AUDIO-8X8 - AK4458VN Eight-Channel DAC


EIGHT IDENTICAL INPUT CHANNELS - SIGNAL FLOWS LEFT TO RIGHT
ADC_CH1P_RAW

XLR -> 100R/RFI/fault clamps -> THAT1206 -> 10u bipolar -> 13k/1k level shift -> OPA1652 -> 220R/3.3nF -> AK5558

Every XLR pin 1 and shell bonds to XLR_CHASSIS at the connector. AGND and chassis meet only at the controlled board-entry bond.

2.5 V common mode +24 dBu -> 2.49 Vpp diff

+24 dBu -> 2.49 Vpp diff 2.5 V common mode

INPUT RELEASE GATES: SPICE stability/noise, THAT fault-clamp review, +24 dBu THD+N, RF injection, ESD/surge, and phantom-fault tests on every connector type.

Protection and filter values require simulation plus surge/RFI bench qualification
13 k/1 k network maps +24 dBu to 2.49 Vpp differential at AK5558
+4 dBu nominal, +24 dBu maximum, no phantom power
THAT1206 -6 dB receiver; OPA1652 single-supply differential ADC driver

Sheet: /Balanced Inputs 1-8/
File: Audio-Inputs.kicad_sch
Title: ProComm AUDIO-8X8 - Eight Balanced Input Channels

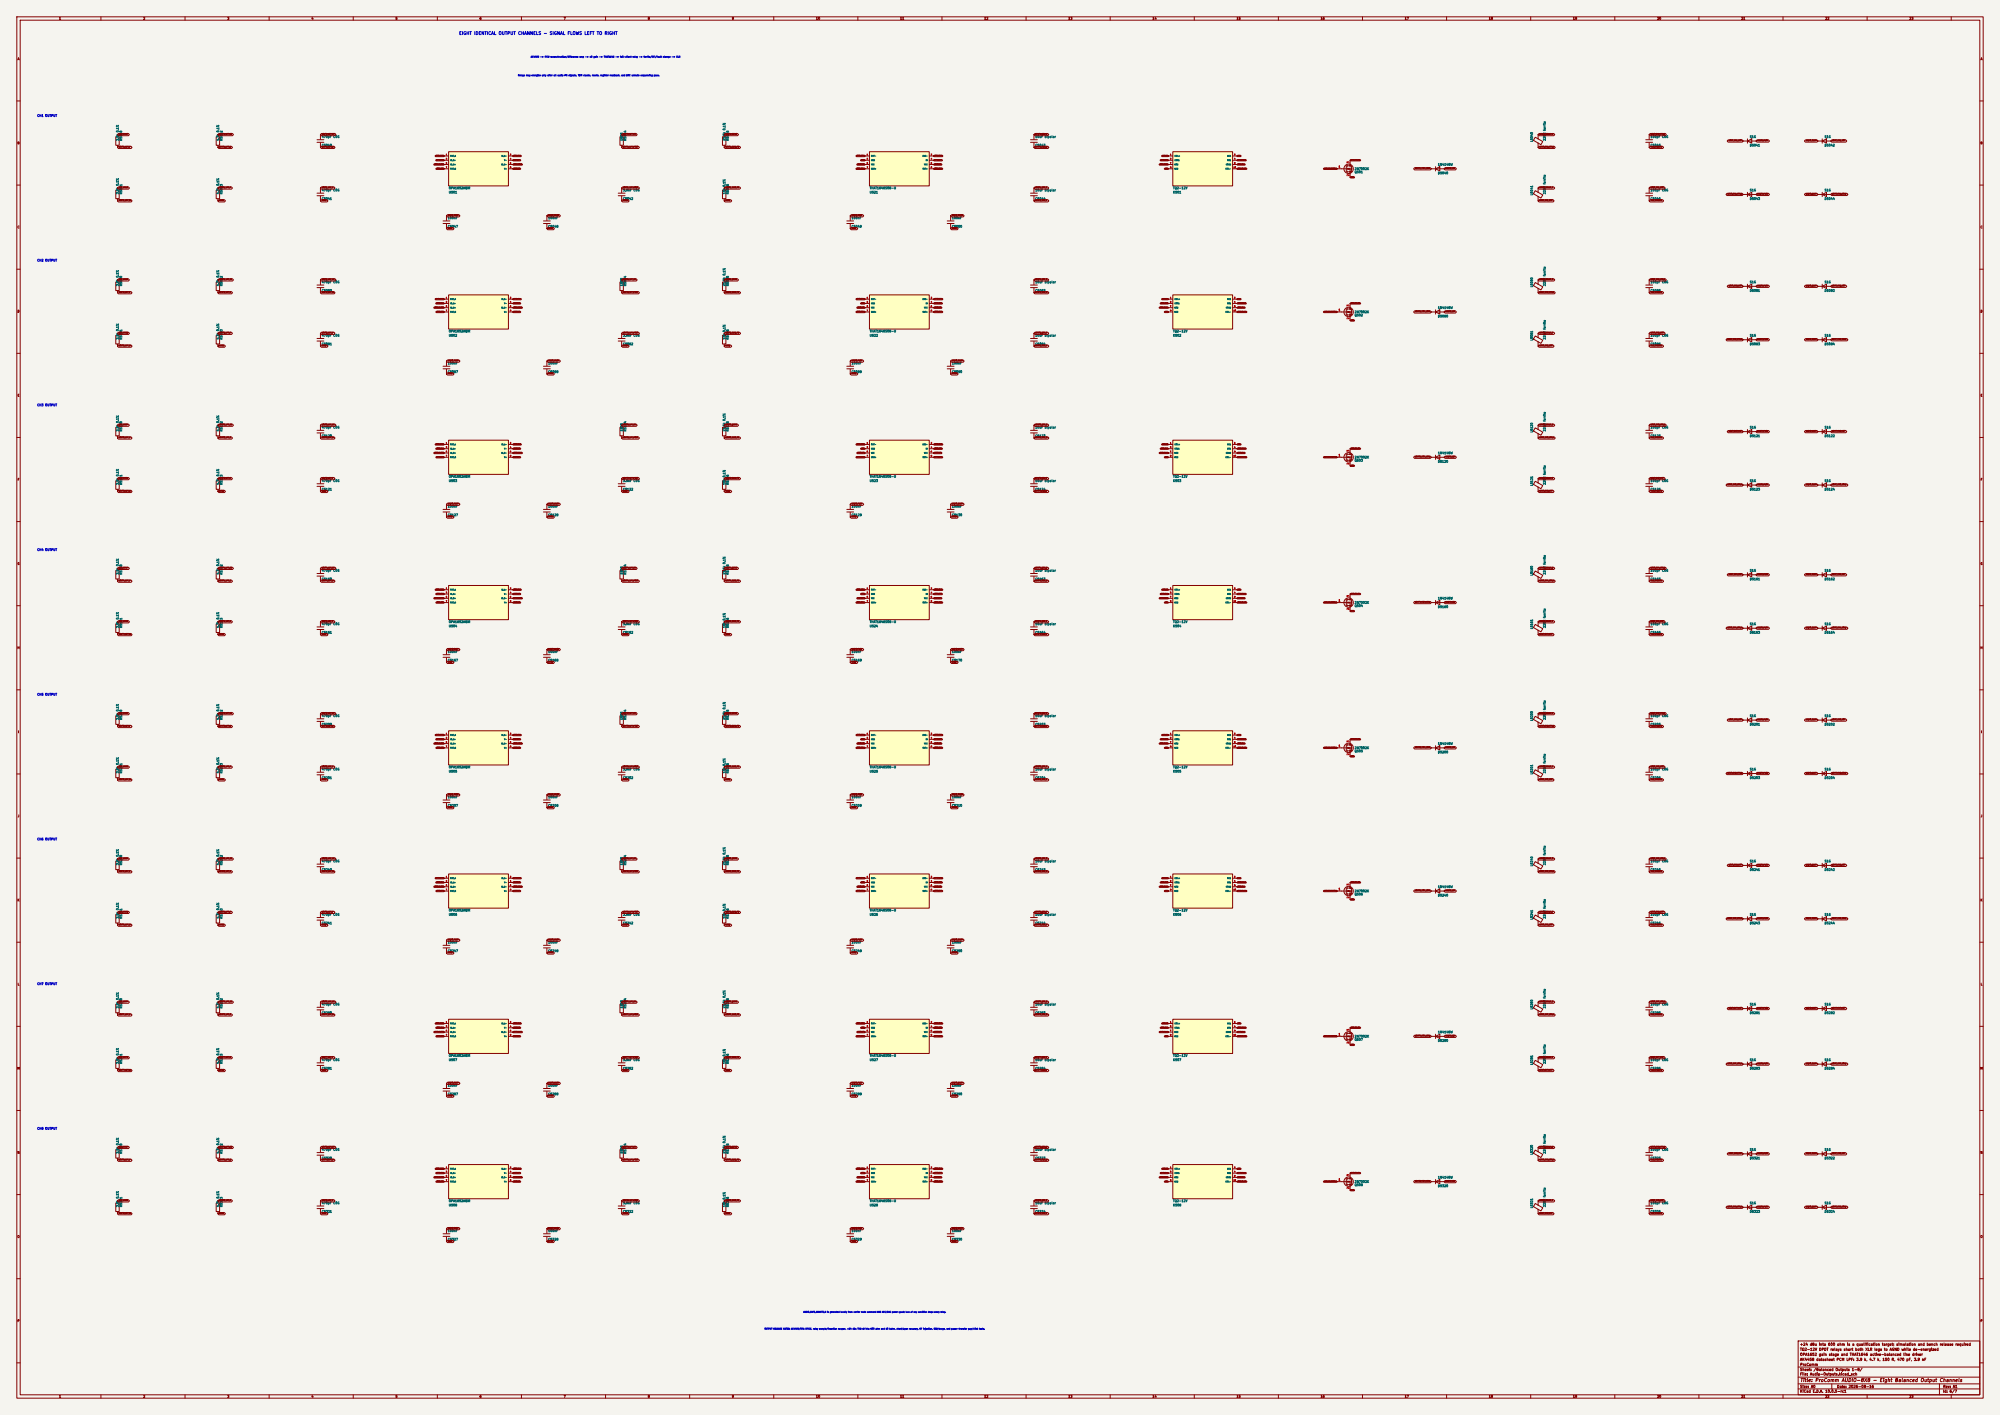
[picture p71: page 6]

AK4458 -> PCM reconstruction/difference amp -> x3 gain -> THAT1646 -> fail-silent relay -> ferrite/RFI/fault clamps -> XLR EIGHT IDENTICAL OUTPUT CHANNELS - SIGNAL FLOWS LEFT TO RIGHT

Relays may energize only after all audio PG signals, TDM clocks, resets, register readback, and DAC unmute sequencing pass.

AUDIO_SAFE_UNMUTE_N is generated locally from carrier mute command AND ADC/DAC power-good; loss of any condition drops every relay.

OUTPUT RELEASE GATES: AK4458/OPA SPICE, relay sample/insertion coupon, +24 dBu THD+N into 600 ohm and 10 kohm, short/open recovery, RF injection, ESD/surge, and power-transfer pop/click tests.

+24 dBu into 600 ohm is a qualification target; simulation and bench release required
TQ2-12V DPDT relays short both XLR legs to AGND while de-energized
OPA1652 gain stage and THAT1646 active-balanced line driver
AK4458 datasheet PCM LPF: 3.9 k, 4.7 k, 150 R, 470 pF, 3.9 nF

Sheet: /Balanced Outputs 1-8/
File: Audio-Outputs.kicad_sch
Title: ProComm AUDIO-8X8 - Eight Balanced Output Channels

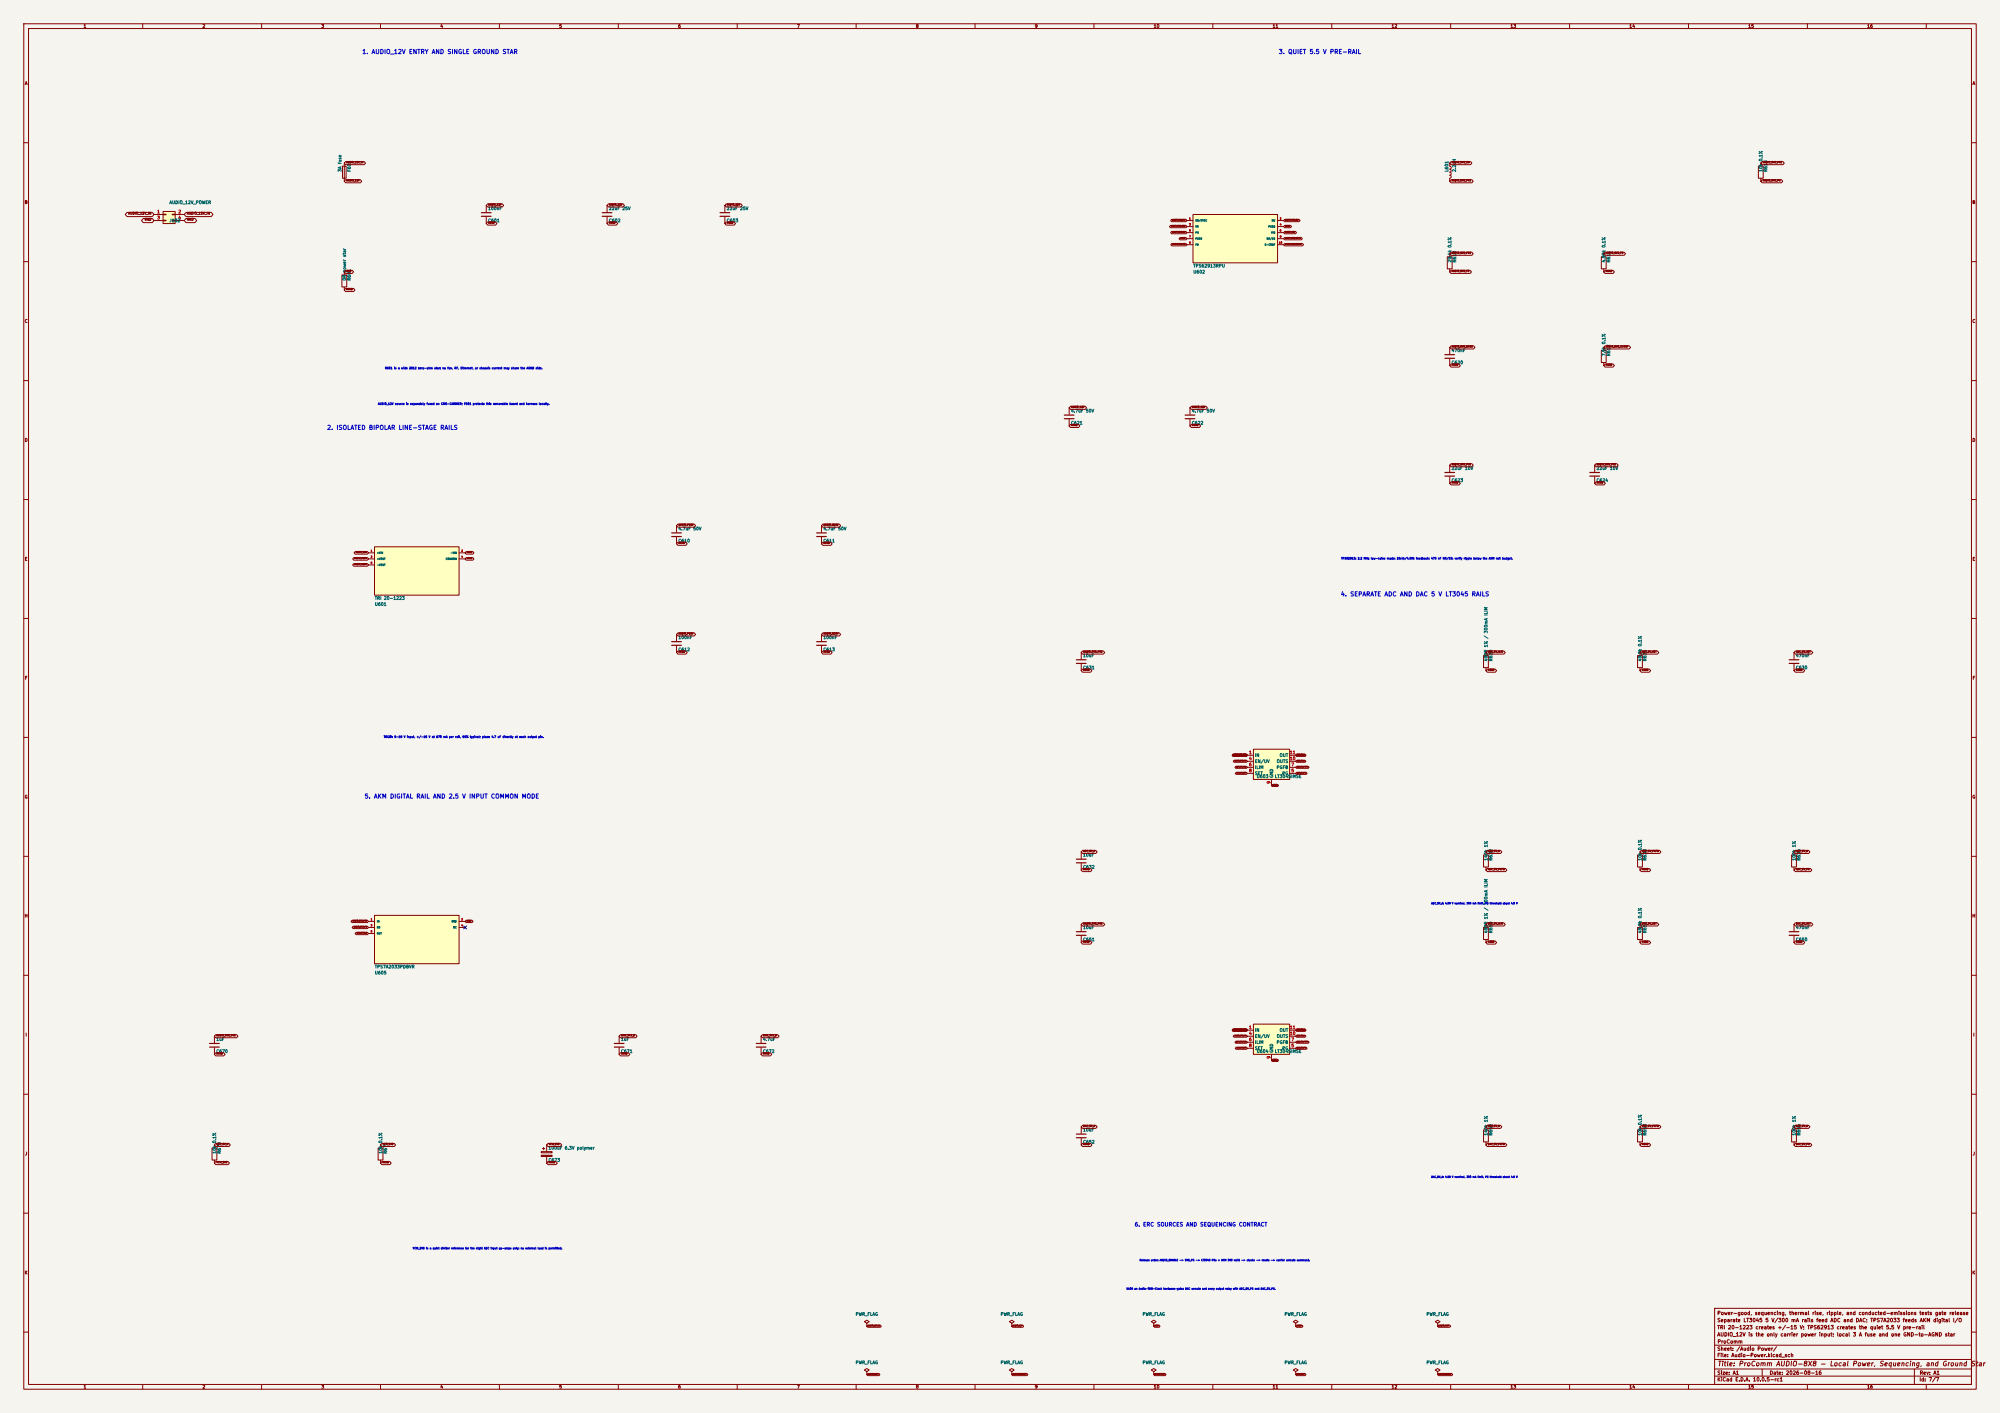
[picture p72: page 7]

1. AUDIO_12V ENTRY AND SINGLE GROUND STAR

R601 is a wide 2512 zero-ohm star: no fan, RF, Ethernet, or chassis current may share the AGND side.

AUDIO_12V source is separately fused on CM5-CARRIER; F601 protects this removable board and harness locally.

TPS62913: 2.2 MHz low-noise mode; 29.4k/4.99k feedback; 470 nF NR/SS; verify ripple below the AKM rail budget. 2. ISOLATED BIPOLAR LINE-STAGE RAILS

4. SEPARATE ADC AND DAC 5 V LT3045 RAILS

TRI20: 9-18 V input, +/-15 V at 670 mA per rail, 89% typical; place 4.7 uF directly at each output pin.

5. AKM DIGITAL RAIL AND 2.5 V INPUT COMMON MODE

ADC_5V_A: 4.99 V nominal, 300 mA limit, PG threshold about 4.5 V

6. ERC SOURCES AND SEQUENCING CONTRACT

Separate LT3045 5 V/300 mA rails feed ADC and DAC; TPS7A2033 feeds AKM digital I/O
TRI 20-1223 creates +/-15 V; TPS62913 creates the quiet 5.5 V pre-rail
AUDIO_12V is the only carrier power input; local 3 A fuse and one GND-to-AGND star

Sheet: /Audio Power/
File: Audio-Power.kicad_sch
Title: ProComm AUDIO-8X8 - Local Power, Sequencing, and Ground Star
