omaralabed/Radxa-CM5-PCB/docs/mechanical-parts/neutrik-nc3fav-drawing.pdf

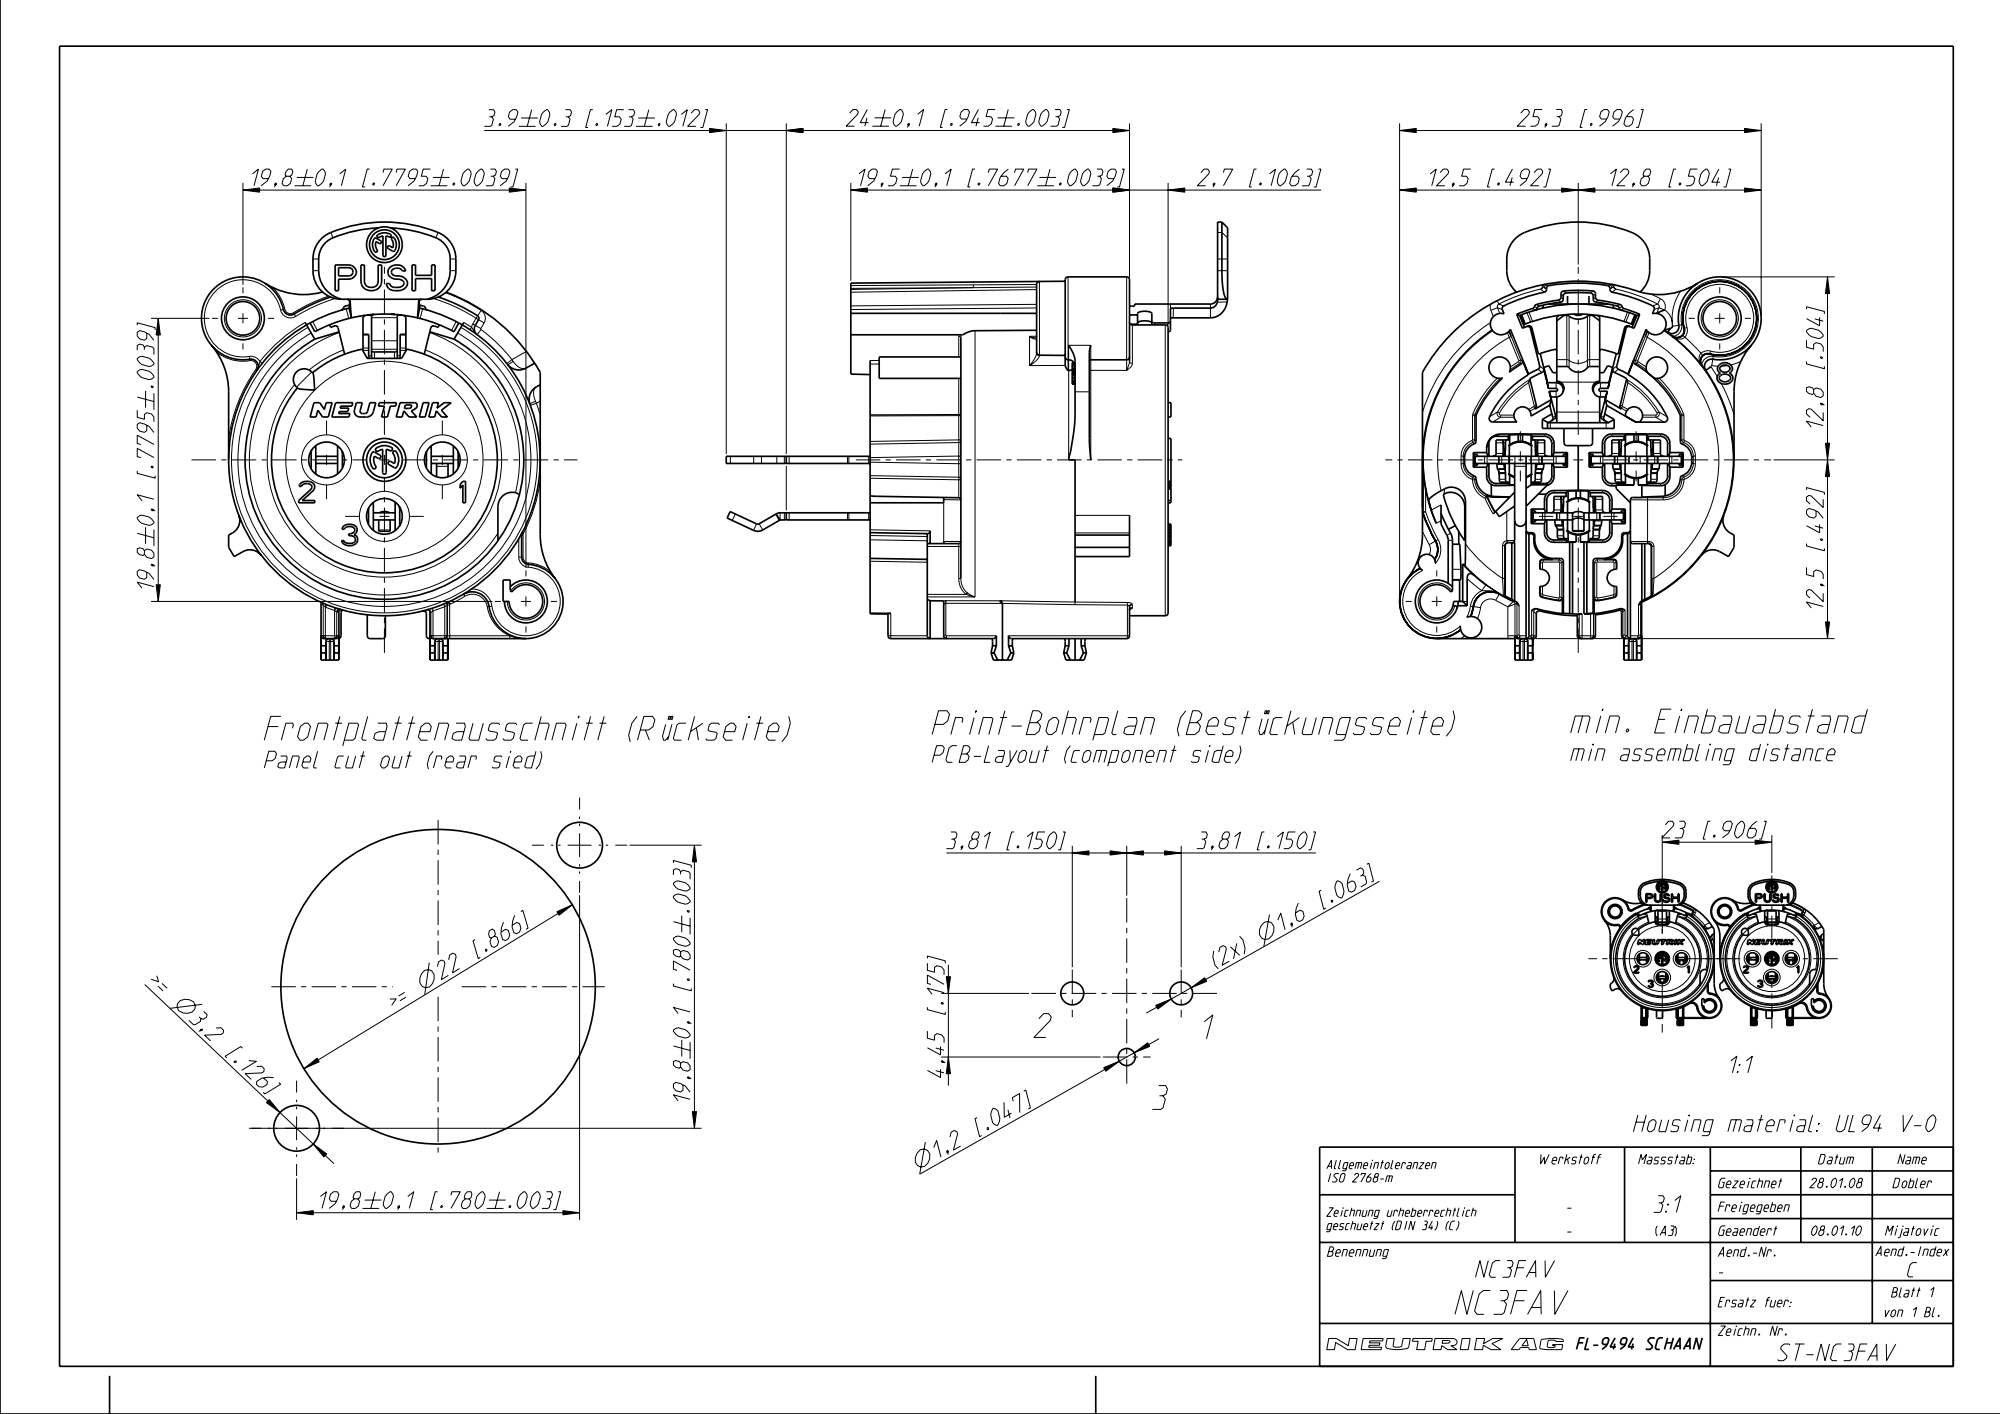
[picture p73: page 1]
