omaralabed/Radxa-CM5-PCB/docs/mechanical-parts/neutrik-nc3mav-drawing.pdf

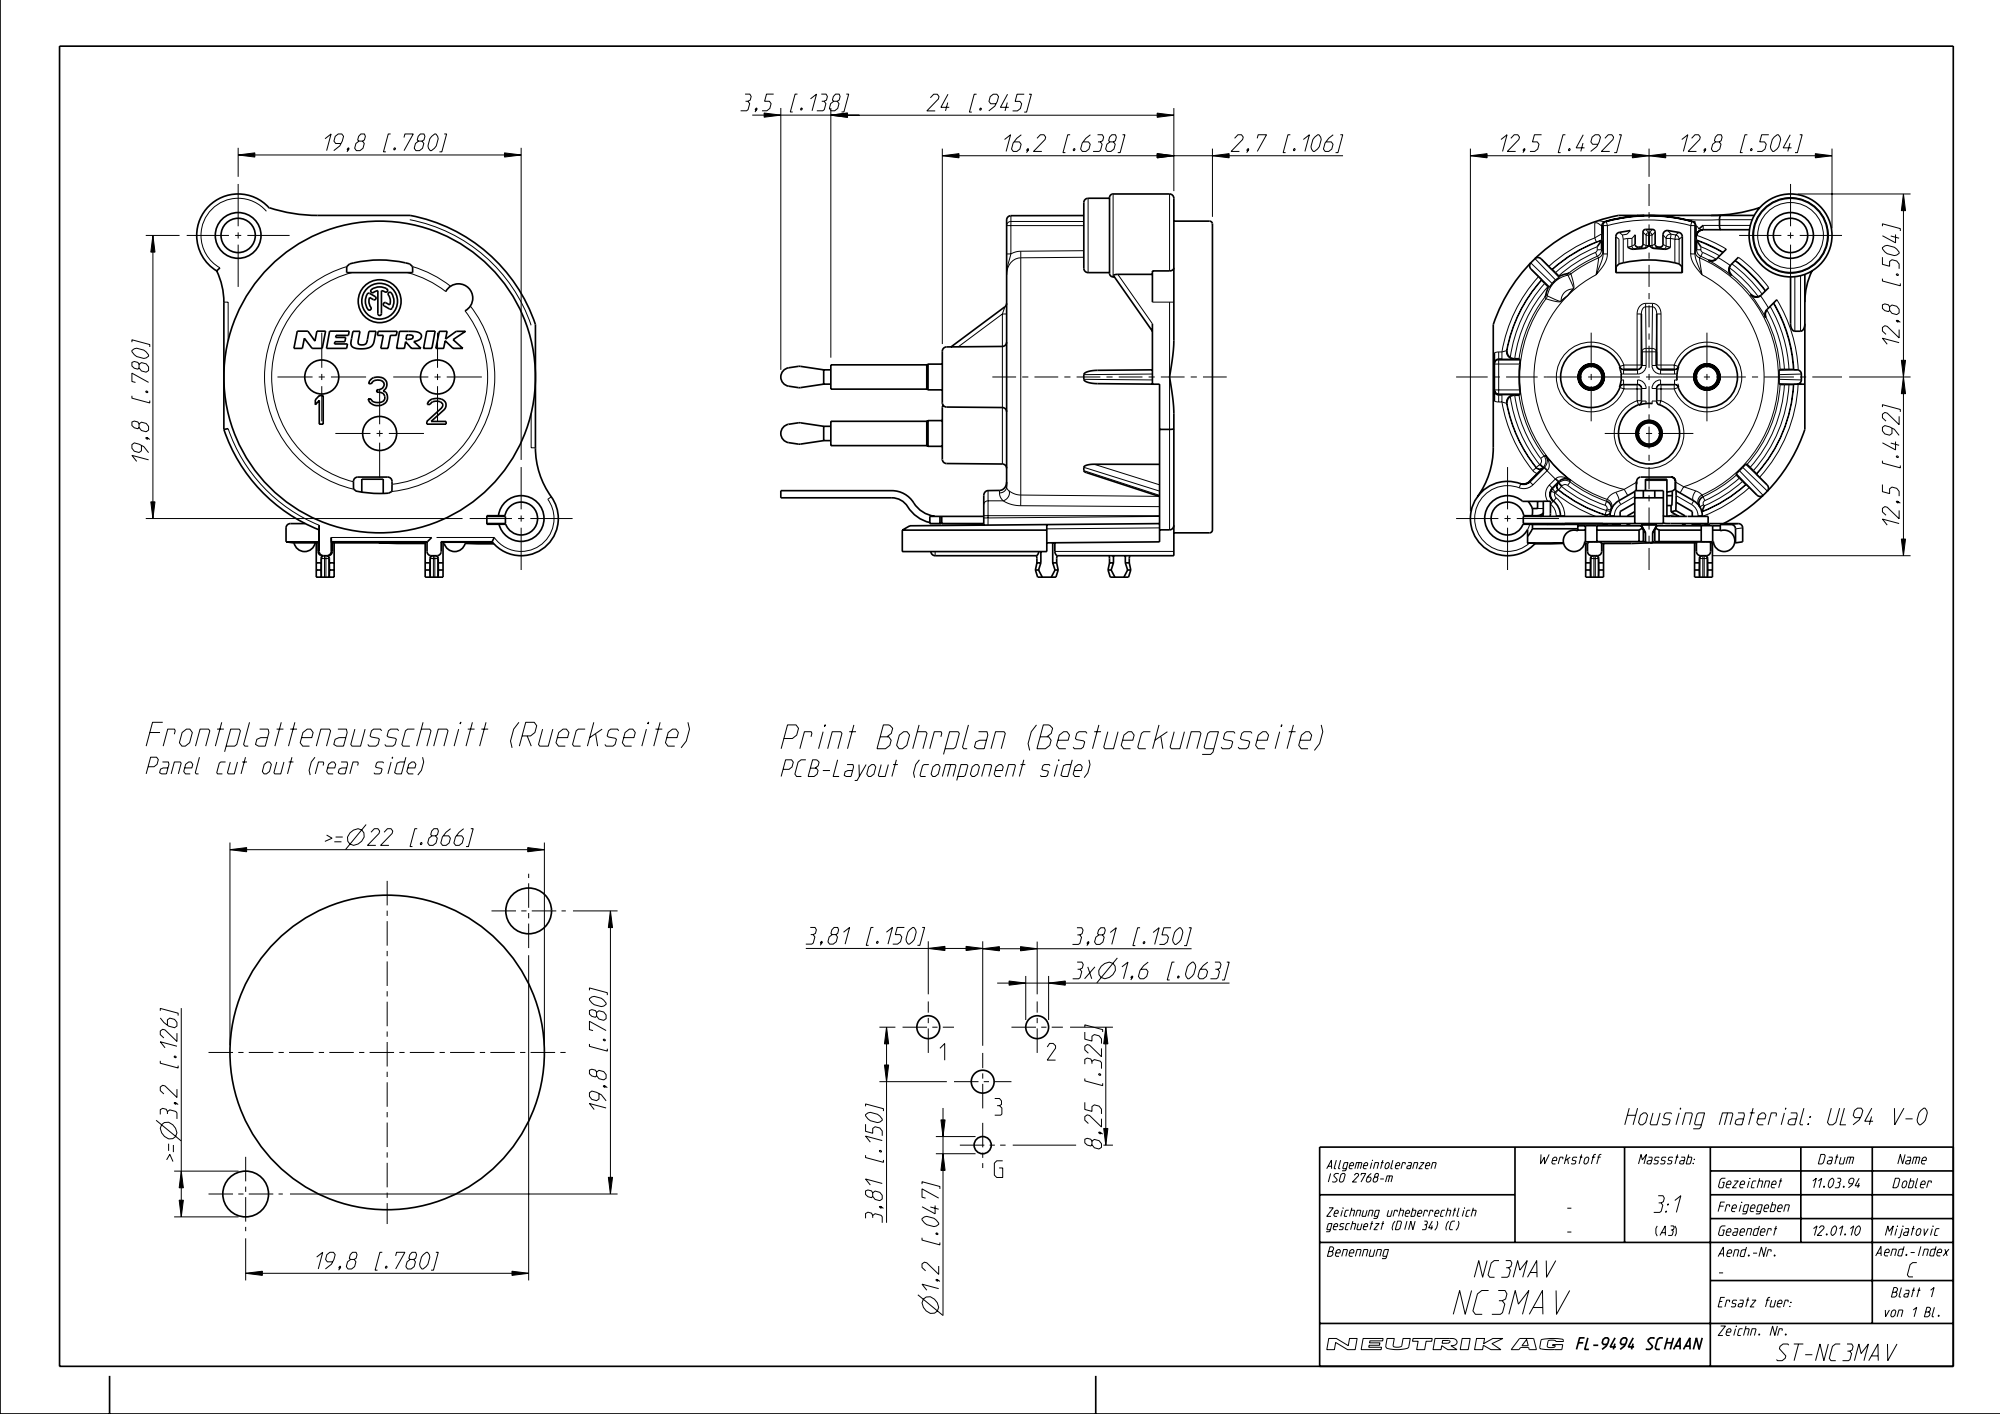
[picture p74: page 1]
