omaralabed/Radxa-CM5-PCB/cad/kicad/generate_interface_schematics.py

#!/usr/bin/env python3
"""Generate native KiCad interface-contract schematics for CM5-CARRIER and AUDIO-8X8."""

from __future__ import annotations

import json
from contextlib import contextmanager
from pathlib import Path
import re
import shutil
import subprocess
import tempfile
import uuid as _uuid


_uuid_counter = 0


def _deterministic_uuid4() -> _uuid.UUID:
    """Return stable KiCad UUIDs for reproducible generated schematics."""
    global _uuid_counter
    _uuid_counter += 1
    return _uuid.uuid5(
        _uuid.NAMESPACE_URL,
        f"radxa-cm5-procomm:interface-schematics:{_uuid_counter}",
    )


# kicad-sch-api uses uuid4 throughout its object factories. Install the stable
# source before importing it so repeated generation produces reviewable diffs.
_uuid.uuid4 = _deterministic_uuid4


@contextmanager
def isolated_uuid_namespace(tag: str):
    """Allocate UUIDs for new blocks without shifting established sheet IDs."""
    counter = 0
    previous_uuid4 = _uuid.uuid4

    def isolated_uuid4() -> _uuid.UUID:
        nonlocal counter
        counter += 1
        return _uuid.uuid5(
            _uuid.NAMESPACE_URL,
            f"radxa-cm5-procomm:interface-schematics:extension:{tag}:{counter}",
        )

    _uuid.uuid4 = isolated_uuid4
    try:
        yield
    finally:
        _uuid.uuid4 = previous_uuid4


def lock_component_pin_uuids(component) -> None:
    """Assign pin UUIDs now so KiCad's serializer cannot shift later sheets."""
    if component.pin_uuids:
        return
    for pin in component.pins:
        component.pin_uuids[str(pin.number)] = str(_uuid.uuid4())

from kicad_sch_api import create_schematic, get_symbol_cache
from openpyxl import load_workbook


ROOT = Path(__file__).resolve().parent
WORKSPACE = ROOT.parent.parent
CM5_PINOUT = WORKSPACE / "docs" / "radxa_cm5_v2210_pinout.xlsx"
CM5_LOCAL_LIBRARY = ROOT / "CM5-CARRIER" / "CM5Carrier.kicad_sym"
CM5_LOCAL_FOOTPRINTS = ROOT / "CM5-CARRIER" / "CM5Carrier.pretty"
CM5_LOCAL_3DMODELS = ROOT / "CM5-CARRIER" / "CM5Carrier.3dshapes"
COMPONENT_REFERENCES = WORKSPACE / "references" / "components"
BEL_V8BR_1AX1_GH = COMPONENT_REFERENCES / "bel" / "V8BR-1AX1-GH"
LEGACY_CELLULAR_FOOTPRINTS = (
    WORKSPACE.parent / "ProComm enclosure and PCB boards" /
    "ADVANCED_SCHEMATIC_WORK" / "ProComm_RevF.pretty"
)
LEGACY_CELLULAR_MODELS = (
    WORKSPACE.parent / "ProComm enclosure and PCB boards" /
    "ADVANCED_SCHEMATIC_WORK" / "ProComm_RevF.3dshapes"
)
KICAD_TEMPLATE = Path(
    "/Applications/KiCad/KiCad.app/Contents/SharedSupport/template/"
    "EuroCard160mmX100mm/EuroCard160mmX100mm.kicad_pro"
)
KICAD_CLI = Path(
    "/Applications/KiCad/KiCad.app/Contents/MacOS/kicad-cli"
)
RADXA_CM5_IO_ASC = (
    WORKSPACE
    / "references"
    / "radxa-cm-projects"
    / "cm5"
    / "radxa-cm5-io-board"
    / "radxa_cm5_io_board_v2200.asc"
)

MF_2X2 = "Connector_Molex:Molex_Micro-Fit_3.0_43045-0412_2x02_P3.00mm_Vertical"
MF_2X4 = "Connector_Molex:Molex_Micro-Fit_3.0_43045-0812_2x04_P3.00mm_Vertical"
JST_GH_4 = "Connector_JST:JST_GH_BM04B-GHS-TBT_1x04-1MP_P1.25mm_Vertical"
JST_GH_5 = "Connector_JST:JST_GH_BM05B-GHS-TBT_1x05-1MP_P1.25mm_Vertical"
JST_GH_6 = "Connector_JST:JST_GH_BM06B-GHS-TBT_1x06-1MP_P1.25mm_Vertical"
DF40_SIM_PLUG = (
    "CM5Carrier:"
    "Hirose_DF40C-20DP-0.4V_2x10-1MP_P0.4mm"
)
DF40_SIM_RECEPTACLE = (
    "CM5Carrier:"
    "Hirose_DF40HC(2.5)-20DS-0.4V_2x10_P0.4mm"
)
PICO_6 = "Connector_Molex:Molex_PicoBlade_53047-0610_1x06_P1.25mm_Vertical"
PICO_8 = "Connector_Molex:Molex_PicoBlade_53047-0810_1x08_P1.25mm_Vertical"
R_0603 = "Resistor_SMD:R_0603_1608Metric"
C_0402 = "Capacitor_SMD:C_0402_1005Metric"
C_0603 = "Capacitor_SMD:C_0603_1608Metric"
C_0805 = "Capacitor_SMD:C_0805_2012Metric"
C_1206 = "Capacitor_SMD:C_1206_3216Metric"
C_1210 = "Capacitor_SMD:C_1210_3225Metric"
TEST_POINT_2MM = "TestPoint:TestPoint_Pad_D2.0mm"
MILLIGRID_2X15 = (
    "Connector_Molex_Milligrid:"
    "Molex_8783230xx_2x15_P2.0mm_Header_Vertical_Polarized_MountingPegs"
)
CM5_DF40_FOOTPRINTS = {
    "U13-A": "CM5Carrier:Radxa_CM5_U33A_DF40C_100DS_OFFICIAL",
    "U13-B": "CM5Carrier:Radxa_CM5_U33B_DF40C_100DS_OFFICIAL",
    "J1": "CM5Carrier:Radxa_CM5_J24_DF40C_100DS_OFFICIAL",
}
CM5_MODULE_MOUNT_FOOTPRINT = "CM5Carrier:Radxa_CM5_Module_Mount_2p6mm_OFFICIAL"

# These mappings are package-code or manufacturer-drawing backed. Keep this
# list exact: an unlisted MPN must remain blocked until its package is checked.
MPN_FOOTPRINTS = {
    "GRM188R71H473KA61D": C_0603,
    "GRM1885C1H682JA01D": C_0603,
    "GRM1885C1H151JA01D": C_0603,
    "GRM188R71E104KA01D": C_0603,
    "GRM188R71A105KA61D": C_0603,
    "GRM21BR71A475KA73L": C_0805,
    "GRM21BR71A226ME44L": C_0805,
    "GRM21BR71E106KA73L": C_0805,
    "GRM31CR71H475KA12L": C_1206,
    "GRM32ER71A476KE15L": C_1210,
    "GCM32ER70J476KE19L": C_1210,
    "16SVP330M": "Capacitor_SMD:CP_Elec_10x12.6",
    "6SVP330M": "Capacitor_SMD:CP_Elec_10x7.9",
    "6SVP470M": "Capacitor_SMD:CP_Elec_8x11.9",
    "BAT54WS-7-F": "Diode_SMD:D_SOD-323",
    "0453003.MR": "Fuse:Fuse_Littelfuse-NANO2-451_453",
    "0453002.MR": "Fuse:Fuse_Littelfuse-NANO2-451_453",
    "0453.250MR": "Fuse:Fuse_Littelfuse-NANO2-451_453",
    "XAL7070-472MEC": "Inductor_SMD:L_Coilcraft_XAL7070-XXX",
    "XGL4030-222MEC": "Inductor_SMD:L_Coilcraft_XxL4040",
    "SPM10065VC-3R3M-D": "CM5Carrier:TDK_SPM10065VC",
    "74439370047": "CM5Carrier:Wurth_74439370047",
    "KRL6432E-M-R006-F-T1": "CM5Carrier:Susumu_KRL6432E_6mR",
    "KRL11050-C-R004-F-T1": "CM5Carrier:Susumu_KRL11050_4mR",
    "NVMFS6B25NLT1G": "CM5Carrier:onsemi_DFN5_5x6_488AA_GSD",
    "FDWS86068-F085": "CM5Carrier:onsemi_DFNW8_5p2x6p3_507AU_GSD",
    "CSD18532Q5B": "CM5Carrier:TI_DNK0008A_GSD",
    "CSD17573Q5B": "CM5Carrier:TI_DNK0008A_GSD",
    "LM61460RJR": "CM5Carrier:TI_RJR0014A",
    "LM61440RJR": "CM5Carrier:TI_RJR0014A",
    "TPS22990DMLR": "CM5Carrier:TI_DML0010A",
    "RC0603FR-0740K2L": R_0603,
    "RC0603FR-077K5L": R_0603,
    "RC0603FR-07499RL": R_0603,
    "RC0603FR-0769K8L": R_0603,
    "RC0603FR-0710KL": R_0603,
    "RC0603JR-070RL": R_0603,
    "TNPW060324K0BEEA": R_0603,
    "TNPW060326K1BEEA": R_0603,
    "TNPW06034K42BEEA": R_0603,
    "TNPW06031K24BEEA": R_0603,
    "TNPW06031K00BEEA": R_0603,
    "TNPW06034K99BEEA": R_0603,
    "TNPW06036K19BEEA": R_0603,
    "TNPW060315K6BEEA": R_0603,
    "TNPW060320K0BEEA": R_0603,
    "TNPW060321K5BEEA": R_0603,
    "TNPW060329K4BEEA": R_0603,
    "TNPW060335K7BEEA": R_0603,
    "TNPW060343K2BEEA": R_0603,
    "TNPW0603100KBEEA": R_0603,
    "TNPW0603280KBEEA": R_0603,
    "RC0603FR-0727K4L": R_0603,
    "RC0603FR-0733K2L": R_0603,
    "RC0603FR-0773K2L": R_0603,
    "RC0603FR-0793K1L": R_0603,
    "RC0603FR-07255RL": R_0603,
    "GRM31CR71H105KA61L": C_1206,
    "GRM188R71H103KA01D": C_0603,
    "GRM188R71H222KA01D": C_0603,
    "GRM188R71H333KA01D": C_0603,
    "GRM188R71H472KA01D": C_0603,
    "GRM1885C1H221JA01D": C_0603,
    "GRM1885C1H561JA01D": C_0603,
    "GRM188R71E474KA12D": C_0603,
    "PCA9306DP,118": "Package_SO:TSSOP-8_3x3mm_P0.65mm",
    "PCA9517ADP,118": "Package_SO:TSSOP-8_3x3mm_P0.65mm",
    "TCA9535PWR": "Package_SO:TSSOP-24_4.4x7.8mm_P0.65mm",
    "EMC2305-1-AP-TR": "Package_DFN_QFN:QFN-16-1EP_4x4mm_P0.65mm_EP2.1x2.1mm",
    "TMP117AIDRVR": "Package_SON:WSON-6-1EP_2x2mm_P0.65mm_EP1x1.6mm",
    "2N7002K-7": "Package_TO_SOT_SMD:SOT-23",
    "2920L300/15DR": "Fuse:Fuse_2920_7451Metric",
    "1812L110/33DR": "Fuse:Fuse_1812_4532Metric",
    "VLS3012HBX-3R3M-N": "CM5Carrier:TDK_VLS3012HBX",
    "ABM8-25.000MHZ-10-D1G-T": "Crystal:Crystal_SMD_3225-4Pin_3.2x2.5mm",
    "C1005X7R1H104K050BB": C_0402,
    "GRM188R61E106MA73D": C_0603,
    "GRM155R6YA105KE11D": C_0402,
    "GRM1555C1H150JA01D": C_0402,
    "RC0603FR-071K43L": R_0603,
    "RC0603FR-07475RL": R_0603,
    "RC0603FR-07200RL": R_0603,
    "RC0603FR-07200KL": R_0603,
    "RC0603FR-076K04L": R_0603,
    "RC0603FR-07330RL": R_0603,
    "RC0603FR-072K2L": R_0603,
    "RC0603FR-074K7L": R_0603,
    "RC0603FR-075K1L": R_0603,
    "RC0603FR-07100KL": R_0603,
    "RC0603FR-071ML": R_0603,
    "RC0603FR-071KL": R_0603,
    "TPD4E05U06DQAR": "Package_SON:USON-10_2.5x1.0mm_P0.5mm",
    "SN65LVDS047PWR": "Package_SO:TSSOP-16_4.4x5mm_P0.65mm",
    "SN65LVDT2DR": "Package_SO:SOIC-8_3.9x4.9mm_P1.27mm",
    "SN74AVC4T245PWR": "Package_SO:TSSOP-16_4.4x5mm_P0.65mm",
    "SN74LVC1T45DCKR": "Package_TO_SOT_SMD:SOT-363_SC-70-6",
    "SN74LVC1G11DBVR": "Package_TO_SOT_SMD:SOT-23-6",
    "LP5907MFX-3.3/NOPB": "Package_TO_SOT_SMD:SOT-23-5",
    "LP5907MFX-1.8/NOPB": "Package_TO_SOT_SMD:SOT-23-5",
    "TPA6132A2RTER": (
        "Package_DFN_QFN:"
        "WQFN-16-1EP_3x3mm_P0.5mm_EP1.68x1.68mm_ThermalVias"
    ),
    "87832-6423": MILLIGRID_2X15,
    "STX-353K7A-6N-KTTR": "CM5Carrier:Kycon_STX-353K7A-6N-KTTR_PRELIMINARY",
    "GRM188R71A225KE15": C_0603,
    "RC0603FR-07330KL": R_0603,
    "0603L010YR": "Fuse:Fuse_0603_1608Metric",
    "1206L110/16WR": "Fuse:Fuse_1206_3216Metric",
    "TPD3F303DPVR": (
        "Package_SON:Texas_R-PUSON-N8_USON-8-1EP_1.6x2.1mm_P0.5mm_EP0.4x1.7mm"
    ),
    "AK5558VN": "Package_DFN_QFN:QFN-64-1EP_9x9mm_P0.5mm_EP6x6mm_ThermalVias",
    "AK4458VN": "Package_DFN_QFN:QFN-48-1EP_7x7mm_P0.5mm_EP5.15x5.15mm_ThermalVias",
    "THAT1206S08-U": "Package_SO:SOIC-8_3.9x4.9mm_P1.27mm",
    "THAT1646S08-U": "Package_SO:SOIC-8_3.9x4.9mm_P1.27mm",
    "OPA1652AIDR": "Package_SO:SOIC-8_3.9x4.9mm_P1.27mm",
    "SN65LVDS1DR": "Package_SO:SOIC-8_3.9x4.9mm_P1.27mm",
    "LT3045IMSE#TRPBF": (
        "Package_SO:MSOP-12-1EP_3x4.039mm_P0.65mm_EP1.651x2.845mm_ThermalVias"
    ),
    "TPS62913RPUT": "Package_DFN_QFN:Texas_RPU0010A_VQFN-HR-10_2x2mm_P0.5mm",
    "TRI 20-1223": "CM5Carrier:TRACO_TRI20_DUAL",
    "ULN2803ADWR": "Package_SO:SOIC-18W_7.5x11.6mm_P1.27mm",
    "TQ2-12V": "CM5Carrier:Panasonic_TQ2-12V_PRELIMINARY",
    "S1G-13-F": "Diode_SMD:D_SMA",
    "BZT52C12-7-F": "Diode_SMD:D_SOD-123",
    "BLM21PG221SN1D": "Inductor_SMD:L_0805_2012Metric",
    "UES1H100MDM1TD": "Capacitor_THT:CP_Radial_D5.0mm_P2.00mm",
    "UES0J221MHM": "Capacitor_THT:CP_Radial_D10.0mm_P5.00mm",
    "6SVP100M": "Capacitor_SMD:CP_Elec_6.3x5.8",
    "6SVP220MX": "Capacitor_SMD:CP_Elec_8x6.9",
    "GRM1885C1H680JA01D": C_0603,
    "GRM1555C1H221JA01D": C_0402,
    "GRM1555C1H680JA01D": C_0402,
    "GRM1555C1H9R1BA01D": C_0402,
    "GRM1555C1H4R7BA01D": C_0402,
    "SMF4L5.0AT1G": "Diode_SMD:D_SOD-123F",
    "RC0603FR-0710RL": R_0603,
    "RC0603FR-07100RL": R_0603,
    "RC0603FR-0713KL": R_0603,
    "RC0603FR-073K9L": R_0603,
    "RC0603FR-07150RL": R_0603,
    "RC0603FR-0720RL": R_0603,
    "RC0603FR-07220RL": R_0603,
    "RC0603FR-0720KL": R_0603,
    "TNPW060349K9BEEA": R_0603,
    "GRM1885C1H471JA01D": C_0603,
    "GRM1885C1H101JA01D": C_0603,
    "GRM1885C1H332JA01D": C_0603,
    "GRM1885C1H392JA01D": C_0603,
    "GRM188R71A106KA73D": C_0603,
    "GRM188R71E474KA12D": C_0603,
    "GRM21BR71E106KA73L": C_0805,
    "RC0603FR-074K99L": R_0603,
    "RC0603FR-0729K4L": R_0603,
    "1N4148W-7-F": "Diode_SMD:D_SOD-123",
    "TPS7A2033PDBVR": "Package_TO_SOT_SMD:SOT-23-5",
    "GRM32ER71E226KE15L": C_1210,
    "RC0603FR-07140KL": R_0603,
    "RC2512JK-070RL": "Resistor_SMD:R_2512_6332Metric",
    "BM04B-GHS-TBT(LF)(SN)": JST_GH_4,
    "BM05B-GHS-TBT(LF)(SN)": JST_GH_5,
    "BM06B-GHS-TBT(LF)(SN)": JST_GH_6,
    "43045-0812": MF_2X4,
    "VY1472M63Y5UQ6TV0": "Capacitor_THT:C_Disc_D16.0mm_W5.0mm_P10.00mm",
}

POWER_PASSIVE_PARTS = {
    "1uF 50V X7R": ("Murata", "GRM31CR71H105KA61L"),
    "100nF": ("Murata", "GRM188R71E104KA01D"),
    "100nF 25V": ("Murata", "GRM188R71E104KA01D"),
    "10nF": ("Murata", "GRM188R71H103KA01D"),
    "2.2nF": ("Murata", "GRM188R71H222KA01D"),
    "33nF": ("Murata", "GRM188R71H333KA01D"),
    "4.7nF": ("Murata", "GRM188R71H472KA01D"),
    "220pF": ("Murata", "GRM1885C1H221JA01D"),
    "560pF": ("Murata", "GRM1885C1H561JA01D"),
    "470nF": ("Murata", "GRM188R71E474KA12D"),
    "1uF X7R": ("Murata", "GRM188R71A105KA61D"),
    "4.7uF 10V": ("Murata", "GRM21BR71A475KA73L"),
    "4.7uF 50V": ("Murata", "GRM31CR71H475KA12L"),
    "10k": ("Yageo", "RC0603FR-0710KL"),
    "10k 1%": ("Yageo", "RC0603FR-0710KL"),
    "100k 1%": ("Yageo", "RC0603FR-07100KL"),
    "27.4k": ("Yageo", "RC0603FR-0727K4L"),
    "33.2k / 400kHz": ("Yageo", "RC0603FR-0733K2L"),
    "73.2k 1%": ("Yageo", "RC0603FR-0773K2L"),
    "93.1k": ("Yageo", "RC0603FR-0793K1L"),
    "255R 1% / 6A ILIM": ("Yageo", "RC0603FR-07255RL"),
    "1.24k 0.1%": ("Vishay", "TNPW06031K24BEEA"),
    "4.99k 0.1%": ("Vishay", "TNPW06034K99BEEA"),
    "6.19k 0.1%": ("Vishay", "TNPW06036K19BEEA"),
    "15.6k 0.1%": ("Vishay", "TNPW060315K6BEEA"),
    "20k 0.1%": ("Vishay", "TNPW060320K0BEEA"),
    "29.4k 0.1%": ("Vishay", "TNPW060329K4BEEA"),
    "35.7k 0.1%": ("Vishay", "TNPW060335K7BEEA"),
    "43.2k 0.1%": ("Vishay", "TNPW060343K2BEEA"),
    "100k 0.1%": ("Vishay", "TNPW0603100KBEEA"),
    "280k 0.1%": ("Vishay", "TNPW0603280KBEEA"),
}

THERMAL_PASSIVE_PARTS = {
    "100nF": ("Murata", "GRM188R71E104KA01D"),
    "1k": ("Yageo", "RC0603FR-071KL"),
    "1k ring limit": ("Yageo", "RC0603FR-071KL"),
    "2.2k": ("Yageo", "RC0603FR-072K2L"),
    "4.7k": ("Yageo", "RC0603FR-074K7L"),
    "4.7k 5%": ("Yageo", "RC0603FR-074K7L"),
    "5.1k": ("Yageo", "RC0603FR-075K1L"),
    "10k": ("Yageo", "RC0603FR-0710KL"),
    "100k": ("Yageo", "RC0603FR-07100KL"),
    "200k": ("Yageo", "RC0603FR-07200KL"),
}

NETWORK_PASSIVE_PARTS = {
    "100nF": ("TDK", "C1005X7R1H104K050BB"),
    "10nF": ("Murata", "GRM188R71H103KA01D"),
    "22uF 10V X7R": ("Murata", "GRM21BR71A226ME44L"),
    "10uF 25V X5R": ("Murata", "GRM188R61E106MA73D"),
    "1uF 35V X5R / ESR <1R": ("Murata", "GRM155R6YA105KE11D"),
    "220R ferrite": ("Murata", "BLM21PG221SN1D"),
    "15pF C0G": ("Murata", "GRM1555C1H150JA01D"),
    "4.7k": ("Yageo", "RC0603FR-074K7L"),
    "1.43k 1%": ("Yageo", "RC0603FR-071K43L"),
    "475R 1%": ("Yageo", "RC0603FR-07475RL"),
    "2.2k": ("Yageo", "RC0603FR-072K2L"),
    "0R": ("Yageo", "RC0603JR-070RL"),
    "200R 1%": ("Yageo", "RC0603FR-07200RL"),
    "6.04k 1%": ("Yageo", "RC0603FR-076K04L"),
    "10k": ("Yageo", "RC0603FR-0710KL"),
    "100k": ("Yageo", "RC0603FR-07100KL"),
    "330R": ("Yageo", "RC0603FR-07330RL"),
}

WWAN_PASSIVE_PARTS = {
    "220uF 6.3V polymer": ("Panasonic", "6SVP220MX"),
    "10uF 25V X5R": ("Murata", "GRM188R61E106MA73D"),
    "100nF": ("TDK", "C1005X7R1H104K050BB"),
    "6.8nF C0G": ("Murata", "GRM1885C1H682JA01D"),
    "220pF C0G": ("Murata", "GRM1555C1H221JA01D"),
    "68pF C0G": ("Murata", "GRM1555C1H680JA01D"),
    "15pF C0G": ("Murata", "GRM1555C1H150JA01D"),
    "9.1pF C0G": ("Murata", "GRM1555C1H9R1BA01D"),
    "4.7pF C0G": ("Murata", "GRM1555C1H4R7BA01D"),
    "100k": ("Yageo", "RC0603FR-07100KL"),
}

DISPLAY_PASSIVE_PARTS = {
    "2.2k": ("Yageo", "RC0603FR-072K2L"),
    "7.5k S-CONF": ("Yageo", "RC0603FR-077K5L"),
    "26.1k 0.1%": ("Vishay", "TNPW060326K1BEEA"),
    "4.99k 0.1%": ("Vishay", "TNPW06034K99BEEA"),
    "470nF": ("Murata", "GRM188R71E474KA12D"),
    "10uF 25V X5R": ("Murata", "GRM188R61E106MA73D"),
    "10uF 25V X7R": ("Murata", "GRM21BR71E106KA73L"),
    "22uF 10V X7R": ("Murata", "GRM21BR71A226ME44L"),
    "100nF": ("TDK", "C1005X7R1H104K050BB"),
}

AUDIO_PASSIVE_PARTS = {
    "0R": ("Yageo", "RC0603JR-070RL"),
    "0R star bond": ("Yageo", "RC0603JR-070RL"),
    "0R power star": ("Yageo", "RC2512JK-070RL"),
    "100nF": ("TDK", "C1005X7R1H104K050BB"),
    "1uF": ("Murata", "GRM188R71A105KA61D"),
    "2.2uF": ("Murata", "GRM188R71A225KE15"),
    "4.7uF": ("Murata", "GRM21BR71A475KA73L"),
    "10uF": ("Murata", "GRM188R61E106MA73D"),
    "2.2k": ("Yageo", "RC0603FR-072K2L"),
    "10k": ("Yageo", "RC0603FR-0710KL"),
    "100k": ("Yageo", "RC0603FR-07100KL"),
    "200k": ("Yageo", "RC0603FR-07200KL"),
    "330k": ("Yageo", "RC0603FR-07330KL"),
}

AUDIO8_PASSIVE_PARTS = {
    "0R star bond": ("Yageo", "RC0603JR-070RL"),
    "0R power star": ("Yageo", "RC2512JK-070RL"),
    "20R": ("Yageo", "RC0603FR-0720RL"),
    "10R": ("Yageo", "RC0603FR-0710RL"),
    "100R": ("Yageo", "RC0603FR-07100RL"),
    "150R": ("Yageo", "RC0603FR-07150RL"),
    "220R": ("Yageo", "RC0603FR-07220RL"),
    "1k 0.1%": ("Vishay", "TNPW06031K00BEEA"),
    "3.9k 0.1%": ("Yageo", "RC0603FR-073K9L"),
    "4.7k 0.1%": ("Yageo", "RC0603FR-074K7L"),
    "10k 0.1%": ("Yageo", "RC0603FR-0710KL"),
    "13k 0.1%": ("Yageo", "RC0603FR-0713KL"),
    "20k 0.1%": ("Yageo", "RC0603FR-0720KL"),
    "21.5k 0.1%": ("Vishay", "TNPW060321K5BEEA"),
    "49.9k 0.1%": ("Vishay", "TNPW060349K9BEEA"),
    "29.4k 0.1%": ("Vishay", "TNPW060329K4BEEA"),
    "4.99k 0.1%": ("Yageo", "RC0603FR-074K99L"),
    "7.5k 0.1%": ("Yageo", "RC0603FR-077K5L"),
    "140k 1%": ("Yageo", "RC0603FR-07140KL"),
    "100k 1%": ("Yageo", "RC0603FR-07100KL"),
    "499R 1% / 300mA ILIM": ("Yageo", "RC0603FR-07499RL"),
    "1M": ("Yageo", "RC0603FR-071ML"),
    "100nF": ("TDK", "C1005X7R1H104K050BB"),
    "470nF": ("Murata", "GRM188R71E474KA12D"),
    "100pF C0G": ("Murata", "GRM1885C1H101JA01D"),
    "470pF C0G": ("Murata", "GRM1885C1H471JA01D"),
    "3.3nF C0G": ("Murata", "GRM1885C1H332JA01D"),
    "3.9nF C0G": ("Murata", "GRM1885C1H392JA01D"),
    "1uF": ("Murata", "GRM188R71A105KA61D"),
    "4.7uF": ("Murata", "GRM21BR71A475KA73L"),
    "4.7uF 50V": ("Murata", "GRM31CR71H475KA12L"),
    "10uF": ("Murata", "GRM188R71A106KA73D"),
    "22uF 25V": ("Murata", "GRM32ER71E226KE15L"),
    "10uF bipolar": ("Nichicon", "UES1H100MDM1TD"),
    "22uF 10V": ("Murata", "GRM21BR71A226ME44L"),
    "100uF 6.3V polymer": ("Panasonic", "6SVP100M"),
    "220uF 6.3V polymer": ("Panasonic", "6SVP220MX"),
    "220uF bipolar": ("Nichicon", "UES0J221MHM"),
    "1N4148W": ("Diodes Incorporated", "1N4148W-7-F"),
    "12V zener": ("Diodes Incorporated", "BZT52C12-7-F"),
    "220R ferrite": ("Murata", "BLM21PG221SN1D"),
    "S1G": ("Diodes Incorporated", "S1G-13-F"),
    "2.2uH": ("Coilcraft", "XGL4030-222MEC"),
    "3A fuse": ("Littelfuse", "0453003.MR"),
}


# This is the controlled allocation from the A0 pin audit.  Physical signal
# names for all 300 connector contacts come directly from the official V2.21
# workbook; only these 76 contacts receive product nets in Rev A.
CM5_ALLOCATIONS = (
    ("U13-A", 77, "Input", "SYS_4V0"),
    ("U13-A", 79, "Input", "SYS_4V0"),
    ("U13-A", 81, "Input", "SYS_4V0"),
    ("U13-A", 83, "Input", "SYS_4V0"),
    ("U13-A", 85, "Input", "SYS_4V0"),
    ("U13-A", 87, "Input", "SYS_4V0"),
    ("U13-A", 78, "Input", "LOGIC_3V3"),
    ("U13-B", 106, "Input", "IO_5V0"),
    ("U13-A", 92, "Input", "CM5_RESET_N"),
    ("U13-A", 93, "Input", "CM5_BOOT"),
    ("U13-A", 99, "Input", "CM5_PWRON_N"),
    ("J1", 26, "Input", "CM5_RECOVERY_KEY"),
    ("U13-A", 3, "Bidirectional", "WAN1_MDI3_P"),
    ("U13-A", 5, "Bidirectional", "WAN1_MDI3_N"),
    ("U13-A", 4, "Bidirectional", "WAN1_MDI1_P"),
    ("U13-A", 6, "Bidirectional", "WAN1_MDI1_N"),
    ("U13-A", 11, "Bidirectional", "WAN1_MDI2_P"),
    ("U13-A", 9, "Bidirectional", "WAN1_MDI2_N"),
    ("U13-A", 12, "Bidirectional", "WAN1_MDI0_P"),
    ("U13-A", 10, "Bidirectional", "WAN1_MDI0_N"),
    ("U13-A", 15, "Output", "WAN1_LED2"),
    ("U13-A", 17, "Output", "WAN1_LED1"),
    ("U13-A", 19, "Output", "WAN1_LED0"),
    ("U13-A", 24, "Input", "PCIE_UP_WAKE_N"),
    ("U13-B", 102, "Input", "PCIE_UP_CLKREQ_N"),
    ("U13-B", 109, "Output", "PCIE_UP_PERST_CMD_N"),
    ("U13-B", 110, "Output", "PCIE_UP_REFCLK_P"),
    ("U13-B", 112, "Output", "PCIE_UP_REFCLK_N"),
    ("U13-B", 116, "Input", "PCIE_UP_RX_P_CM5"),
    ("U13-B", 118, "Input", "PCIE_UP_RX_N_CM5"),
    ("U13-B", 122, "Output", "PCIE_UP_TX_P_CM5"),
    ("U13-B", 124, "Output", "PCIE_UP_TX_N_CM5"),
    ("J1", 51, "Output", "WWAN_USB3_TX_P"),
    ("J1", 53, "Output", "WWAN_USB3_TX_N"),
    ("J1", 57, "Input", "WWAN_USB3_RX_P"),
    ("J1", 59, "Input", "WWAN_USB3_RX_N"),
    ("J1", 63, "Bidirectional", "WWAN_USB2_DP"),
    ("J1", 65, "Bidirectional", "WWAN_USB2_DM"),
    ("J1", 45, "Bidirectional", "TOUCH_USB_DP"),
    ("J1", 47, "Bidirectional", "TOUCH_USB_DM"),
    ("U13-B", 101, "Input", "REC_USB_ID"),
    ("U13-B", 103, "Bidirectional", "REC_USB_DM"),
    ("U13-B", 105, "Bidirectional", "REC_USB_DP"),
    ("J1", 97, "Input", "REC_USB_VBUS_DET"),
    ("U13-B", 170, "Output", "HDMI_D2_P"),
    ("U13-B", 172, "Output", "HDMI_D2_N"),
    ("U13-B", 176, "Output", "HDMI_D1_P"),
    ("U13-B", 178, "Output", "HDMI_D1_N"),
    ("U13-B", 182, "Output", "HDMI_D0_P"),
    ("U13-B", 184, "Output", "HDMI_D0_N"),
    ("U13-B", 188, "Output", "HDMI_CLK_P"),
    ("U13-B", 190, "Output", "HDMI_CLK_N"),
    ("U13-B", 151, "Bidirectional", "HDMI_CEC"),
    ("U13-B", 153, "Input", "HDMI_HPD"),
    ("U13-B", 199, "Bidirectional", "HDMI_DDC_SDA"),
    ("U13-B", 200, "Bidirectional", "HDMI_DDC_SCL"),
    ("U13-B", 145, "Bidirectional", "HDMI_HEAC_P"),
    ("U13-B", 147, "Bidirectional", "HDMI_HEAC_N"),
    ("U13-A", 34, "Output", "AUD_DAC_SDIN"),
    ("U13-A", 46, "Output", "AUD_BCLK"),
    ("U13-A", 48, "Output", "AUD_FSYNC"),
    ("U13-A", 50, "Output", "AUD_MCLK"),
    ("U13-A", 54, "Input", "AUD_ADC_SDOUT"),
    ("U13-A", 80, "Bidirectional", "SYS_I2C7_SCL"),
    ("U13-A", 82, "Bidirectional", "SYS_I2C7_SDA"),
    ("U13-A", 20, "Input", "AUD_IRQ_N"),
    ("U13-A", 100, "Output", "HS_MCLK"),
    ("U13-A", 28, "Output", "HS_BCLK"),
    ("U13-A", 30, "Output", "HS_LRCK"),
    ("U13-A", 31, "Output", "HS_SDOUT_TO_CODEC"),
    ("J1", 40, "Input", "HS_SDIN_FROM_CODEC"),
    ("J1", 4, "Bidirectional", "HS_I2C_SDA"),
    ("J1", 6, "Bidirectional", "HS_I2C_SCL"),
    ("J1", 36, "Input", "HS_JACK_DET_N"),
    ("U13-A", 51, "Input", "DBG_UART_RX"),
    ("U13-A", 55, "Output", "DBG_UART_TX"),
)

# These contacts remain owned by the allocation ledger but intentionally have
# no copper in Rev A: the selected two-LED WAN jack does not use native LED2,
# and the selected display does not use the HEAC/ARC return sideband.
CM5_ASSIGNED_NC = {("U13-A", 15), ("U13-B", 147)}

LAN7430_PINS = (
    (1, "AVDDH_1"), (2, "TXRXP_A"), (3, "TXRXM_A"), (4, "AVDDL_1"),
    (5, "TXRXP_B"), (6, "TXRXM_B"), (7, "TXRXP_C"), (8, "TXRXM_C"),
    (9, "AVDDL_2"), (10, "TXRXP_D"), (11, "TXRXM_D"), (12, "AVDDH_2"),
    (13, "VDD12CORE"), (14, "VP"), (15, "GD_1"), (16, "PCIE_RX_P"),
    (17, "PCIE_RX_M"), (18, "GD_2"), (19, "PCIE_TX_P"), (20, "VPTX"),
    (21, "PCIE_TX_M"), (22, "GD_3"), (23, "VPH"), (24, "RESREF"),
    (25, "PCIE_CLK_P"), (26, "PCIE_CLK_M"), (27, "VDD25_REG_OUT"),
    (28, "VDD_REG_IN"), (29, "RESET_N"), (30, "TEST"), (31, "VDD12CORE"),
    (32, "VDD12_SW_OUT"), (33, "VDD_SW_IN"), (34, "VDD12_SW_FB"),
    (35, "VAUX_DET/GPIO3/LED3/TCK"),
    (36, "EECLK/GPIO2/LED2/TMS/ADV_PM_DISABLE"),
    (37, "EEDIO/GPIO1/LED1/TDO"), (38, "EECS/GPIO0/LED0/TDI"),
    (39, "VDDVARIO"), (40, "VDD12CORE"), (41, "VDD_OTP"),
    (42, "CLKREQ#"), (43, "WAKE#"), (44, "PERST#"), (45, "AVDD12"),
    (46, "XO"), (47, "XI"), (48, "ISET"), (49, "VSS_EP"),
)

PI7_BALL_ROWS = {
    "A": ("CLKREQ_L[5]", "CLKREQ_L[4]", "PERP[7]", "PETP[7]", "PERP[6]", "PETP[6]", "REFCLKN[1]", "REXT[1]", "PETP[5]", "PERP[5]", "PETP[4]", "PERP[4]", "SHCL_I2C", "LNKSTS[4]"),
    "B": ("LNKSTS[2]", "CLKREQ_L[6]", "PERN[7]", "PETN[7]", "PERN[6]", "PETN[6]", "REFCLKP[1]", "REXT_GND[1]", "PETN[5]", "PERN[5]", "PETN[4]", "PERN[4]", "SHDA_I2C", "LNKSTS[3]/LNKSTS_DIS"),
    "C": ("NC", "LNKSTS[5]", "NC", "NC", "AGND", "AGND", "NC", "AVDDH", "AGND", "AGND", "AGND", "PERST_L", "CLKREQ_L[3]", "SHPCINT_L"),
    "D": ("GPIO[1]", "GPIO[0]", "NC", "VDDR", "VDDC", "VDDC", "AVDD", "AVDD", "VDDC", "VDDC", "VDDR", "CLKREQ_L[2]", "REFCLKOP[1]", "REFCLKON[1]"),
    "E": ("GPIO[4]", "GPIO[3]", "GPIO[2]", "VDDC", "DGND", "DGND", "DGND", "DGND", "DGND", "DGND", "VDDC", "IREF", "REFCLKOP[2]", "REFCLKON[2]"),
    "F": ("UPS_PORTSEL[1]/DBO[4]", "GPIO[5]", "UPS_PORTSEL[0]/DBO[3]", "NC", "DGND", "DGND", "DGND", "DGND", "DGND", "DGND", "CLKREQ_L[1]", "SDA_I2C", "REFCLKOP[3]", "REFCLKON[3]"),
    "G": ("NC", "UPS_PORTSEL[3]", "AVDDH", "VDDC", "DGND", "DGND", "DGND", "DGND", "DGND", "DGND", "VDDC", "CVDDR", "REFCLKIP", "REFCLKIN"),
    "H": ("NC", "UPS_PORTSEL[2]", "AGND", "VDDC", "DGND", "DGND", "DGND", "DGND", "DGND", "DGND", "VDDC", "CVDDR", "REFCLKOP[4]", "REFCLKON[4]"),
    "J": ("GPIO[7]", "RXPOLINV_DIS", "DBO[1]", "GPIO[6]", "DGND", "DGND", "DGND", "DGND", "DGND", "DGND", "SCL_I2C", "SWG_LVL", "REFCLKOP[5]", "REFCLKON[5]"),
    "K": ("NC", "NC", "DBO[2]", "VDDC", "DGND", "DGND", "DGND", "DGND", "DGND", "DGND", "VDDC", "EEDO", "REFCLKOP[6]", "REFCLKON[6]"),
    "L": ("SMBUS_EN_L", "CLKBUF_PD", "NC", "VDDR", "VDDC", "VDDC", "AVDD", "AVDD", "VDDC", "VDDC", "VDDR", "EECK", "REFCLKOP[7]", "REFCLKON[7]"),
    "M": ("NC", "DWNRST_L[1]", "DWNRST_L[4]", "DWNRST_L[5]", "AGND", "AGND", "AVDDH", "NC", "AGND", "AGND", "AGND", "EECS_L", "LNKSTS[1]/DBG_DIS", "EEDI"),
    "N": ("PL_512B/DBO[0]", "DWNRST_L[2]", "PERN[0]", "PETN[0]", "PERN[1]", "PETN[1]", "REXT_GND[0]", "REFCLKP[0]", "PETN[2]", "PERN[2]", "PETN[3]", "PERN[3]", "VC1_EN", "NC"),
    "P": ("NC", "DWNRST_L[3]", "PERP[0]", "PETP[0]", "PERP[1]", "PETP[1]", "REXT[0]", "REFCLKN[0]", "PETP[2]", "PERP[2]", "PETP[3]", "PERP[3]", "PWR_SAV_DIS", "TEST/LNKSTS[0]"),
}


def allocation_map() -> dict[tuple[str, int], tuple[str, str]]:
    return {(connector, pin): (direction, net) for connector, pin, direction, net in CM5_ALLOCATIONS}


def load_cm5_pinout() -> dict[str, list[tuple[int, str]]]:
    workbook = load_workbook(CM5_PINOUT, data_only=True, read_only=True)
    signal_columns = {"U13-A": 5, "U13-B": 3, "J1": 2}
    pinout: dict[str, list[tuple[int, str]]] = {}
    for connector, signal_column in signal_columns.items():
        sheet = workbook[connector]
        rows = []
        for row in sheet.iter_rows(min_row=3, max_row=102, values_only=True):
            pin = int(row[0])
            signal = str(row[signal_column - 1] or "NC")
            rows.append((pin, signal))
        if len(rows) != 100:
            raise RuntimeError(f"{connector} source has {len(rows)} pins, expected 100")
        pinout[connector] = rows
    return pinout


def _escape_symbol_text(value: str) -> str:
    return value.replace("\\", "\\\\").replace('"', '\\"')


def write_cm5_local_library() -> dict[str, list[tuple[int, str]]]:
    """Build exact CM5 mating symbols from Radxa's V2.21 pinout."""
    pinout = load_cm5_pinout()
    lines = ["(kicad_symbol_lib (version 20231120) (generator procomm_cm5_generator)"]
    for connector, pins in pinout.items():
        symbol_name = f"Radxa_CM5_{connector.replace('-', '_')}"
        start_pin = pins[0][0]
        body_bottom = -69.85 if connector == "U13-A" else -63.5
        lines.extend(
            [
                f'  (symbol "{symbol_name}" (pin_names (offset 0.9)) (in_bom yes) (on_board yes)',
                '    (property "Reference" "J" (at -25.4 67.31 0) (effects (font (size 1.27 1.27)) (justify left)))',
                f'    (property "Value" "RADXA CM5 {connector} MATE" (at -25.4 64.77 0) (effects (font (size 1.27 1.27)) (justify left)))',
                f'    (property "Footprint" "{CM5_DF40_FOOTPRINTS[connector]}" (at 0 0 0) (effects (font (size 1.27 1.27)) hide))',
                '    (property "Datasheet" "https://dl.radxa.com/cm5/v2210/radxa_cm5_v2210_pinout.xlsx" (at 0 0 0) (effects (font (size 1.27 1.27)) hide))',
                f'    (property "Description" "Radxa CM5 {connector}, all 100 physical contacts" (at 0 0 0) (effects (font (size 1.27 1.27)) hide))',
                f'    (symbol "{symbol_name}_0_1"',
                f'      (rectangle (start -25.4 63.5) (end 25.4 {body_bottom}) (stroke (width 0.254) (type default)) (fill (type background)))',
                "    )",
                f'    (symbol "{symbol_name}_1_1"',
            ]
        )
        for pin, signal in pins:
            row = (pin - start_pin) // 2
            y = 62.23 - row * 2.54
            is_left = pin % 2 == 1
            x = -27.94 if is_left else 27.94
            orientation = 0 if is_left else 180
            # These are physical carrier-side connector contacts.  Keep them
            # passive for ERC; direction at the CM5 is controlled separately
            # in CM5_ALLOCATIONS and the allocation workbook.
            pin_type = "passive"
            escaped = _escape_symbol_text(signal)
            lines.append(
                f'      (pin {pin_type} line (at {x:.2f} {y:.2f} {orientation}) (length 2.54) '
                f'(name "{escaped}" (effects (font (size 0.75 0.75)))) '
                f'(number "{pin}" (effects (font (size 0.75 0.75)))))'
            )
        if connector == "U13-A":
            for index, pin in enumerate(range(201, 205)):
                is_left = index % 2 == 0
                x = -27.94 if is_left else 27.94
                y = -66.04 - (index // 2) * 2.54
                orientation = 0 if is_left else 180
                lines.append(
                    f'      (pin passive line (at {x:.2f} {y:.2f} {orientation}) (length 2.54) '
                    f'(name "MODULE_MOUNT_GND_{pin - 200}" (effects (font (size 0.75 0.75)))) '
                    f'(number "{pin}" (effects (font (size 0.75 0.75)))))'
                )
        lines.extend(["    )", "  )"])

    lines.extend(
        [
            '  (symbol "LAN7430" (pin_names (offset 0.9)) (in_bom yes) (on_board yes)',
            '    (property "Reference" "U" (at -22.86 34.29 0) (effects (font (size 1.27 1.27)) (justify left)))',
            '    (property "Value" "LAN7430" (at -22.86 31.75 0) (effects (font (size 1.27 1.27)) (justify left)))',
            '    (property "Footprint" "Package_DFN_QFN:QFN-48-1EP_7x7mm_P0.5mm_EP5.3x5.3mm_ThermalVias" (at 0 0 0) (effects (font (size 1.27 1.27)) hide))',
            '    (property "Datasheet" "https://ww1.microchip.com/downloads/aemDocuments/documents/UNG/ProductDocuments/DataSheets/LAN7430-LAN7431-Data-Sheet-DS00002631.pdf" (at 0 0 0) (effects (font (size 1.27 1.27)) hide))',
            '    (property "Description" "48-pin VQFN PCIe to Gigabit Ethernet controller with integrated PHY" (at 0 0 0) (effects (font (size 1.27 1.27)) hide))',
            '    (symbol "LAN7430_0_1"',
            '      (rectangle (start -22.86 30.48) (end 22.86 -30.48) (stroke (width 0.254) (type default)) (fill (type background)))',
            '    )',
            '    (symbol "LAN7430_1_1"',
        ]
    )
    for index, (pin, signal) in enumerate(LAN7430_PINS):
        row = index // 2
        y = 29.21 - row * 2.54
        is_left = index % 2 == 0
        x = -25.4 if is_left else 25.4
        orientation = 0 if is_left else 180
        pin_type = "passive"
        lines.append(
            f'      (pin {pin_type} line (at {x:.2f} {y:.2f} {orientation}) (length 2.54) '
            f'(name "{_escape_symbol_text(signal)}" (effects (font (size 0.72 0.72)))) '
            f'(number "{pin}" (effects (font (size 0.72 0.72)))))'
        )
    lines.extend(["    )", "  )"])

    lines.extend(
        [
            '  (symbol "Crystal_GND24_3225" (pin_names (offset 0.9)) (in_bom yes) (on_board yes)',
            '    (property "Reference" "Y" (at -5.08 7.62 0) (effects (font (size 1.27 1.27))))',
            '    (property "Value" "Crystal_GND24_3225" (at 0 -7.62 0) (effects (font (size 1.27 1.27))))',
            '    (property "Footprint" "Crystal:Crystal_SMD_3225-4Pin_3.2x2.5mm" (at 0 0 0) (effects (font (size 1.27 1.27)) hide))',
            '    (property "Datasheet" "https://abracon.com/Resonators/abm8.pdf" (at 0 0 0) (effects (font (size 1.27 1.27)) hide))',
            '    (property "Description" "Four-pad 3225 crystal with grounded case pads 2 and 4" (at 0 0 0) (effects (font (size 1.27 1.27)) hide))',
            '    (symbol "Crystal_GND24_3225_0_1"',
            '      (rectangle (start -2.54 1.27) (end 2.54 -1.27) (stroke (width 0.254) (type default)) (fill (type background)))',
            '    )',
            '    (symbol "Crystal_GND24_3225_1_1"',
            '      (pin passive line (at -5.08 0 0) (length 2.54) (name "XI" (effects (font (size 0.72 0.72)))) (number "1" (effects (font (size 0.72 0.72)))))',
            '      (pin power_in line (at 0 -5.08 90) (length 3.81) (name "GND" (effects (font (size 0.72 0.72)))) (number "2" (effects (font (size 0.72 0.72)))))',
            '      (pin passive line (at 5.08 0 180) (length 2.54) (name "XO" (effects (font (size 0.72 0.72)))) (number "3" (effects (font (size 0.72 0.72)))))',
            '      (pin power_in line (at 0 5.08 270) (length 3.81) (name "GND" (effects (font (size 0.72 0.72)))) (number "4" (effects (font (size 0.72 0.72)))))',
            '    )',
            '  )',
        ]
    )

    power_names = {"VDDC", "VDDR", "CVDDR", "AVDD", "AVDDH", "AGND", "DGND"}
    pi7_units: dict[int, list[tuple[str, str]]] = {1: [], 2: [], 3: []}
    for row_name, names in PI7_BALL_ROWS.items():
        for column, signal in enumerate(names, start=1):
            ball = f"{row_name}{column}"
            if signal in power_names:
                unit = 3
            elif signal.startswith(("PER", "PET", "REFCLK", "CLKREQ", "DWNRST")) or signal == "PERST_L":
                unit = 1
            else:
                unit = 2
            pi7_units[unit].append((ball, signal))
    lines.extend(
        [
            '  (symbol "PI7C9X2G608GP" (pin_names (offset 0.9)) (in_bom yes) (on_board yes)',
            '    (property "Reference" "U" (at -25.4 2.54 0) (effects (font (size 1.27 1.27)) (justify left)))',
            '    (property "Value" "PI7C9X2G608GP" (at -25.4 0 0) (effects (font (size 1.27 1.27)) (justify left)))',
            '    (property "Footprint" "Package_BGA:BGA-196_15x15mm_Layout14x14_P1.0mm" (at 0 0 0) (effects (font (size 1.27 1.27)) hide))',
            '    (property "Datasheet" "https://www.diodes.com/datasheet/download/PI7C9X2G608GP.pdf" (at 0 0 0) (effects (font (size 1.27 1.27)) hide))',
            '    (property "Description" "196-ball LBGA, six-port/eight-lane PCIe Gen2 packet switch" (at 0 0 0) (effects (font (size 1.27 1.27)) hide))',
            '    (property "Manufacturer" "Diodes Incorporated" (at 0 0 0) (effects (font (size 1.27 1.27)) hide))',
            '    (property "MPN" "PI7C9X2G608GPCNJEX" (at 0 0 0) (effects (font (size 1.27 1.27)) hide))',
        ]
    )
    for unit, pins in pi7_units.items():
        rows = (len(pins) + 1) // 2
        half_height = max(12.7, rows * 1.27 + 2.54)
        lines.extend(
            [
                f'    (symbol "PI7C9X2G608GP_{unit}_1"',
                f'      (rectangle (start -25.4 {half_height:.2f}) (end 25.4 {-half_height:.2f}) (stroke (width 0.254) (type default)) (fill (type background)))',
            ]
        )
        for index, (ball, signal) in enumerate(pins):
            row = index // 2
            y = half_height - 2.54 - row * 2.54
            is_left = index % 2 == 0
            x = -27.94 if is_left else 27.94
            orientation = 0 if is_left else 180
            pin_type = "passive"
            lines.append(
                f'      (pin {pin_type} line (at {x:.2f} {y:.2f} {orientation}) (length 2.54) '
                f'(name "{_escape_symbol_text(signal)}" (effects (font (size 0.68 0.68)))) '
                f'(number "{ball}" (effects (font (size 0.68 0.68)))))'
            )
        lines.append("    )")
    lines.append("  )")

    local_symbols = (
        (
            "Bel_V8BR_1AX1_GH",
            "J",
            "V8BR-1AX1-GH",
            "CM5Carrier:Bel_V8BR_1AX1_GH",
            "https://www.belfuse.com/media/drawings/products/magjack%20ICMs/dr-MAG-V8BR-1AX1-GH.pdf",
            "Vertical 1000BASE-T MagJack with exposed PHY and cable center taps",
            (
                (1, "TRCT3"), (2, "TRD3-"), (3, "TRD3+"),
                (4, "TRD2+"), (5, "TRD2-"), (6, "TRCT2"),
                (7, "TRCT4"), (8, "TRD4+"), (9, "TRD4-"),
                (10, "TRD1-"), (11, "TRD1+"), (12, "TRCT1"),
                (13, "VC12"), (14, "VC36"), (15, "VC45"),
                (16, "VC78"), (17, "LED1-"), (18, "LED1+"),
                (19, "LED2-"), (20, "LED2+"),
                (21, "SHIELD"), (22, "SHIELD"),
            ),
        ),
        (
            "LM5146RGY",
            "U",
            "LM5146RGYR",
            "Package_DFN_QFN:Texas_RGY_R-PVQFN-N20_EP2.05x3.05mm_ThermalVias",
            "https://www.ti.com/lit/ds/symlink/lm5146.pdf",
            "100 V synchronous buck controller in 20-pin RGY VQFN",
            (
                (1, "EN/UVLO"), (2, "RT"), (3, "SS/TRK"), (4, "COMP"),
                (5, "FB"), (6, "AGND"), (7, "SYNCOUT"), (8, "SYNCIN"),
                (9, "NC"), (10, "PGOOD"), (11, "ILIM"), (12, "PGND"),
                (13, "LO"), (14, "VCC"), (15, "EP"), (16, "NC"),
                (17, "BST"), (18, "HO"), (19, "SW"), (20, "VIN"),
            ),
        ),
        (
            "LM61460RJR",
            "U",
            "LM61460RJR",
            "",
            "https://www.ti.com/lit/ds/symlink/lm61460.pdf",
            "36 V 6 A synchronous buck converter in 14-pin RJR VQFN-HR",
            (
                (1, "BIAS"), (2, "VCC"), (3, "AGND"), (4, "FB"),
                (5, "PGOOD"), (6, "RT"), (7, "EN/SYNC"), (8, "VIN1"),
                (9, "PGND1"), (10, "SW"), (11, "PGND2"), (12, "VIN2"),
                (13, "RBOOT"), (14, "CBOOT"),
            ),
        ),
        (
            "LM61440RJR",
            "U",
            "LM61440RJR",
            "",
            "https://www.ti.com/lit/ds/symlink/lm61440.pdf",
            "36 V 4 A synchronous buck converter in 14-pin RJR VQFN-HR",
            (
                (1, "BIAS"), (2, "VCC"), (3, "AGND"), (4, "FB"),
                (5, "PGOOD"), (6, "RT"), (7, "EN/SYNC"), (8, "VIN1"),
                (9, "PGND1"), (10, "SW"), (11, "PGND2"), (12, "VIN2"),
                (13, "RBOOT"), (14, "CBOOT"),
            ),
        ),
        (
            "LM5176PWP_A1",
            "U",
            "LM5176PWP",
            "Package_SO:HTSSOP-28-1EP_4.4x9.7mm_P0.65mm_EP3.4x9.5mm_ThermalVias",
            "https://www.ti.com/lit/ds/symlink/lm5176.pdf",
            "55 V four-switch buck-boost controller in 28-pin PWP HTSSOP",
            (
                (1, "EN/UVLO"), (2, "VIN"), (3, "VISNS"), (4, "MODE"),
                (5, "DITH"), (6, "RT/SYNC"), (7, "SLOPE"), (8, "SS"),
                (9, "COMP"), (10, "AGND"), (11, "FB"), (12, "VOSNS"),
                (13, "ISNS-"), (14, "ISNS+"), (15, "CSG"), (16, "CS"),
                (17, "PGOOD"), (18, "SW2"), (19, "HDRV2"), (20, "BOOT2"),
                (21, "LDRV2"), (22, "PGND"), (23, "VCC"), (24, "BIAS"),
                (25, "LDRV1"), (26, "BOOT1"), (27, "HDRV1"), (28, "SW1"),
                (29, "EP"),
            ),
        ),
        (
            "TPS62913RPU",
            "U",
            "TPS62913RPU",
            "Package_DFN_QFN:Texas_RPU0010A_VQFN-HR-10_2x2mm_P0.5mm",
            "https://www.ti.com/lit/ds/symlink/tps62913.pdf",
            "17 V 3 A low-noise buck converter in exact 10-pin RPU QFN pinout",
            (
                (1, "EN/SYNC"), (2, "SW"), (3, "VO"), (4, "PGND"),
                (5, "PG"), (6, "VIN"), (7, "PSNS"), (8, "NR/SS"),
                (9, "FB"), (10, "S-CONF"),
            ),
        ),
        (
            "TPS259827LNRGE",
            "U",
            "TPS259827LNRGER",
            "Package_DFN_QFN:Texas_RGE0024H_VQFN-24-1EP_4x4mm_P0.5mm_EP2.7x2.7mm_ThermalVias",
            "https://www.ti.com/lit/ds/symlink/tps25982.pdf",
            "24 V 15 A eFuse, no fixed OVLO, active current-limiter variant",
            (
                (1, "IN1"), (2, "IN2"), (3, "IN3"), (4, "GND1"),
                (5, "GND2"), (6, "EN/UVLO"), (7, "ITIMER"), (8, "ILIM"),
                (9, "IMON"), (10, "RETRY_DLY"), (11, "NRETRY"), (12, "LDSTRT"),
                (13, "PG"), (14, "GND3"), (15, "dVdt"), (16, "IN4"),
                (17, "OUT1"), (18, "OUT2"), (19, "OUT3"), (20, "OUT4"),
                (21, "OUT5"), (22, "OUT6"), (23, "OUT7"), (24, "OUT8"),
            ),
        ),
        (
            "TPS22990DML",
            "U",
            "TPS22990DMLR",
            "",
            "https://www.ti.com/lit/ds/symlink/tps22990.pdf",
            "5.5 V 10 A controlled-rise-time load switch",
            (
                (1, "CT"), (2, "NC"), (3, "VIN"), (4, "VBIAS"),
                (5, "ON"), (6, "GND"), (7, "PG"), (8, "VOUT1"),
                (9, "VOUT2"), (10, "VOUT3"),
            ),
        ),
        (
            "TRI20_1223",
            "U",
            "TRI 20-1223",
            "",
            "https://www.tracopower.com/tri20-datasheet",
            "20 W reinforced-isolation 12 V to dual 15 V DC/DC module",
            (
                (1, "+VIN"), (2, "-VIN"), (3, "+VOUT"),
                (4, "COMMON"), (5, "-VOUT"),
            ),
        ),
        (
            "TPS7A20DBV_A1",
            "U",
            "TPS7A20 fixed DBV",
            "Package_TO_SOT_SMD:SOT-23-5",
            "https://www.ti.com/lit/ds/symlink/tps7a20.pdf",
            "300 mA low-noise fixed-output LDO in SOT-23-5",
            (
                (1, "IN"), (2, "GND"), (3, "EN"), (4, "NC"), (5, "OUT"),
            ),
        ),
        (
            "PCA9517ADP_A1",
            "U",
            "PCA9517ADP",
            "Package_SO:TSSOP-8_3x3mm_P0.65mm",
            "https://www.nxp.com/docs/en/data-sheet/PCA9517A.pdf",
            "Fast-mode I2C repeater used to isolate the off-board audio-control bus",
            (
                (1, "VCCA"), (2, "SCLA"), (3, "SDAA"), (4, "GND"),
                (5, "EN"), (6, "SDAB"), (7, "SCLB"), (8, "VCCB"),
            ),
        ),
        (
            "FSA2567MPX",
            "U",
            "FSA2567MPX",
            "Package_DFN_QFN:WQFN-16-1EP_3x3mm_P0.5mm_EP1.68x1.68mm",
            "https://www.onsemi.com/pdf/datasheet/fsa2567-d.pdf",
            "Dual-SIM four-pole analog switch",
            (
                (1, "1VSIM"), (2, "SEL"), (3, "2RST"), (4, "RST"),
                (5, "1RST"), (6, "GND"), (7, "2CLK"), (8, "CLK"),
                (9, "1CLK"), (10, "NC"), (11, "2DAT"), (12, "DAT"),
                (13, "1DAT"), (14, "VCC"), (15, "2VSIM"), (16, "VSIM"),
                (17, "EP"),
            ),
        ),
        (
            "Mini_PCIe_52",
            "J",
            "Molex 0679101002 / AW7915-NP1",
            "CM5Carrier:Molex_0679101002_Mini_PCIe",
            "https://www.molex.com/en-us/products/part-detail/0679101002",
            "52-contact Mini PCIe socket with the standard PCIe/USB/UIM pin assignment",
            (
                (1, "WAKE#"), (2, "+3V3AUX"), (3, "COEX1"), (4, "GND"),
                (5, "COEX2"), (6, "+1V5"), (7, "CLKREQ#"), (8, "UIM_PWR"),
                (9, "GND"), (10, "UIM_DATA"), (11, "REFCLK-"), (12, "UIM_CLK"),
                (13, "REFCLK+"), (14, "UIM_RESET"), (15, "GND"), (16, "UIM_VPP"),
                (17, "RESERVED"), (18, "GND"), (19, "RESERVED"), (20, "W_DISABLE#"),
                (21, "GND"), (22, "PERST#"), (23, "PERn0"), (24, "+3V3AUX"),
                (25, "PERp0"), (26, "GND"), (27, "GND"), (28, "+1V5"),
                (29, "GND"), (30, "SMB_CLK"), (31, "PETn0"), (32, "SMB_DATA"),
                (33, "PETp0"), (34, "GND"), (35, "GND"), (36, "USB_D-"),
                (37, "GND"), (38, "USB_D+"), (39, "+3V3AUX"), (40, "GND"),
                (41, "+3V3AUX"), (42, "LED_WWAN#"), (43, "GND"), (44, "LED_WLAN#"),
                (45, "RESERVED"), (46, "LED_WPAN#"), (47, "RESERVED"), (48, "+1V5"),
                (49, "RESERVED"), (50, "GND"), (51, "RESERVED"), (52, "+3V3AUX"),
            ),
        ),
        (
            "Wurth_Nano_SIM_693043020611",
            "J",
            "693043020611",
            "CM5Carrier:J_Wurth_WR-CRD_693043020611",
            "https://www.we-online.com/components/products/datasheet/693043020611.pdf",
            "Wurth WR-CRD push-push nano-SIM holder",
            (
                ("C1", "VCC"), ("C2", "RESET"), ("C3", "CLOCK"),
                ("C5", "GND"), ("C6", "VPP_NC"), ("C7", "I/O"),
                ("S1", "SHIELD"), ("S2", "SHIELD"), ("S3", "SHIELD"),
                ("S4", "SHIELD"), ("S5", "SHIELD"), ("S6", "SHIELD"),
            ),
        ),
        (
            "ES8316",
            "U",
            "ES8316",
            "Package_DFN_QFN:QFN-32-1EP_4x4mm_P0.4mm_EP2.9x2.9mm_ThermalVias",
            "https://dl.radxa.com/cm5/radxa_cm5_io_board_v2200_schematic.pdf",
            "Low-power stereo audio codec; exact pinout follows Radxa CM5 IO V2.2",
            (
                (1, "CCLK"), (2, "MCLK"), (3, "DVDD"), (4, "PVDD"),
                (5, "DGND"), (6, "SCLK"), (7, "DSDIN"), (8, "DLRCK"),
                (9, "ASDOUT"), (10, "GPIO1"), (11, "GPIO2"), (12, "GPIO3"),
                (13, "CPVSSP"), (14, "CPVDD"), (15, "CPTOP"), (16, "CPBOT"),
                (17, "CPGND"), (18, "CPGNDREF"), (19, "ROUT"), (20, "LOUT"),
                (21, "DACVREF"), (22, "AVDD"), (23, "AGND"), (24, "ADCVREF"),
                (25, "VMID"), (26, "MICBIAS"), (27, "RIN2"), (28, "LIN2"),
                (29, "RIN1"), (30, "LIN1"), (31, "CE"), (32, "CDATA"),
                (33, "E-PAD"),
            ),
        ),
        (
            "AK5558VN",
            "U",
            "AK5558VN",
            "Package_DFN_QFN:QFN-64-1EP_9x9mm_P0.5mm_EP6x6mm_ThermalVias",
            "https://www.akm-semi.com/pdf-0f/ak5558vn.pdf",
            "Eight-channel 32-bit ADC; exact 64-QFN pin assignment",
            (
                (1, "AVSS1"), (2, "AVDD1"), (3, "AIN3P"), (4, "AIN3N"),
                (5, "VREFL2"), (6, "VREFH2"), (7, "AIN4N"), (8, "AIN4P"),
                (9, "AIN5P"), (10, "AIN5N"), (11, "VREFH3"), (12, "VREFL3"),
                (13, "AIN6N"), (14, "AIN6P"), (15, "AVDD2"), (16, "AVSS2"),
                (17, "AIN7P"), (18, "AIN7N"), (19, "VREFH4"), (20, "VREFL4"),
                (21, "AIN8N"), (22, "AIN8P"), (23, "TEST"), (24, "MCLK"),
                (25, "TVDD"), (26, "DVSS"), (27, "VDD18"), (28, "PDN"),
                (29, "PW0"), (30, "PW1"), (31, "PW2"), (32, "MSN"),
                (33, "BICK/DCLK"), (34, "LRCK/DSDOL1"), (35, "TDMIN/DSDOR1"),
                (36, "SDTO1/DSDOL2"), (37, "SDTO2/DSDOR2"),
                (38, "SDTO3/DSDOL3"), (39, "SDTO4/DSDOR3"),
                (40, "DSDOL4"), (41, "DSDOR4"), (42, "OVF"),
                (43, "CKS0/SDA/CDTI"), (44, "CKS1/CAD0_I2C/CSN"),
                (45, "CKS2/SCL/CCLK"), (46, "CKS3/CAD1"),
                (47, "SLOW/DCKB"), (48, "SD/PMOD"), (49, "DIF0/DSDSEL0"),
                (50, "DIF1/DSDSEL1"), (51, "TDM0"), (52, "TDM1"),
                (53, "PSN/CAD0_SPI"), (54, "I2C"), (55, "DP"),
                (56, "HPFE/DCKS"), (57, "LDOE"), (58, "ODP"),
                (59, "AIN1P"), (60, "AIN1N"), (61, "VREFL1"),
                (62, "VREFH1"), (63, "AIN2N"), (64, "AIN2P"),
                (65, "EP"),
            ),
        ),
        (
            "AK4458VN",
            "U",
            "AK4458VN",
            "Package_DFN_QFN:QFN-48-1EP_7x7mm_P0.5mm_EP5.15x5.15mm_ThermalVias",
            "https://www.akm-semi.com/pdf-c1/ak4458vn.pdf",
            "Eight-channel premium DAC; exact 48-QFN pin assignment",
            (
                (1, "MCLK"), (2, "BICK/DCLK"), (3, "LRCK/DSDL1"),
                (4, "SDTI1/DSDR1"), (5, "SDTI2/DSDL2"),
                (6, "SDTI3/DSDR2/TDMO1"), (7, "SDTI4/DSDL3/TDMO2"),
                (8, "DSDR3"), (9, "DSDL4"), (10, "DSDR4"),
                (11, "DZF/SMUTE"), (12, "CAD1/DCHAIN"),
                (13, "SDA/CDTI/TDM0"), (14, "SCL/CCLK/TDM1"),
                (15, "CAD0_I2C/CSN/DIF"), (16, "PS/CAD0_SPI"), (17, "I2C"),
                (18, "AOUTL1P"), (19, "AOUTL1N"), (20, "VREFL1"),
                (21, "VREFH1"), (22, "AOUTR1N"), (23, "AOUTR1P"),
                (24, "AOUTL2P"), (25, "AOUTL2N"), (26, "VREFL2"),
                (27, "VREFH2"), (28, "AOUTR2N"), (29, "AOUTR2P"),
                (30, "AVSS"), (31, "AVDD"), (32, "AOUTL3P"),
                (33, "AOUTL3N"), (34, "VREFH3"), (35, "VREFL3"),
                (36, "AOUTR3N"), (37, "AOUTR3P"), (38, "AOUTL4P"),
                (39, "AOUTL4N"), (40, "VREFH4"), (41, "VREFL4"),
                (42, "AOUTR4N"), (43, "AOUTR4P"), (44, "LDOE"),
                (45, "TVDD"), (46, "DVSS"), (47, "VDD18"), (48, "PDN"),
                (49, "EP"),
            ),
        ),
        (
            "THAT1206",
            "U",
            "THAT1206S08-U",
            "Package_SO:SOIC-8_3.9x4.9mm_P1.27mm",
            "https://www.thatcorp.com/datashts/THAT_1200-Series_Datasheet.pdf",
            "Minus-six-decibel InGenius balanced line receiver",
            ((1, "REF"), (2, "IN-"), (3, "IN+"), (4, "VEE"),
             (5, "CM_IN"), (6, "VOUT"), (7, "VCC"), (8, "CM_OUT")),
        ),
        (
            "THAT1646",
            "U",
            "THAT1646S08-U",
            "Package_SO:SOIC-8_3.9x4.9mm_P1.27mm",
            "https://thatcorp.com/datashts/THAT_1606-1646_Datasheet.pdf",
            "OutSmarts balanced line driver with six-decibel gain",
            ((1, "OUT-"), (2, "SNS-"), (3, "GND"), (4, "IN"),
             (5, "VEE"), (6, "VCC"), (7, "SNS+"), (8, "OUT+")),
        ),
        (
            "OPA1652",
            "U",
            "OPA1652AIDR",
            "Package_SO:SOIC-8_3.9x4.9mm_P1.27mm",
            "https://www.ti.com/lit/ds/symlink/opa1654.pdf",
            "Dual low-noise FET-input audio operational amplifier",
            ((1, "OUT_A"), (2, "IN_A-"), (3, "IN_A+"), (4, "V-"),
             (5, "IN_B+"), (6, "IN_B-"), (7, "OUT_B"), (8, "V+")),
        ),
        (
            "Panasonic_TQ2_12V",
            "K",
            "TQ2-12V",
            "CM5Carrier:Panasonic_TQ2-12V_PRELIMINARY",
            "https://na.industrial.panasonic.com/products/relays-contactors/mechanical-signal-relays/series/119572/model/119888",
            "Sealed 12 V DPDT signal relay; footprint remains drawing/coupon gated",
            ((1, "COIL+"), (2, "NC1"), (3, "COM1"), (4, "NO1"),
             (7, "NO2"), (8, "COM2"), (9, "NC2"), (10, "COIL-")),
        ),
        (
            "Kycon_STX_353K7A_6N",
            "J",
            "STX-353K7A-6N-KTTR",
            "CM5Carrier:Kycon_STX-353K7A-6N-KTTR_PRELIMINARY",
            "https://www.kycon.com/Catalog_PDF/STX-353K7A.pdf",
            "Kycon vertical four-pole jack with an isolated insertion switch",
            (
                (1, "SLEEVE_MIC"), (2, "R2_GND"), (3, "R1_HP_R"),
                (4, "TIP_HP_L"), (5, "SWITCH_A"), (6, "SWITCH_B"),
            ),
        ),
    )
    for name, reference, value, footprint, datasheet, description, pins in local_symbols:
        rows = (len(pins) + 1) // 2
        half_height = max(10.16, rows * 1.27 + 2.54)
        lines.extend(
            [
                f'  (symbol "{name}" (pin_names (offset 0.9)) (in_bom yes) (on_board yes)',
                f'    (property "Reference" "{reference}" (at {-17.78:.2f} {half_height + 3.81:.2f} 0) (effects (font (size 1.27 1.27)) (justify left)))',
                f'    (property "Value" "{value}" (at {-17.78:.2f} {half_height + 1.27:.2f} 0) (effects (font (size 1.27 1.27)) (justify left)))',
                f'    (property "Footprint" "{footprint}" (at 0 0 0) (effects (font (size 1.27 1.27)) hide))',
                f'    (property "Datasheet" "{datasheet}" (at 0 0 0) (effects (font (size 1.27 1.27)) hide))',
                f'    (property "Description" "{description}" (at 0 0 0) (effects (font (size 1.27 1.27)) hide))',
                f'    (symbol "{name}_0_1"',
                f'      (rectangle (start -17.78 {half_height:.2f}) (end 17.78 {-half_height:.2f}) (stroke (width 0.254) (type default)) (fill (type background)))',
                "    )",
                f'    (symbol "{name}_1_1"',
            ]
        )
        for index, (pin, signal) in enumerate(pins):
            row = index // 2
            y = half_height - 2.54 - row * 2.54
            is_left = index % 2 == 0
            x = -20.32 if is_left else 20.32
            orientation = 0 if is_left else 180
            lines.append(
                f'      (pin passive line (at {x:.2f} {y:.2f} {orientation}) (length 2.54) '
                f'(name "{_escape_symbol_text(signal)}" (effects (font (size 0.72 0.72)))) '
                f'(number "{pin}" (effects (font (size 0.72 0.72)))))'
            )
        lines.extend(["    )", "  )"])

    cm5_audio_port_pins = (
        (1, "AUD_MCLK", "output"), (2, "AUD_BCLK", "output"),
        (3, "AUD_FSYNC", "output"), (4, "AUD_DAC_SDIN", "output"),
        (5, "AUD_ADC_SDOUT", "passive"), (6, "SYS_I2C7_SCL", "bidirectional"),
        (7, "SYS_I2C7_SDA", "bidirectional"), (8, "AUD_IRQ_N", "passive"),
        (9, "HS_MCLK", "output"), (10, "HS_BCLK", "output"),
        (11, "HS_LRCK", "output"), (12, "HS_SDOUT_TO_CODEC", "output"),
        (13, "HS_SDIN_FROM_CODEC", "passive"), (14, "HS_I2C_SCL", "bidirectional"),
        (15, "HS_I2C_SDA", "bidirectional"), (16, "HS_JACK_DET_N", "passive"),
    )
    lines.extend(
        [
            '  (symbol "CM5_Audio_Port" (pin_names (offset 0.9)) (in_bom no) (on_board no)',
            '    (property "Reference" "U" (at -20.32 25.4 0) (effects (font (size 1.27 1.27)) (justify left)))',
            '    (property "Value" "CM5 AUDIO OFF-SHEET PORT" (at -20.32 22.86 0) (effects (font (size 1.27 1.27)) (justify left)))',
            '    (property "Footprint" "" (at 0 0 0) (effects (font (size 1.27 1.27)) hide))',
            '    (property "Datasheet" "" (at 0 0 0) (effects (font (size 1.27 1.27)) hide))',
            '    (property "Description" "Typed off-sheet CM5 audio interface for ERC" (at 0 0 0) (effects (font (size 1.27 1.27)) hide))',
            '    (symbol "CM5_Audio_Port_0_1"',
            '      (rectangle (start -20.32 20.32) (end 20.32 -20.32) (stroke (width 0.254) (type default)) (fill (type background)))',
            '    )',
            '    (symbol "CM5_Audio_Port_1_1"',
        ]
    )
    for index, (pin, signal, pin_type) in enumerate(cm5_audio_port_pins):
        row = index // 2
        y = 17.78 - row * 5.08
        is_left = index % 2 == 0
        x = -22.86 if is_left else 22.86
        orientation = 0 if is_left else 180
        lines.append(
            f'      (pin {pin_type} line (at {x:.2f} {y:.2f} {orientation}) (length 2.54) '
            f'(name "{signal}" (effects (font (size 0.75 0.75)))) '
            f'(number "{pin}" (effects (font (size 0.75 0.75)))))'
        )
    lines.extend(["    )", "  )"])
    lines.append(")")
    CM5_LOCAL_LIBRARY.parent.mkdir(parents=True, exist_ok=True)
    CM5_LOCAL_LIBRARY.write_text("\n".join(lines) + "\n")
    (CM5_LOCAL_LIBRARY.parent / "sym-lib-table").write_text(
        '(sym_lib_table\n'
        '  (version 7)\n'
        '  (lib (name "CM5Carrier")(type "KiCad")(uri "${KIPRJMOD}/CM5Carrier.kicad_sym")(options "")(descr "Radxa CM5 carrier-local symbols"))\n'
        ')\n'
    )
    audio_folder = ROOT / "AUDIO-8X8"
    audio_folder.mkdir(parents=True, exist_ok=True)
    (audio_folder / "sym-lib-table").write_text(
        '(sym_lib_table\n'
        '  (version 7)\n'
        '  (lib (name "CM5Carrier")(type "KiCad")(uri "${KIPRJMOD}/../CM5-CARRIER/CM5Carrier.kicad_sym")(options "")(descr "Shared Radxa CM5 carrier and audio symbols"))\n'
        ')\n'
    )
    sim_folder = ROOT / "SIM-SERVICE"
    sim_folder.mkdir(parents=True, exist_ok=True)
    (sim_folder / "sym-lib-table").write_text(
        '(sym_lib_table\n'
        '  (version 7)\n'
        '  (lib (name "CM5Carrier")(type "KiCad")(uri "${KIPRJMOD}/../CM5-CARRIER/CM5Carrier.kicad_sym")(options "")(descr "Shared carrier and service-board symbols"))\n'
        ')\n'
    )
    return pinout


def _balanced_sexpr(text: str, start: int) -> str:
    """Return one balanced KiCad S-expression beginning at start."""
    depth = 0
    quoted = False
    escaped = False
    for index in range(start, len(text)):
        character = text[index]
        if quoted:
            if escaped:
                escaped = False
            elif character == "\\":
                escaped = True
            elif character == '"':
                quoted = False
            continue
        if character == '"':
            quoted = True
        elif character == "(":
            depth += 1
        elif character == ")":
            depth -= 1
            if depth == 0:
                return text[start:index + 1]
    raise RuntimeError("Unbalanced KiCad S-expression in imported Radxa board")


def _top_level_sexprs(expression: str) -> list[str]:
    """Return the direct child expressions of a KiCad S-expression."""
    children: list[str] = []
    depth = 0
    quoted = False
    escaped = False
    child_start: int | None = None
    for index, character in enumerate(expression):
        if quoted:
            if escaped:
                escaped = False
            elif character == "\\":
                escaped = True
            elif character == '"':
                quoted = False
            continue
        if character == '"':
            quoted = True
        elif character == "(":
            depth += 1
            if depth == 2:
                child_start = index
        elif character == ")":
            if depth == 2 and child_start is not None:
                children.append(expression[child_start:index + 1])
                child_start = None
            depth -= 1
    return children


def _sexpr_name(expression: str) -> str:
    match = re.match(r"\(\s*([^\s()]+)", expression)
    if not match:
        raise RuntimeError(f"Cannot identify KiCad expression: {expression[:80]!r}")
    return match.group(1)


def _strip_board_ownership(expression: str) -> str:
    """Remove board-instance fields while preserving source geometry."""
    return re.sub(
        r"\n\s*\((?:net|uuid|path)\s+[^\n()]*\)",
        "",
        expression,
    )


def _imported_footprint(board_text: str, reference: str) -> str:
    marker = f'(property "Reference" "{reference}"'
    property_offset = board_text.find(marker)
    if property_offset < 0:
        raise RuntimeError(f"Official Radxa board has no {reference} footprint")
    footprint_offset = board_text.rfind("(footprint ", 0, property_offset)
    if footprint_offset < 0:
        raise RuntimeError(f"Cannot locate official Radxa {reference} footprint")
    return _balanced_sexpr(board_text, footprint_offset)


def _write_official_footprint(
    name: str,
    description: str,
    reference_position: tuple[float, float],
    children: list[str],
) -> None:
    """Write a footprint made only from geometry imported from Radxa's PCB."""
    x, y = reference_position
    lines = [
        f'(footprint "{name}"',
        '  (version 20240108)',
        '  (generator "procomm_radxa_official_pads_import")',
        '  (layer "F.Cu")',
        f'  (descr "{description}")',
        '  (tags "Radxa CM5 official V2.20 DF40 exact mating geometry")',
        f'  (property "Reference" "REF**" (at {x:.3f} {y:.3f} 0) (layer "F.SilkS") (effects (font (size 0.8 0.8) (thickness 0.12))))',
        f'  (property "Value" "{name}" (at {x:.3f} {y + 2.0:.3f} 0) (layer "F.Fab") hide (effects (font (size 0.8 0.8) (thickness 0.12))))',
        '  (attr smd)',
    ]
    for child in children:
        sanitized = _strip_board_ownership(child)
        if _sexpr_name(child).startswith("fp_"):
            # PADS assembly/component outlines are mating references, not
            # guaranteed production silkscreen. Preserve them on Fab so source
            # geometry remains visible without printing ink across 0.4 mm pads.
            sanitized = sanitized.replace('(layer "F.SilkS")', '(layer "F.Fab")')
        lines.extend("  " + line.expandtabs(2) for line in sanitized.splitlines())
    lines.append(")")
    (CM5_LOCAL_FOOTPRINTS / f"{name}.kicad_mod").write_text("\n".join(lines) + "\n")


def _radxa_df40_decal_contract() -> None:
    """Verify the native PADS decal before correcting the KiCad import artifact."""
    source = RADXA_CM5_IO_ASC.read_text(errors="replace")
    start_match = re.search(r"^DF40C_100DS\s+M\s", source, re.MULTILINE)
    if not start_match:
        raise RuntimeError("Official Radxa source has no DF40C_100DS PADS decal")
    next_decal = re.search(
        r"^[A-Za-z0-9_+.-]+\s+M\s",
        source[start_match.end():],
        re.MULTILINE,
    )
    if not next_decal:
        raise RuntimeError("Cannot delimit the official DF40C_100DS PADS decal")
    decal = source[start_match.start():start_match.end() + next_decal.start()]
    pins = [
        int(pin)
        for pin in re.findall(
            r"^T-?\d+\s+-?\d+\s+-?\d+\s+-?\d+\s+(\d+)\s*$",
            decal,
            re.MULTILINE,
        )
    ]
    if pins != list(range(1, 101)):
        raise RuntimeError("Official DF40C_100DS decal does not contain ordered pins 1-100")
    pad_stack = re.search(
        r"^PAD 0 3\s*\n-2 300000 RF\s+0\.000 1710000\b",
        decal,
        re.MULTILINE,
    )
    if not pad_stack:
        raise RuntimeError(
            "Official DF40C_100DS PADS stack is not 0.20 x 1.14 mm at 0 degrees"
        )


def _normalize_j24_imported_pad_angles(children: list[str]) -> list[str]:
    """Remove KiCad's proven double application of J24's 270-degree rotation.

    Radxa's native DF40C_100DS decal defines its 1.14 x 0.20 mm rectangular
    land at 0 degrees. J24 is then placed at 270 degrees on the Radxa IO board.
    KiCad 10.0.5 converts the pad coordinates into footprint-local coordinates
    but incorrectly retains 270 degrees on every child pad. That makes adjacent
    0.40 mm-pitch pads overlap. Preserve position and size verbatim and restore
    only the native decal angle.
    """
    normalized: list[str] = []
    corrected = 0
    for child in children:
        if _sexpr_name(child) != "pad":
            normalized.append(child)
            continue
        at_match = re.search(
            r"\(at\s+(-?[0-9.]+)\s+(-?[0-9.]+)\s+(-?[0-9.]+)\)",
            child,
        )
        if not at_match or float(at_match.group(3)) % 360.0 != 270.0:
            raise RuntimeError(
                "KiCad PADS import behavior changed; refusing an unproved J24 correction"
            )
        replacement = f"(at {at_match.group(1)} {at_match.group(2)})"
        normalized.append(child[:at_match.start()] + replacement + child[at_match.end():])
        corrected += 1
    if corrected != 100:
        raise RuntimeError(f"Expected to normalize 100 J24 pads; corrected {corrected}")
    return normalized


def write_radxa_cm5_official_footprints() -> None:
    """Extract the CM5 mating pattern from Radxa's official PCB.

    Radxa models U33-A, U33-B and the four module mounts as one PADS decal.
    They are split into two KiCad BOM footprints at the same origin so the
    three purchased DF40C-100DS connectors remain distinct while their pad
    coordinates cannot drift. J24 retains Radxa's official relative transform.
    Its child pad angle is restored from the native PADS decal after checking
    the known KiCad importer double-rotation artifact.
    """
    if not RADXA_CM5_IO_ASC.exists():
        raise FileNotFoundError(f"Official Radxa PCB source missing: {RADXA_CM5_IO_ASC}")
    _radxa_df40_decal_contract()
    with tempfile.TemporaryDirectory(prefix="radxa-cm5-official-geometry-") as temp:
        imported_board = Path(temp) / "radxa_cm5_io_board_v2200.kicad_pcb"
        result = subprocess.run(
            [
                str(KICAD_CLI),
                "pcb",
                "import",
                "--format",
                "pads",
                "--output",
                str(imported_board),
                str(RADXA_CM5_IO_ASC),
            ],
            check=False,
            stdout=subprocess.PIPE,
            stderr=subprocess.PIPE,
            text=True,
        )
        if result.returncode:
            raise RuntimeError(f"Radxa PADS import failed:\n{result.stderr.strip()}")
        board_text = imported_board.read_text()

    u33_children = _top_level_sexprs(_imported_footprint(board_text, "U33"))
    j24_children = _top_level_sexprs(_imported_footprint(board_text, "J24"))

    u33a: list[str] = []
    u33b: list[str] = []
    for child in u33_children:
        kind = _sexpr_name(child)
        if kind == "pad":
            pin_match = re.match(r'\(pad "(\d+)"', child)
            if not pin_match:
                continue
            pin = int(pin_match.group(1))
            if 1 <= pin <= 100 or 201 <= pin <= 204:
                u33a.append(child)
            elif 101 <= pin <= 200:
                u33b.append(child)
        elif kind == "fp_line":
            coordinates = [
                (float(x), float(y))
                for x, y in re.findall(
                    r"\((?:start|end)\s+(-?[0-9.]+)\s+(-?[0-9.]+)",
                    child,
                )
            ]
            is_left_connector = coordinates and all(
                -20.0 < x < -14.0 and -15.0 < y < 10.0
                for x, y in coordinates
            )
            (u33b if is_left_connector else u33a).append(child)

    j24_geometry = [
        child
        for child in j24_children
        if _sexpr_name(child) in {"fp_line", "fp_arc", "fp_rect", "fp_circle", "fp_poly", "pad"}
    ]
    j24_geometry = _normalize_j24_imported_pad_angles(j24_geometry)
    u33a_pads = [item for item in u33a if _sexpr_name(item) == "pad"]
    u33b_pads = [item for item in u33b if _sexpr_name(item) == "pad"]
    j24_pads = [item for item in j24_geometry if _sexpr_name(item) == "pad"]
    if (len(u33a_pads), len(u33b_pads), len(j24_pads)) != (104, 100, 100):
        raise RuntimeError(
            "Official CM5 footprint extraction expected U33-A=104, U33-B=100, J24=100 pads; "
            f"found {len(u33a_pads)}, {len(u33b_pads)}, {len(j24_pads)}"
        )

    _write_official_footprint(
        "Radxa_CM5_U33A_DF40C_100DS_OFFICIAL",
        "U33-A pads 1-100 plus grounded module mounts 201-204; exact Radxa CM5 IO V2.20 PADS geometry",
        (21.5, 10.5),
        u33a,
    )
    _write_official_footprint(
        "Radxa_CM5_U33B_DF40C_100DS_OFFICIAL",
        "U33-B pads 101-200; exact Radxa CM5 IO V2.20 PADS geometry; place at the same origin as U33-A",
        (-21.5, 10.5),
        u33b,
    )
    _write_official_footprint(
        "Radxa_CM5_J24_DF40C_100DS_OFFICIAL",
        "J24 pads 1-100; Radxa CM5 IO V2.20 PADS coordinates and sizes; native decal pad angle restored after verified KiCad importer correction",
        (1.4, -2.0),
        j24_geometry,
    )


def write_cm5_local_footprints() -> None:
    """Copy controlled connector mechanics into this project's local library."""
    CM5_LOCAL_FOOTPRINTS.mkdir(parents=True, exist_ok=True)
    CM5_LOCAL_3DMODELS.mkdir(parents=True, exist_ok=True)
    filenames = (
        "TE_2199230-3_M2_Key_B_4.2mm.kicad_mod",
        "J_Wurth_WR-CRD_693043020611.kicad_mod",
    )
    for filename in filenames:
        source = LEGACY_CELLULAR_FOOTPRINTS / filename
        if not source.exists():
            raise FileNotFoundError(f"Controlled connector footprint missing: {source}")
        shutil.copyfile(source, CM5_LOCAL_FOOTPRINTS / filename)
    sim_footprint = CM5_LOCAL_FOOTPRINTS / "J_Wurth_WR-CRD_693043020611.kicad_mod"
    sim_footprint.write_text(
        sim_footprint.read_text().replace(
            '${KIPRJMOD}/ProComm_RevF.3dshapes/J_Wurth_WR-CRD_693043020611.step',
            '${KIPRJMOD}/../CM5-CARRIER/CM5Carrier.3dshapes/J_Wurth_WR-CRD_693043020611.step',
        )
    )
    shutil.copyfile(
        BEL_V8BR_1AX1_GH / "Bel_V8BR_1AX1_GH.kicad_mod",
        CM5_LOCAL_FOOTPRINTS / "Bel_V8BR_1AX1_GH.kicad_mod",
    )
    shutil.copyfile(
        BEL_V8BR_1AX1_GH / "Bel_V8BR_1AX1_GH.step",
        CM5_LOCAL_3DMODELS / "Bel_V8BR_1AX1_GH.step",
    )
    shutil.copyfile(
        LEGACY_CELLULAR_MODELS / "J_Wurth_WR-CRD_693043020611.step",
        CM5_LOCAL_3DMODELS / "J_Wurth_WR-CRD_693043020611.step",
    )
    write_molex_0679101002_footprint()
    write_kycon_stx_353k7a_footprint()
    write_panasonic_tq2_footprint()
    write_traco_tri20_footprint()
    write_power_magnetic_and_shunt_footprints()
    write_power_semiconductor_footprints()
    write_radxa_cm5_official_footprints()
    (CM5_LOCAL_LIBRARY.parent / "fp-lib-table").write_text(
        '(fp_lib_table\n'
        '  (version 7)\n'
        '  (lib (name "CM5Carrier")(type "KiCad")(uri "${KIPRJMOD}/CM5Carrier.pretty")(options "")(descr "Radxa CM5 carrier-local footprints"))\n'
        '  (lib (name "ProCommMechanical")(type "KiCad")(uri "${KIPRJMOD}/../ProCommMechanical.pretty")(options "")(descr "Controlled ProComm support and mechanical footprints"))\n'
        ')\n'
    )
    sim_folder = ROOT / "SIM-SERVICE"
    sim_folder.mkdir(parents=True, exist_ok=True)
    (sim_folder / "fp-lib-table").write_text(
        '(fp_lib_table\n'
        '  (version 7)\n'
        '  (lib (name "CM5Carrier")(type "KiCad")(uri "${KIPRJMOD}/../CM5-CARRIER/CM5Carrier.pretty")(options "")(descr "Shared carrier and service-board footprints"))\n'
        '  (lib (name "ProCommMechanical")(type "KiCad")(uri "${KIPRJMOD}/../ProCommMechanical.pretty")(options "")(descr "Controlled ProComm supports"))\n'
        ')\n'
    )
    (ROOT / "AUDIO-8X8" / "fp-lib-table").write_text(
        '(fp_lib_table\n'
        '  (version 7)\n'
        '  (lib (name "CM5Carrier")(type "KiCad")(uri "${KIPRJMOD}/../CM5-CARRIER/CM5Carrier.pretty")(options "")(descr "Shared Radxa CM5 carrier and audio footprints"))\n'
        '  (lib (name "ProCommMechanical")(type "KiCad")(uri "${KIPRJMOD}/../ProCommMechanical.pretty")(options "")(descr "Controlled ProComm support and mechanical footprints"))\n'
        ')\n'
    )


def write_kycon_stx_353k7a_footprint() -> None:
    """Generate a drawing-derived, coupon-gated land pattern for the CTIA jack.

    Kycon's catalog drawing defines the terminal center locations and component
    envelope but does not publish a recommended PCB land.  This footprint is
    intentionally marked preliminary and must be checked against a physical
    STX-353K7A-6N-KTTR sample and a plated-hole coupon before production.
    """

    name = "Kycon_STX-353K7A-6N-KTTR_PRELIMINARY"

    def fp_uuid(label: str) -> str:
        return str(
            _uuid.uuid5(
                _uuid.NAMESPACE_URL,
                f"radxa-cm5-procomm:kycon-stx-353k7a:{label}",
            )
        )

    lines = [
        f'(footprint "{name}"',
        '  (version 20240108)',
        '  (generator "procomm_cm5_generator")',
        '  (layer "F.Cu")',
        '  (descr "Kycon STX-353K7A-6N-KTTR vertical four-pole jack; terminal centers reconstructed from the Kycon component drawing; PRELIMINARY - SAMPLE AND COUPON VERIFICATION REQUIRED")',
        '  (tags "Kycon STX-353K7A CTIA preliminary coupon required")',
        '  (attr through_hole)',
        '  (duplicate_pad_numbers_are_jumpers no)',
        f'  (property "Reference" "J**" (at 0 -14.25 0) (layer "F.SilkS") (uuid "{fp_uuid("reference")}") (effects (font (size 1 1) (thickness 0.15))))',
        f'  (property "Value" "{name}" (at 0 2.75 0) (layer "F.Fab") (uuid "{fp_uuid("value")}") (effects (font (size 1 1) (thickness 0.15))))',
        '  (property "Datasheet" "https://www.kycon.com/Catalog_PDF/STX-353K7A.pdf" (at 0 0 0) (layer "F.Fab") (hide yes) '
        f'(uuid "{fp_uuid("datasheet")}") (effects (font (size 1.27 1.27))))',
        '  (property "Description" "Drawing-derived preliminary footprint; physical sample and coupon are release gates" (at 0 0 0) (layer "F.Fab") (hide yes) '
        f'(uuid "{fp_uuid("description")}") (effects (font (size 1.27 1.27))))',
        f'  (fp_rect (start -3.825 -12.50) (end 3.825 0.00) (stroke (width 0.10) (type default)) (fill none) (layer "F.Fab") (uuid "{fp_uuid("fab-body")}"))',
        f'  (fp_rect (start -4.15 -12.85) (end 4.15 1.05) (stroke (width 0.05) (type default)) (fill none) (layer "F.CrtYd") (uuid "{fp_uuid("courtyard")}"))',
        f'  (fp_line (start -3.825 -12.50) (end 3.825 -12.50) (stroke (width 0.15) (type default)) (layer "F.SilkS") (uuid "{fp_uuid("silk-back")}"))',
        f'  (fp_line (start -3.825 -12.50) (end -3.825 -0.70) (stroke (width 0.15) (type default)) (layer "F.SilkS") (uuid "{fp_uuid("silk-left")}"))',
        f'  (fp_line (start 3.825 -12.50) (end 3.825 -0.70) (stroke (width 0.15) (type default)) (layer "F.SilkS") (uuid "{fp_uuid("silk-right")}"))',
        f'  (fp_text user "PRELIMINARY - COUPON REQUIRED" (at 0 -8.8 0) (layer "F.Fab") (uuid "{fp_uuid("coupon-note")}") (effects (font (size 0.8 0.8) (thickness 0.12))))',
    ]
    # Pin 1 is the drawing datum.  Pins 5/6/1/4 form the rear terminal row;
    # pins 2/3 form the forward row at the drawing's 5.10 mm row spacing.
    pads = (
        (1, 0.000, 0.000),
        (2, -1.725, -5.100),
        (3, 1.725, -5.100),
        (4, 3.070, 0.000),
        (5, -1.300, 0.000),
        (6, -3.350, 0.000),
    )
    for pin, x, y in pads:
        shape = "roundrect" if pin == 1 else "circle"
        lines.extend(
            [
                f'  (pad "{pin}" thru_hole {shape}',
                f'    (at {x:.3f} {y:.3f}) (size 1.80 1.80) (drill 1.00)',
                '    (layers "*.Cu" "*.Mask")',
            ]
        )
        if pin == 1:
            lines.append('    (roundrect_rratio 0.25)')
        lines.extend([f'    (uuid "{fp_uuid(f"pad-{pin}")}")', '  )'])
    lines.extend(['  (embedded_fonts no)', ')'])
    (CM5_LOCAL_FOOTPRINTS / f"{name}.kicad_mod").write_text(
        "\n".join(lines) + "\n"
    )


def write_panasonic_tq2_footprint() -> None:
    """Generate the preliminary TQ2 through-hole pattern for capture review.

    The 2.54 mm contact pitch and 7.62 mm row spacing are held as provisional
    dimensions until Panasonic's current engineering drawing and a relay
    insertion coupon are signed off.  Routing is intentionally gated on that
    verification in the footprint audit.
    """
    name = "Panasonic_TQ2-12V_PRELIMINARY"

    def fp_uuid(label: str) -> str:
        return str(
            _uuid.uuid5(
                _uuid.NAMESPACE_URL,
                f"radxa-cm5-procomm:panasonic-tq2:{label}",
            )
        )

    lines = [
        f'(footprint "{name}"',
        '  (version 20240108)',
        '  (generator "procomm_cm5_generator")',
        '  (layer "F.Cu")',
        '  (descr "Panasonic TQ2 standard PC-board relay; PRELIMINARY - current engineering drawing and insertion coupon required")',
        '  (tags "Panasonic TQ2 preliminary coupon required")',
        '  (attr through_hole)',
        '  (duplicate_pad_numbers_are_jumpers no)',
        f'  (property "Reference" "K**" (at 0 -5.8 0) (layer "F.SilkS") (uuid "{fp_uuid("reference")}") (effects (font (size 1 1) (thickness 0.15))))',
        f'  (property "Value" "{name}" (at 0 5.8 0) (layer "F.Fab") (uuid "{fp_uuid("value")}") (effects (font (size 1 1) (thickness 0.15))))',
        '  (property "Datasheet" "https://na.industrial.panasonic.com/products/relays-contactors/mechanical-signal-relays/series/119572/model/119888" (at 0 0 0) (layer "F.Fab") (hide yes) '
        f'(uuid "{fp_uuid("datasheet")}") (effects (font (size 1.27 1.27))))',
        f'  (fp_rect (start -7.1 -4.5) (end 7.1 4.5) (stroke (width 0.10) (type default)) (fill none) (layer "F.Fab") (uuid "{fp_uuid("fab-body")}"))',
        f'  (fp_rect (start -7.35 -4.75) (end 7.35 4.75) (stroke (width 0.05) (type default)) (fill none) (layer "F.CrtYd") (uuid "{fp_uuid("courtyard")}"))',
        f'  (fp_line (start -7.1 -4.5) (end 7.1 -4.5) (stroke (width 0.15) (type default)) (layer "F.SilkS") (uuid "{fp_uuid("silk-top")}"))',
        f'  (fp_text user "PRELIMINARY - DRAWING/COUPON" (at 0 0 0) (layer "F.Fab") (uuid "{fp_uuid("gate-note")}") (effects (font (size 0.7 0.7) (thickness 0.1))))',
    ]
    pads = (
        (1, -3.81, -3.81), (2, -1.27, -3.81),
        (3, 1.27, -3.81), (4, 3.81, -3.81),
        (10, -3.81, 3.81), (9, -1.27, 3.81),
        (8, 1.27, 3.81), (7, 3.81, 3.81),
    )
    for pin, x, y in pads:
        shape = "roundrect" if pin == 1 else "circle"
        lines.extend(
            [
                f'  (pad "{pin}" thru_hole {shape}',
                f'    (at {x:.2f} {y:.2f}) (size 1.7 1.7) (drill 0.9)',
                '    (layers "*.Cu" "*.Mask")',
            ]
        )
        if pin == 1:
            lines.append('    (roundrect_rratio 0.25)')
        lines.extend([f'    (uuid "{fp_uuid(f"pad-{pin}")}")', '  )'])
    lines.extend(['  (embedded_fonts no)', ')'])
    (CM5_LOCAL_FOOTPRINTS / f"{name}.kicad_mod").write_text(
        "\n".join(lines) + "\n"
    )


def write_traco_tri20_footprint() -> None:
    """Generate the TRI 20 dual-output footprint from Traco's Rev 2024 drawing."""
    name = "TRACO_TRI20_DUAL"

    def fp_uuid(label: str) -> str:
        return str(
            _uuid.uuid5(
                _uuid.NAMESPACE_URL,
                f"radxa-cm5-procomm:traco-tri20:{label}",
            )
        )

    lines = [
        f'(footprint "{name}"',
        '  (version 20240108)',
        '  (generator "procomm_cm5_generator")',
        '  (layer "F.Cu")',
        '  (descr "Traco Power TRI 20 dual-output DC/DC; exact 50.8 x 25.4 mm outline and five-pin pattern from Rev August 7 2024 drawing")',
        '  (tags "Traco TRI20 2x1 inch DIP dual output")',
        '  (attr through_hole)',
        '  (duplicate_pad_numbers_are_jumpers no)',
        f'  (property "Reference" "U**" (at 0 -14.7 0) (layer "F.SilkS") (uuid "{fp_uuid("reference")}") (effects (font (size 1 1) (thickness 0.15))))',
        f'  (property "Value" "{name}" (at 0 14.7 0) (layer "F.Fab") (uuid "{fp_uuid("value")}") (effects (font (size 1 1) (thickness 0.15))))',
        '  (property "Datasheet" "https://www.tracopower.com/tri20-datasheet" (at 0 0 0) (layer "F.Fab") (hide yes) '
        f'(uuid "{fp_uuid("datasheet")}") (effects (font (size 1.27 1.27))))',
        f'  (fp_rect (start -25.4 -12.7) (end 25.4 12.7) (stroke (width 0.10) (type default)) (fill none) (layer "F.Fab") (uuid "{fp_uuid("fab-body")}"))',
        f'  (fp_rect (start -25.7 -13.0) (end 25.7 13.0) (stroke (width 0.05) (type default)) (fill none) (layer "F.CrtYd") (uuid "{fp_uuid("courtyard")}"))',
        f'  (fp_line (start -25.4 -12.7) (end 25.4 -12.7) (stroke (width 0.15) (type default)) (layer "F.SilkS") (uuid "{fp_uuid("silk-top")}"))',
        f'  (fp_line (start -25.4 12.7) (end 25.4 12.7) (stroke (width 0.15) (type default)) (layer "F.SilkS") (uuid "{fp_uuid("silk-bottom")}"))',
        f'  (fp_line (start -25.4 -12.7) (end -25.4 12.7) (stroke (width 0.15) (type default)) (layer "F.SilkS") (uuid "{fp_uuid("silk-left")}"))',
        f'  (fp_line (start 25.4 -12.7) (end 25.4 12.7) (stroke (width 0.15) (type default)) (layer "F.SilkS") (uuid "{fp_uuid("silk-right")}"))',
        f'  (fp_circle (center -23.7 -6.8) (end -23.1 -6.8) (stroke (width 0.15) (type default)) (fill none) (layer "F.SilkS") (uuid "{fp_uuid("pin-one")}"))',
        f'  (fp_text user "BOTTOM-VIEW PIN DATUM" (at 0 0 0) (layer "F.Fab") (uuid "{fp_uuid("datum-note")}") (effects (font (size 0.8 0.8) (thickness 0.12))))',
    ]
    # Manufacturer bottom view: 45.72 mm column pitch. Input pins are 5.08 mm
    # apart; dual-output pins are on 5.08 mm pitch around the center common.
    pads = (
        (1, -22.86, -2.54),
        (2, -22.86, 2.54),
        (3, 22.86, -5.08),
        (4, 22.86, 0.00),
        (5, 22.86, 5.08),
    )
    for pin, x, y in pads:
        shape = "roundrect" if pin == 1 else "circle"
        lines.extend(
            [
                f'  (pad "{pin}" thru_hole {shape}',
                f'    (at {x:.2f} {y:.2f}) (size 2.20 2.20) (drill 1.20)',
                '    (layers "*.Cu" "*.Mask")',
            ]
        )
        if pin == 1:
            lines.append('    (roundrect_rratio 0.25)')
        lines.extend([f'    (uuid "{fp_uuid(f"pad-{pin}")}")', '  )'])
    lines.extend(['  (embedded_fonts no)', ')'])
    (CM5_LOCAL_FOOTPRINTS / f"{name}.kicad_mod").write_text(
        "\n".join(lines) + "\n"
    )


def write_power_magnetic_and_shunt_footprints() -> None:
    """Generate simple two-pad lands from controlled manufacturer drawings."""

    def write_footprint(
        name: str,
        reference_prefix: str,
        body: tuple[float, float],
        pad_size: tuple[float, float],
        pad_centers: tuple[tuple[float, float], tuple[float, float]],
        datasheet: str,
        description: str,
    ) -> None:
        def fp_uuid(label: str) -> str:
            return str(
                _uuid.uuid5(
                    _uuid.NAMESPACE_URL,
                    f"radxa-cm5-procomm:power-footprints:{name}:{label}",
                )
            )

        body_x, body_y = body
        pad_x, pad_y = pad_size
        extent_x = max(body_x / 2, *(abs(x) + pad_x / 2 for x, _ in pad_centers))
        extent_y = max(body_y / 2, *(abs(y) + pad_y / 2 for _, y in pad_centers))
        courtyard_x = extent_x + 0.25
        courtyard_y = extent_y + 0.25
        lines = [
            f'(footprint "{name}"',
            '  (version 20240108)',
            '  (generator "procomm_cm5_generator")',
            '  (layer "F.Cu")',
            f'  (descr "{description}")',
            '  (attr smd)',
            '  (duplicate_pad_numbers_are_jumpers no)',
            f'  (property "Reference" "{reference_prefix}**" (at 0 {-courtyard_y - 1.0:.2f} 0) (layer "F.SilkS") (uuid "{fp_uuid("reference")}") (effects (font (size 1 1) (thickness 0.15))))',
            f'  (property "Value" "{name}" (at 0 {courtyard_y + 1.0:.2f} 0) (layer "F.Fab") (uuid "{fp_uuid("value")}") (effects (font (size 1 1) (thickness 0.15))))',
            f'  (property "Datasheet" "{datasheet}" (at 0 0 0) (layer "F.Fab") (hide yes) (uuid "{fp_uuid("datasheet")}") (effects (font (size 1.27 1.27))))',
            f'  (fp_rect (start {-body_x / 2:.2f} {-body_y / 2:.2f}) (end {body_x / 2:.2f} {body_y / 2:.2f}) (stroke (width 0.10) (type default)) (fill none) (layer "F.Fab") (uuid "{fp_uuid("fab")}"))',
            f'  (fp_rect (start {-courtyard_x:.2f} {-courtyard_y:.2f}) (end {courtyard_x:.2f} {courtyard_y:.2f}) (stroke (width 0.05) (type default)) (fill none) (layer "F.CrtYd") (uuid "{fp_uuid("courtyard")}"))',
            f'  (fp_line (start {-body_x / 2:.2f} {-body_y / 2:.2f}) (end {body_x / 2:.2f} {-body_y / 2:.2f}) (stroke (width 0.15) (type default)) (layer "F.SilkS") (uuid "{fp_uuid("silk-top")}"))',
            f'  (fp_line (start {-body_x / 2:.2f} {body_y / 2:.2f}) (end {body_x / 2:.2f} {body_y / 2:.2f}) (stroke (width 0.15) (type default)) (layer "F.SilkS") (uuid "{fp_uuid("silk-bottom")}"))',
        ]
        for index, (x, y) in enumerate(pad_centers, start=1):
            lines.extend(
                [
                    f'  (pad "{index}" smd roundrect',
                    f'    (at {x:.3f} {y:.3f}) (size {pad_x:.3f} {pad_y:.3f})',
                    '    (layers "F.Cu" "F.Paste" "F.Mask")',
                    '    (roundrect_rratio 0.10)',
                    f'    (uuid "{fp_uuid(f"pad-{index}")}")',
                    '  )',
                ]
            )
        lines.extend(['  (embedded_fonts no)', ')'])
        (CM5_LOCAL_FOOTPRINTS / f"{name}.kicad_mod").write_text("\n".join(lines) + "\n")

    write_footprint(
        "TDK_SPM10065VC",
        "L",
        (10.5, 10.0),
        (2.95, 4.50),
        ((-4.525, 0.0), (4.525, 0.0)),
        "https://product.tdk.com/en/search/inductor/inductor/smd/info?part_no=SPM10065VC-3R3M-D",
        "TDK SPM10065VC; 10.5 x 10.0 mm body; A=2.95, B=6.10, C=4.50 mm recommended land",
    )
    write_footprint(
        "Wurth_74439370047",
        "L",
        (16.4, 15.4),
        (14.1, 3.3),
        ((0.0, -5.3), (0.0, 5.3)),
        "https://www.we-online.com/components/products/datasheet/74439370047.pdf",
        "Wurth 74439370047 WE-XHMI; manufacturer recommended 14.1 x 3.3 mm lands with 7.3 mm gap",
    )
    write_footprint(
        "Susumu_KRL6432E_6mR",
        "R",
        (3.1, 6.3),
        (1.0, 6.6),
        ((-1.6, 0.0), (1.6, 0.0)),
        "https://www.susumu.co.jp/en/tech/rep-data-rand/",
        "Susumu KRL6432E long-side terminal, 2 mOhm and above land: a=2.20, b=4.20, c=6.60 mm",
    )
    write_footprint(
        "Susumu_KRL11050_4mR",
        "R",
        (5.0, 11.0),
        (1.0, 11.2),
        ((-2.3, 0.0), (2.3, 0.0)),
        "https://www.susumu.co.jp/en/tech/rep-data-rand/",
        "Susumu KRL11050 long-side terminal, 2 mOhm and above land: a=3.60, b=5.60, c=11.20 mm",
    )


def write_power_semiconductor_footprints() -> None:
    """Generate drawing-derived power IC and MOSFET land patterns.

    The MOSFET symbols expose G/S/D as pins 1/2/3.  Their physical packages
    use repeated source and drain terminals, so these project footprints map
    every physical terminal onto the corresponding three schematic nets.
    """

    def fp_uuid(name: str, label: str) -> str:
        return str(
            _uuid.uuid5(
                _uuid.NAMESPACE_URL,
                f"radxa-cm5-procomm:power-semiconductor:{name}:{label}",
            )
        )

    def base_lines(
        name: str,
        body: tuple[float, float],
        courtyard: tuple[float, float],
        datasheet: str,
        description: str,
        reference_prefix: str,
    ) -> list[str]:
        body_x, body_y = body
        courtyard_x, courtyard_y = courtyard
        return [
            f'(footprint "{name}"',
            '  (version 20240108)',
            '  (generator "procomm_cm5_generator")',
            '  (layer "F.Cu")',
            f'  (descr "{description}")',
            '  (attr smd)',
            '  (duplicate_pad_numbers_are_jumpers no)',
            f'  (property "Reference" "{reference_prefix}**" (at 0 {-courtyard_y - 1.0:.2f} 0) (layer "F.SilkS") (uuid "{fp_uuid(name, "reference")}") (effects (font (size 1 1) (thickness 0.15))))',
            f'  (property "Value" "{name}" (at 0 {courtyard_y + 1.0:.2f} 0) (layer "F.Fab") (uuid "{fp_uuid(name, "value")}") (effects (font (size 1 1) (thickness 0.15))))',
            f'  (property "Datasheet" "{datasheet}" (at 0 0 0) (layer "F.Fab") (hide yes) (uuid "{fp_uuid(name, "datasheet")}") (effects (font (size 1.27 1.27))))',
            f'  (fp_rect (start {-body_x / 2:.3f} {-body_y / 2:.3f}) (end {body_x / 2:.3f} {body_y / 2:.3f}) (stroke (width 0.10) (type default)) (fill none) (layer "F.Fab") (uuid "{fp_uuid(name, "fab")}"))',
            f'  (fp_rect (start {-courtyard_x:.3f} {-courtyard_y:.3f}) (end {courtyard_x:.3f} {courtyard_y:.3f}) (stroke (width 0.05) (type default)) (fill none) (layer "F.CrtYd") (uuid "{fp_uuid(name, "courtyard")}"))',
            f'  (fp_line (start {-body_x / 2:.3f} {-body_y / 2:.3f}) (end {body_x / 2:.3f} {-body_y / 2:.3f}) (stroke (width 0.15) (type default)) (layer "F.SilkS") (uuid "{fp_uuid(name, "silk-top")}"))',
            f'  (fp_line (start {-body_x / 2:.3f} {body_y / 2:.3f}) (end {body_x / 2:.3f} {body_y / 2:.3f}) (stroke (width 0.15) (type default)) (layer "F.SilkS") (uuid "{fp_uuid(name, "silk-bottom")}"))',
            f'  (fp_circle (center {-body_x / 2 - 0.35:.3f} {-body_y / 2 - 0.35:.3f}) (end {-body_x / 2 - 0.20:.3f} {-body_y / 2 - 0.35:.3f}) (stroke (width 0.15) (type default)) (fill none) (layer "F.SilkS") (uuid "{fp_uuid(name, "pin-one")}"))',
        ]

    def add_rect_pad(
        lines: list[str],
        name: str,
        number: str,
        x: float,
        y: float,
        width: float,
        height: float,
        label: str,
        layers: str = '"F.Cu" "F.Paste" "F.Mask"',
        shape: str = "roundrect",
    ) -> None:
        lines.extend(
            [
                f'  (pad "{number}" smd {shape}',
                f'    (at {x:.3f} {y:.3f}) (size {width:.3f} {height:.3f})',
                f'    (layers {layers})',
            ]
        )
        if shape == "roundrect":
            lines.append('    (roundrect_rratio 0.10)')
        lines.extend([f'    (uuid "{fp_uuid(name, label)}")', '  )'])

    def add_segmented_paste(
        lines: list[str],
        name: str,
        x_centers: tuple[float, ...],
        y_centers: tuple[float, ...],
        size: tuple[float, float],
        label_prefix: str,
    ) -> None:
        for row, y in enumerate(y_centers):
            for column, x in enumerate(x_centers):
                add_rect_pad(
                    lines,
                    name,
                    "",
                    x,
                    y,
                    size[0],
                    size[1],
                    f"{label_prefix}-{row}-{column}",
                    layers='"F.Paste"',
                    shape="rect",
                )

    def finish(name: str, lines: list[str]) -> None:
        lines.extend(['  (embedded_fonts no)', ')'])
        (CM5_LOCAL_FOOTPRINTS / f"{name}.kicad_mod").write_text("\n".join(lines) + "\n")

    # TI RJR0014A VQFN-HR.  Coordinates are reconstructed directly from the
    # 4223976/H example board layout dimensions (June 2026).  Duplicate
    # rectangles form the four L-shaped corner lands without losing pad nets.
    name = "TI_RJR0014A"
    lines = base_lines(
        name,
        (4.0, 3.5),
        (2.45, 2.05),
        "https://www.ti.com/lit/ml/mpqf507g/mpqf507g.pdf",
        "TI RJR0014A 14-pin VQFN-HR; drawing 4223976/H manufacturer example land pattern",
        "U",
    )
    rjr_rects = (
        ("1", -1.675, -1.450, 0.35, 1.00, "pin-1-vertical"),
        ("1", -1.850, -1.150, 0.70, 0.40, "pin-1-horizontal"),
        ("2", -1.850, -0.525, 0.70, 0.25, "pin-2"),
        ("3", -1.850, 0.000, 0.70, 0.25, "pin-3"),
        ("4", -1.850, 0.525, 0.70, 0.25, "pin-4"),
        ("5", -1.675, 1.450, 0.35, 1.00, "pin-5-vertical"),
        ("5", -1.850, 1.150, 0.70, 0.40, "pin-5-horizontal"),
        ("6", -1.125, 1.600, 0.25, 0.70, "pin-6"),
        ("7", -0.625, 1.600, 0.25, 0.70, "pin-7"),
        ("8", 0.450, 1.450, 0.40, 1.00, "pin-8"),
        ("9", 1.600, 1.450, 0.40, 1.00, "pin-9-vertical"),
        ("9", 1.800, 1.150, 0.80, 0.40, "pin-9-horizontal"),
        ("10", 1.000, 0.000, 2.40, 0.40, "pin-10"),
        ("11", 1.600, -1.450, 0.40, 1.00, "pin-11-vertical"),
        ("11", 1.800, -1.150, 0.80, 0.40, "pin-11-horizontal"),
        ("12", 0.450, -1.450, 0.40, 1.00, "pin-12"),
        ("13", -0.625, -1.600, 0.25, 0.70, "pin-13"),
        ("14", -1.125, -1.600, 0.25, 0.70, "pin-14"),
    )
    for number, x, y, width, height, label in rjr_rects:
        add_rect_pad(lines, name, number, x, y, width, height, label)
    finish(name, lines)

    # TPS22990 DML0010A WSON.  The exposed thermal land is electrically VIN,
    # so it deliberately repeats schematic pad 3.
    name = "TI_DML0010A"
    lines = base_lines(
        name,
        (2.0, 3.0),
        (1.60, 1.80),
        "https://www.ti.com/lit/ds/symlink/tps22990.pdf",
        "TI DML0010A 10-pin WSON; drawing 4222524/A manufacturer land pattern; exposed pad mapped to VIN pin 3",
        "U",
    )
    for pin, y in enumerate((-1.0, -0.5, 0.0, 0.5, 1.0), start=1):
        add_rect_pad(lines, name, str(pin), -1.30, y, 0.45, 0.24, f"pin-{pin}")
    for pin, y in zip((6, 7, 8, 9, 10), (1.0, 0.5, 0.0, -0.5, -1.0)):
        height = 0.28 if pin >= 8 else 0.24
        add_rect_pad(lines, name, str(pin), 1.30, y, 0.45, height, f"pin-{pin}")
    add_rect_pad(lines, name, "3", 0.02, 0.0, 1.10, 1.95, "vin-exposed", layers='"F.Cu" "F.Mask"', shape="rect")
    add_segmented_paste(lines, name, (-0.255, 0.295), (-0.4875, 0.4875), (0.45, 0.75), "vin-paste")
    finish(name, lines)

    # TI DNK0008A VSON-CLIP used by both CSD power MOSFETs.  The copper and
    # paste geometry follows KiCad's TI CSD18531Q5A drawing-backed footprint;
    # only the pad numbers are remapped to the G/S/D schematic convention.
    name = "TI_DNK0008A_GSD"
    lines = base_lines(
        name,
        (5.0, 6.0),
        (3.40, 3.40),
        "https://www.ti.com/lit/ds/symlink/csd18532q5b.pdf",
        "TI DNK0008A VSON-CLIP 5 x 6 mm; physical source/gate/drain terminals remapped to schematic G/S/D pins 1/2/3",
        "Q",
    )
    for y in (-1.905, -0.635, 0.635):
        add_rect_pad(lines, name, "2", -2.80, y, 0.70, 0.70, f"source-{y}")
    add_rect_pad(lines, name, "1", -2.80, 1.905, 0.70, 0.70, "gate")
    for y in (-1.905, -0.635, 0.635, 1.905):
        add_rect_pad(lines, name, "3", 2.80, y, 0.70, 0.70, f"drain-{y}", shape="rect")
    add_rect_pad(lines, name, "3", 0.33, 0.0, 4.35, 4.51, "drain-exposed", layers='"F.Cu" "F.Mask"', shape="rect")
    add_segmented_paste(lines, name, (-0.4525, 1.1125), (-1.095, 1.095), (1.585, 1.57), "drain-paste")
    finish(name, lines)

    # onsemi DFN5 5x6 (SO-8FL), case 488AA.  Physical pins 1-3 are source,
    # pin 4 is gate, and pin 5 plus the large exposed area are drain.
    name = "onsemi_DFN5_5x6_488AA_GSD"
    lines = base_lines(
        name,
        (5.15, 6.15),
        (2.65, 3.65),
        "https://www.onsemi.com/download/data-sheet/pdf/nvmfs6b25nl-d.pdf",
        "onsemi case 488AA DFN5 5 x 6 mm; recommended SO-8FL land remapped to schematic G/S/D pins 1/2/3",
        "Q",
    )
    for physical_pin, x in enumerate((-1.905, -0.635, 0.635, 1.905), start=1):
        number = "2" if physical_pin <= 3 else "1"
        add_rect_pad(lines, name, number, x, 2.765, 0.75, 1.00, f"terminal-{physical_pin}")
    add_rect_pad(lines, name, "3", 0.0, -0.665, 4.56, 3.20, "drain-main", layers='"F.Cu" "F.Mask"', shape="rect")
    for x in (-2.0425, 2.0425):
        add_rect_pad(lines, name, "3", x, 1.600, 0.475, 1.33, f"drain-side-{x}")
    add_segmented_paste(lines, name, (-1.45, 0.0, 1.45), (-1.20, -0.10), (1.20, 0.85), "drain-paste")
    finish(name, lines)

    # onsemi DFNW8 5.2x6.3, case 507AU.  Physical pins 1-3 are source, pin 4
    # is gate, pins 5-8 and the central thermal land are drain.
    name = "onsemi_DFNW8_5p2x6p3_507AU_GSD"
    lines = base_lines(
        name,
        (5.20, 6.30),
        (2.85, 3.75),
        "https://www.onsemi.com/download/data-sheet/pdf/fdws86068-f085-d.pdf",
        "onsemi case 507AU DFNW8 5.2 x 6.3 mm; manufacturer land remapped to schematic G/S/D pins 1/2/3",
        "Q",
    )
    for physical_pin, x in enumerate((-1.905, -0.635, 0.635, 1.905), start=1):
        number = "2" if physical_pin <= 3 else "1"
        add_rect_pad(lines, name, number, x, 2.745, 0.61, 1.42, f"terminal-{physical_pin}")
    add_rect_pad(lines, name, "3", 0.0, 0.0, 4.42, 3.75, "drain-main", layers='"F.Cu" "F.Mask"', shape="rect")
    for physical_pin, x in zip((8, 7, 6, 5), (-1.905, -0.635, 0.635, 1.905)):
        add_rect_pad(lines, name, "3", x, -2.745, 0.66, 1.42, f"drain-terminal-{physical_pin}")
    add_segmented_paste(lines, name, (-1.40, 0.0, 1.40), (-1.15, 0.0, 1.15), (1.05, 0.85), "drain-paste")
    finish(name, lines)


def write_molex_0679101002_footprint() -> None:
    """Generate the Molex Mini PCIe land pattern from SD-67910-001 C2."""

    def fp_uuid(label: str) -> str:
        return str(
            _uuid.uuid5(
                _uuid.NAMESPACE_URL,
                f"radxa-cm5-procomm:molex-0679101002:{label}",
            )
        )

    lines = [
        '(footprint "Molex_0679101002_Mini_PCIe"',
        '  (version 20240108)',
        '  (generator "pcbnew")',
        '  (layer "F.Cu")',
        '  (descr "Molex 0679101002 Mini PCI Express socket, 52 contacts, 0.8 mm pitch, 4.0 mm height; manufacturer recommended PCB layout from production drawing SD-67910-001 revision C2")',
        '  (tags "Molex 0679101002 67910-1002 Mini PCIe socket")',
        '  (property "Reference" "J**"',
        '    (at 12.5 -7.0 0)',
        '    (layer "F.SilkS")',
        f'    (uuid "{fp_uuid("reference")}")',
        '    (effects (font (size 1 1) (thickness 0.15)))',
        '  )',
        '  (property "Value" "Molex_0679101002_Mini_PCIe"',
        '    (at 12.5 7.0 0)',
        '    (layer "F.Fab")',
        f'    (uuid "{fp_uuid("value")}")',
        '    (effects (font (size 1 1) (thickness 0.15)))',
        '  )',
        '  (property "Datasheet" "https://www.molex.com/content/dam/molex/molex-dot-com/products/automated/en-us/salesdrawingpdf/679/67910/679100002_sd.pdf"',
        '    (at 0 0 0) (layer "F.Fab") (hide yes)',
        f'    (uuid "{fp_uuid("datasheet")}")',
        '    (effects (font (size 1.27 1.27)))',
        '  )',
        '  (property "Description" "Molex 0679101002 right-angle 52-position Mini PCIe card socket"',
        '    (at 0 0 0) (layer "F.Fab") (hide yes)',
        f'    (uuid "{fp_uuid("description")}")',
        '    (effects (font (size 1.27 1.27)))',
        '  )',
        '  (attr smd)',
        '  (duplicate_pad_numbers_are_jumpers no)',
    ]

    def add_line(
        start: tuple[float, float],
        end: tuple[float, float],
        layer: str,
        width: float,
        label: str,
    ) -> None:
        lines.extend(
            [
                '  (fp_line',
                f'    (start {start[0]:.2f} {start[1]:.2f})',
                f'    (end {end[0]:.2f} {end[1]:.2f})',
                f'    (stroke (width {width:.2f}) (type default))',
                f'    (layer "{layer}")',
                f'    (uuid "{fp_uuid(label)}")',
                '  )',
            ]
        )

    # The left locator hole is datum E. The connector drawing specifies a
    # 25.00 mm locator-hole pitch and a 30.00 mm maximum body width.
    for layer, width, suffix in (("F.Fab", 0.10, "fab"), ("F.CrtYd", 0.05, "courtyard")):
        x0, y0, x1, y1 = (
            (-2.50, -5.10, 27.50, 5.10)
            if layer == "F.Fab"
            else (-3.10, -5.60, 28.10, 5.60)
        )
        add_line((x0, y0), (x1, y0), layer, width, f"{suffix}-top")
        add_line((x1, y0), (x1, y1), layer, width, f"{suffix}-right")
        add_line((x1, y1), (x0, y1), layer, width, f"{suffix}-bottom")
        add_line((x0, y1), (x0, y0), layer, width, f"{suffix}-left")

    add_line((-2.50, -5.35), (27.50, -5.35), "F.SilkS", 0.15, "silk-top")
    add_line((-2.50, -5.35), (-2.50, -4.95), "F.SilkS", 0.15, "silk-left")
    add_line((27.50, -5.35), (27.50, -4.95), "F.SilkS", 0.15, "silk-right")
    add_line((-0.80, 5.35), (0.80, 5.35), "F.SilkS", 0.25, "pin-one-marker")

    lines.extend(
        [
            '  (fp_text user "DATUM E"',
            '    (at 0 0 0) (layer "F.Fab")',
            f'    (uuid "{fp_uuid("datum-e-text")}")',
            '    (effects (font (size 0.6 0.6) (thickness 0.10)))',
            '  )',
            '  (fp_text user "SD-67910-001 C2"',
            '    (at 12.5 0 0) (layer "F.Fab")',
            f'    (uuid "{fp_uuid("drawing-text")}")',
            '    (effects (font (size 0.7 0.7) (thickness 0.10)))',
            '  )',
            '  (pad "" np_thru_hole circle',
            '    (at 0 0) (size 1.60 1.60) (drill 1.60)',
            '    (layers "*.Cu" "*.Mask")',
            f'    (uuid "{fp_uuid("locator-e")}")',
            '  )',
            '  (pad "" np_thru_hole circle',
            '    (at 25.00 0) (size 1.10 1.10) (drill 1.10)',
            '    (layers "*.Cu" "*.Mask")',
            f'    (uuid "{fp_uuid("locator-d")}")',
            '  )',
            '  (pad "" smd rect',
            '    (at -2.15 3.50) (size 1.60 3.20)',
            '    (layers "F.Cu" "F.Paste" "F.Mask")',
            f'    (uuid "{fp_uuid("hold-down-left")}")',
            '  )',
            '  (pad "" smd rect',
            '    (at 27.15 3.50) (size 1.60 3.20)',
            '    (layers "F.Cu" "F.Paste" "F.Mask")',
            f'    (uuid "{fp_uuid("hold-down-right")}")',
            '  )',
        ]
    )

    # The contact rows are staggered 0.40 mm. Pins 1-16 occupy the 5.60 mm
    # group; pins 17-52 occupy the 13.60 mm group across the card key.
    contact_positions: list[tuple[int, float, float]] = []
    contact_positions.extend((1 + 2 * index, 0.80 * index, 4.10) for index in range(8))
    contact_positions.extend((2 + 2 * index, 0.40 + 0.80 * index, -4.10) for index in range(8))
    contact_positions.extend((17 + 2 * index, 10.30 + 0.80 * index, 4.10) for index in range(18))
    contact_positions.extend((18 + 2 * index, 10.70 + 0.80 * index, -4.10) for index in range(18))
    for pin, x, y in sorted(contact_positions):
        shape = "roundrect" if pin == 1 else "rect"
        lines.extend(
            [
                f'  (pad "{pin}" smd {shape}',
                f'    (at {x:.2f} {y:.2f}) (size 0.60 2.00)',
                '    (layers "F.Cu" "F.Paste" "F.Mask")',
            ]
        )
        if pin == 1:
            lines.append('    (roundrect_rratio 0.25)')
        lines.extend([f'    (uuid "{fp_uuid(f"pad-{pin}")}")', '  )'])

    lines.append(')')
    output = CM5_LOCAL_FOOTPRINTS / "Molex_0679101002_Mini_PCIe.kicad_mod"
    output.write_text("\n".join(lines) + "\n")


def create_project(folder: Path, name: str) -> None:
    folder.mkdir(parents=True, exist_ok=True)
    project_path = folder / f"{name}.kicad_pro"
    existing = json.loads(project_path.read_text()) if project_path.exists() else {}
    shutil.copyfile(KICAD_TEMPLATE, project_path)
    data = json.loads(project_path.read_text())
    data["meta"]["filename"] = project_path.name
    if existing.get("schematic", {}).get("top_level_sheets"):
        data["schematic"]["top_level_sheets"] = existing["schematic"]["top_level_sheets"]
    project_path.write_text(json.dumps(data, indent=2) + "\n")


def pin_xy(component, pin: int | str) -> tuple[float, float]:
    point = component.get_pin_position(str(pin))
    if point is None:
        raise RuntimeError(f"{component.reference} has no pin {pin}")
    return (point.x, 2.0 * component.position.y - point.y)


def add_symbol(
    schematic,
    lib_id: str,
    reference: str,
    value: str,
    position: tuple[float, float],
    footprint: str = "",
    manufacturer: str = "",
    mpn: str = "",
    rotation: int = 0,
):
    if not footprint and mpn:
        footprint = MPN_FOOTPRINTS.get(mpn, "")
    component = schematic.components.add(
        lib_id,
        reference,
        value,
        position=position,
        footprint=footprint or None,
        rotation=rotation,
    )
    if manufacturer:
        component.add_property("Manufacturer", manufacturer, hidden=True)
    if mpn:
        component.add_property("MPN", mpn, hidden=True)
    return component


def label_pin(schematic, component, pin: int, net_name: str, two_row: bool = False) -> None:
    justify = "right" if (not two_row or pin % 2 == 1) else "left"
    add_global_net_label(schematic, net_name, pin_xy(component, pin), 0.95, justify)


def add_global_net_label(
    schematic,
    net_name: str,
    position: tuple[float, float],
    size: float,
    justify: str,
) -> None:
    """Add a project-wide net label so nested board sheets form one netlist."""
    schematic.labels.add(net_name, position, size=size, justify_h=justify)


def save_generated_schematic(schematic, output: Path) -> None:
    """Save and promote all generated net labels to project-wide global labels.

    kicad-sch-api 0.4 accepts global labels but its KiCad 9 writer currently
    omits them. The local-label serializer is stable, so promote those emitted
    records structurally after save. All labels in these generated circuit
    sheets are electrical net labels; free annotations use text objects.
    """
    schematic.save(output)
    text = output.read_text(encoding="utf-8")
    text, count = re.subn(
        r'(?m)^(\t)\(label ("[^"\n]+")$',
        r'\1(global_label \2\n\1\t(shape bidirectional)',
        text,
    )
    if not count:
        raise RuntimeError(f"{output.name} emitted no electrical labels to globalize")
    output.write_text(text, encoding="utf-8")


def label_pin_auto(schematic, component, pin: int | str, net_name: str, size: float = 0.72) -> None:
    position = pin_xy(component, pin)
    justify = "right" if position[0] < component.position.x else "left"
    add_global_net_label(schematic, net_name, position, size, justify)


def label_two_pin_device(schematic, component, net_1: str, net_2: str) -> None:
    label_pin_auto(schematic, component, 1, net_1, 0.7)
    label_pin_auto(schematic, component, 2, net_2, 0.7)


def label_pin_with_stub(
    schematic,
    component,
    pin: int | str,
    net_name: str,
    offsets: tuple[tuple[float, float], ...],
    justify: str,
) -> None:
    """Route a short orthogonal stub so a net label clears the symbol fields."""
    start = pin_xy(component, pin)
    points = [start]
    for offset_x, offset_y in offsets:
        points.append((start[0] + offset_x, start[1] + offset_y))
    for segment_start, segment_end in zip(points, points[1:]):
        schematic.wires.add(start=segment_start, end=segment_end)
    add_global_net_label(schematic, net_name, points[-1], 0.85, justify)


def add_connector(
    schematic,
    lib_id: str,
    reference: str,
    value: str,
    position: tuple[float, float],
    pin_map: dict[int, str],
    footprint: str = "",
    manufacturer: str = "",
    mpn: str = "",
    two_row: bool = False,
):
    component = add_symbol(
        schematic,
        lib_id,
        reference,
        value,
        position,
        footprint,
        manufacturer,
        mpn,
    )
    for pin, net_name in pin_map.items():
        label_pin(schematic, component, pin, net_name, two_row=two_row)
    return component


def heading(schematic, text: str, position: tuple[float, float], size: float = 2.0) -> None:
    schematic.texts.add(text, position, size=size, bold=True)


def note(schematic, text: str, position: tuple[float, float], size: float = 1.0) -> None:
    schematic.texts.add(text, position, size=size)


def add_board_child_sheets(
    schematic,
    project_name: str,
    sheets: tuple[tuple[str, str], ...],
    origin: tuple[float, float],
) -> None:
    """Nest detailed circuit pages under the physical board root schematic."""
    origin_x, origin_y = origin
    for index, (sheet_name, filename) in enumerate(sheets, start=1):
        schematic.add_sheet(
            name=sheet_name,
            filename=filename,
            position=(origin_x, origin_y + (index - 1) * 48),
            size=(165, 30),
            stroke_width=0.3,
            project_name=project_name,
            page_number=str(index + 1),
        )


def add_audio8_passive(
    schematic,
    lib_id: str,
    reference: str,
    value: str,
    position: tuple[float, float],
    rotation: int = 0,
):
    """Add a production-identified passive used by the detailed audio sheets."""
    try:
        manufacturer, mpn = AUDIO8_PASSIVE_PARTS[value]
    except KeyError as error:
        raise RuntimeError(f"No controlled AUDIO-8X8 passive for {value!r}") from error
    return add_symbol(
        schematic,
        lib_id,
        reference,
        value,
        position,
        manufacturer=manufacturer,
        mpn=mpn,
        rotation=rotation,
    )


def build_cm5_core_sheet(pinout: dict[str, list[tuple[int, str]]]) -> Path:
    """Capture all three CM5 connectors and the 76 owned allocation contacts."""
    folder = ROOT / "CM5-CARRIER"
    name = "CM5-Core-Allocated"
    create_project(folder, name)
    schematic = create_schematic(name)
    schematic.set_paper_size("A2")
    schematic.set_title_block(
        title="Radxa CM5 ProComm Carrier - Exact CM5 Connector Allocation",
        date="2026-08-13",
        rev="A1",
        company="ProComm",
        comments={
            1: "Three DF40C-100DS mates; pad geometry and relative placement come from Radxa IO V2.20",
            2: "76 contacts are owned: 74 connected and 2 assigned no-connect; all other functions are no-connect",
            3: "U33-A includes the four official grounded CM5 mounting pads; allocated GPIO domain is 3.3 V",
            4: "DETAILED CAPTURE BASELINE - verify CM5 voltage limits before release",
        },
    )

    heading(schematic, "1. EXACT RADXA CM5 MATING CONNECTORS", (45, 18), 1.8)
    allocations = allocation_map()
    if len(CM5_ALLOCATIONS) != 76 or len(allocations) != 76:
        raise RuntimeError(
            "CM5 allocation contract must contain exactly 76 unique physical contacts"
        )
    if not CM5_ASSIGNED_NC.issubset(allocations) or len(CM5_ASSIGNED_NC) != 2:
        raise RuntimeError("CM5 assigned-no-connect contract must contain two allocated contacts")
    physical_contacts = {
        (connector, pin)
        for connector, rows in pinout.items()
        for pin, _signal in rows
    }
    missing_contacts = sorted(set(allocations) - physical_contacts)
    if missing_contacts:
        raise RuntimeError(
            f"CM5 allocations reference contacts absent from the V2.21 workbook: {missing_contacts}"
        )
    if len(physical_contacts) != 300:
        raise RuntimeError(
            f"CM5 source must contain 300 unique physical contacts, found {len(physical_contacts)}"
        )
    placements = (
        ("U13-A", "J501", 105.0),
        ("U13-B", "J502", 295.0),
        ("J1", "J503", 485.0),
    )
    for connector, reference, x in placements:
        symbol_name = f"Radxa_CM5_{connector.replace('-', '_')}"
        component = add_symbol(
            schematic,
            f"CM5Carrier:{symbol_name}",
            reference,
            f"RADXA CM5 {connector} MATE",
            (x, 105),
            CM5_DF40_FOOTPRINTS[connector],
            "Hirose",
            "DF40C-100DS-0.4V(51)",
        )
        for pin, signal in pinout[connector]:
            position = pin_xy(component, pin)
            if (connector, pin) in CM5_ASSIGNED_NC:
                schematic.no_connects.add(position)
            elif (connector, pin) in allocations:
                net_name = allocations[(connector, pin)][1]
                justify = "right" if position[0] < x else "left"
                add_global_net_label(schematic, net_name, position, 0.68, justify)
            elif signal == "GND":
                justify = "right" if position[0] < x else "left"
                add_global_net_label(schematic, "GND", position, 0.62, justify)
            else:
                schematic.no_connects.add(position)
        if connector == "U13-A":
            for mounting_pad in range(201, 205):
                position = pin_xy(component, mounting_pad)
                justify = "right" if position[0] < x else "left"
                add_global_net_label(schematic, "GND", position, 0.62, justify)
        contact_note = (
            "100 contacts + official grounded module pads 201-204"
            if connector == "U13-A"
            else "100 physical contacts"
        )
        note(schematic, f"{connector}: {contact_note}", (x - 28, 178), 0.82)

    heading(schematic, "2. INTERNAL POWER / STARTUP / RECOVERY SERVICE", (45, 202), 1.6)
    add_connector(
        schematic,
        "Connector_Generic:Conn_01x06",
        "J510",
        "CM5_POWER_SERVICE",
        (90, 235),
        {
            1: "LOGIC_3V3",
            2: "GND",
            3: "CM5_RESET_N",
            4: "CM5_BOOT",
            5: "CM5_PWRON_N",
            6: "CM5_RECOVERY_KEY",
        },
        JST_GH_6,
        "JST",
        "BM06B-GHS-TBT(LF)(SN)",
    )
    note(schematic, "Internal keyed service header; never exposed on the top panel.", (55, 263), 0.85)

    add_connector(
        schematic,
        "Connector_Generic:Conn_01x04",
        "J511",
        "DEBUG_UART_3V3",
        (215, 232),
        {1: "LOGIC_3V3", 2: "GND", 3: "DBG_UART_TX", 4: "DBG_UART_RX"},
        JST_GH_4,
        "JST",
        "BM04B-GHS-TBT(LF)(SN)",
    )
    note(schematic, "3.3 V UART only; keyed factory/debug cable.", (190, 255), 0.85)

    add_connector(
        schematic,
        "Connector_Generic:Conn_01x05",
        "J512",
        "INTERNAL_USB_RECOVERY",
        (330, 233),
        {
            1: "REC_USB_VBUS_DET",
            2: "REC_USB_DM",
            3: "REC_USB_DP",
            4: "REC_USB_ID",
            5: "GND",
        },
        JST_GH_5,
        "JST",
        "BM05B-GHS-TBT(LF)(SN)",
    )
    note(schematic, "Internal keyed recovery harness; service fixture owns the protected USB-C receptacle and CC network.", (285, 260), 0.85)

    add_connector(
        schematic,
        "Connector_Generic:Conn_02x04_Odd_Even",
        "J513",
        "CM5_POWER_ENTRY",
        (470, 232),
        {
            1: "SYS_4V0",
            2: "SYS_4V0",
            3: "SYS_4V0",
            4: "SYS_4V0",
            5: "GND",
            6: "GND",
            7: "GND",
            8: "GND",
        },
        MF_2X4,
        "Molex",
        "43045-0812",
        two_row=True,
    )
    note(schematic, "Kelvin-sense SYS_4V0 at J501; 4.0 V follows the Radxa CM5 carrier design note.", (420, 260), 0.85)
    note(schematic, "PCB lock: J501 and J502 share the U33 origin; J503 is +11.405, -25.415 mm at -90 degrees.", (420, 270), 0.82)

    heading(schematic, "3. OWNERSHIP AUDIT", (45, 295), 1.6)
    audit_lines = (
        "76 / 76 contacts owned; 74 connected, 2 assigned NC, 0 duplicate physical-pin claims.",
        "WAN1 uses native MDI. PCIe Gen2 x1 feeds the packet switch.",
        "WWAN owns USB30_2 + USB20_HOST0; touch owns USB20_HOST1.",
        "HDMI_TX0, I2S0 TDM, I2S1 headset, I2C7, I2C3 and UART2 are reserved exactly once.",
        "Pin 145 reaches HDMI pin 14; pin 147 is assigned NC because HEAC/ARC is unused. U13-B pin 106 receives IO_5V0.",
        "Unused alternate-function contacts carry explicit no-connect markers on this A1 baseline.",
    )
    for index, text in enumerate(audit_lines):
        note(schematic, text, (45, 312 + index * 9), 0.9)

    output = folder / f"{name}.kicad_sch"
    save_generated_schematic(schematic, output)
    return output
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
